gitberthe/BertheVario/BertheVario213/Documentation/00-photo/T5-V2_17.jpg

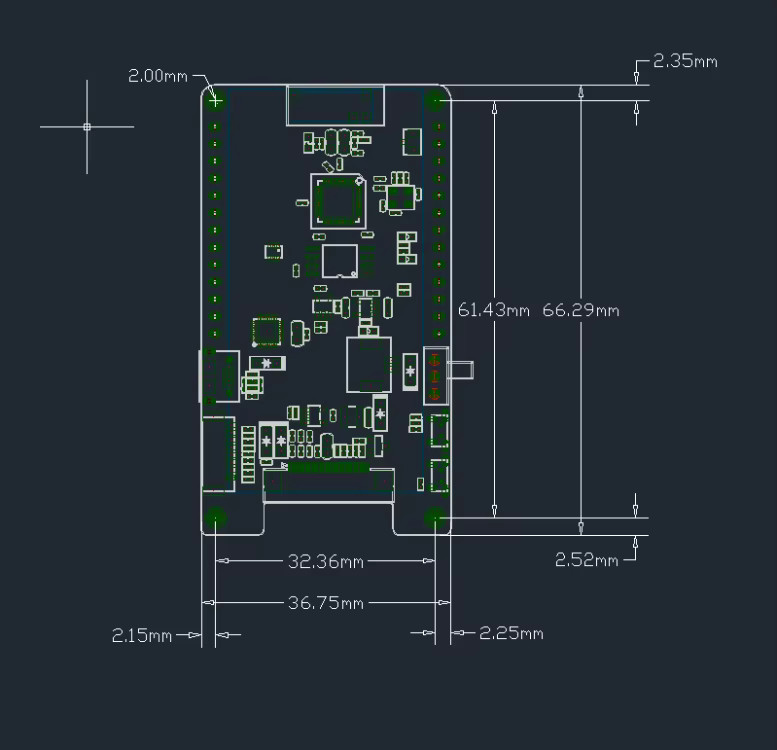
BertheVario213/Documentation/00-photo/T5-V2_17.jpg
