gitberthe/BertheVario/BertheVario213/Photos/03-cablage.jpg

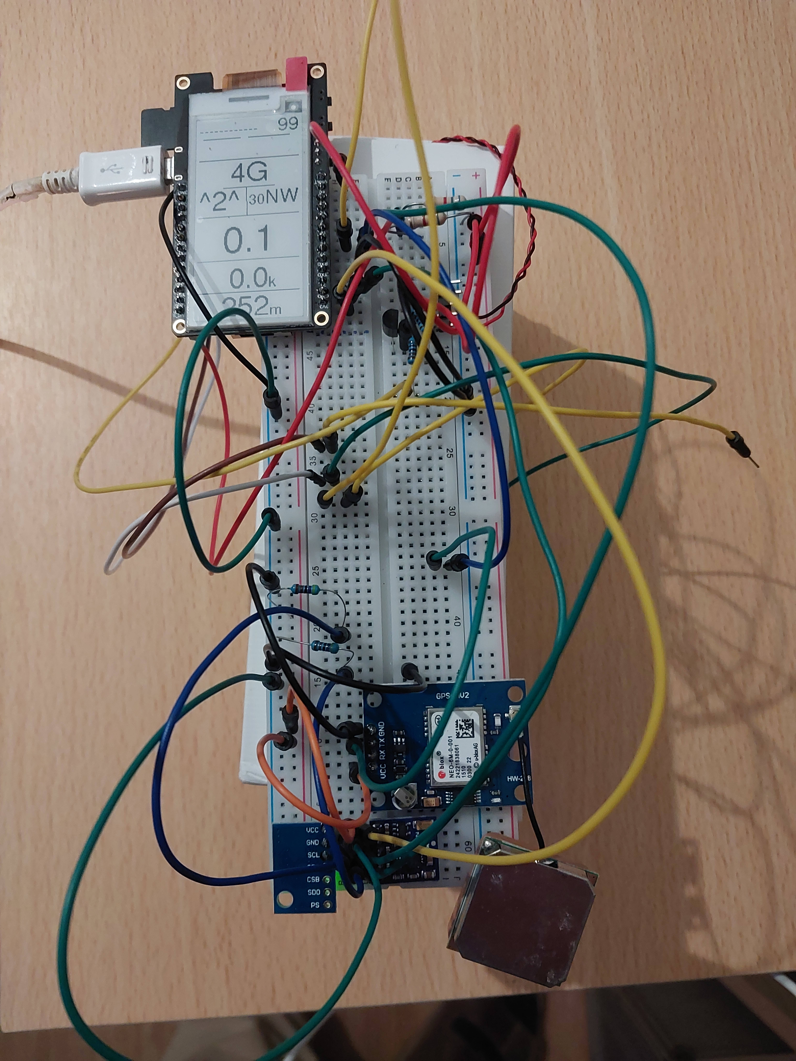
BertheVario213/Photos/03-cablage.jpg
