gitberthe/BertheVario/BertheVario213/Photos/07-bv213-sans-boitier-1.jpg

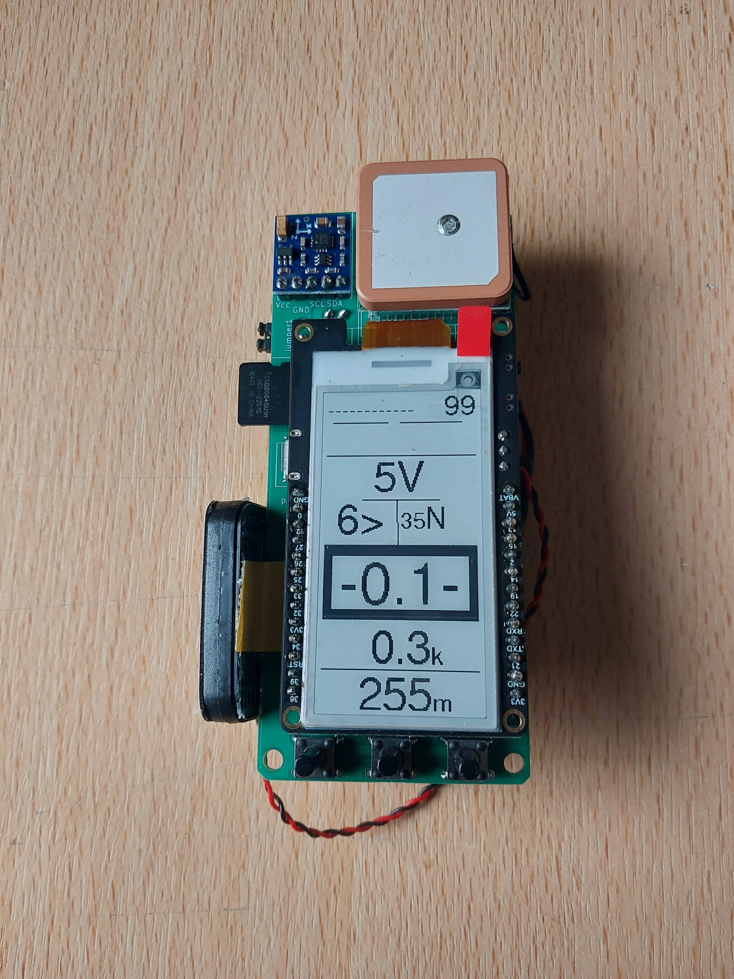
BertheVario213/Photos/07-bv213-sans-boitier-1.jpg
