gitberthe/BertheVario/BertheVario213/Photos/08-bv213-sans-boitier-2.jpg

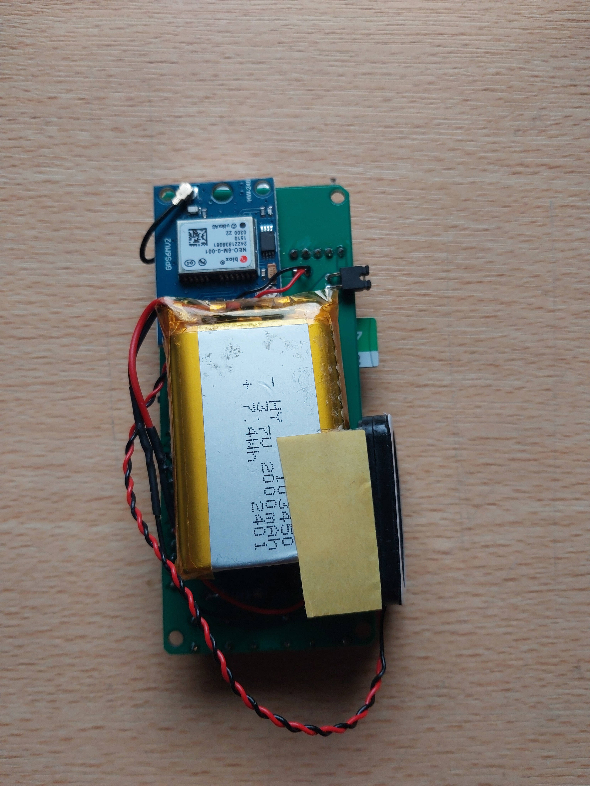
BertheVario213/Photos/08-bv213-sans-boitier-2.jpg
