gitberthe/BertheVario/CompZoneAerienne/zones_gnuplot/000_png_PROTECT_Reserve_naturelle_nationale_de_Chastreix-Sancy_300m_sol_.png

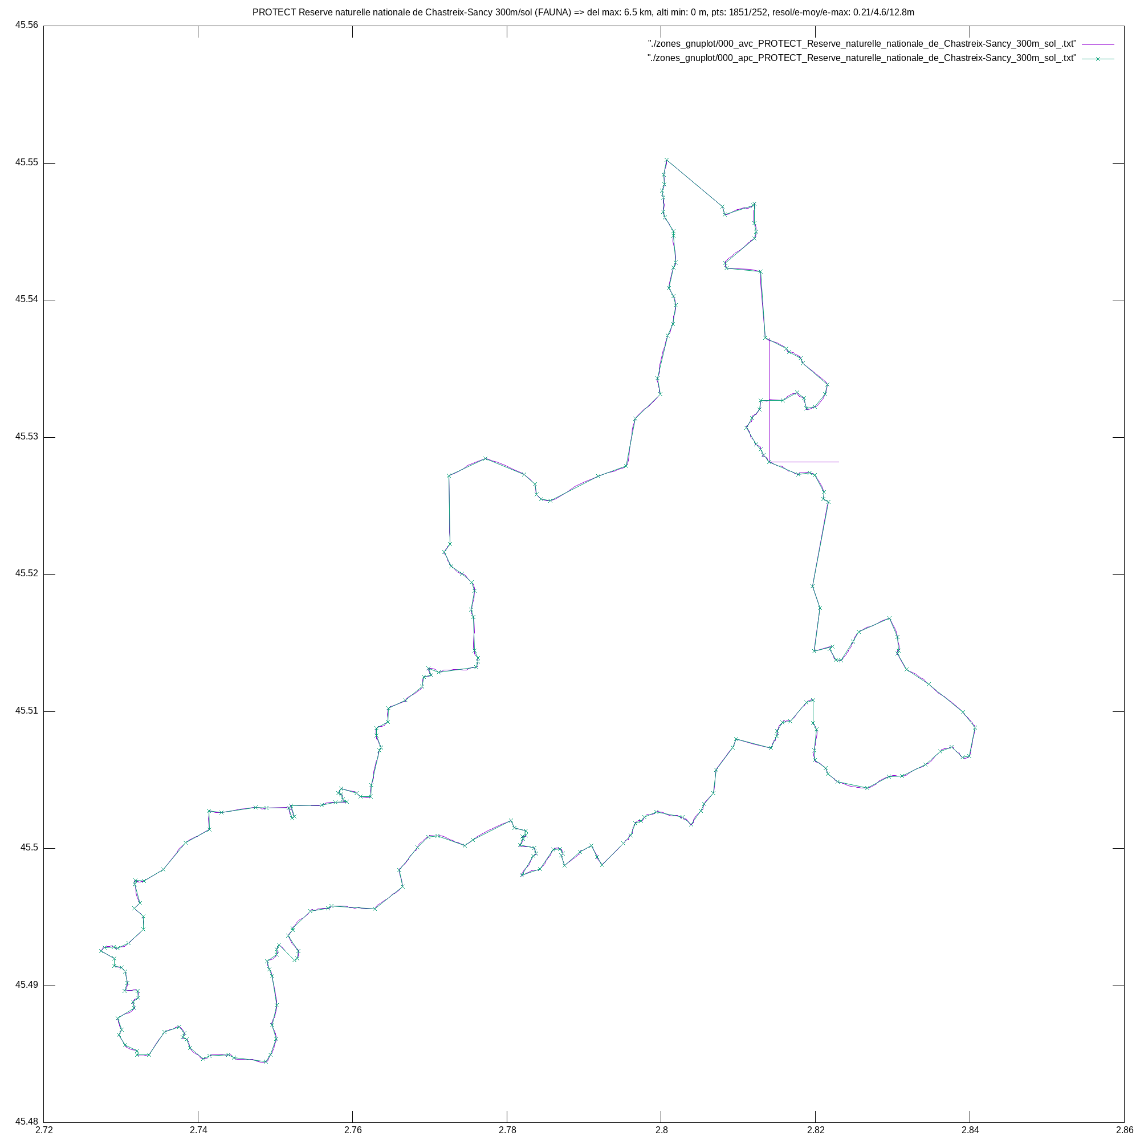
CompZoneAerienne/zones_gnuplot/000_png_PROTECT_Reserve_naturelle_nationale_de_Chastreix-Sancy_300m_sol_.png
