gitberthe/BertheVario/CompZoneAerienne/zones_gnuplot/001_png_PROTECT_Reserve_naturelle_nationale_de_la_Vallee_de_Chaudefour.png

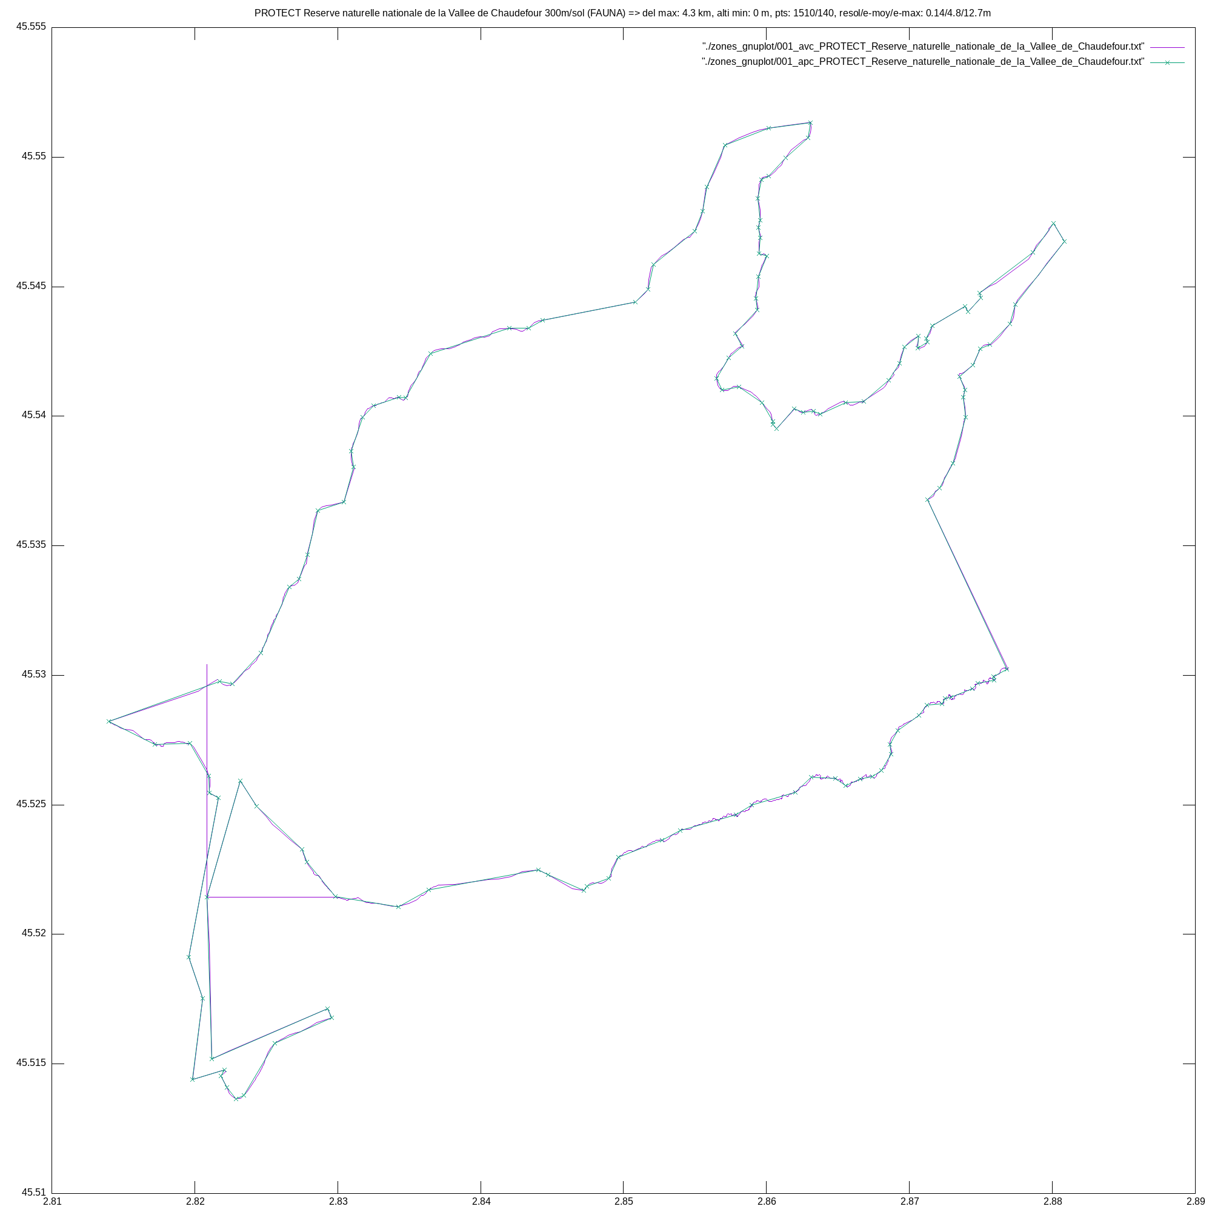
CompZoneAerienne/zones_gnuplot/001_png_PROTECT_Reserve_naturelle_nationale_de_la_Vallee_de_Chaudefour.png
