gitberthe/BertheVario/CompZoneAerienne/zones_gnuplot/002_png_CTR_CLERMONT_Twr_118.625__Upper_2700FT_AMSL-1000FT_AGL.png

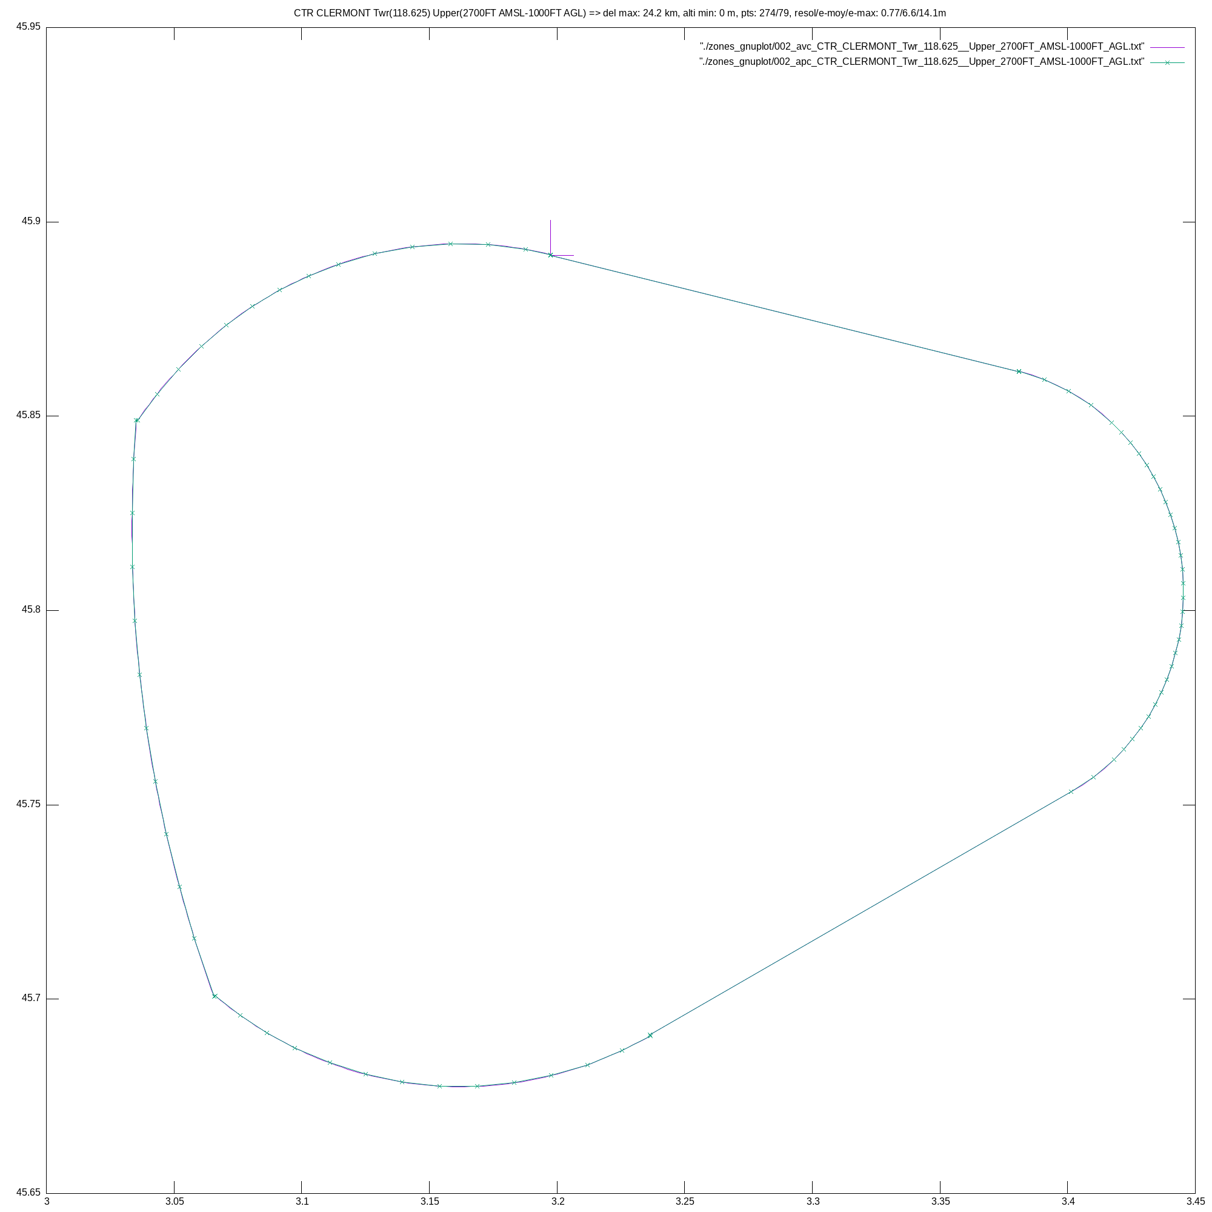
CompZoneAerienne/zones_gnuplot/002_png_CTR_CLERMONT_Twr_118.625__Upper_2700FT_AMSL-1000FT_AGL.png
