gitberthe/BertheVario/CompZoneAerienne/zones_gnuplot/003_png_PROTECT_Rocher_de_la_Jacquette__300m_sol_.png

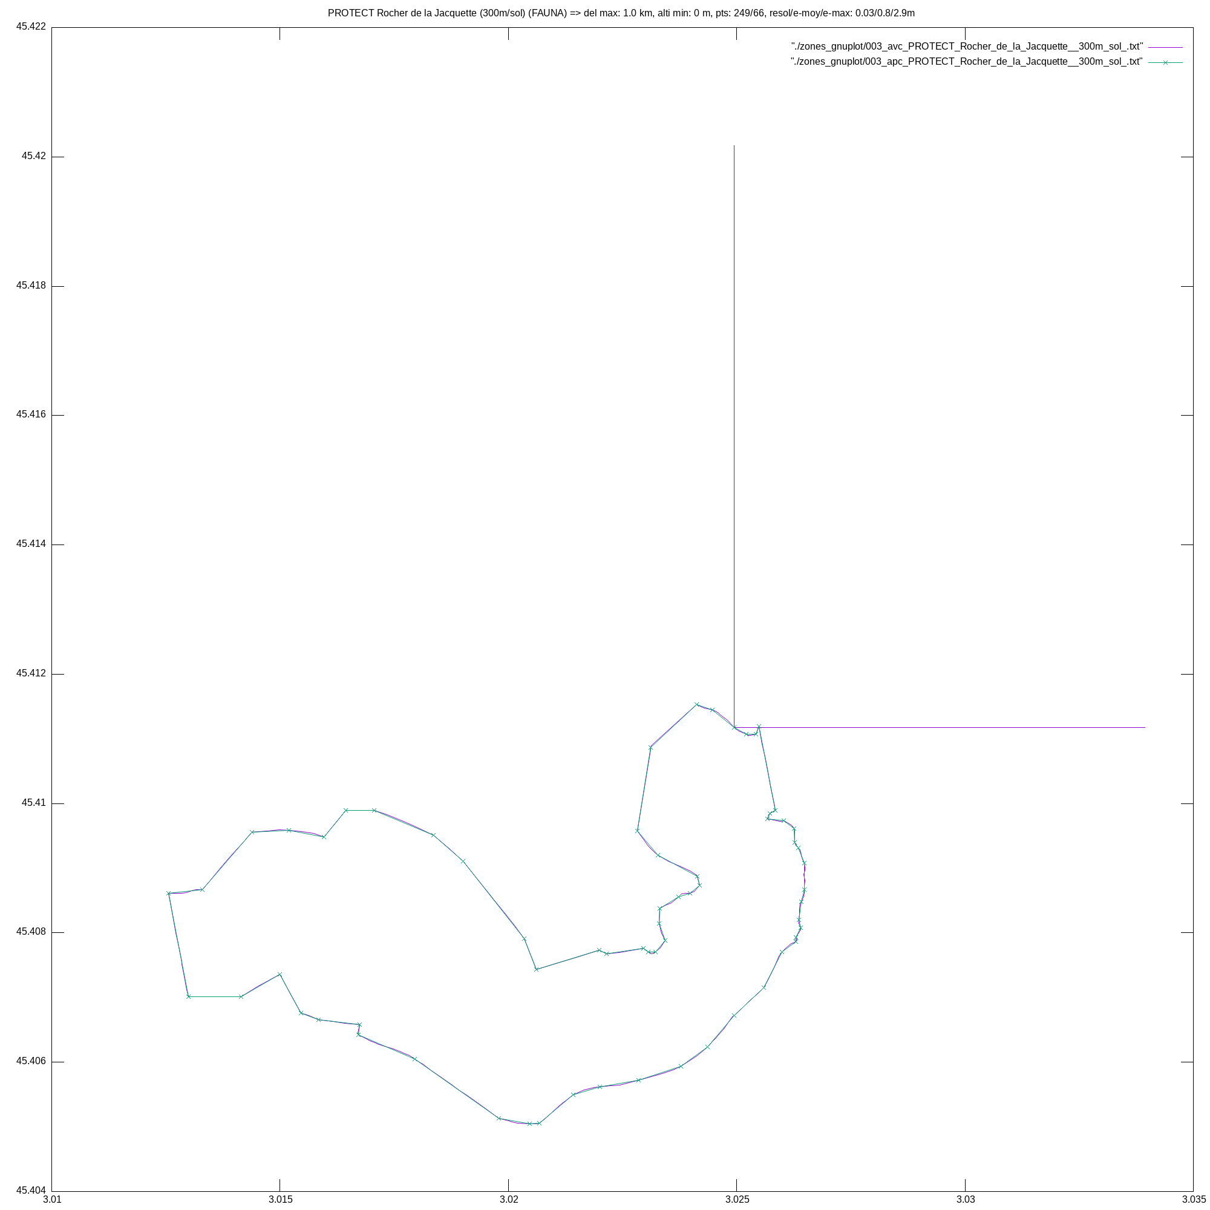
CompZoneAerienne/zones_gnuplot/003_png_PROTECT_Rocher_de_la_Jacquette__300m_sol_.png
