gitberthe/BertheVario/CompZoneAerienne/zones_gnuplot/004_png_TMA_CLERMONT_9_App_122.225__Lower_1000FT_AGL-4000FT.png

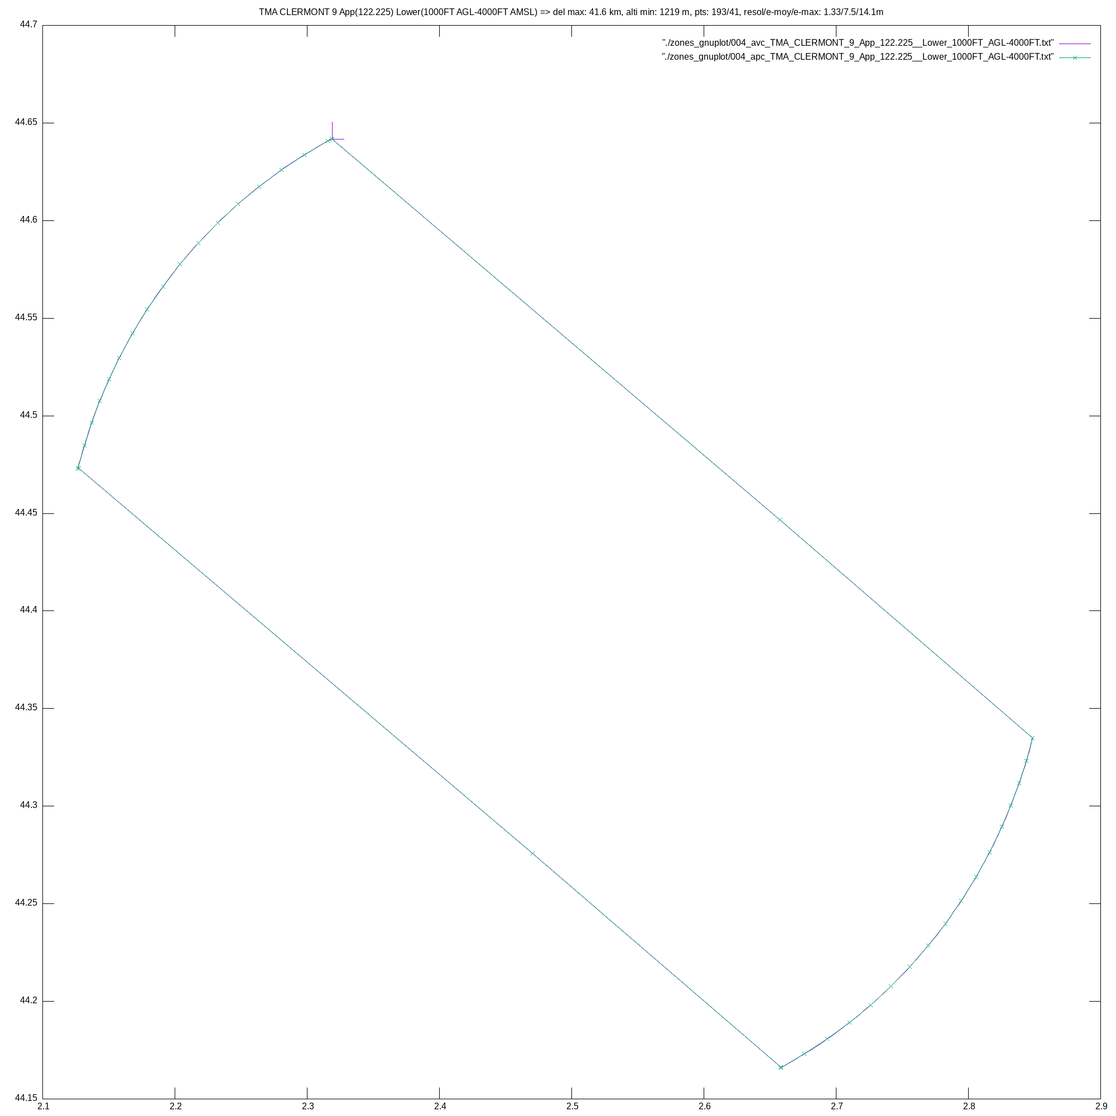
CompZoneAerienne/zones_gnuplot/004_png_TMA_CLERMONT_9_App_122.225__Lower_1000FT_AGL-4000FT.png
