gitberthe/BertheVario/CompZoneAerienne/zones_gnuplot/005_png_CTR_RODEZ_Twr_118.125___FFVL-Prot__.png

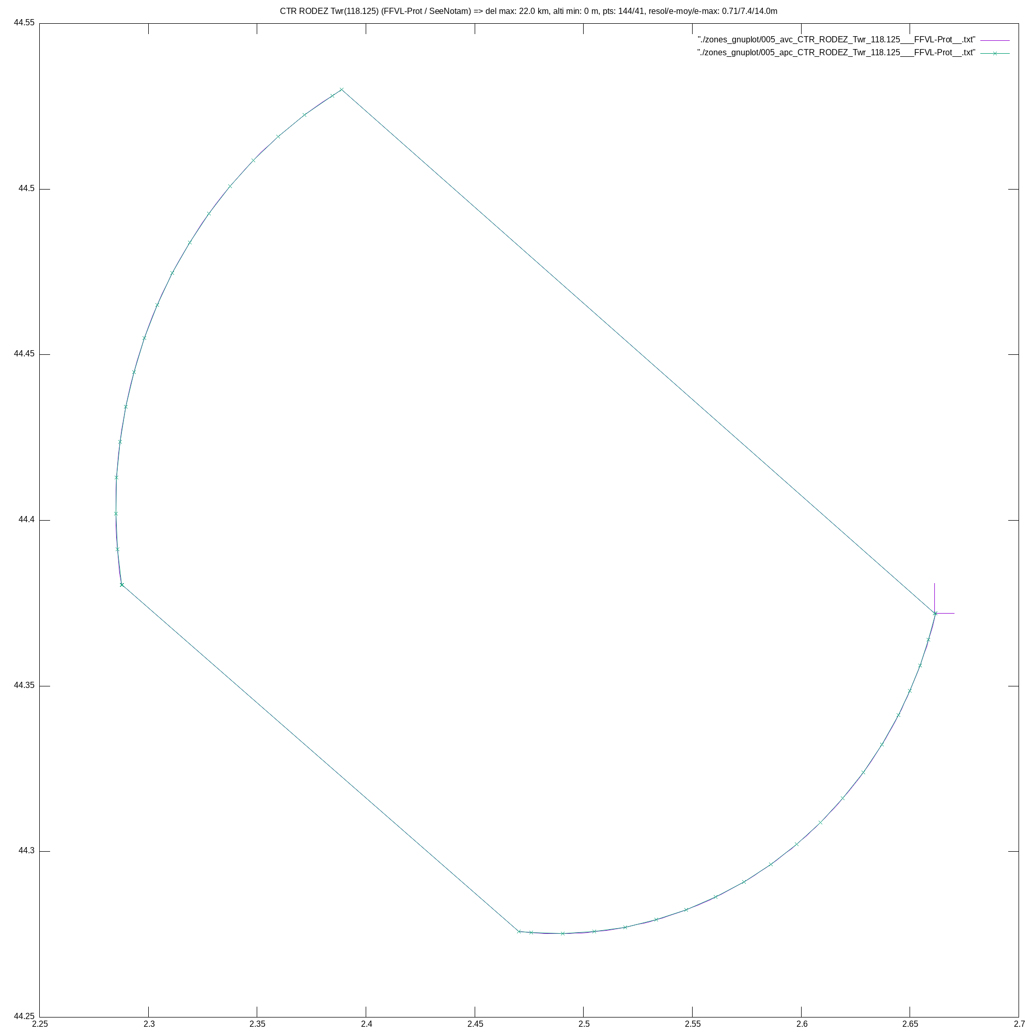
CompZoneAerienne/zones_gnuplot/005_png_CTR_RODEZ_Twr_118.125___FFVL-Prot__.png
