gitberthe/BertheVario/CompZoneAerienne/zones_gnuplot/006_png_TMA_CLERMONT_1_App_122.225__Lower_1000FT_AGL-2700FT.png

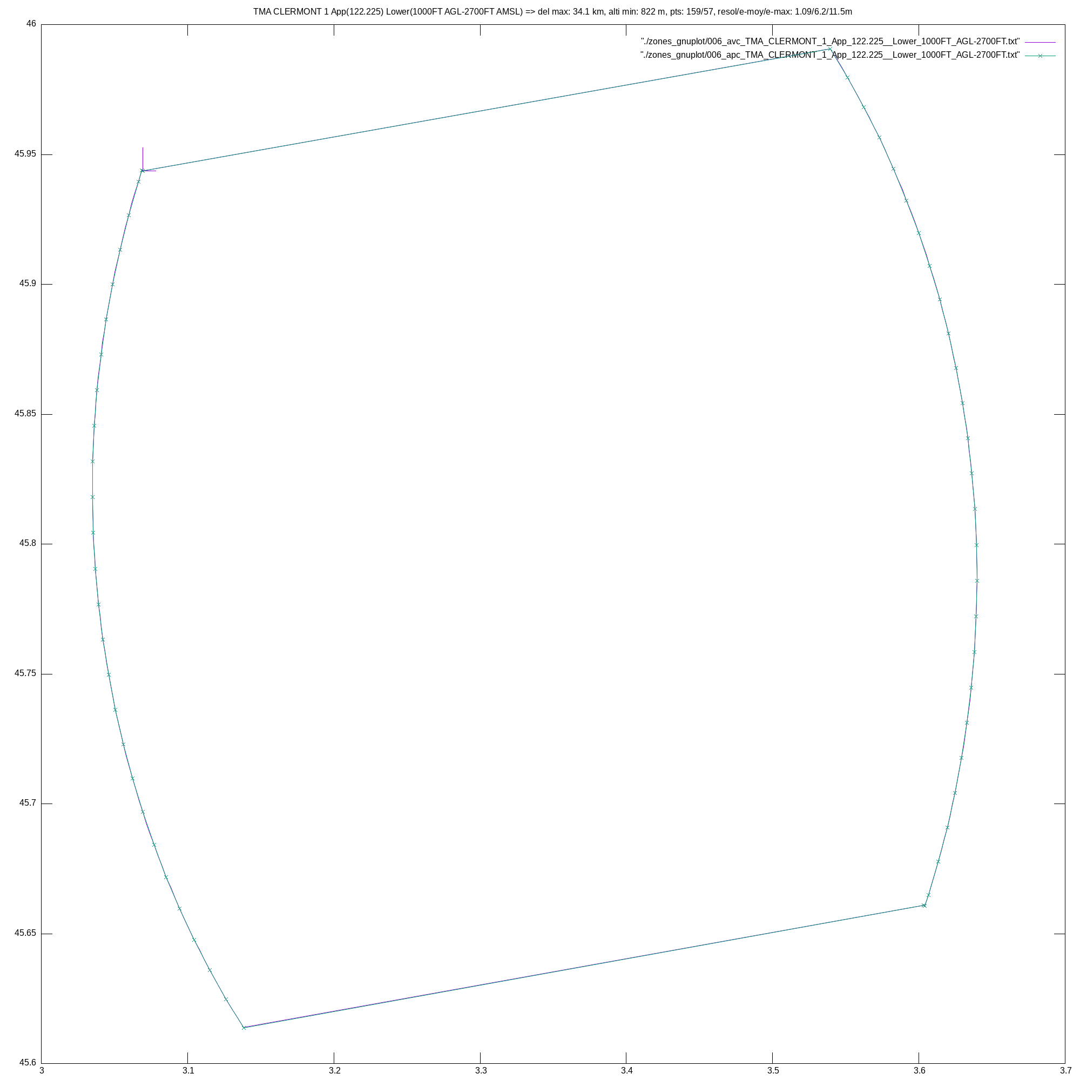
CompZoneAerienne/zones_gnuplot/006_png_TMA_CLERMONT_1_App_122.225__Lower_1000FT_AGL-2700FT.png
