gitberthe/BertheVario/CompZoneAerienne/zones_gnuplot/007_png_CTR_SAINT_ETIENNE_2_Twr_119.250_.png

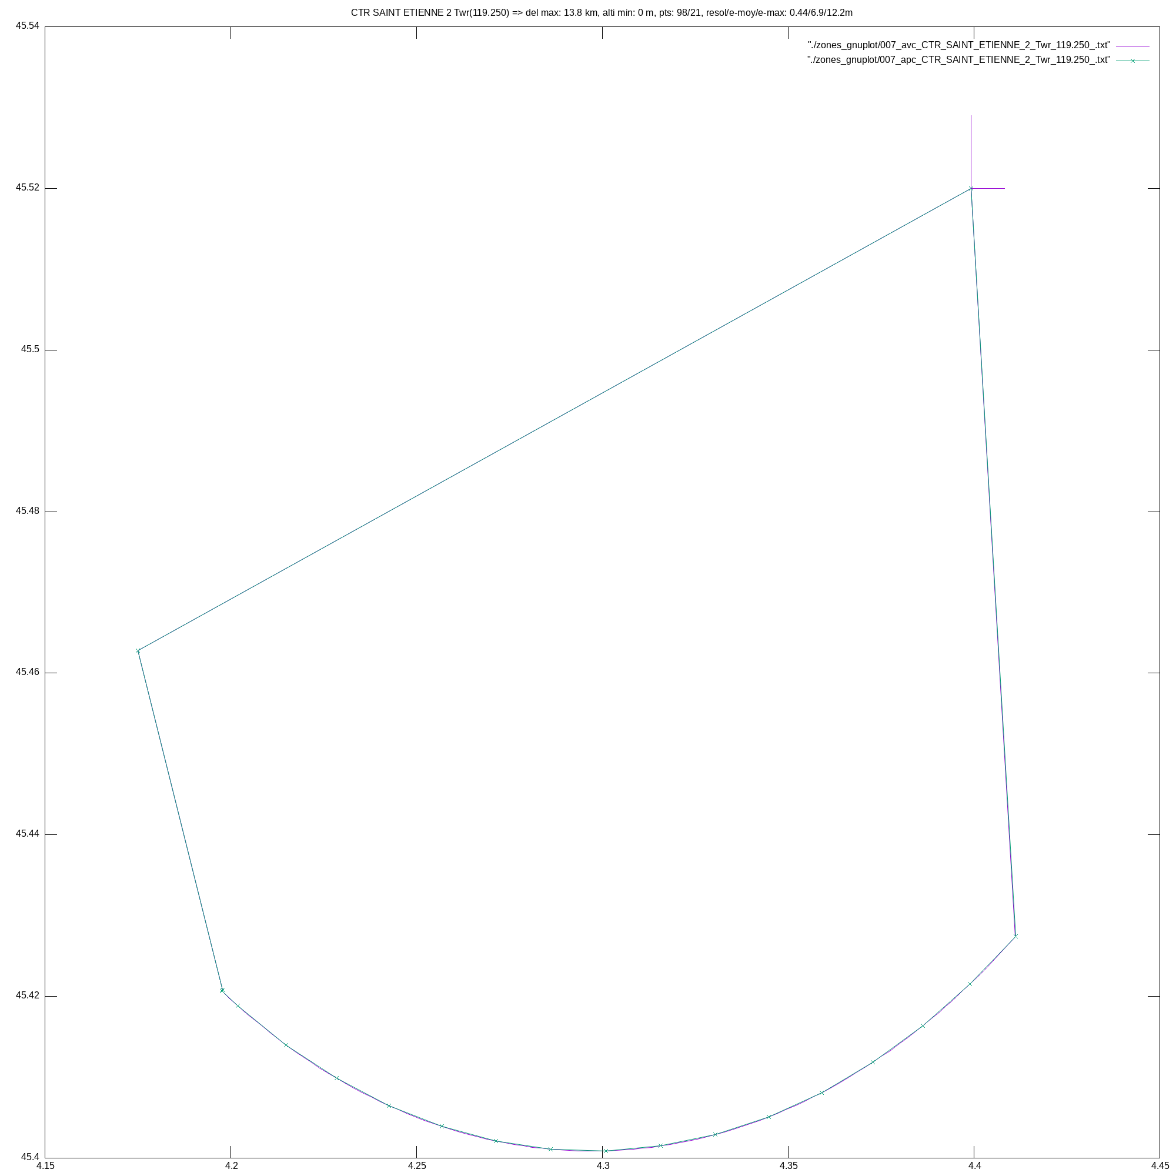
CompZoneAerienne/zones_gnuplot/007_png_CTR_SAINT_ETIENNE_2_Twr_119.250_.png
