gitberthe/BertheVario/CompZoneAerienne/zones_gnuplot/008_png_CTA_LIMOGES_Twr_127.675_.png

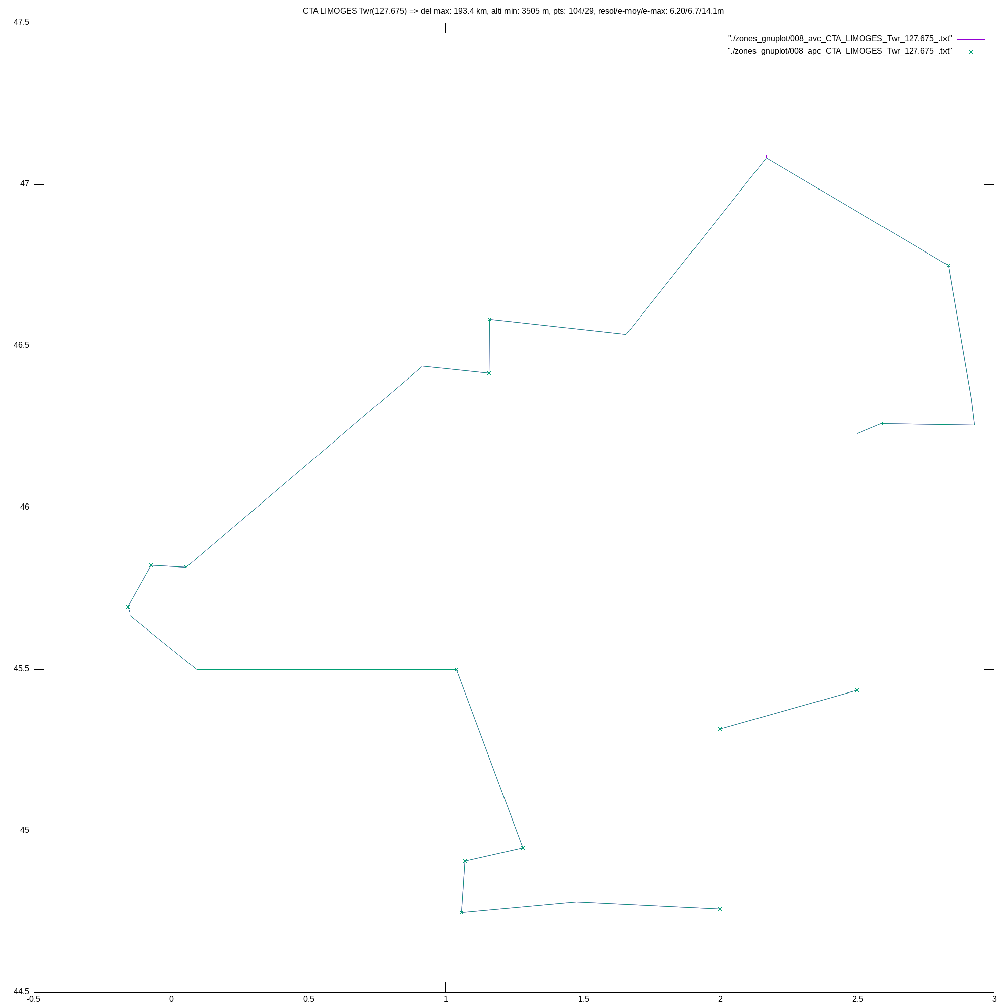
CompZoneAerienne/zones_gnuplot/008_png_CTA_LIMOGES_Twr_127.675_.png
