gitberthe/BertheVario/CompZoneAerienne/zones_gnuplot/009_png_TMA_CLERMONT_2.3_App_122.225_.png

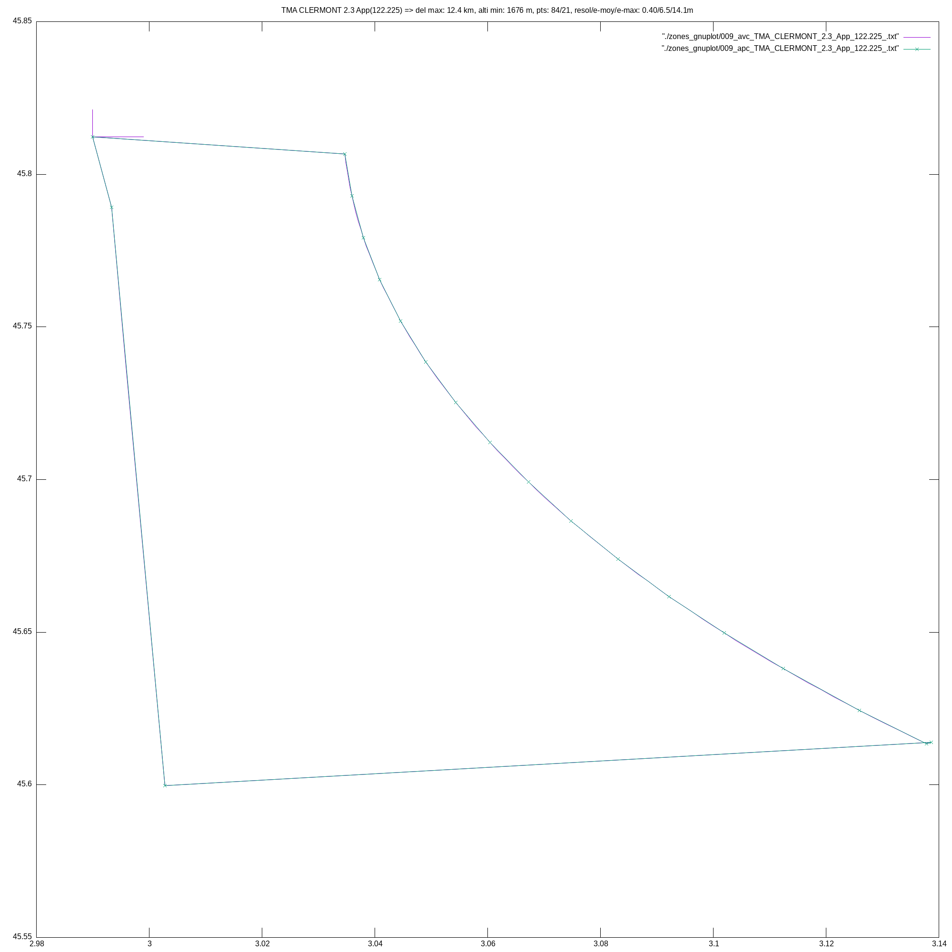
CompZoneAerienne/zones_gnuplot/009_png_TMA_CLERMONT_2.3_App_122.225_.png
