gitberthe/BertheVario/CompZoneAerienne/zones_gnuplot/011_png_RTBA_139_B__MILOPS___SeeNotam_.png

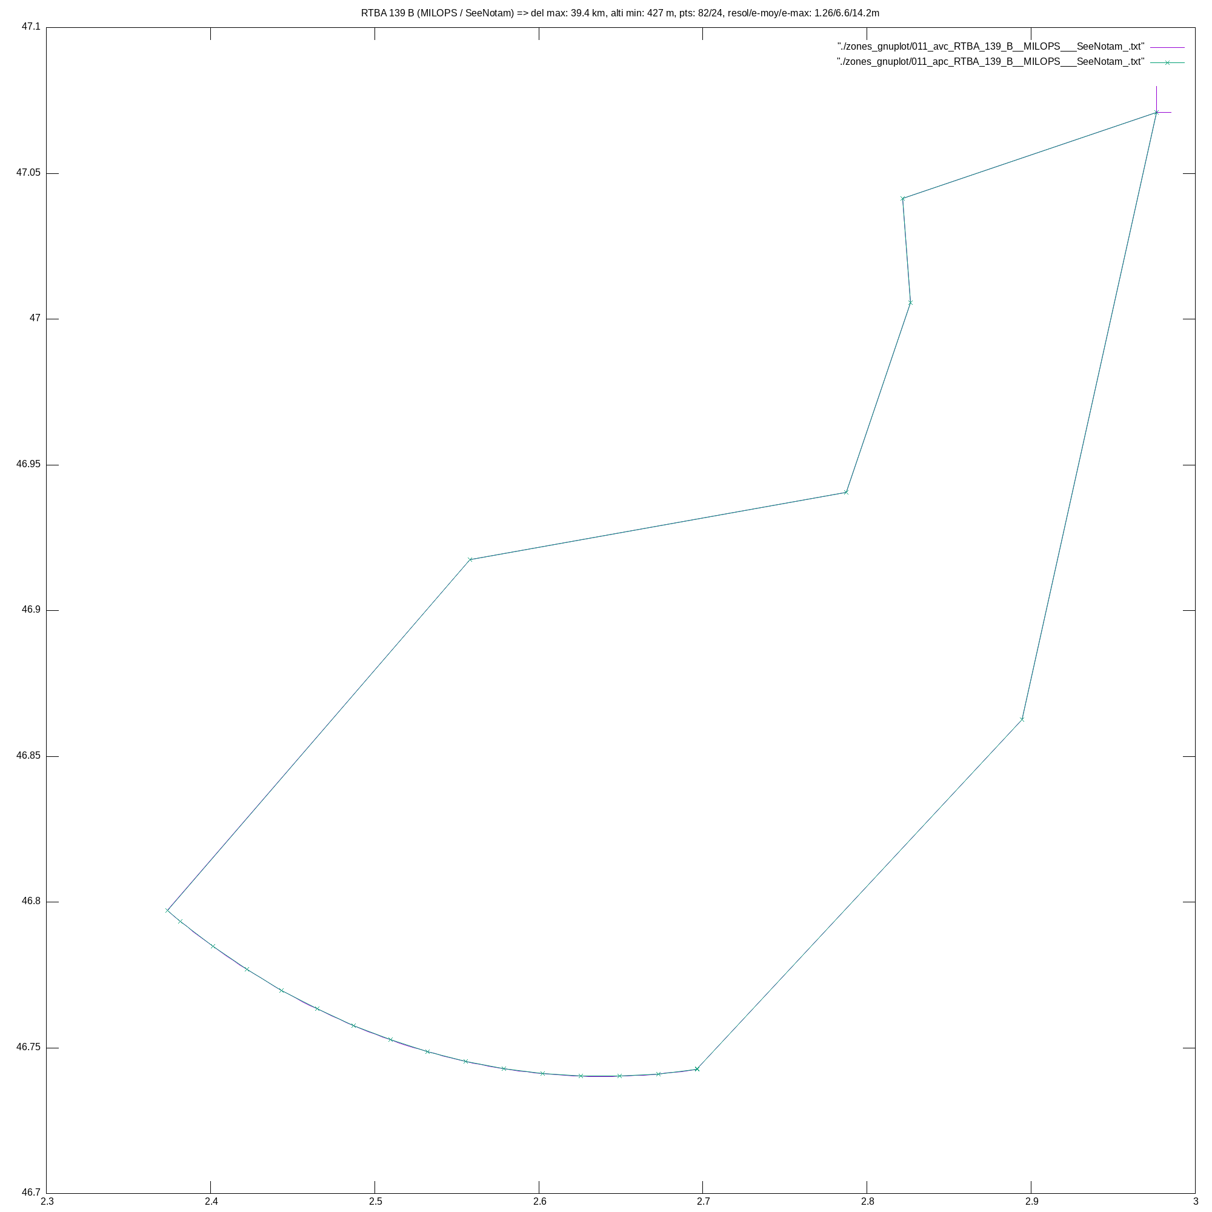
CompZoneAerienne/zones_gnuplot/011_png_RTBA_139_B__MILOPS___SeeNotam_.png
