gitberthe/BertheVario/CompZoneAerienne/zones_gnuplot/012_png_RTBA_139_A__MILOPS___SeeNotam_.png

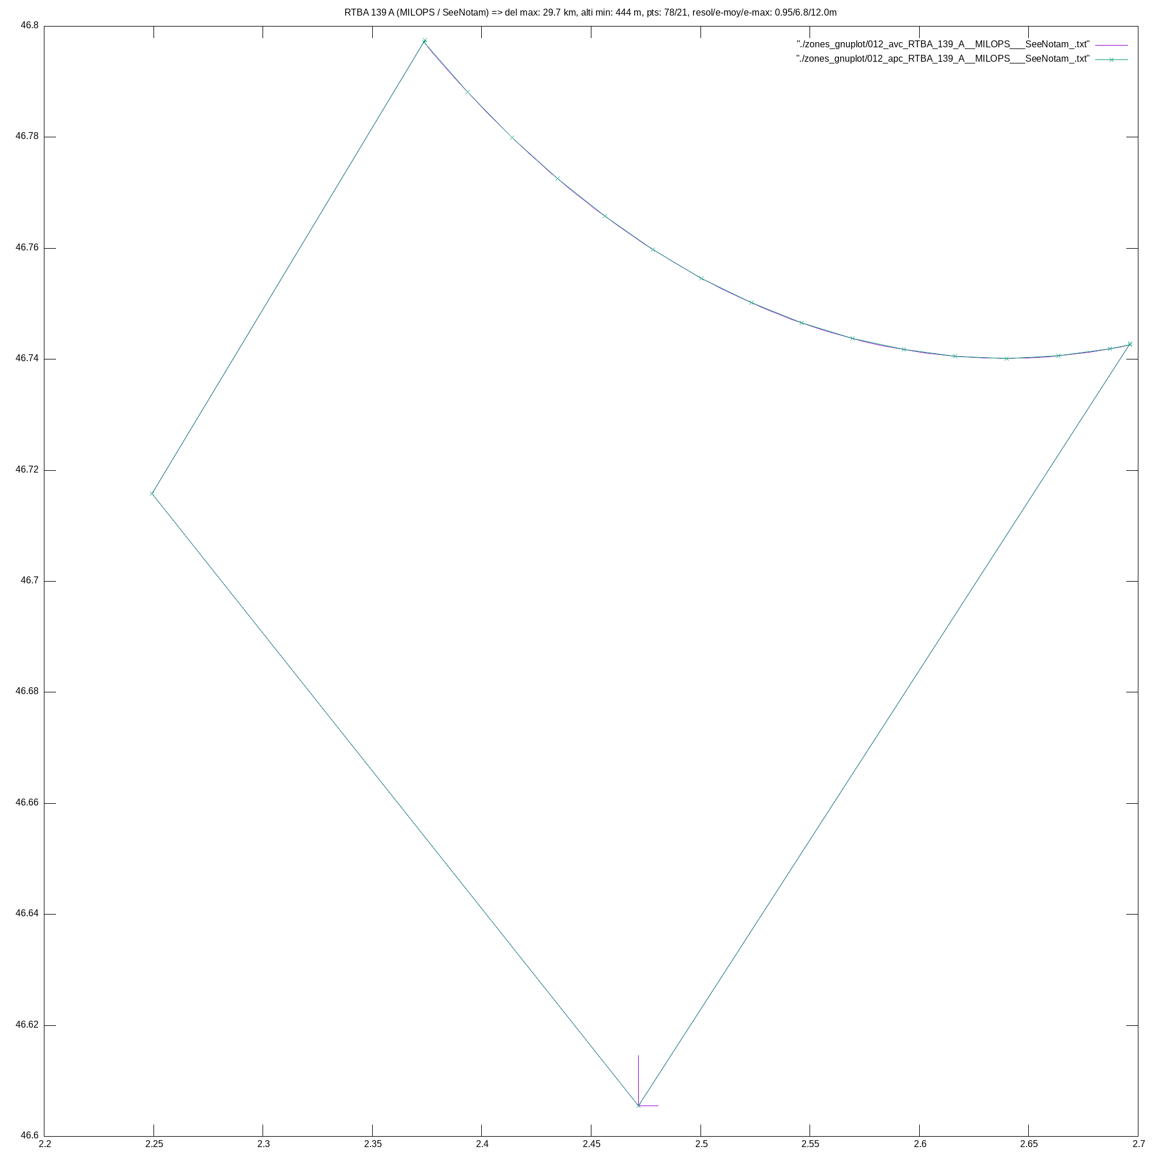
CompZoneAerienne/zones_gnuplot/012_png_RTBA_139_A__MILOPS___SeeNotam_.png
