gitberthe/BertheVario/CompZoneAerienne/zones_gnuplot/013_png_R_20_B3_E_App_119.7_.png

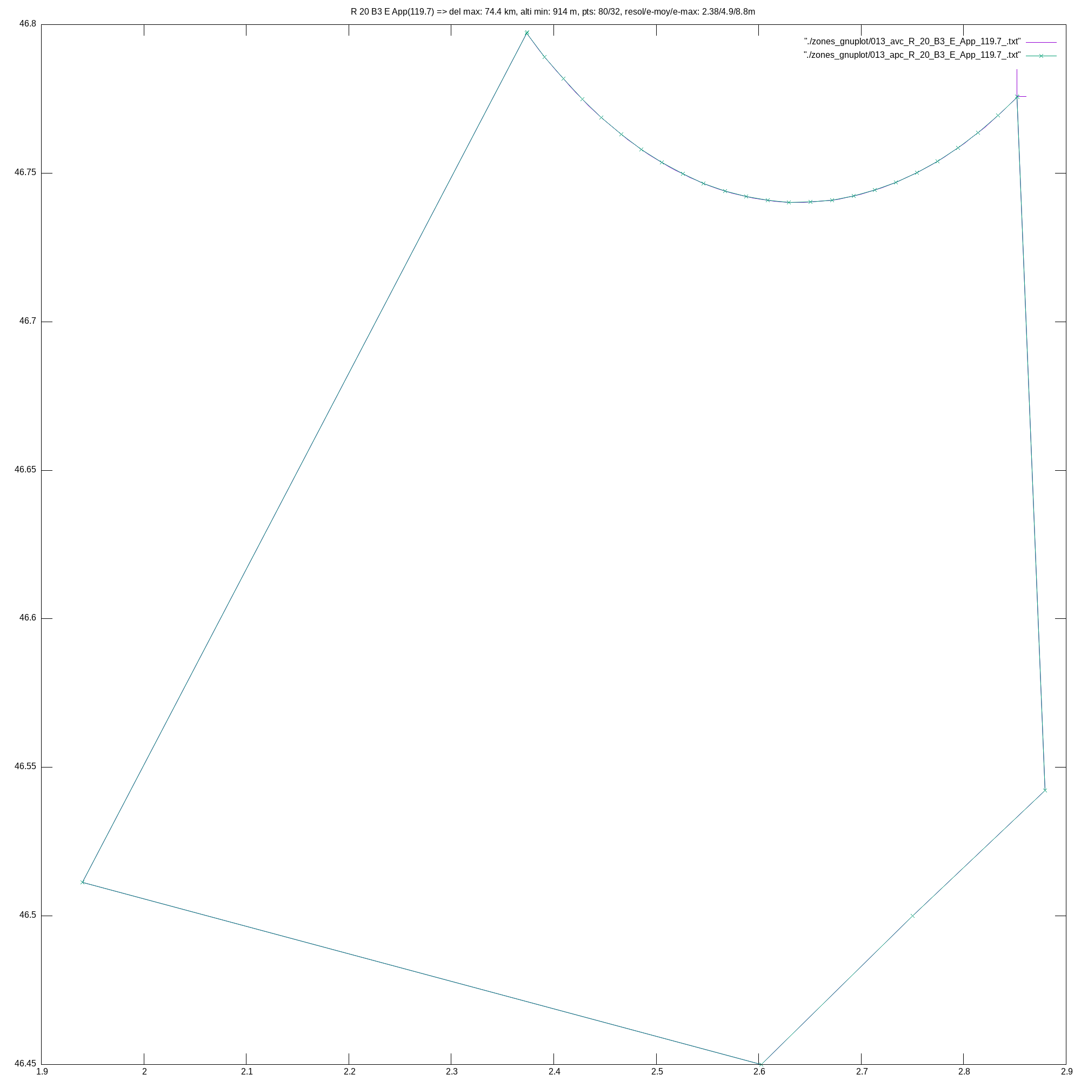
CompZoneAerienne/zones_gnuplot/013_png_R_20_B3_E_App_119.7_.png
