gitberthe/BertheVario/CompZoneAerienne/zones_gnuplot/014_png_PROTECT_Parc_Cevennes_Coeur__1000m_sol__.png

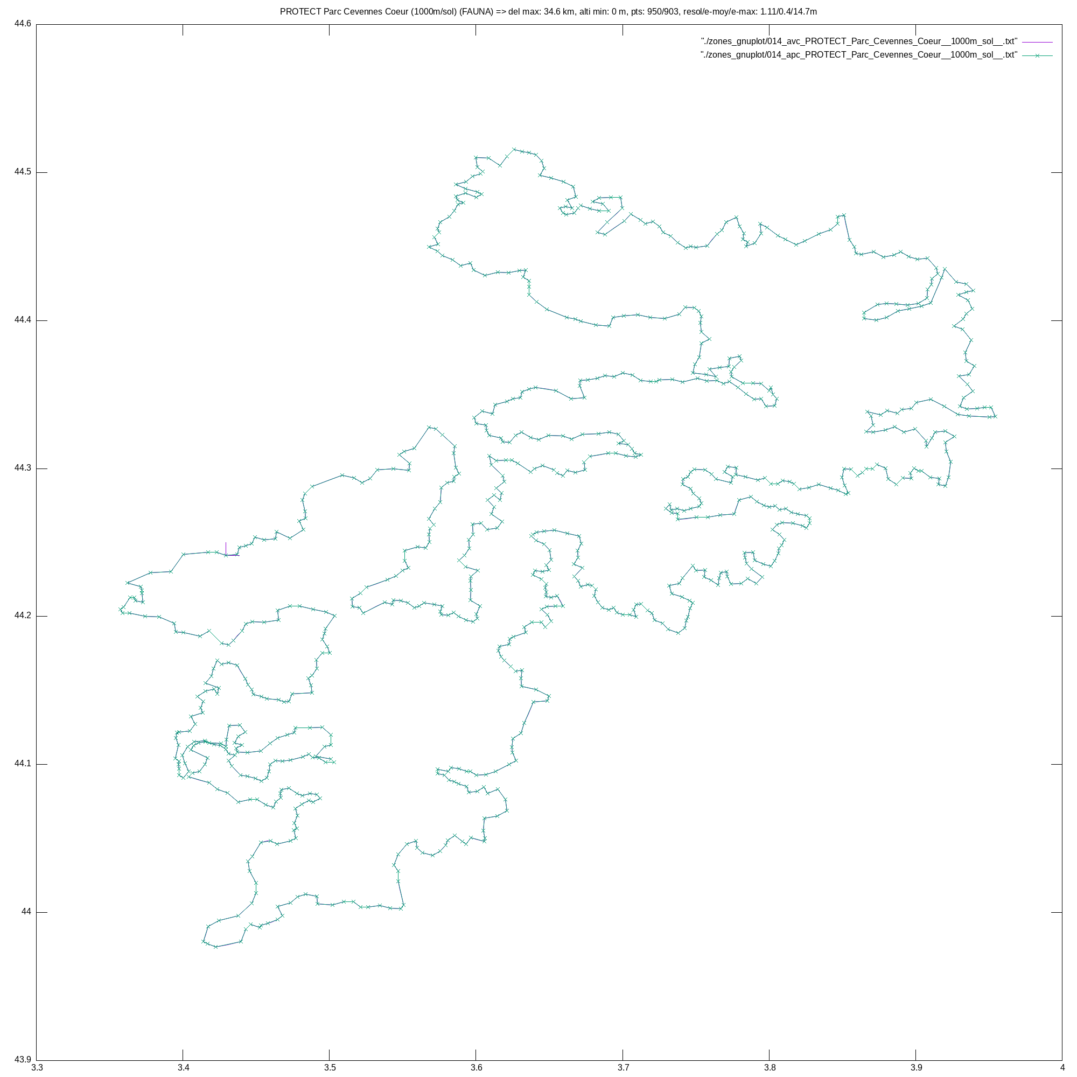
CompZoneAerienne/zones_gnuplot/014_png_PROTECT_Parc_Cevennes_Coeur__1000m_sol__.png
