gitberthe/BertheVario/CompZoneAerienne/zones_gnuplot/015_png_TMA_SAINT-YAN_1.2_App_123.405_.png

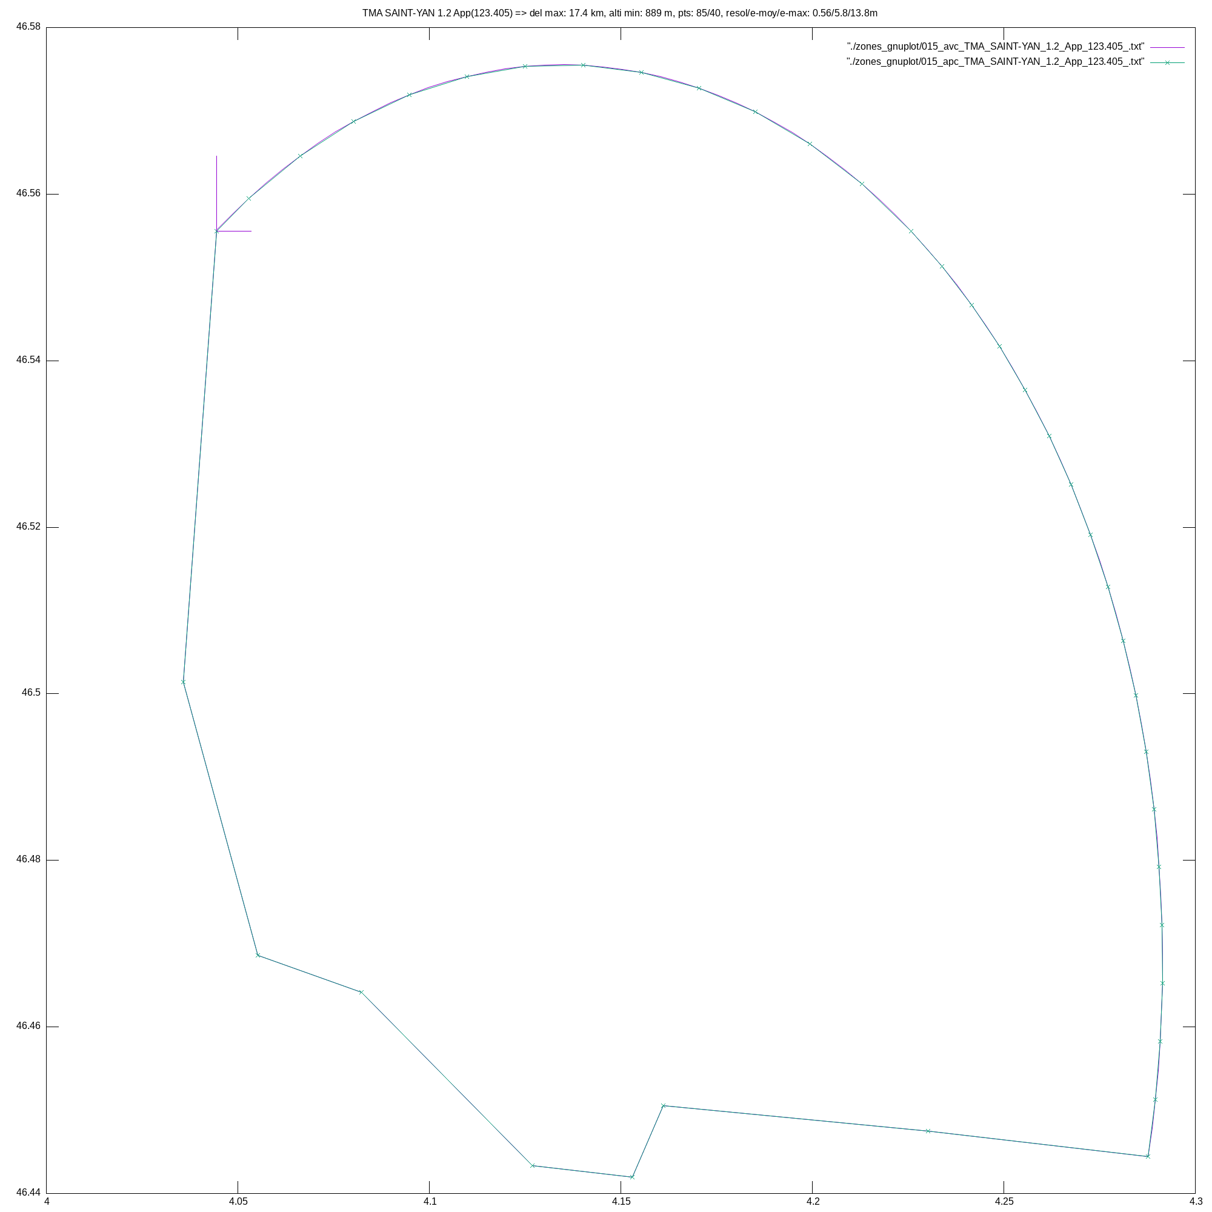
CompZoneAerienne/zones_gnuplot/015_png_TMA_SAINT-YAN_1.2_App_123.405_.png
