gitberthe/BertheVario/CompZoneAerienne/zones_gnuplot/016_png_CTR_SAINT_ETIENNE_1_Twr_119.250__Upper_3200FT.png

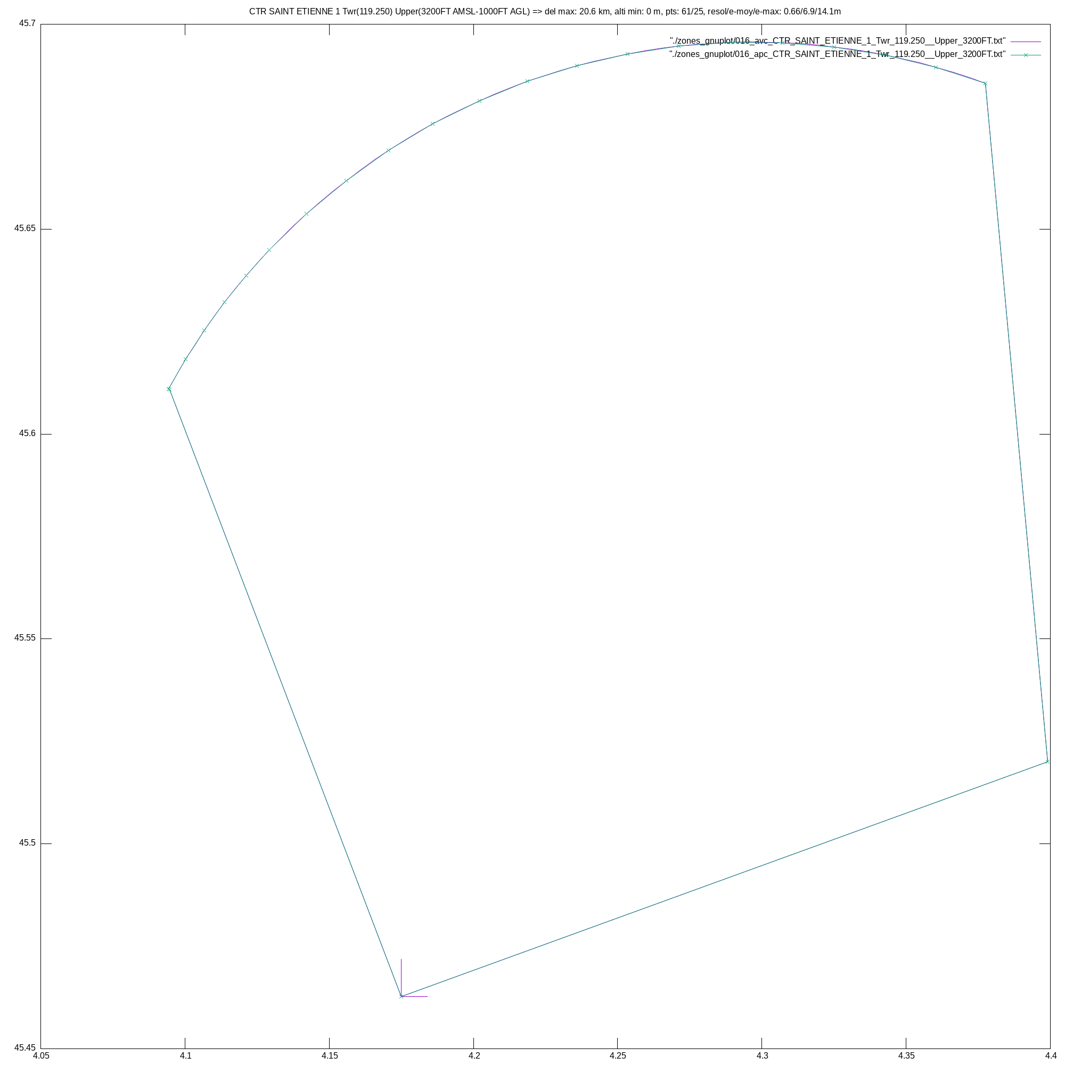
CompZoneAerienne/zones_gnuplot/016_png_CTR_SAINT_ETIENNE_1_Twr_119.250__Upper_3200FT.png
