gitberthe/BertheVario/CompZoneAerienne/zones_gnuplot/017_png_R_20_B3_W_App_119.7_.png

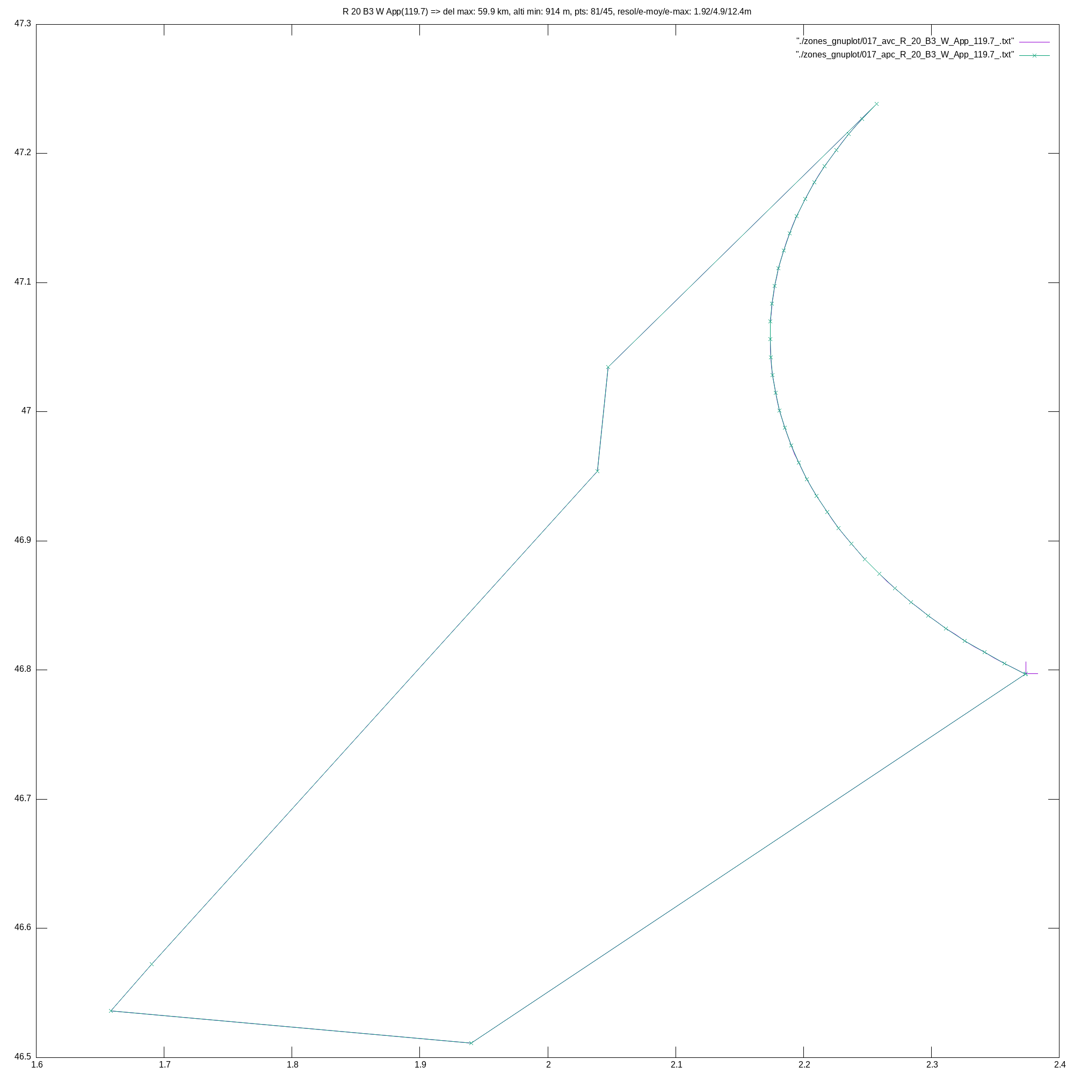
CompZoneAerienne/zones_gnuplot/017_png_R_20_B3_W_App_119.7_.png
