gitberthe/BertheVario/CompZoneAerienne/zones_gnuplot/018_png_R_368_E2.png

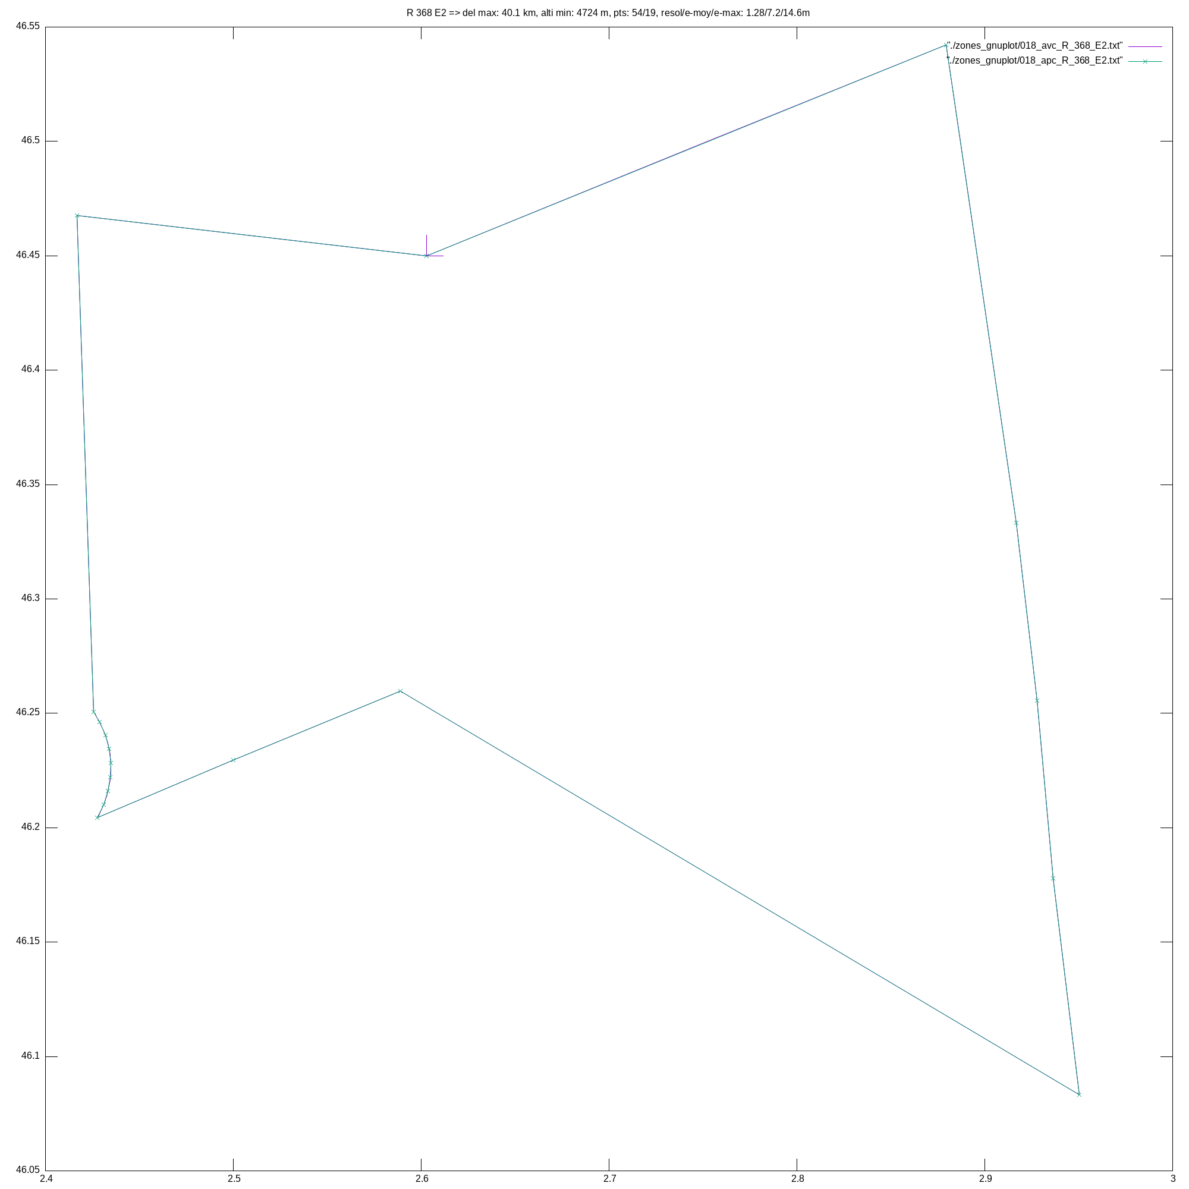
CompZoneAerienne/zones_gnuplot/018_png_R_368_E2.png
