gitberthe/BertheVario/CompZoneAerienne/zones_gnuplot/019_png_TMA_LYON_04_App_133.150_.png

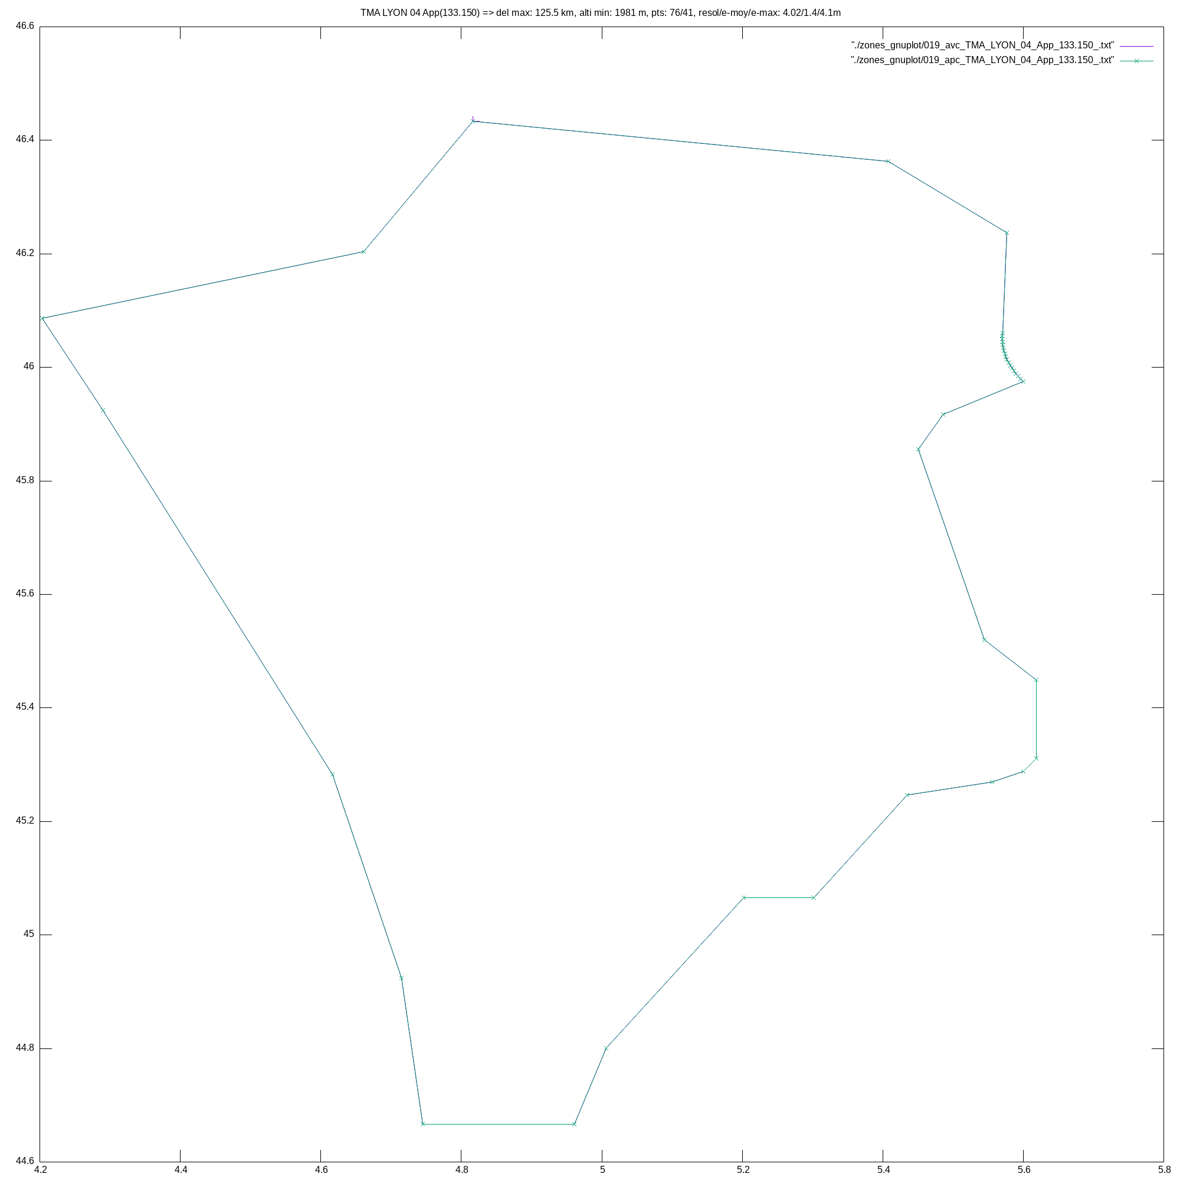
CompZoneAerienne/zones_gnuplot/019_png_TMA_LYON_04_App_133.150_.png
