gitberthe/BertheVario/CompZoneAerienne/zones_gnuplot/020_png_CTR_SAINT-YAN_2_Twr_122.300_.png

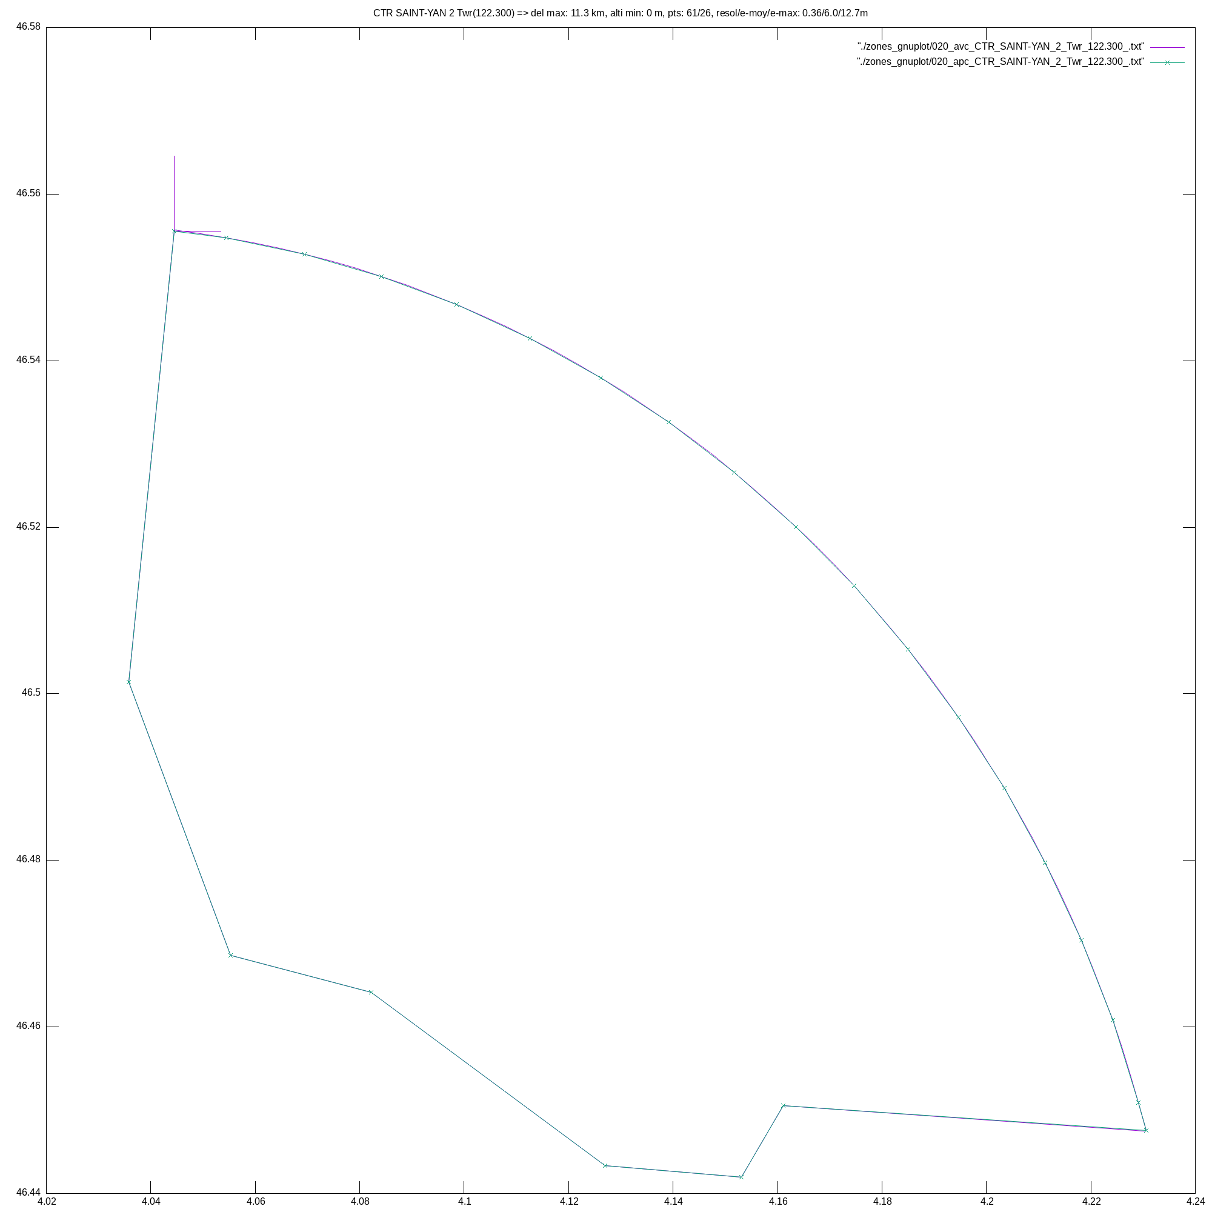
CompZoneAerienne/zones_gnuplot/020_png_CTR_SAINT-YAN_2_Twr_122.300_.png
