gitberthe/BertheVario/CompZoneAerienne/zones_gnuplot/022_png_TMA_SAINT-YAN_1.3_App_123.405_.png

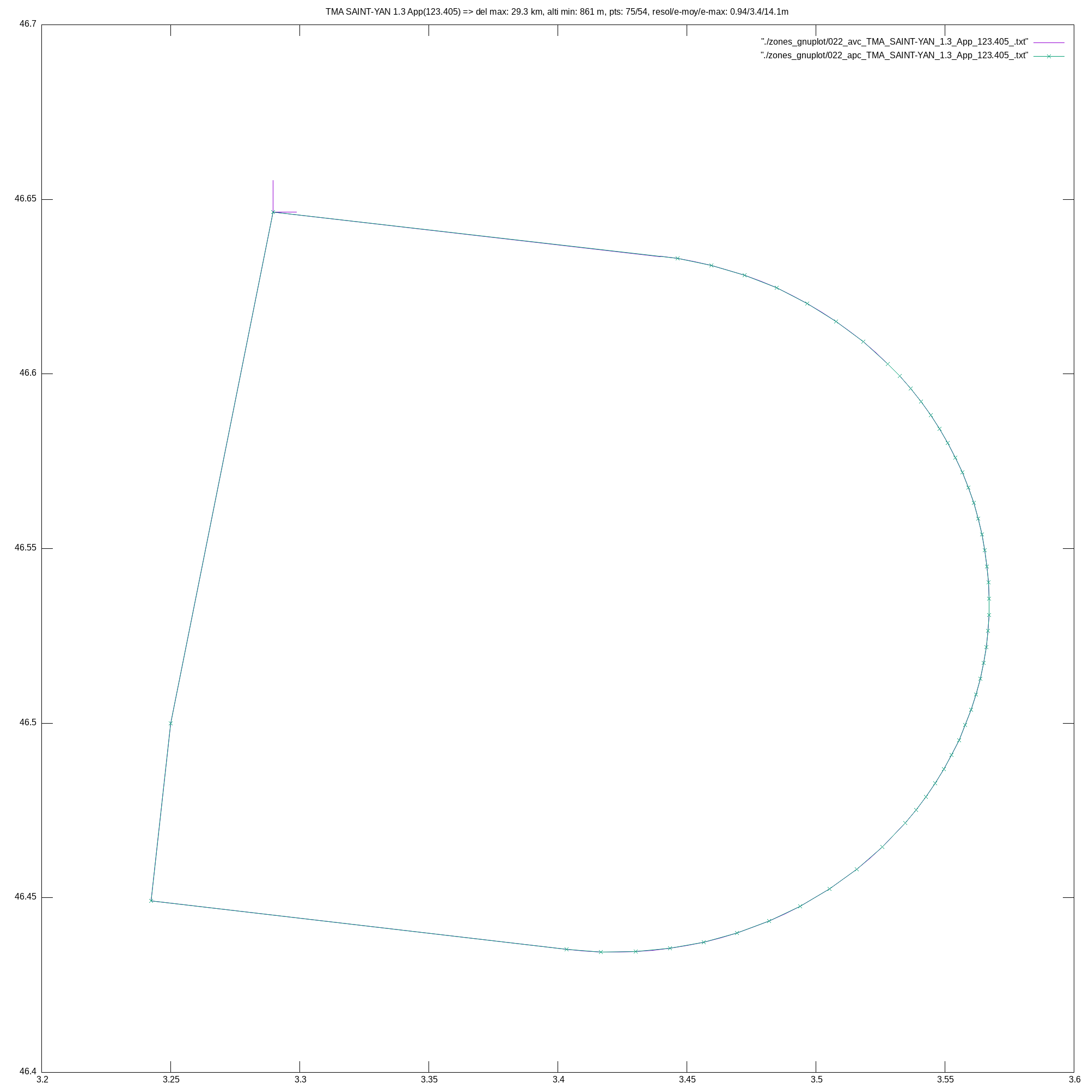
CompZoneAerienne/zones_gnuplot/022_png_TMA_SAINT-YAN_1.3_App_123.405_.png
