gitberthe/BertheVario/CompZoneAerienne/zones_gnuplot/023_png_R_167_B_App_119.2___SeeNotam_.png

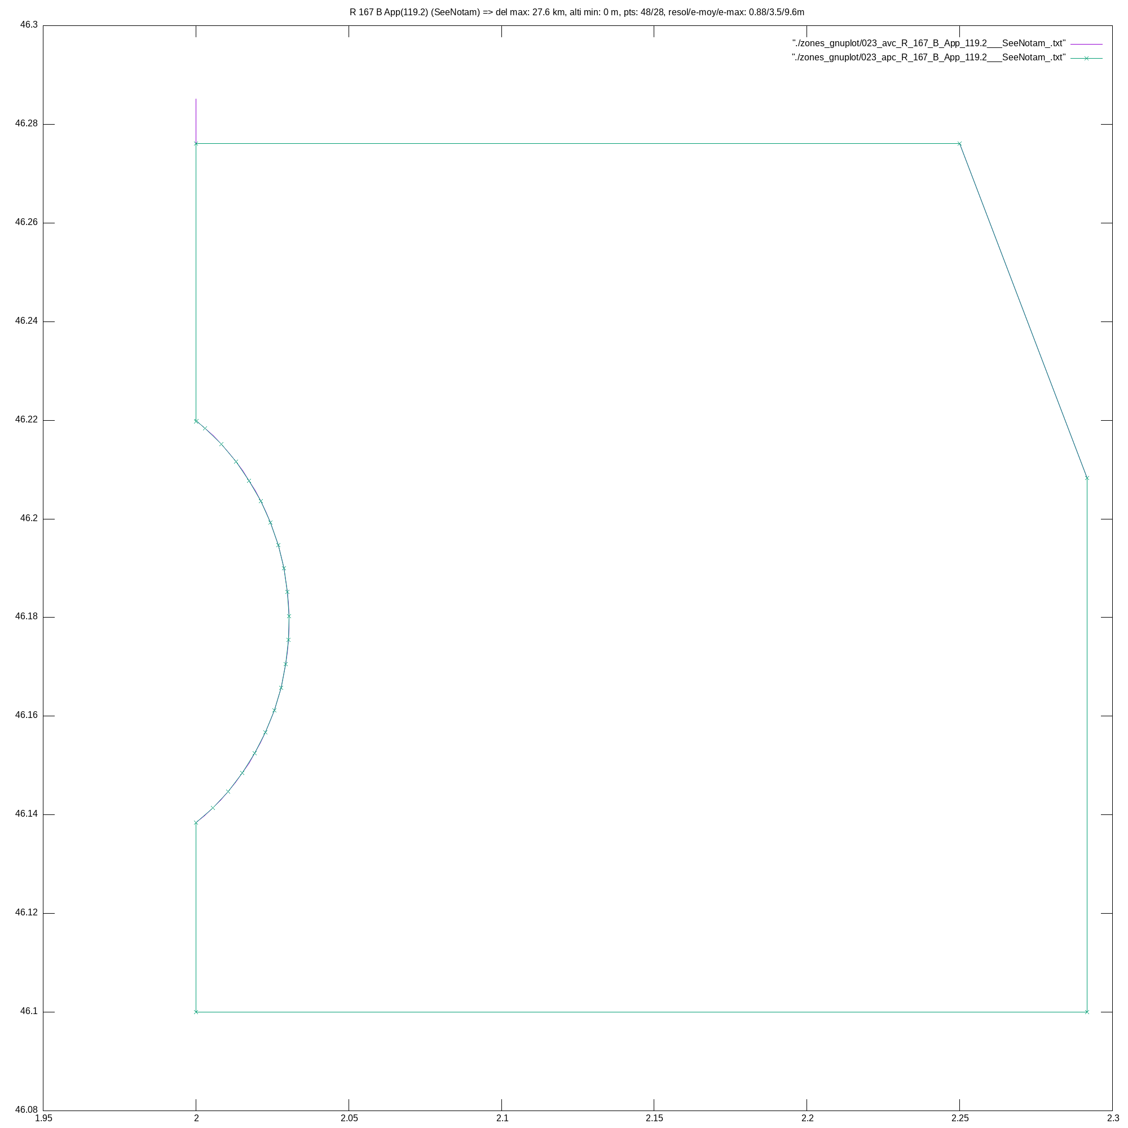
CompZoneAerienne/zones_gnuplot/023_png_R_167_B_App_119.2___SeeNotam_.png
