gitberthe/BertheVario/CompZoneAerienne/zones_gnuplot/024_png_R_20_B2_N_App_119.7_.png

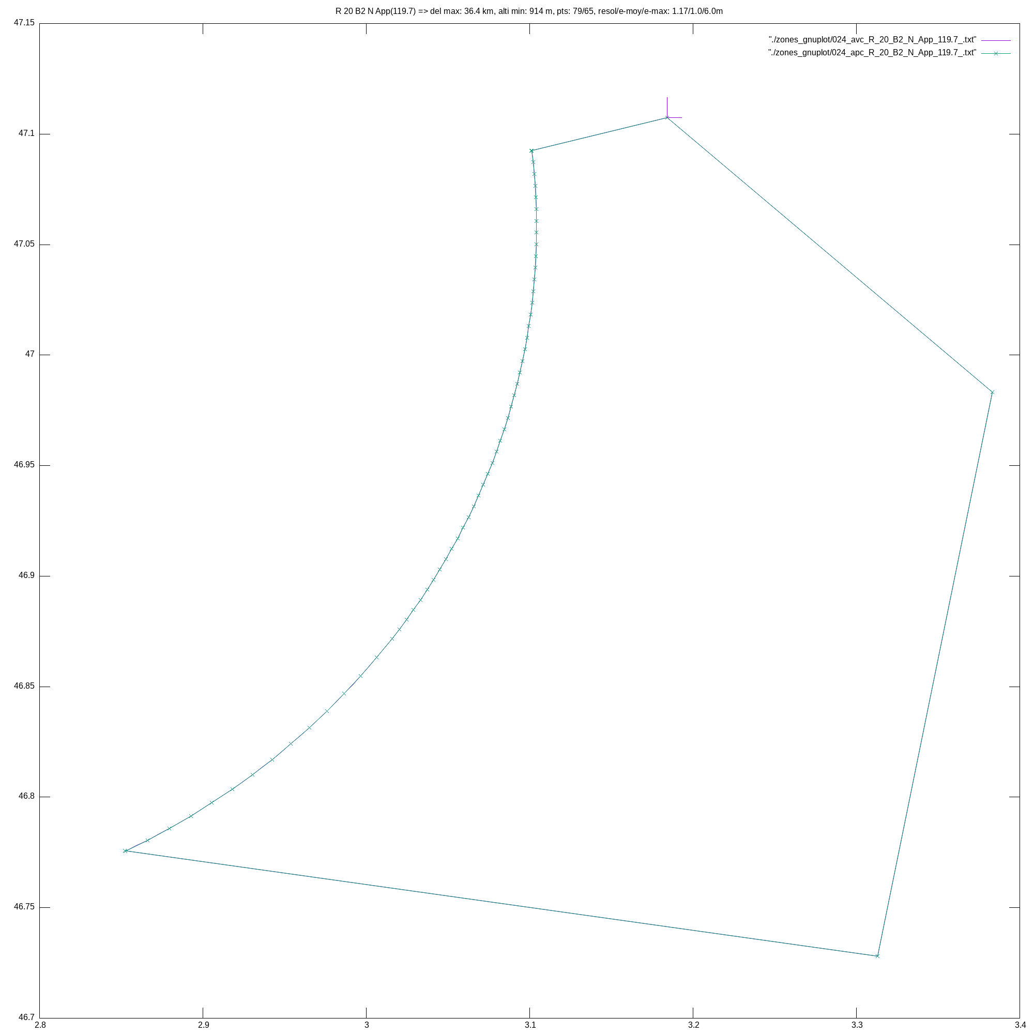
CompZoneAerienne/zones_gnuplot/024_png_R_20_B2_N_App_119.7_.png
