gitberthe/BertheVario/CompZoneAerienne/zones_gnuplot/026_png_PROTECT_4228_Gypaete_barbu_-_Zone_Tampon_300m_sol.png

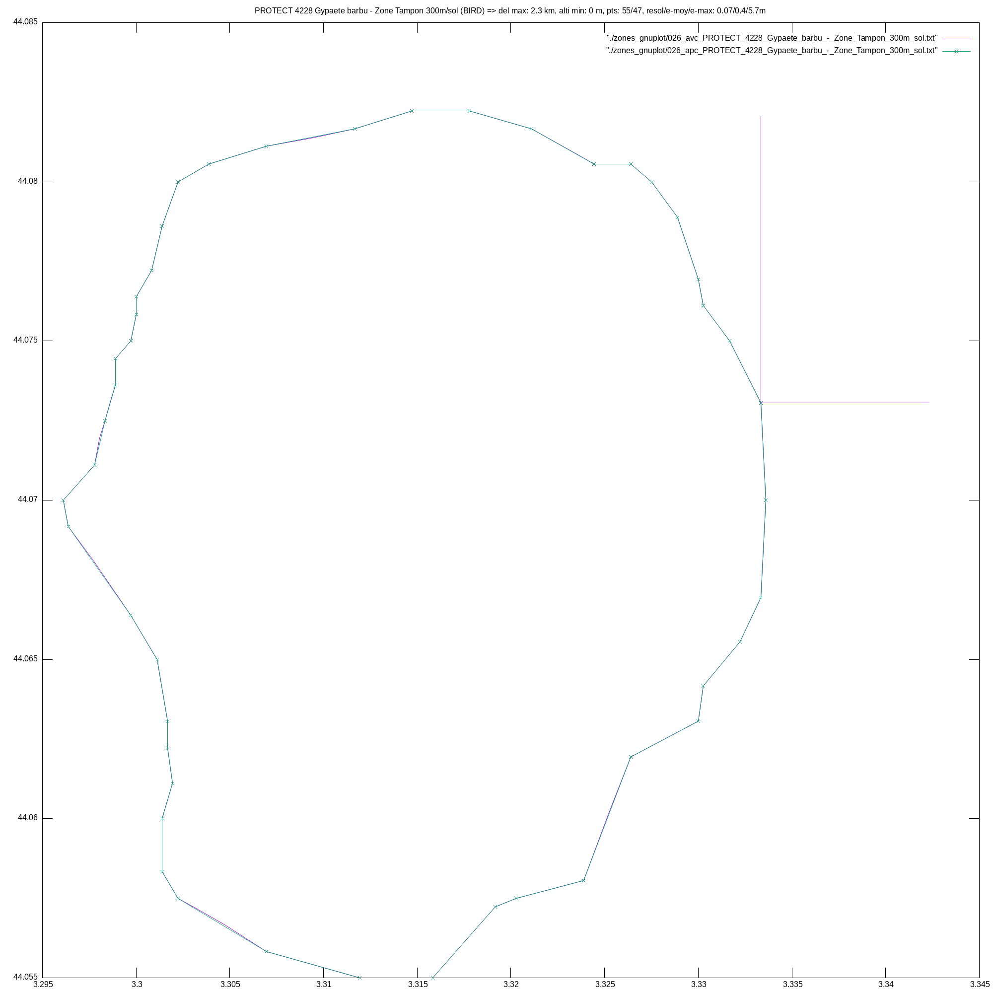
CompZoneAerienne/zones_gnuplot/026_png_PROTECT_4228_Gypaete_barbu_-_Zone_Tampon_300m_sol.png
