gitberthe/BertheVario/CompZoneAerienne/zones_gnuplot/027_png_PROTECT_4229_Gypaete_barbu_-_Zone_Tampon_300m_sol.png

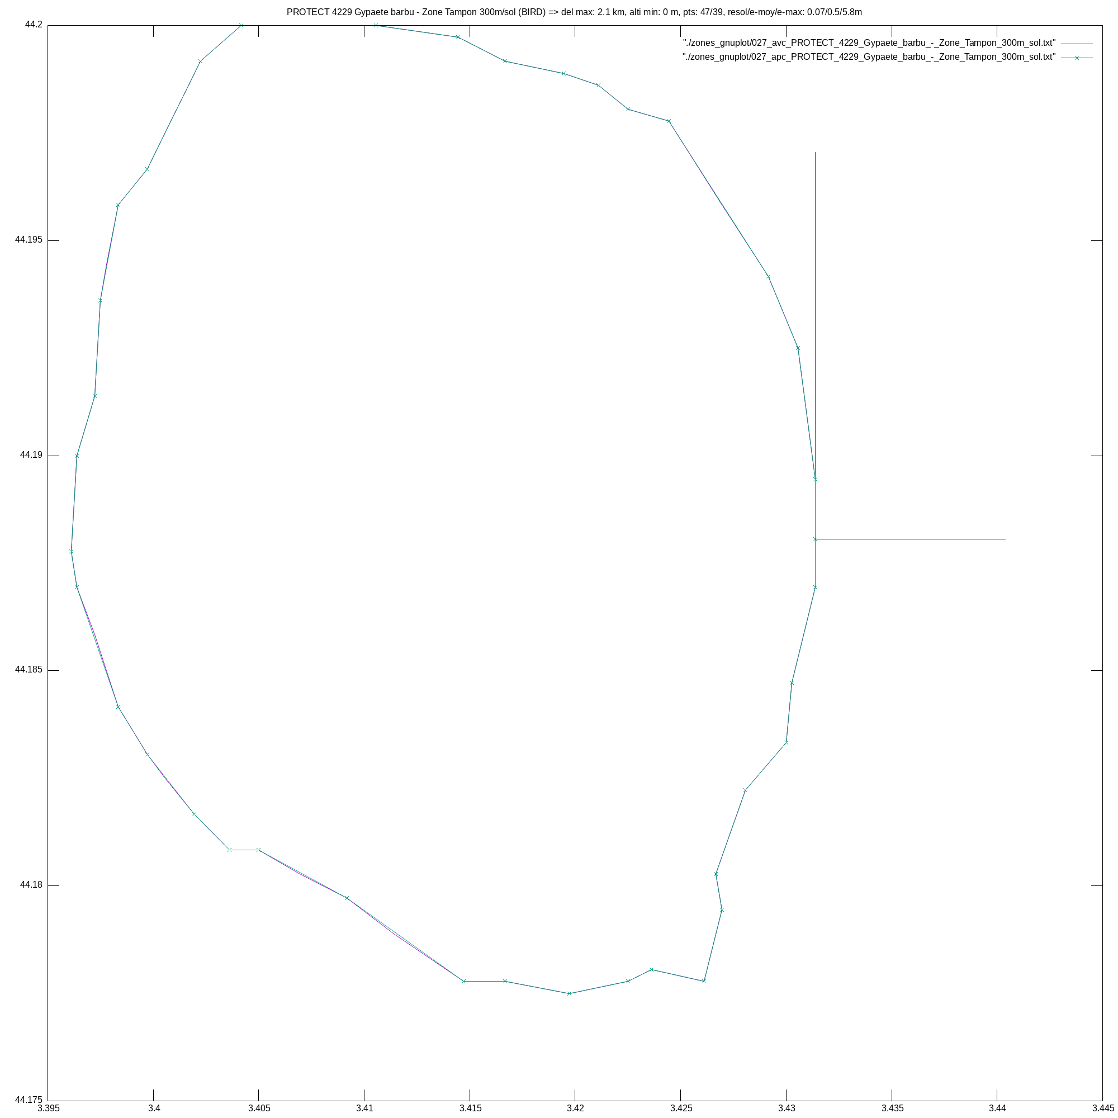
CompZoneAerienne/zones_gnuplot/027_png_PROTECT_4229_Gypaete_barbu_-_Zone_Tampon_300m_sol.png
