gitberthe/BertheVario/CompZoneAerienne/zones_gnuplot/028_png_CTA_LYON.png

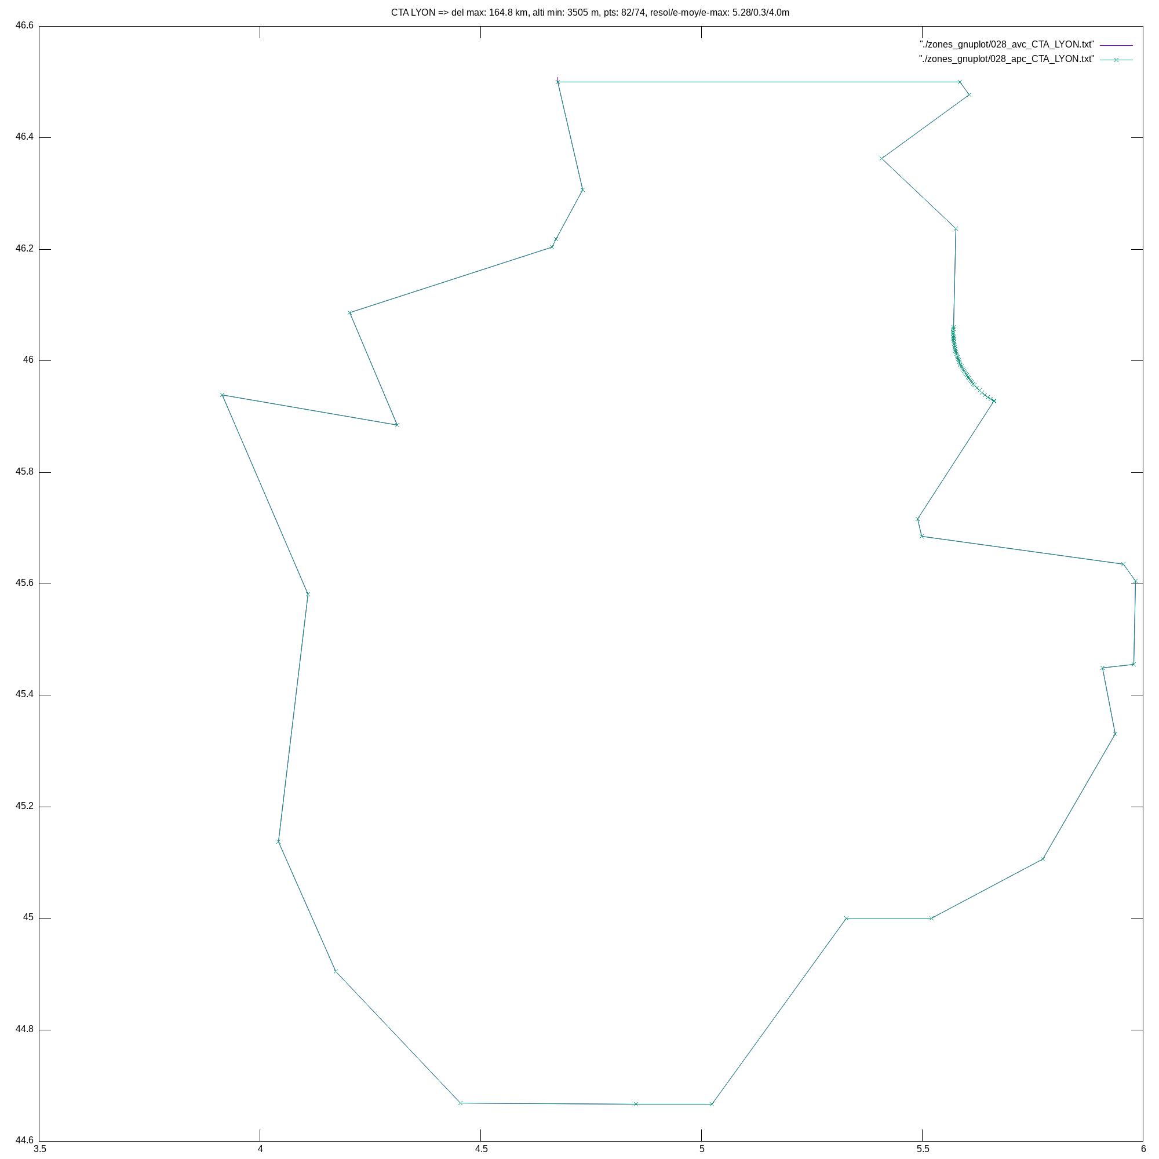
CompZoneAerienne/zones_gnuplot/028_png_CTA_LYON.png
