gitberthe/BertheVario/CompZoneAerienne/zones_gnuplot/029_png_PROTECT_Puy_D_Anzelles___Plateau_des_Vaugondieres.png

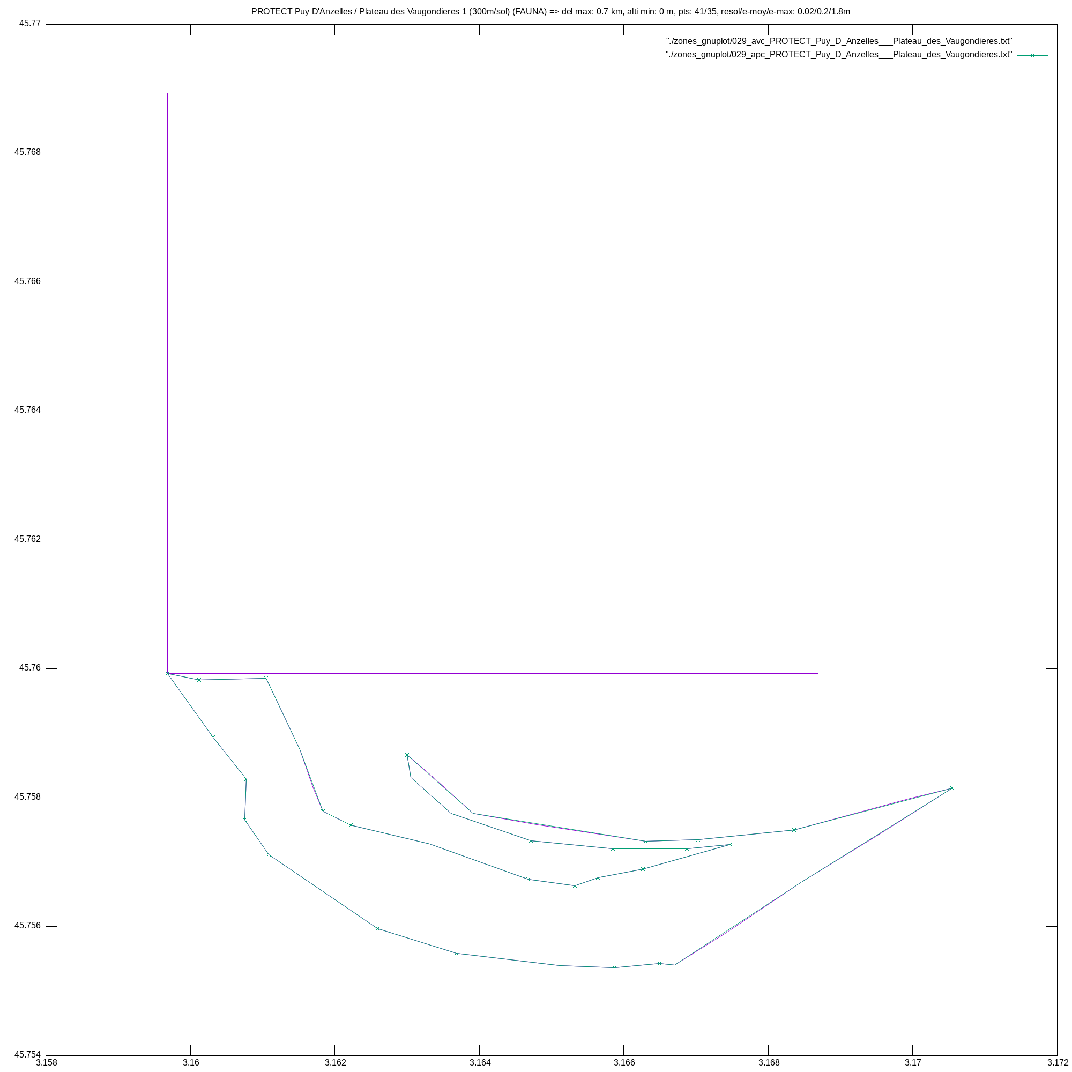
CompZoneAerienne/zones_gnuplot/029_png_PROTECT_Puy_D_Anzelles___Plateau_des_Vaugondieres.png
