gitberthe/BertheVario/CompZoneAerienne/zones_gnuplot/030_png_R_68_B.png

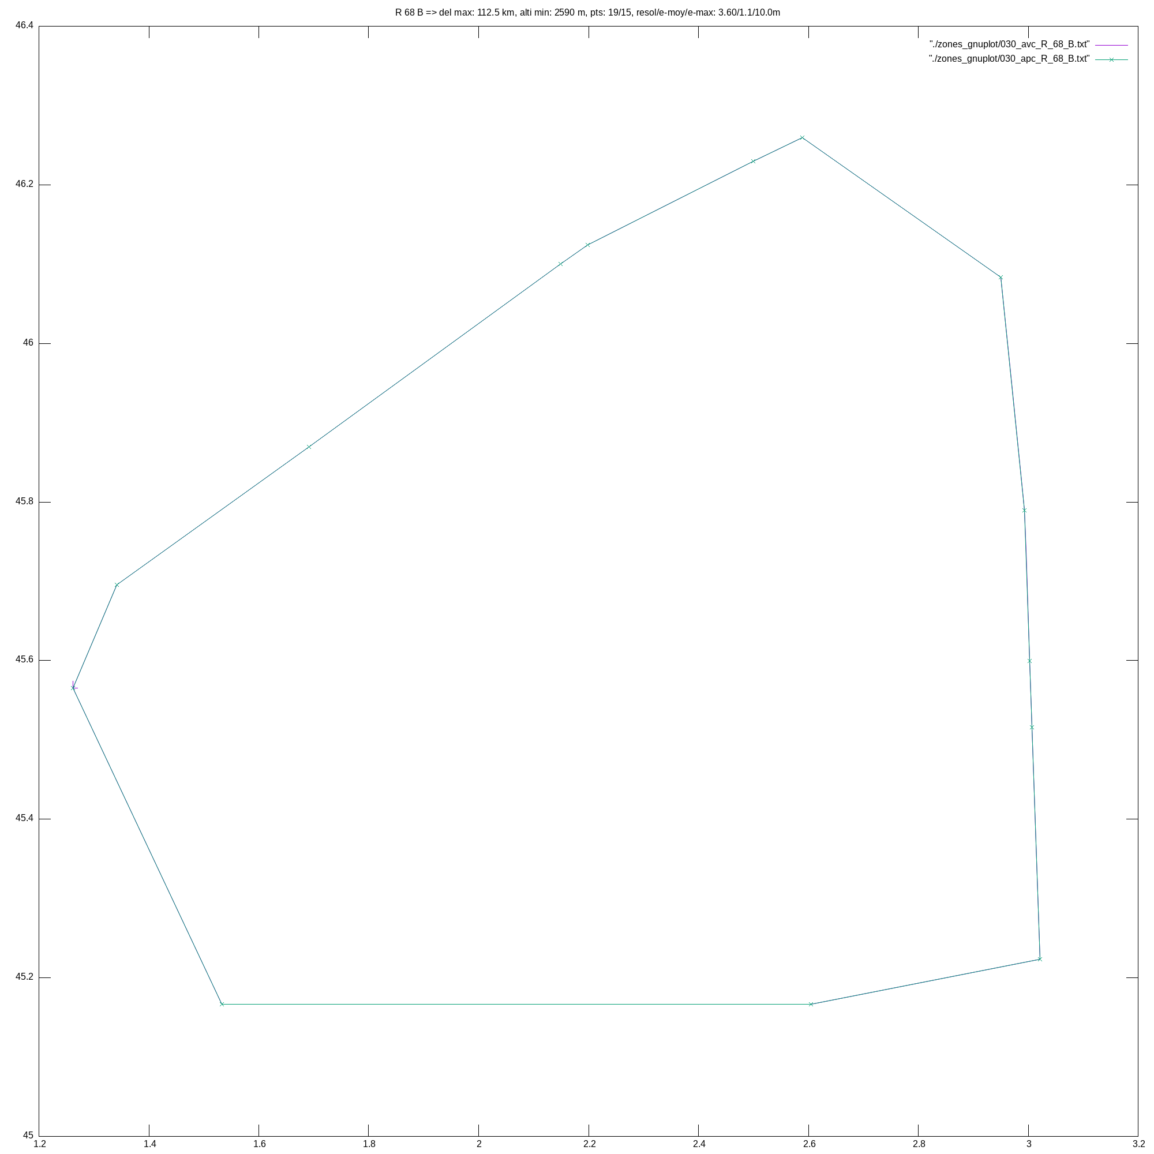
CompZoneAerienne/zones_gnuplot/030_png_R_68_B.png
