gitberthe/BertheVario/CompZoneAerienne/zones_gnuplot/031_png_R_368_B.png

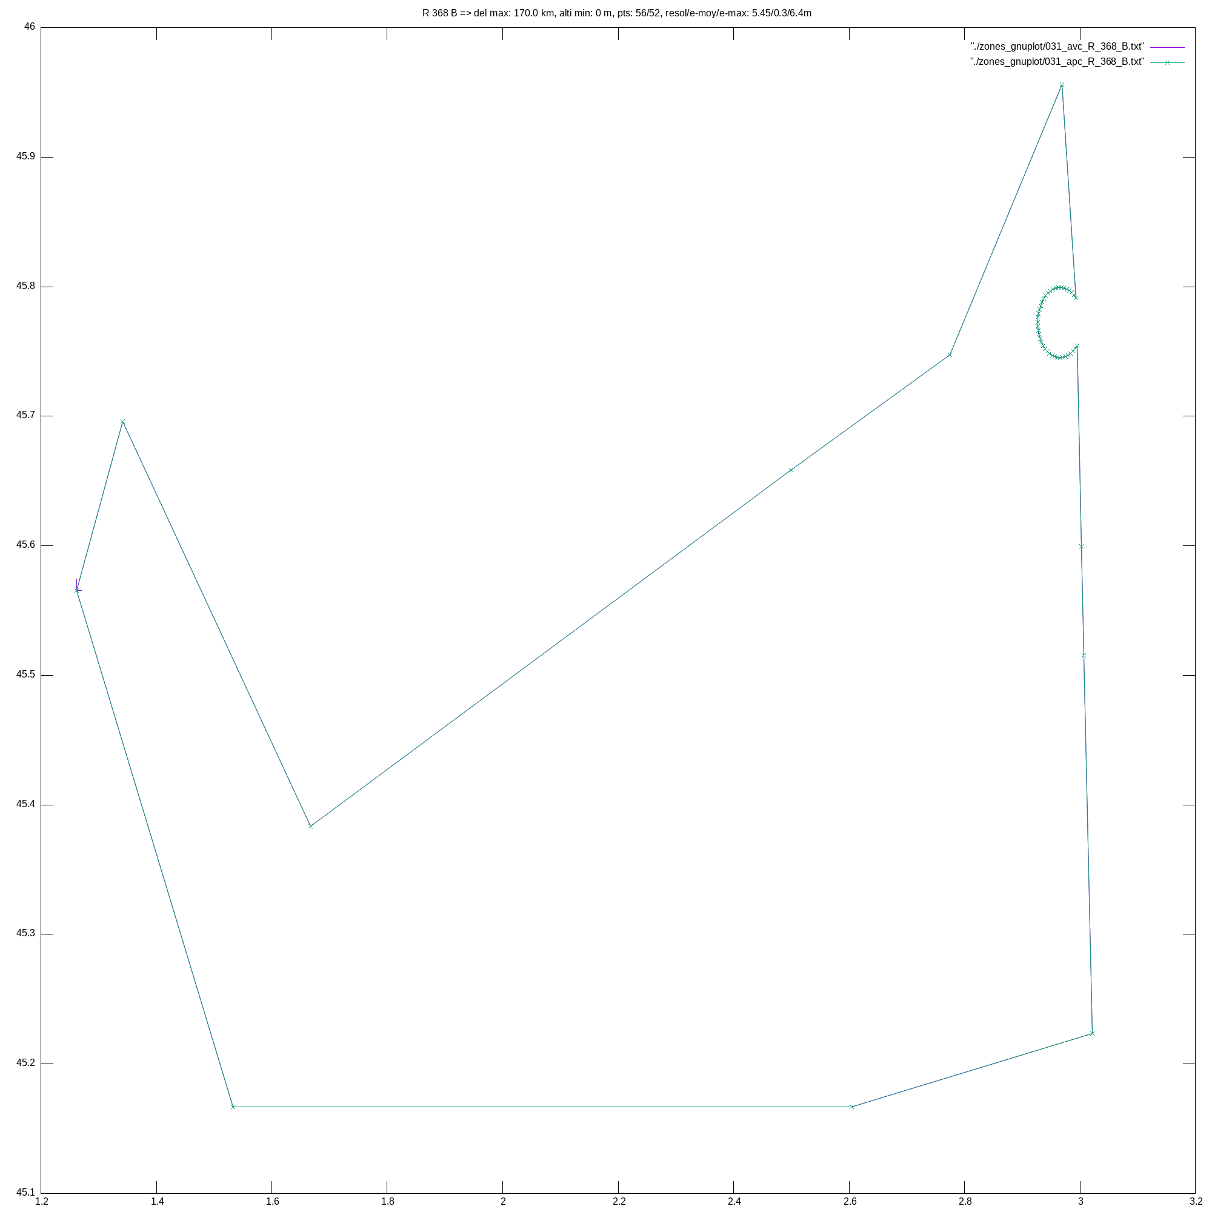
CompZoneAerienne/zones_gnuplot/031_png_R_368_B.png
