gitberthe/BertheVario/CompZoneAerienne/zones_gnuplot/032_png_TMA_CLERMONT_2_App_122.225_.png

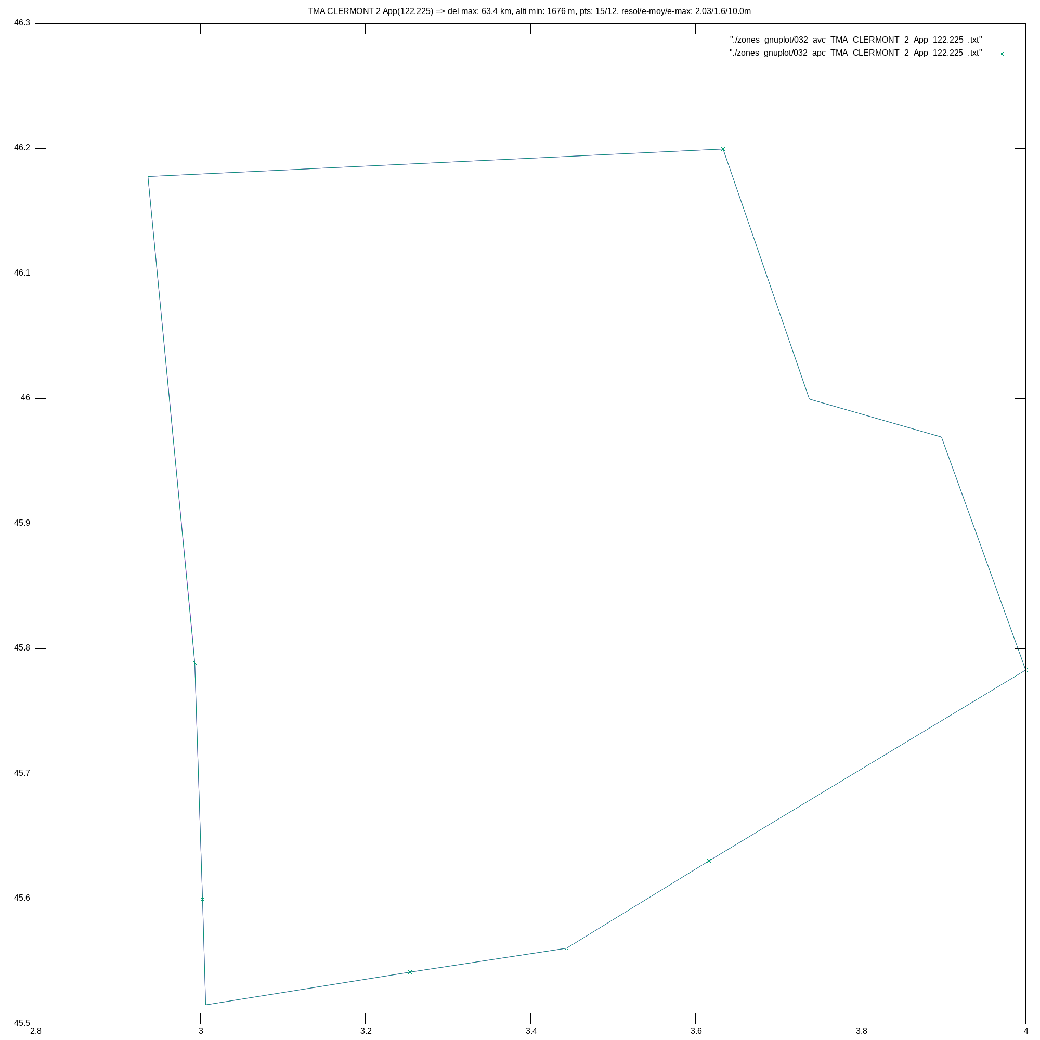
CompZoneAerienne/zones_gnuplot/032_png_TMA_CLERMONT_2_App_122.225_.png
