gitberthe/BertheVario/CompZoneAerienne/zones_gnuplot/033_png_CTA_MARSEILLE_7.png

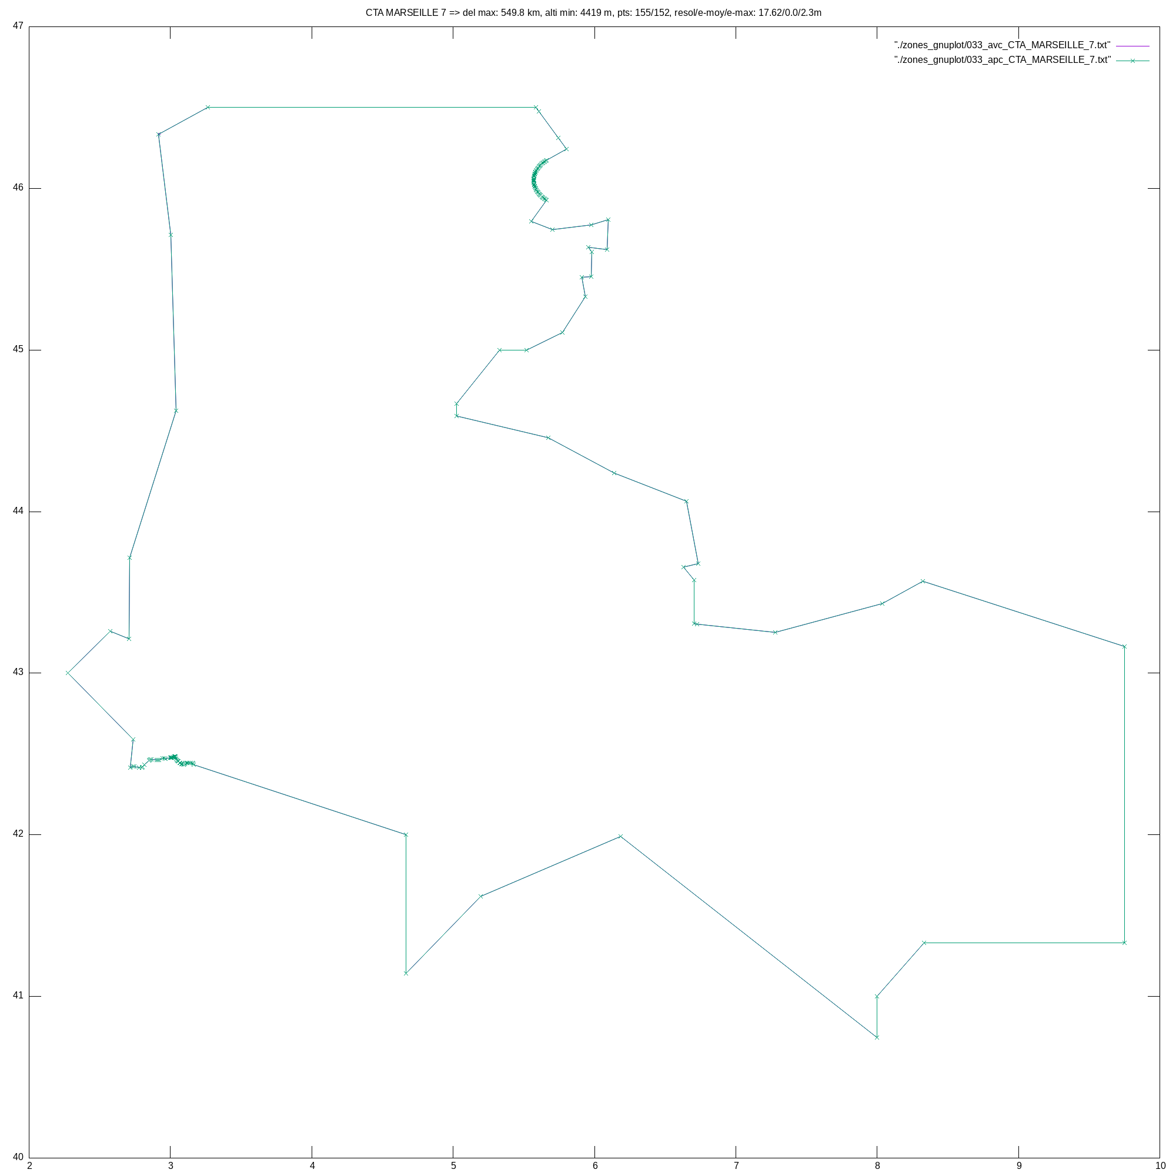
CompZoneAerienne/zones_gnuplot/033_png_CTA_MARSEILLE_7.png
