gitberthe/BertheVario/CompZoneAerienne/zones_gnuplot/034_png_TMA_CLERMONT_5_App_122.225_.png

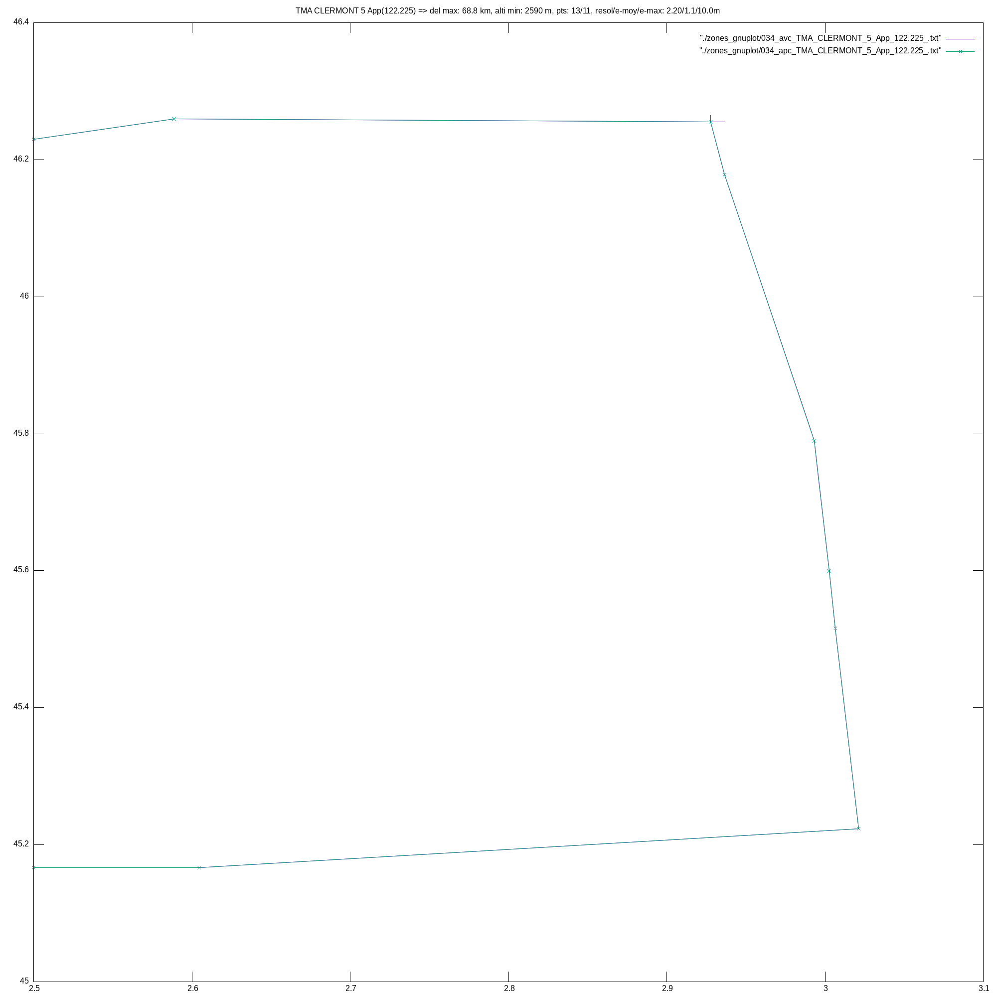
CompZoneAerienne/zones_gnuplot/034_png_TMA_CLERMONT_5_App_122.225_.png
