gitberthe/BertheVario/CompZoneAerienne/zones_gnuplot/035_png_CTR_SAINT-YAN_1_Twr_122.300_.png

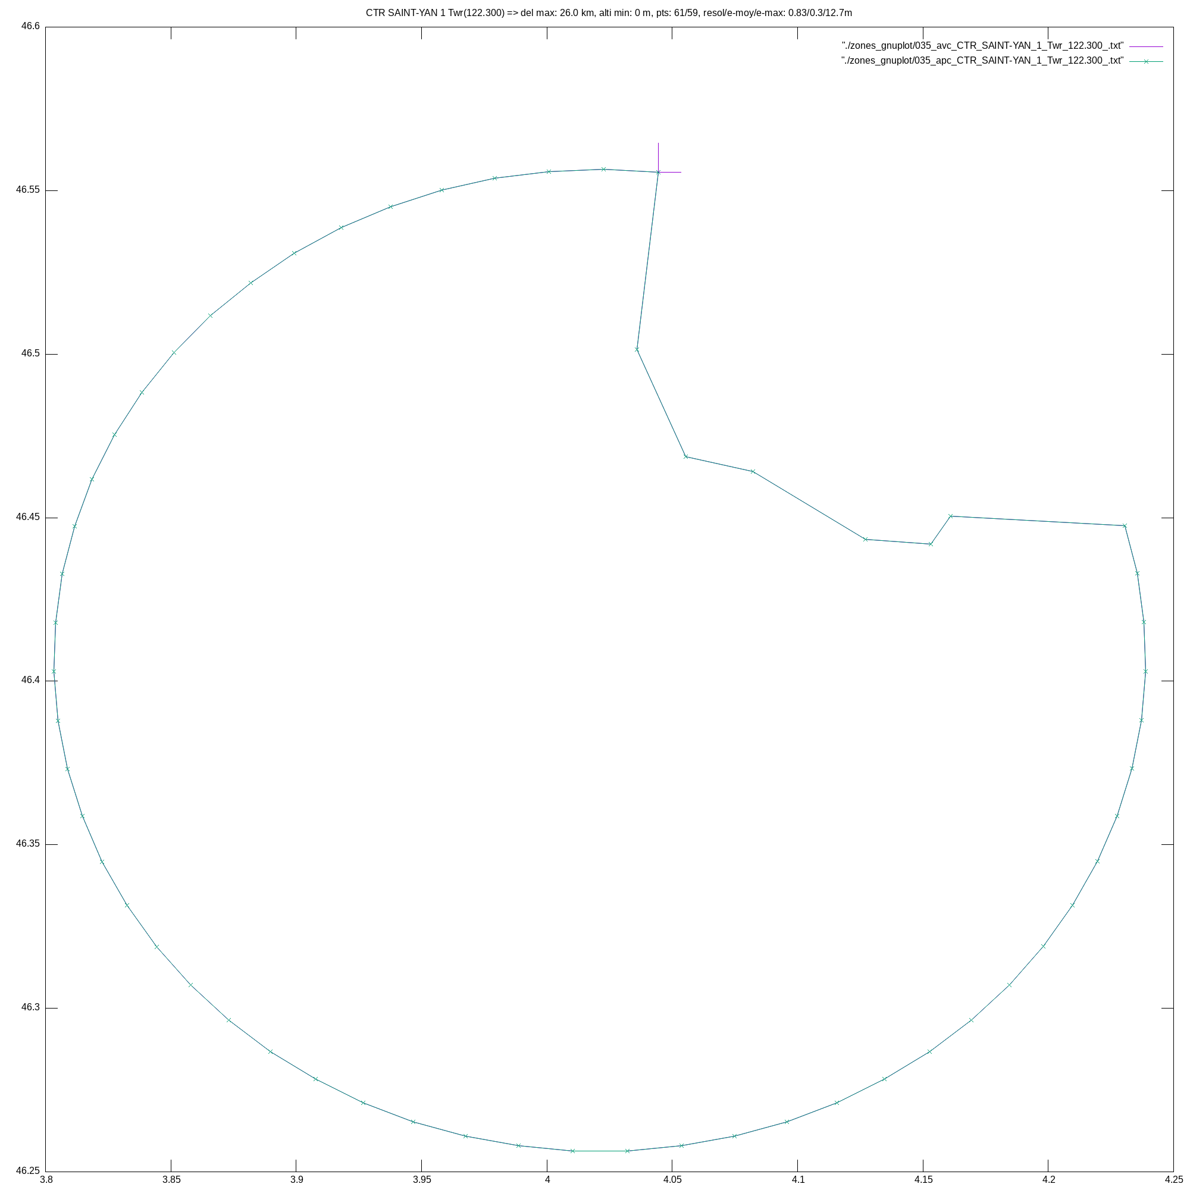
CompZoneAerienne/zones_gnuplot/035_png_CTR_SAINT-YAN_1_Twr_122.300_.png
