gitberthe/BertheVario/CompZoneAerienne/zones_gnuplot/037_png_R_167_A_App_119.2___SeeNotam_.png

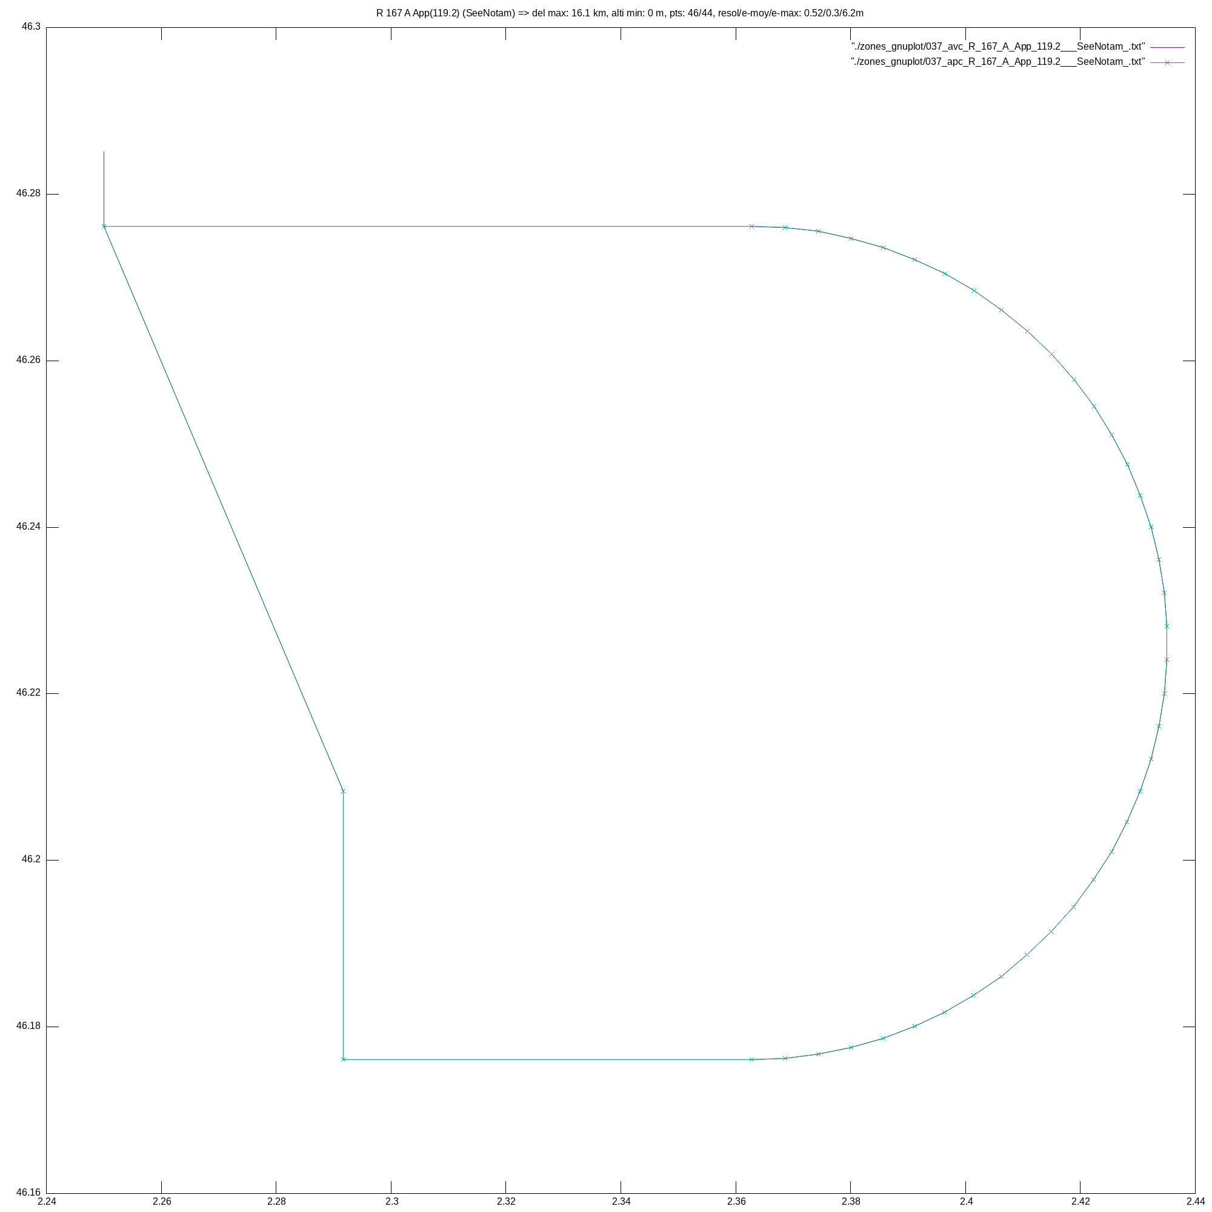
CompZoneAerienne/zones_gnuplot/037_png_R_167_A_App_119.2___SeeNotam_.png
