gitberthe/BertheVario/CompZoneAerienne/zones_gnuplot/038_png_CTA_MONTPELLIER.png

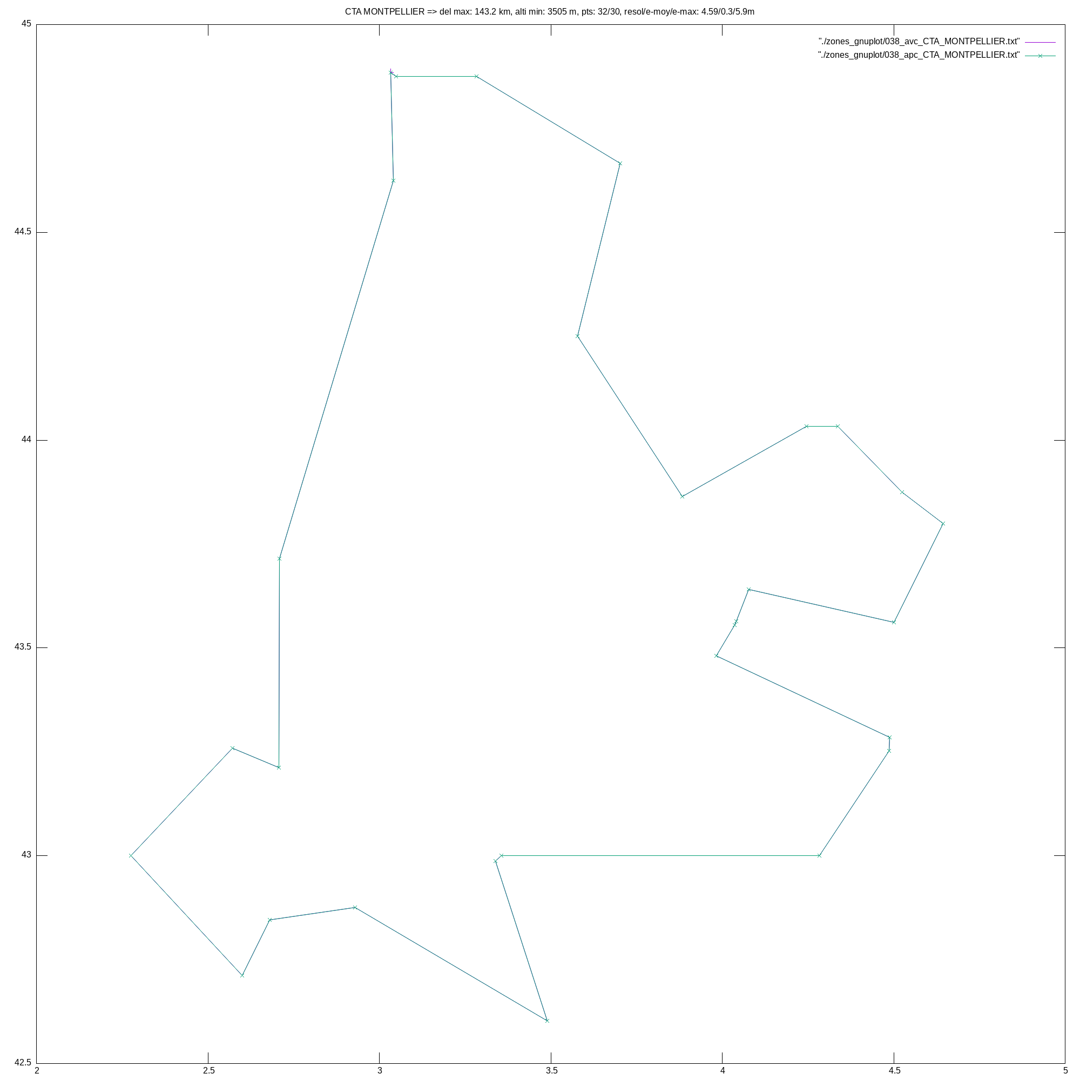
CompZoneAerienne/zones_gnuplot/038_png_CTA_MONTPELLIER.png
