gitberthe/BertheVario/CompZoneAerienne/zones_gnuplot/039_png_CTA_TOULOUSE_3.png

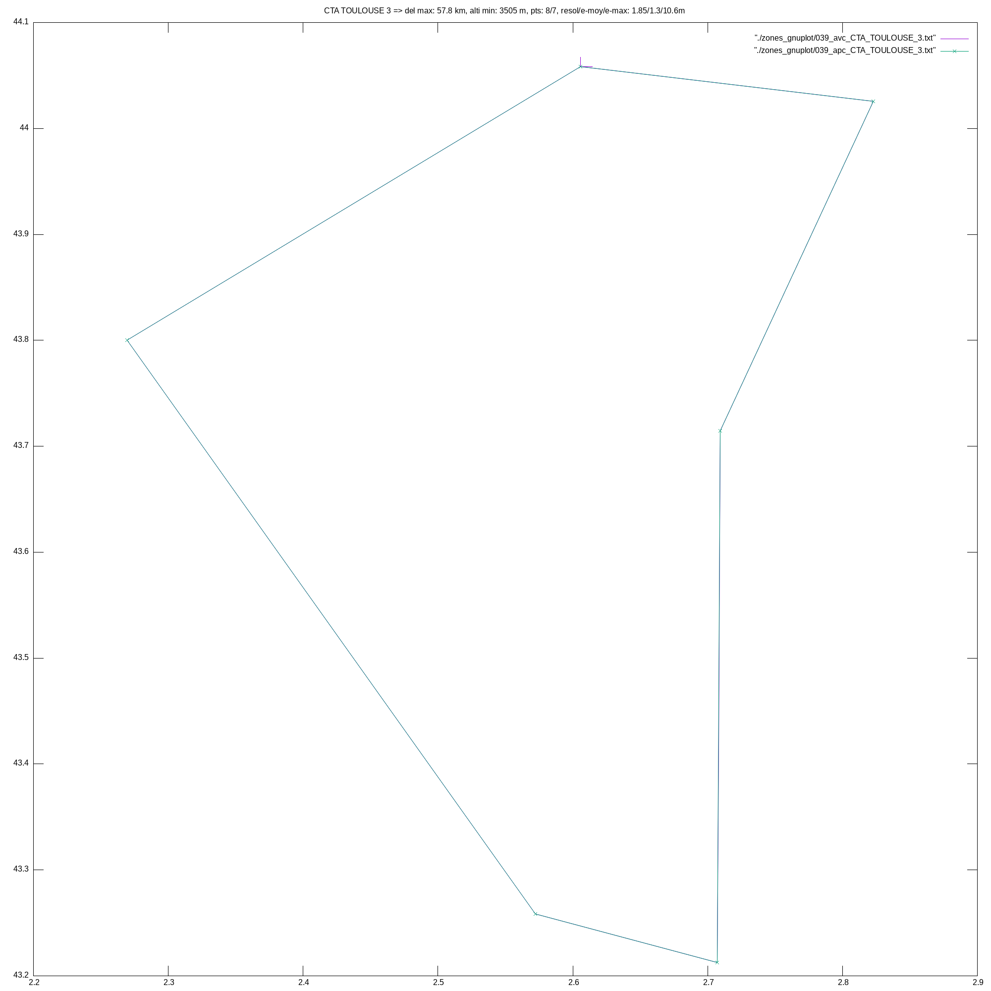
CompZoneAerienne/zones_gnuplot/039_png_CTA_TOULOUSE_3.png
