gitberthe/BertheVario/CompZoneAerienne/zones_gnuplot/040_png_R_368_C1.png

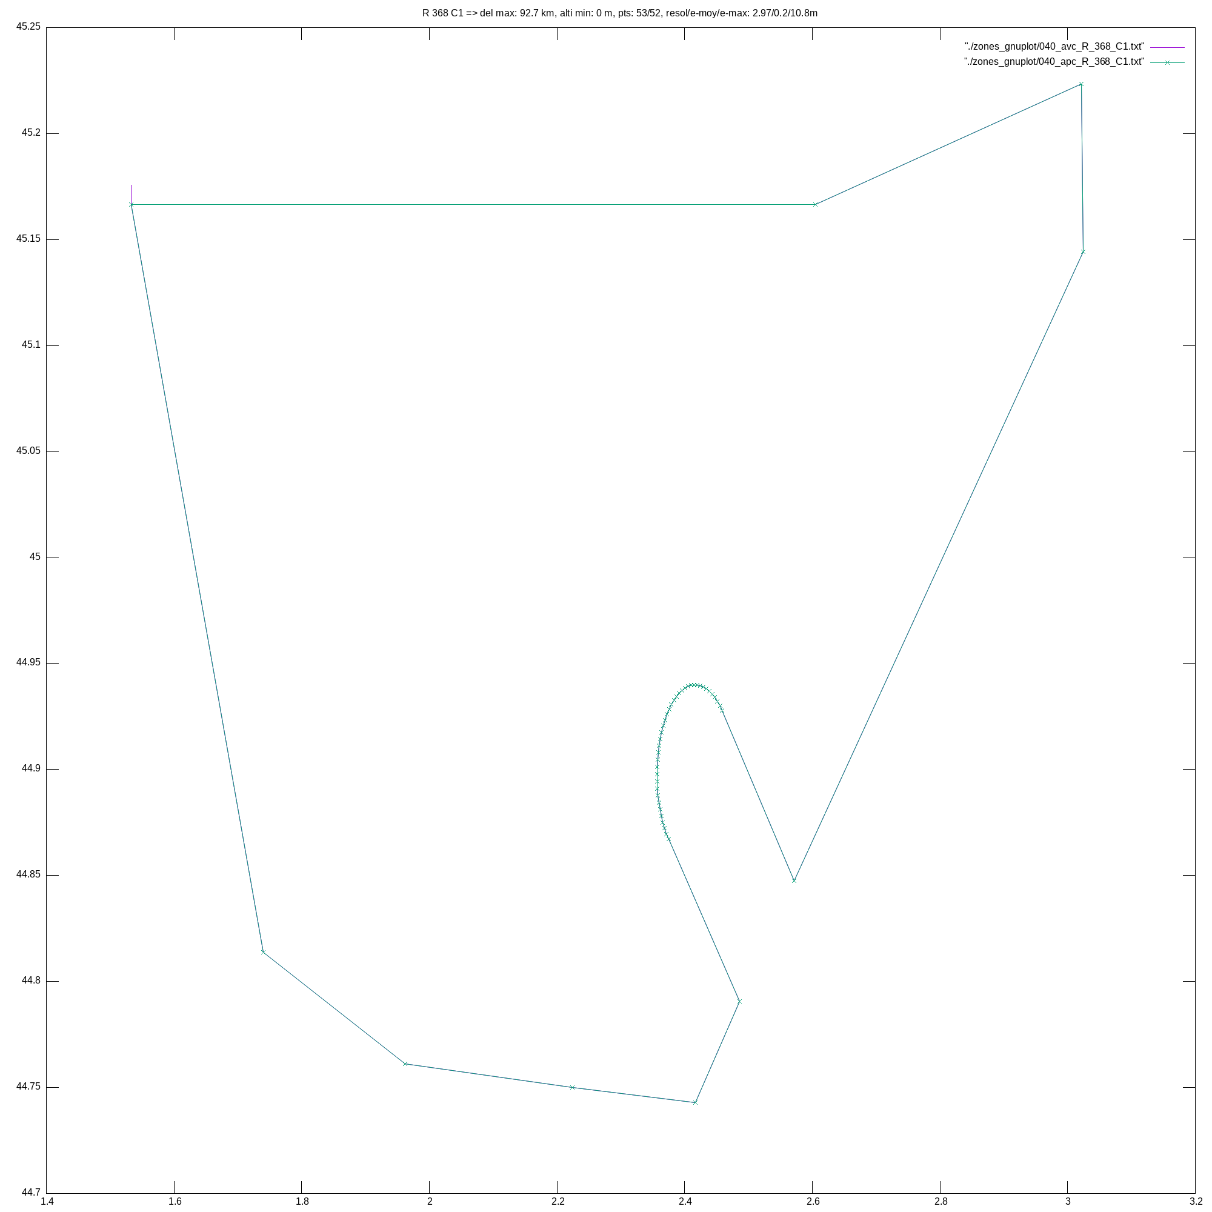
CompZoneAerienne/zones_gnuplot/040_png_R_368_C1.png
