gitberthe/BertheVario/CompZoneAerienne/zones_gnuplot/041_png_R_68_A.png

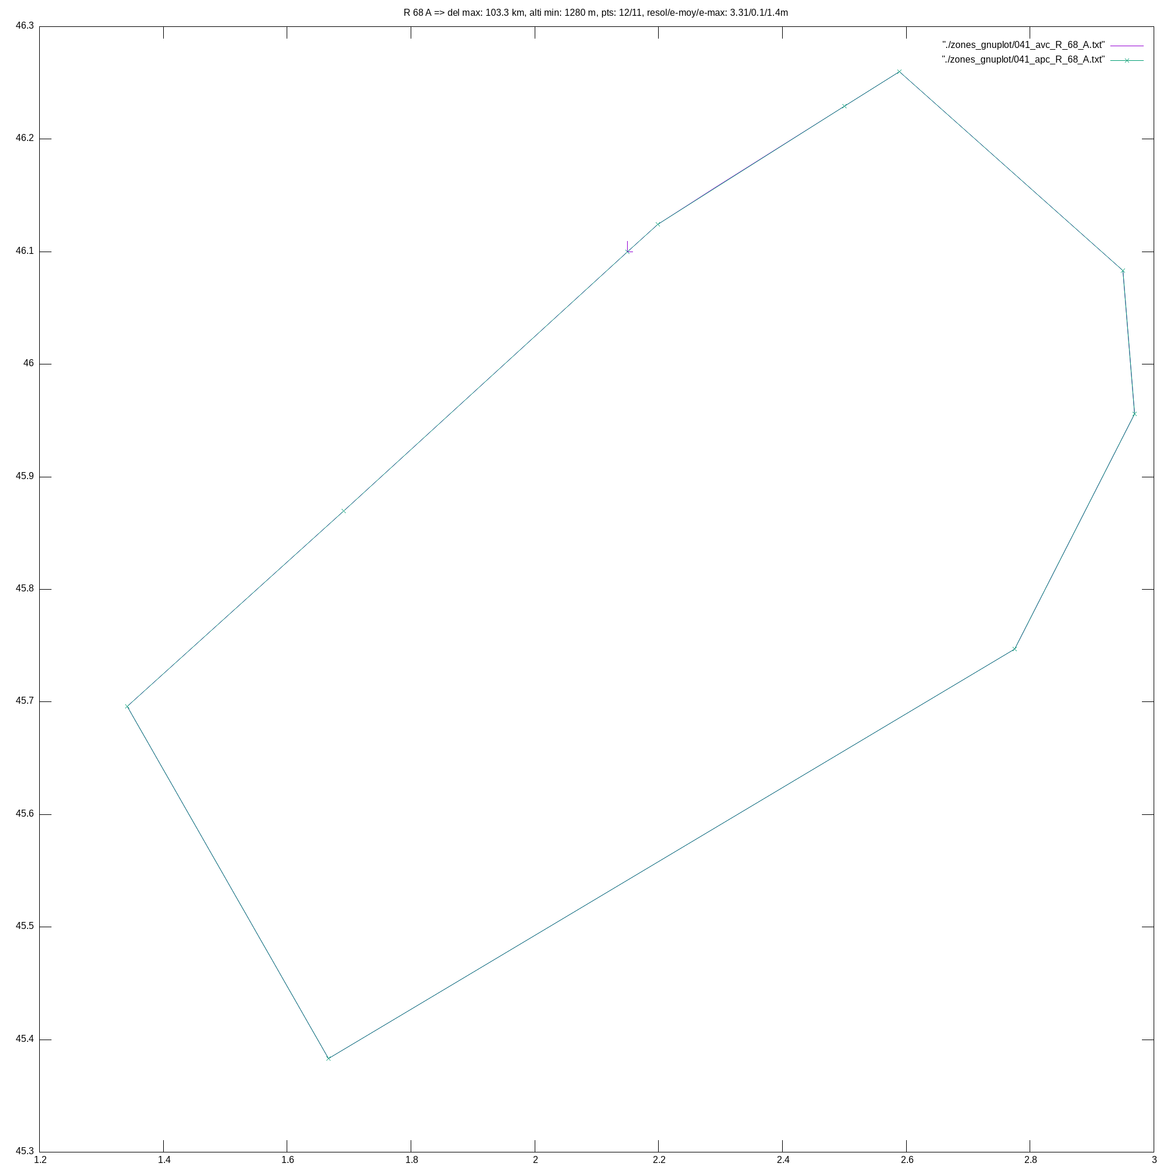
CompZoneAerienne/zones_gnuplot/041_png_R_68_A.png
