gitberthe/BertheVario/CompZoneAerienne/zones_gnuplot/042_png_TMA_MONTPELLIER_4_App_130.855_.png

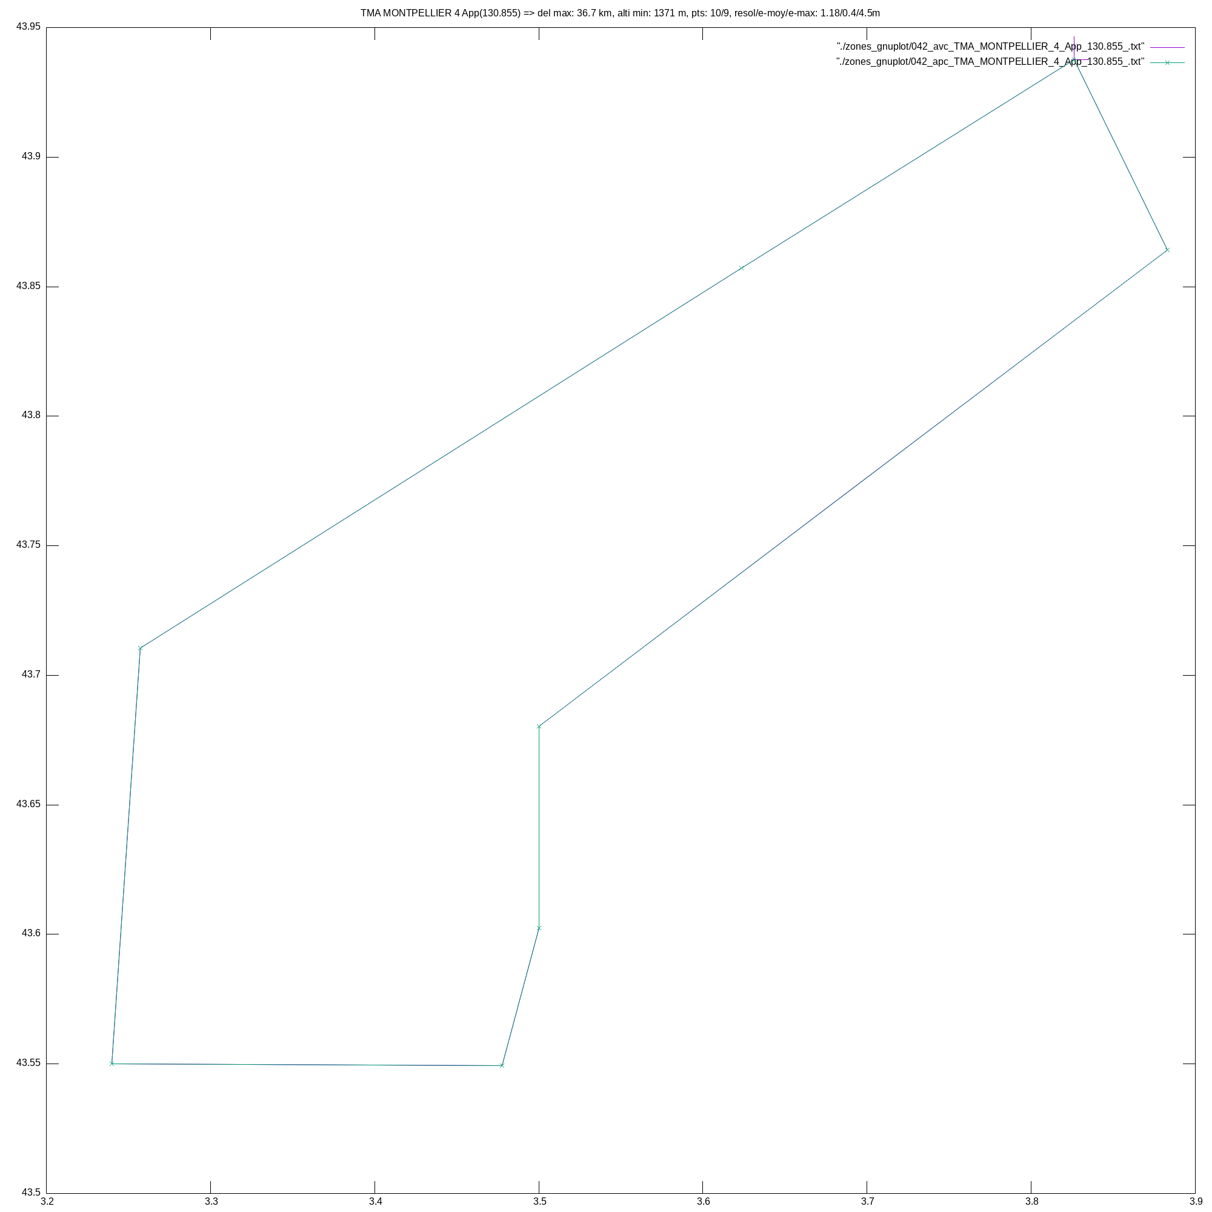
CompZoneAerienne/zones_gnuplot/042_png_TMA_MONTPELLIER_4_App_130.855_.png
