gitberthe/BertheVario/CompZoneAerienne/zones_gnuplot/043_png_FFVL-Prot_Parc_Cevennes_Tarn_Ouest__500m_sol_.png

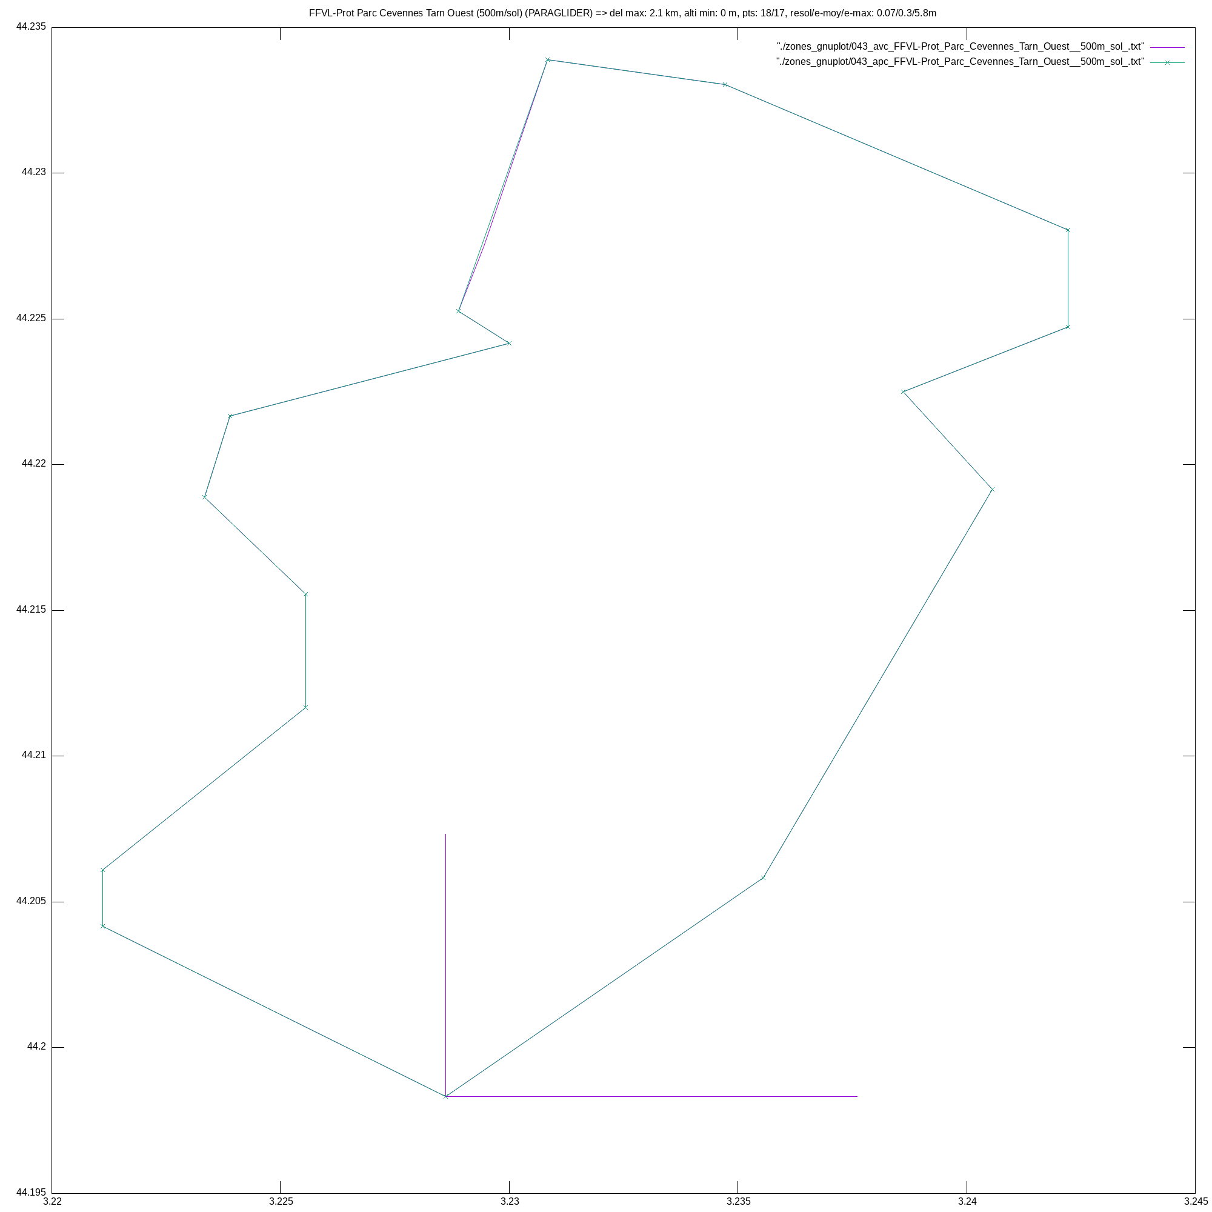
CompZoneAerienne/zones_gnuplot/043_png_FFVL-Prot_Parc_Cevennes_Tarn_Ouest__500m_sol_.png
