gitberthe/BertheVario/CompZoneAerienne/zones_gnuplot/045_png_FFVL-Prot_Parc_Cevennes_Combe_Ouest__500m_sol_.png

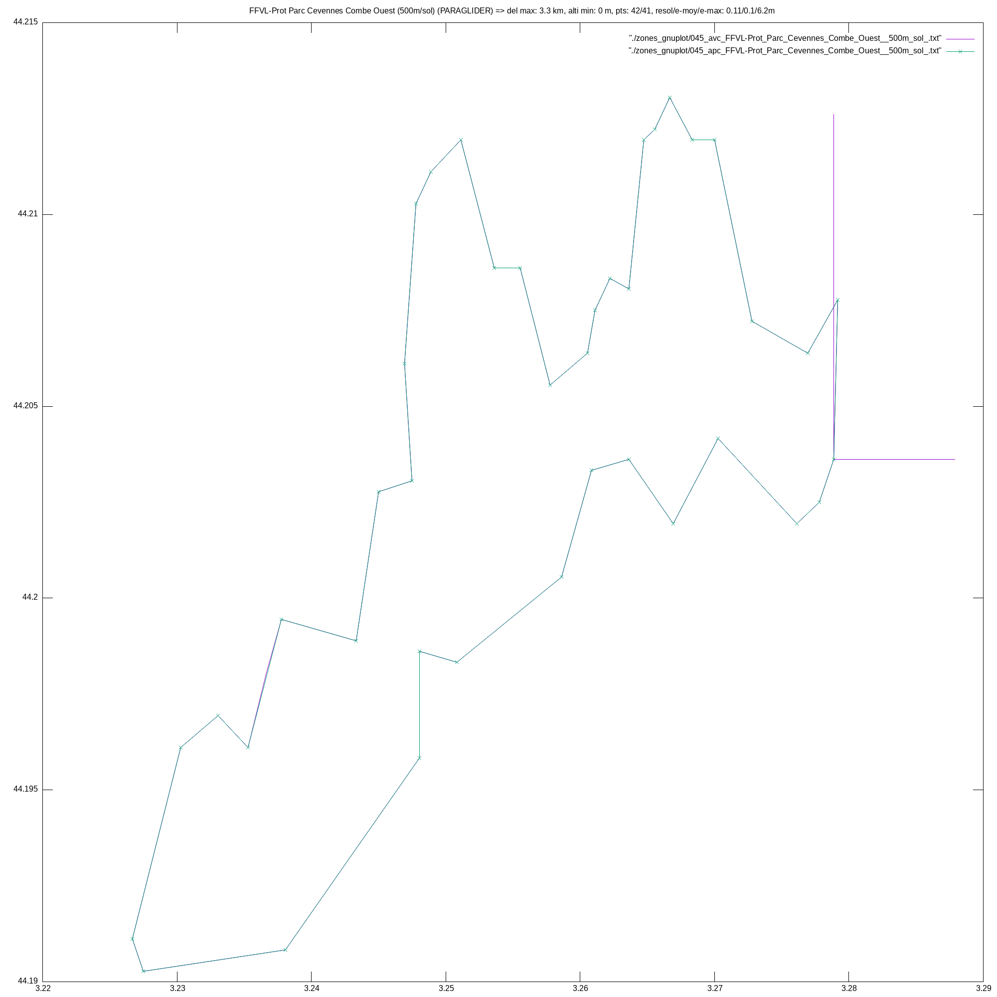
CompZoneAerienne/zones_gnuplot/045_png_FFVL-Prot_Parc_Cevennes_Combe_Ouest__500m_sol_.png
