gitberthe/BertheVario/CompZoneAerienne/zones_gnuplot/046_png_PROTECT_Puy_D_Anzelles___Plateau_des_Vaugondires.png

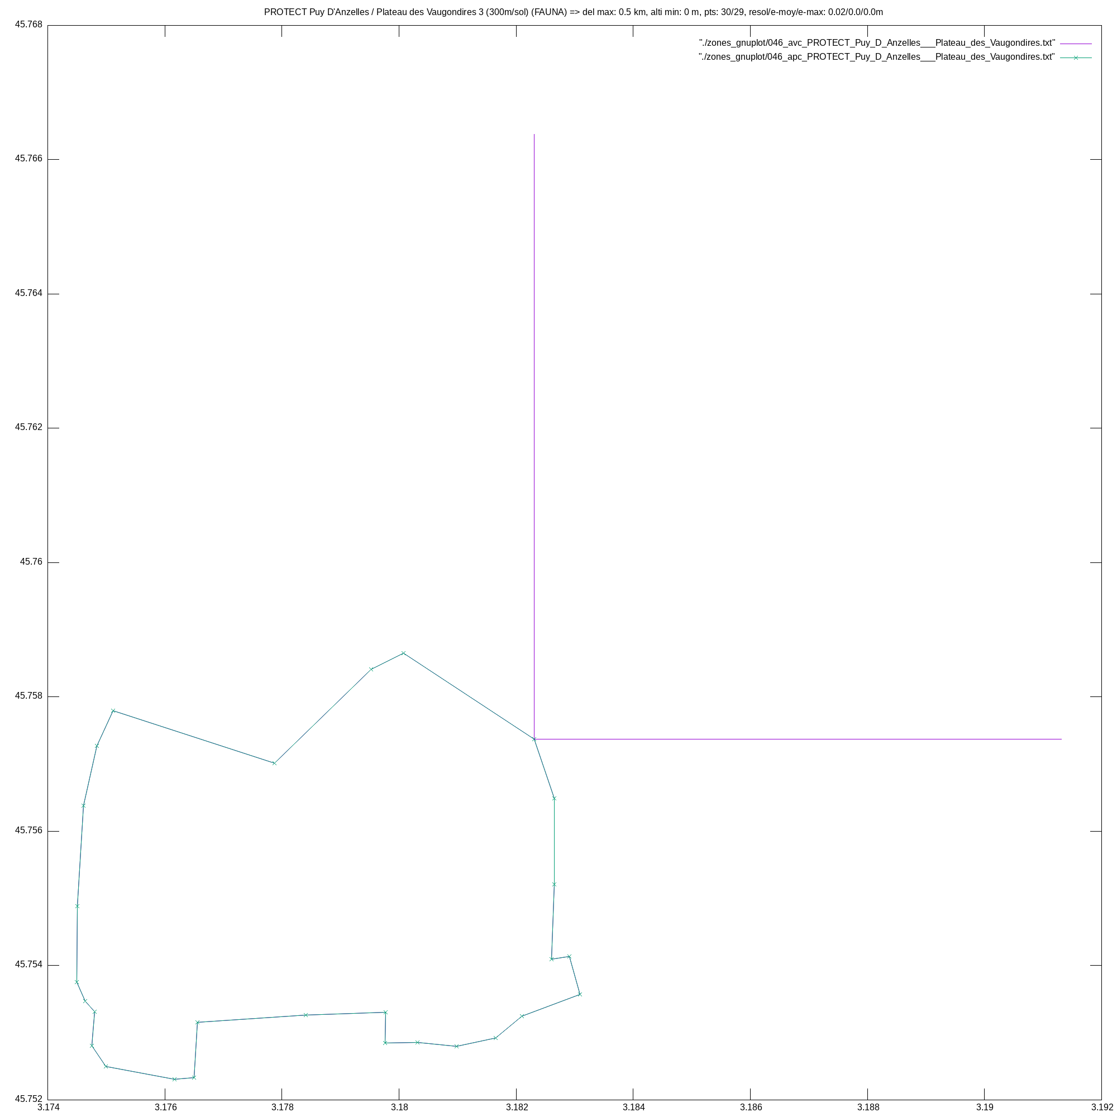
CompZoneAerienne/zones_gnuplot/046_png_PROTECT_Puy_D_Anzelles___Plateau_des_Vaugondires.png
