gitberthe/BertheVario/CompZoneAerienne/zones_gnuplot/048_png_CTA_CLERMONT_1.png

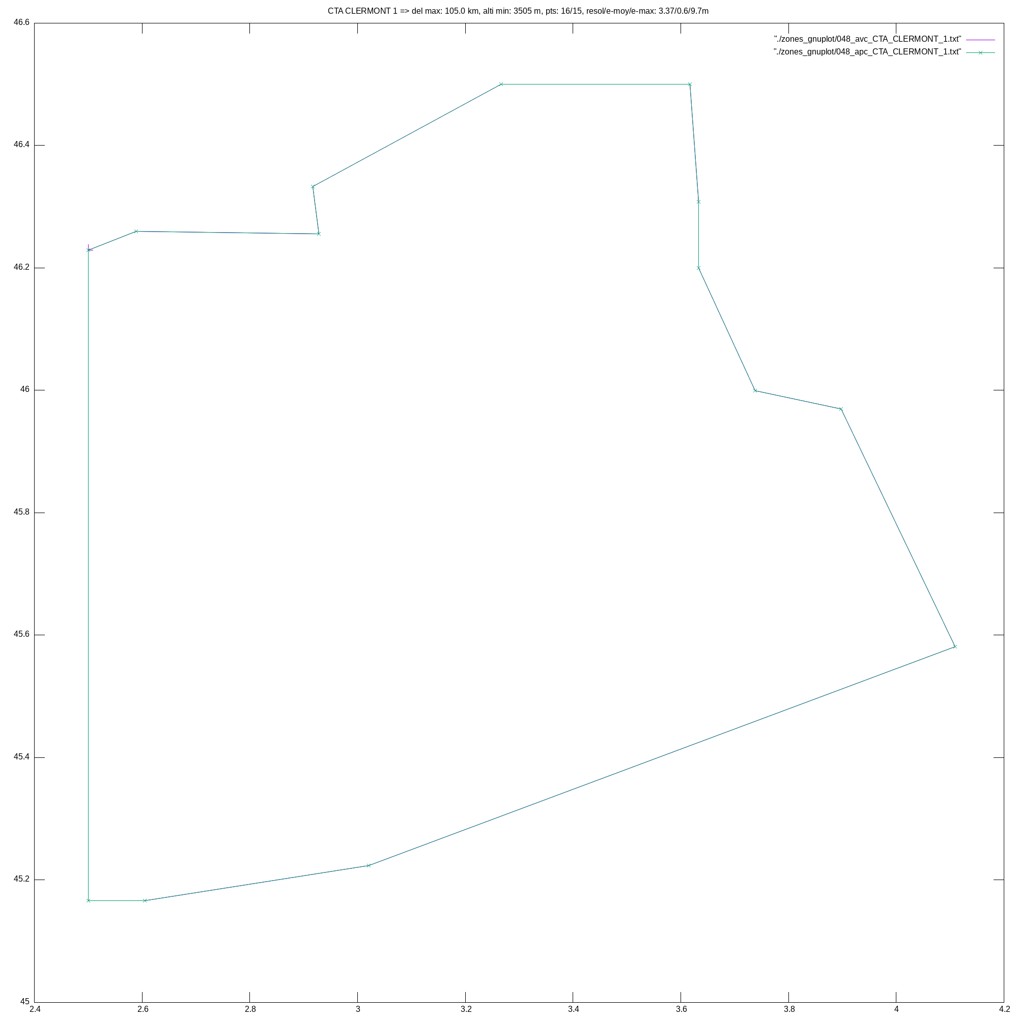
CompZoneAerienne/zones_gnuplot/048_png_CTA_CLERMONT_1.png
