gitberthe/BertheVario/CompZoneAerienne/zones_gnuplot/049_png_PROTECT_5516_Gypaete_barbu_-_Zone_Tampon_300m_sol.png

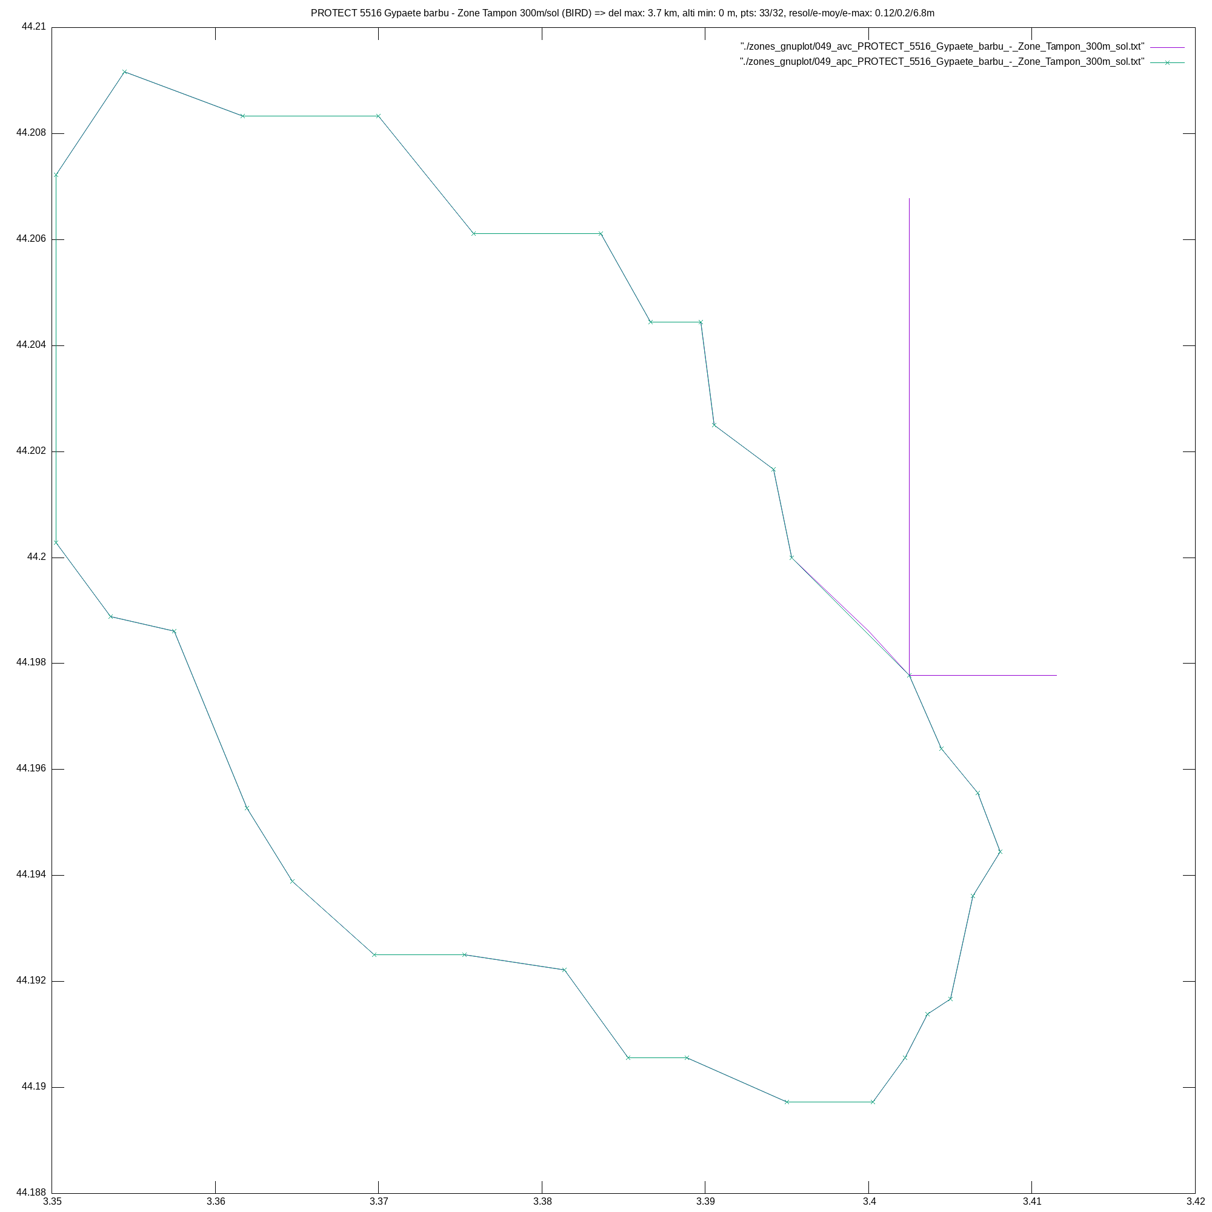
CompZoneAerienne/zones_gnuplot/049_png_PROTECT_5516_Gypaete_barbu_-_Zone_Tampon_300m_sol.png
