gitberthe/BertheVario/CompZoneAerienne/zones_gnuplot/050_png_TMA_CLERMONT_2.2_App_122.225_.png

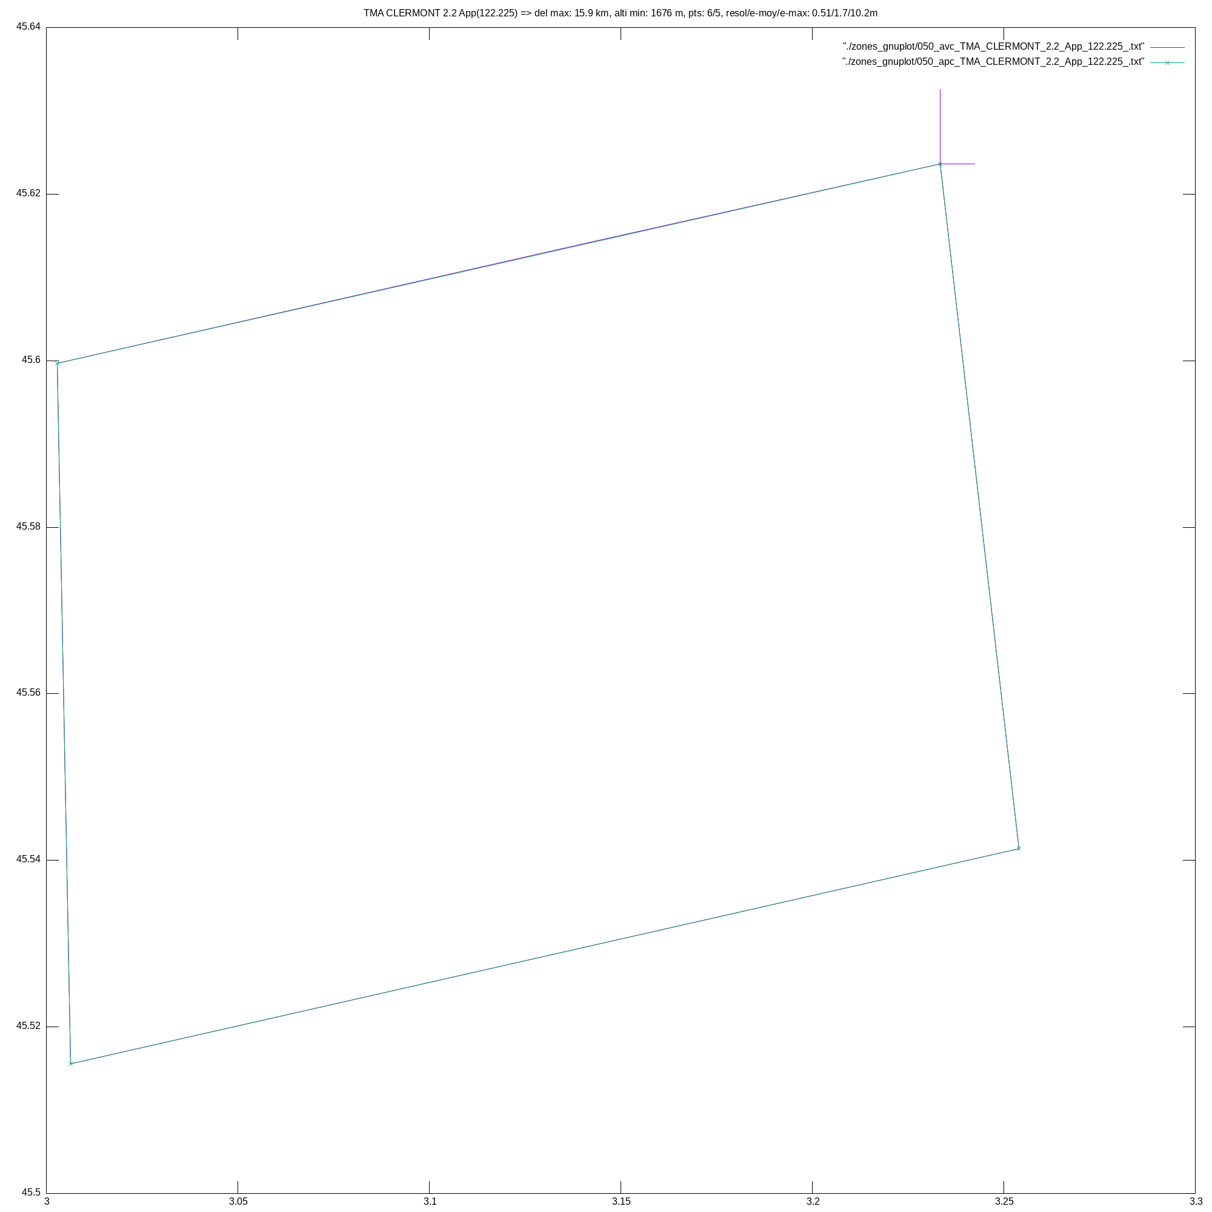
CompZoneAerienne/zones_gnuplot/050_png_TMA_CLERMONT_2.2_App_122.225_.png
