gitberthe/BertheVario/CompZoneAerienne/zones_gnuplot/051_png_FFVL-Prot_Parc_Cevennes_Combe_Est__500m_sol_.png

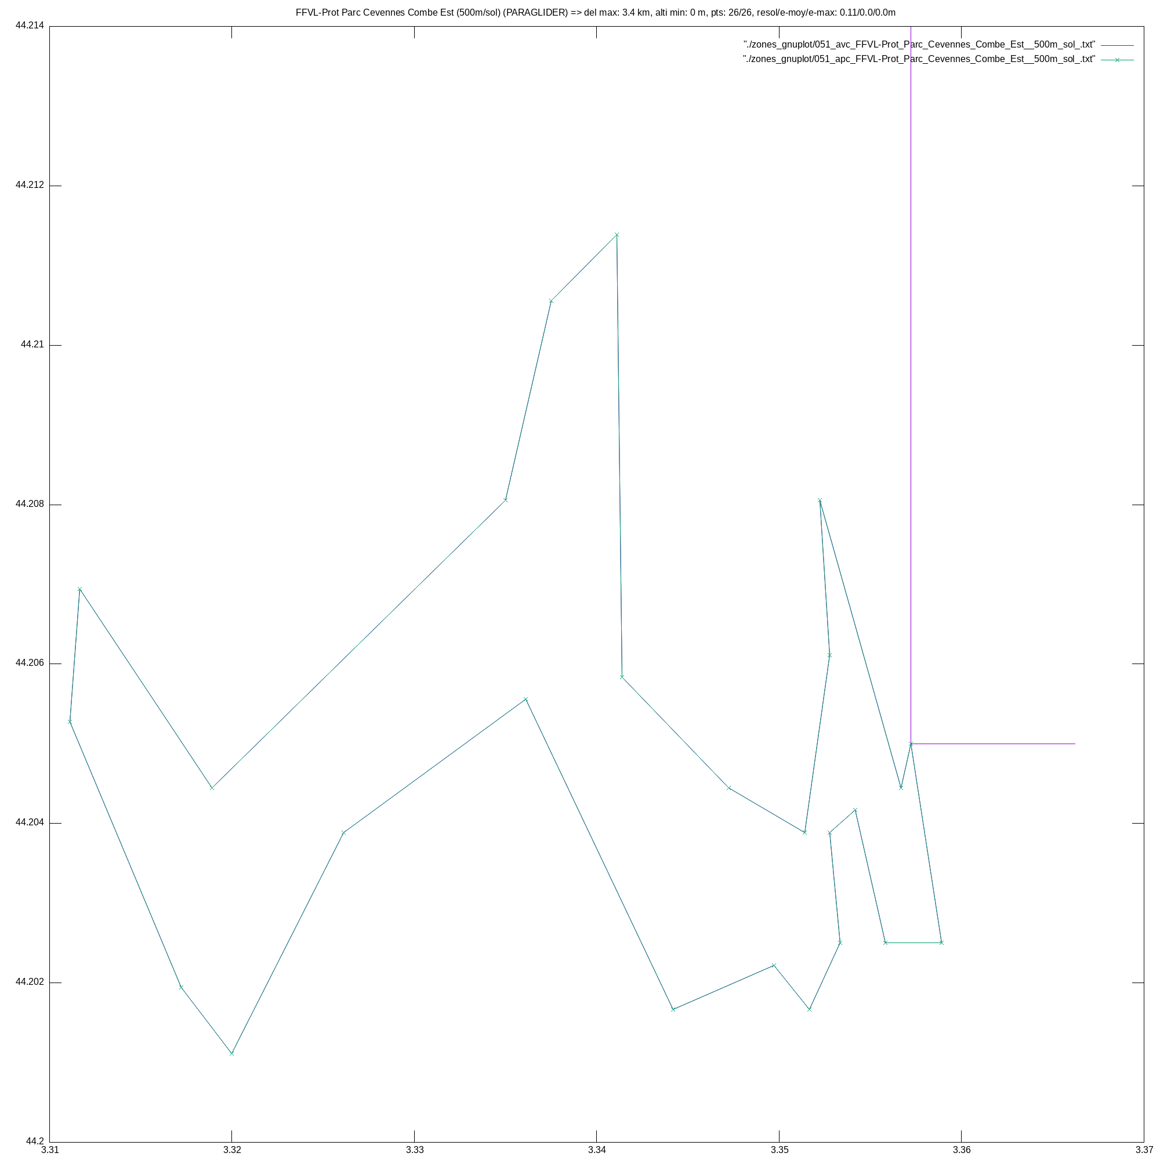
CompZoneAerienne/zones_gnuplot/051_png_FFVL-Prot_Parc_Cevennes_Combe_Est__500m_sol_.png
