gitberthe/BertheVario/CompZoneAerienne/zones_gnuplot/052_png_R_217__5.png

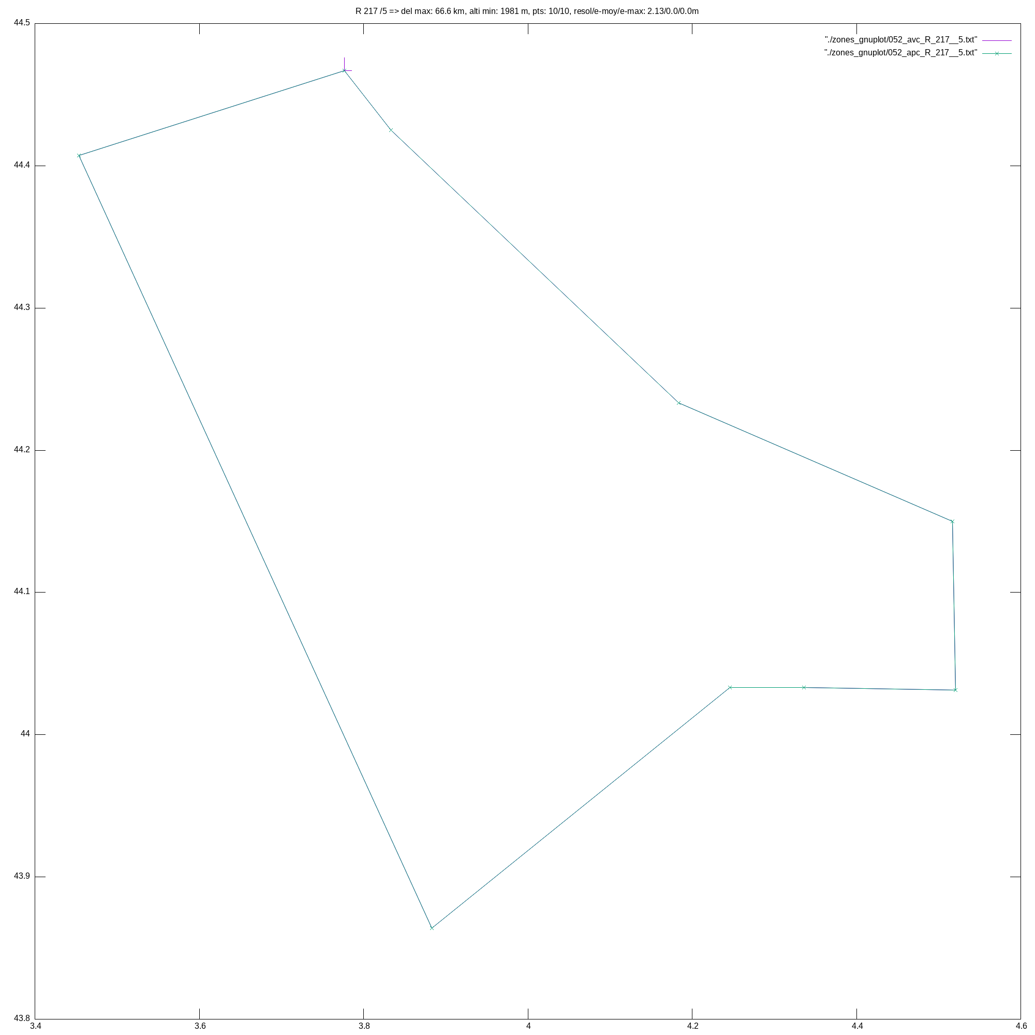
CompZoneAerienne/zones_gnuplot/052_png_R_217__5.png
