gitberthe/BertheVario/CompZoneAerienne/zones_gnuplot/053_png_TMA_MONTPELLIER_6.1_App_130.855_.png

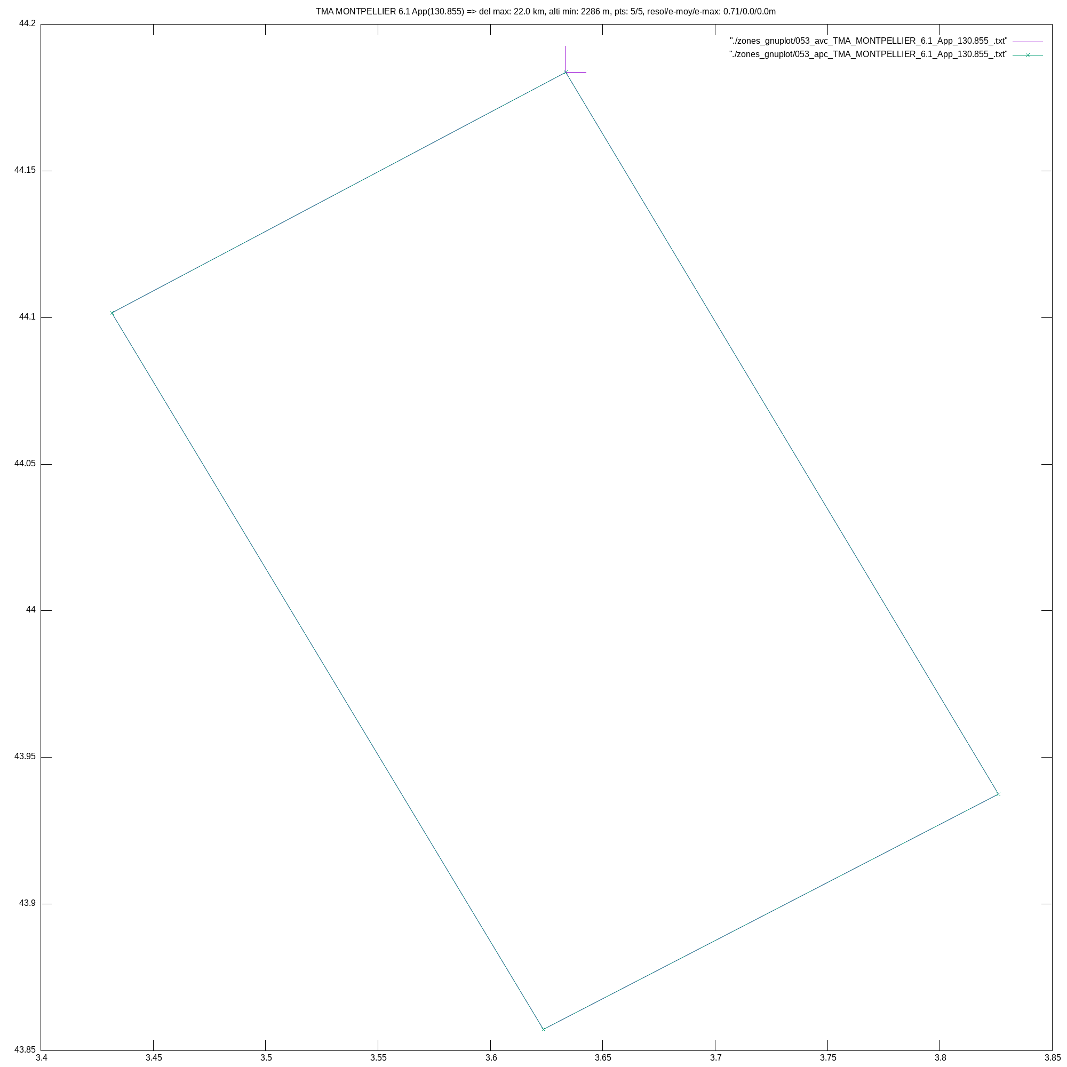
CompZoneAerienne/zones_gnuplot/053_png_TMA_MONTPELLIER_6.1_App_130.855_.png
