gitberthe/BertheVario/CompZoneAerienne/zones_gnuplot/054_png_RTBA_46_C__MILOPS___SeeNotam_.png

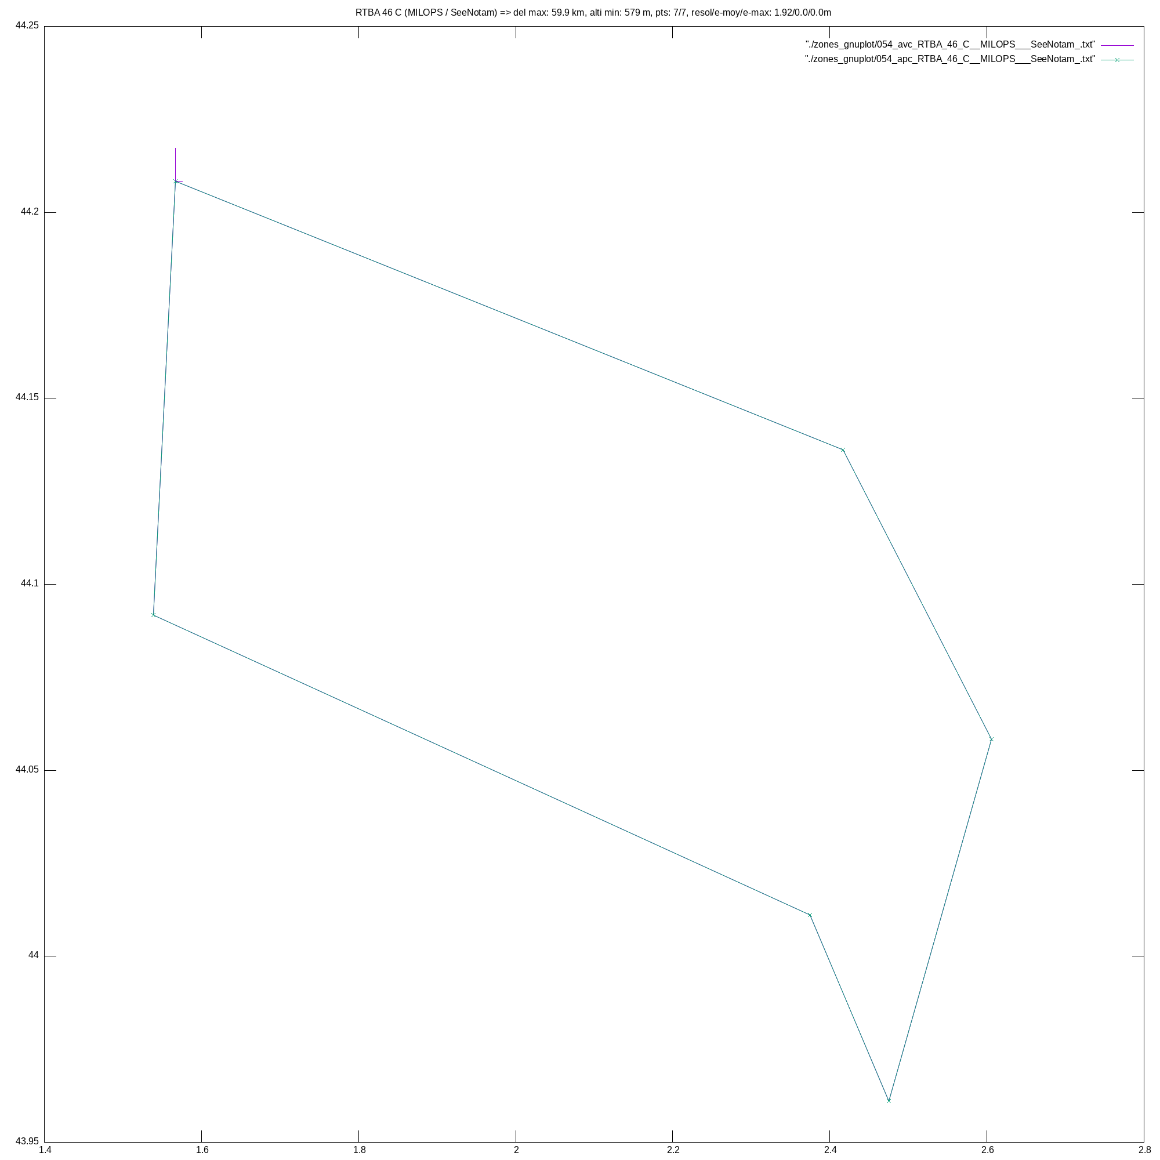
CompZoneAerienne/zones_gnuplot/054_png_RTBA_46_C__MILOPS___SeeNotam_.png
