gitberthe/BertheVario/CompZoneAerienne/zones_gnuplot/055_png_RTBA_589_B__MILOPS___SeeNotam_.png

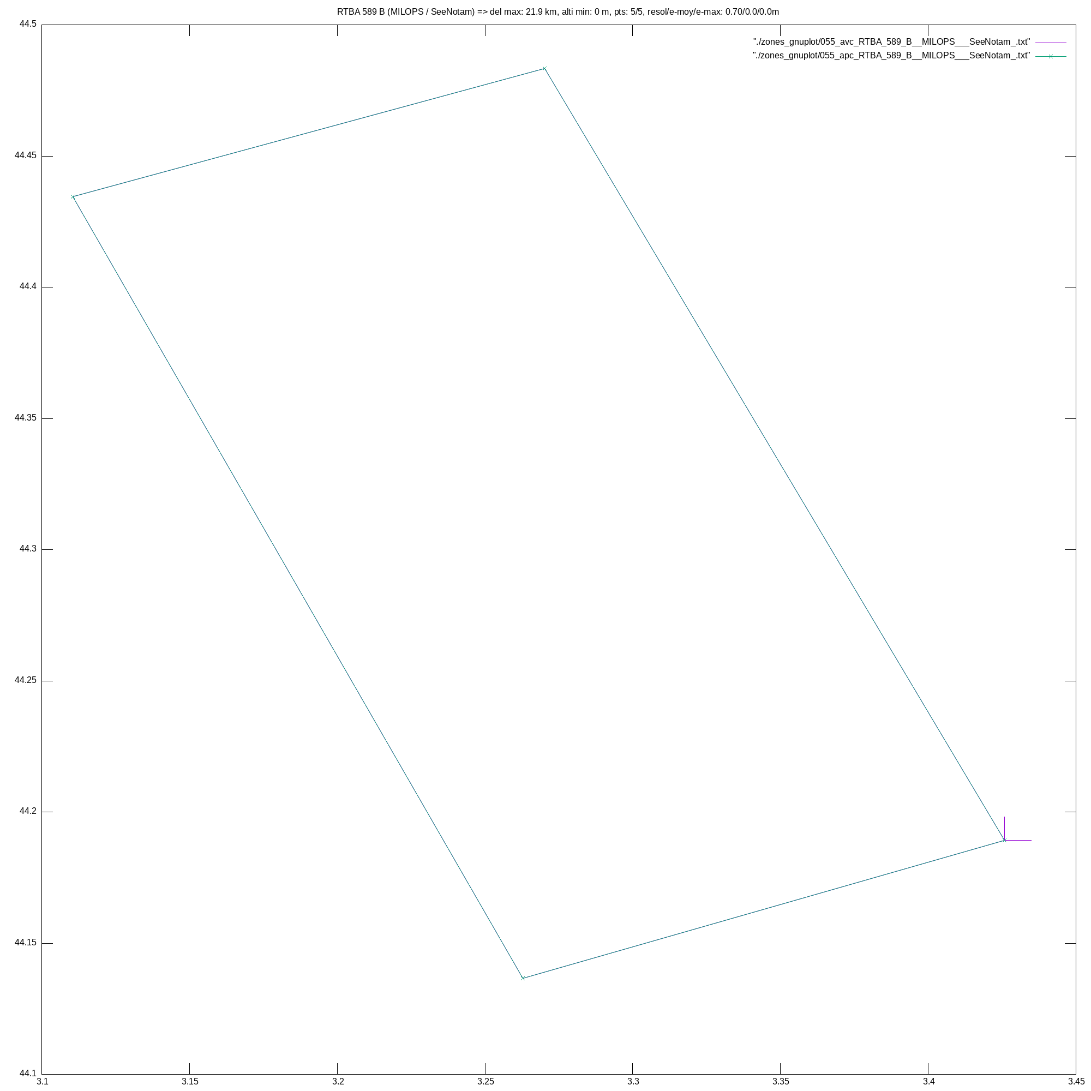
CompZoneAerienne/zones_gnuplot/055_png_RTBA_589_B__MILOPS___SeeNotam_.png
