gitberthe/BertheVario/CompZoneAerienne/zones_gnuplot/056_png_RTBA_589_A__MILOPS___SeeNotam_.png

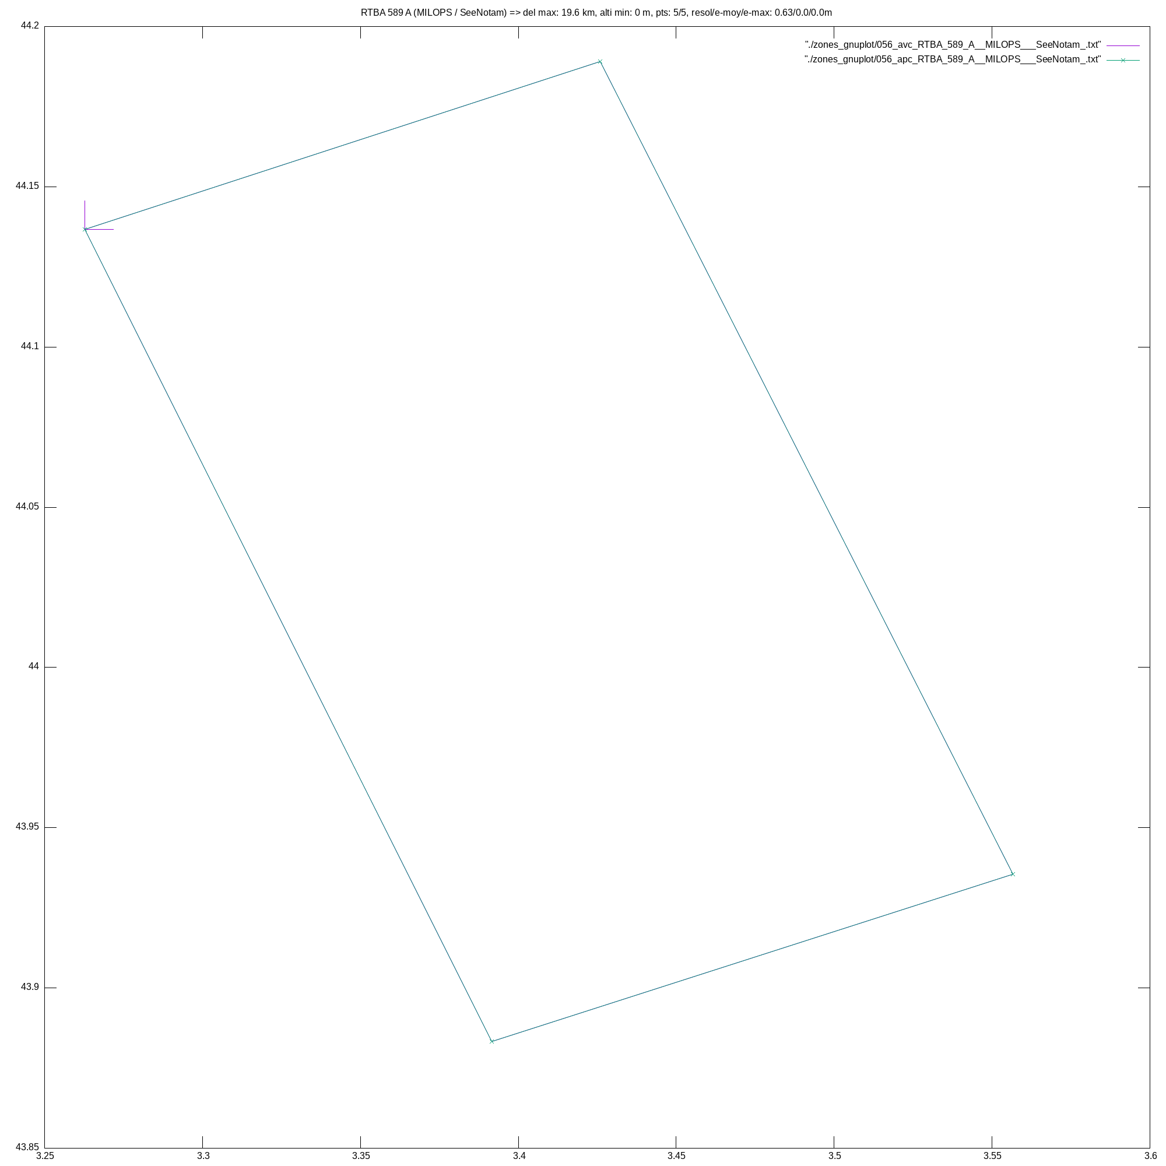
CompZoneAerienne/zones_gnuplot/056_png_RTBA_589_A__MILOPS___SeeNotam_.png
