gitberthe/BertheVario/CompZoneAerienne/zones_gnuplot/057_png_RTBA_193_B__MILOPS___SeeNotam_.png

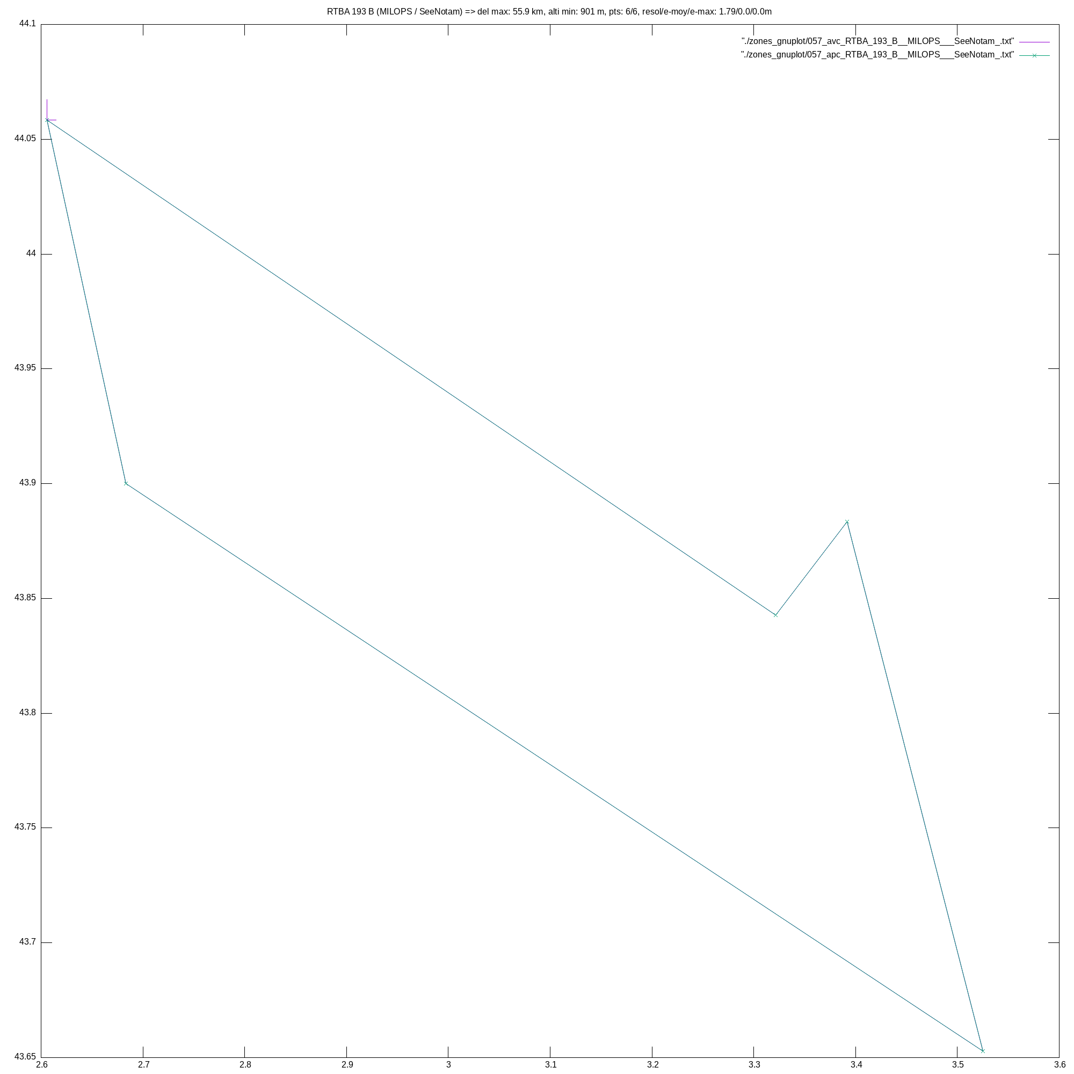
CompZoneAerienne/zones_gnuplot/057_png_RTBA_193_B__MILOPS___SeeNotam_.png
