gitberthe/BertheVario/CompZoneAerienne/zones_gnuplot/058_png_RTBA_193_A__MILOPS___SeeNotam_.png

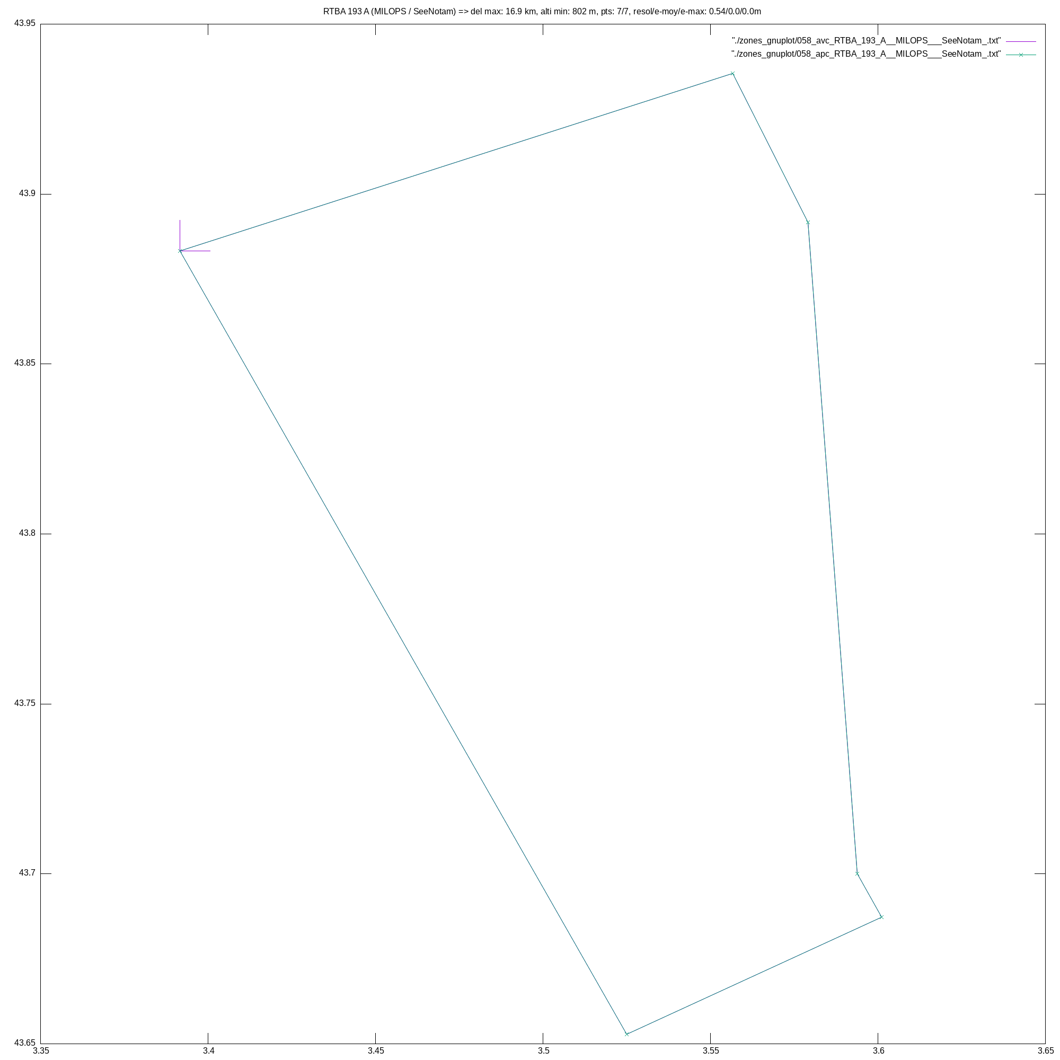
CompZoneAerienne/zones_gnuplot/058_png_RTBA_193_A__MILOPS___SeeNotam_.png
