gitberthe/BertheVario/CompZoneAerienne/zones_gnuplot/059_png_RTBA_46_N2__MILOPS___SeeNotam_.png

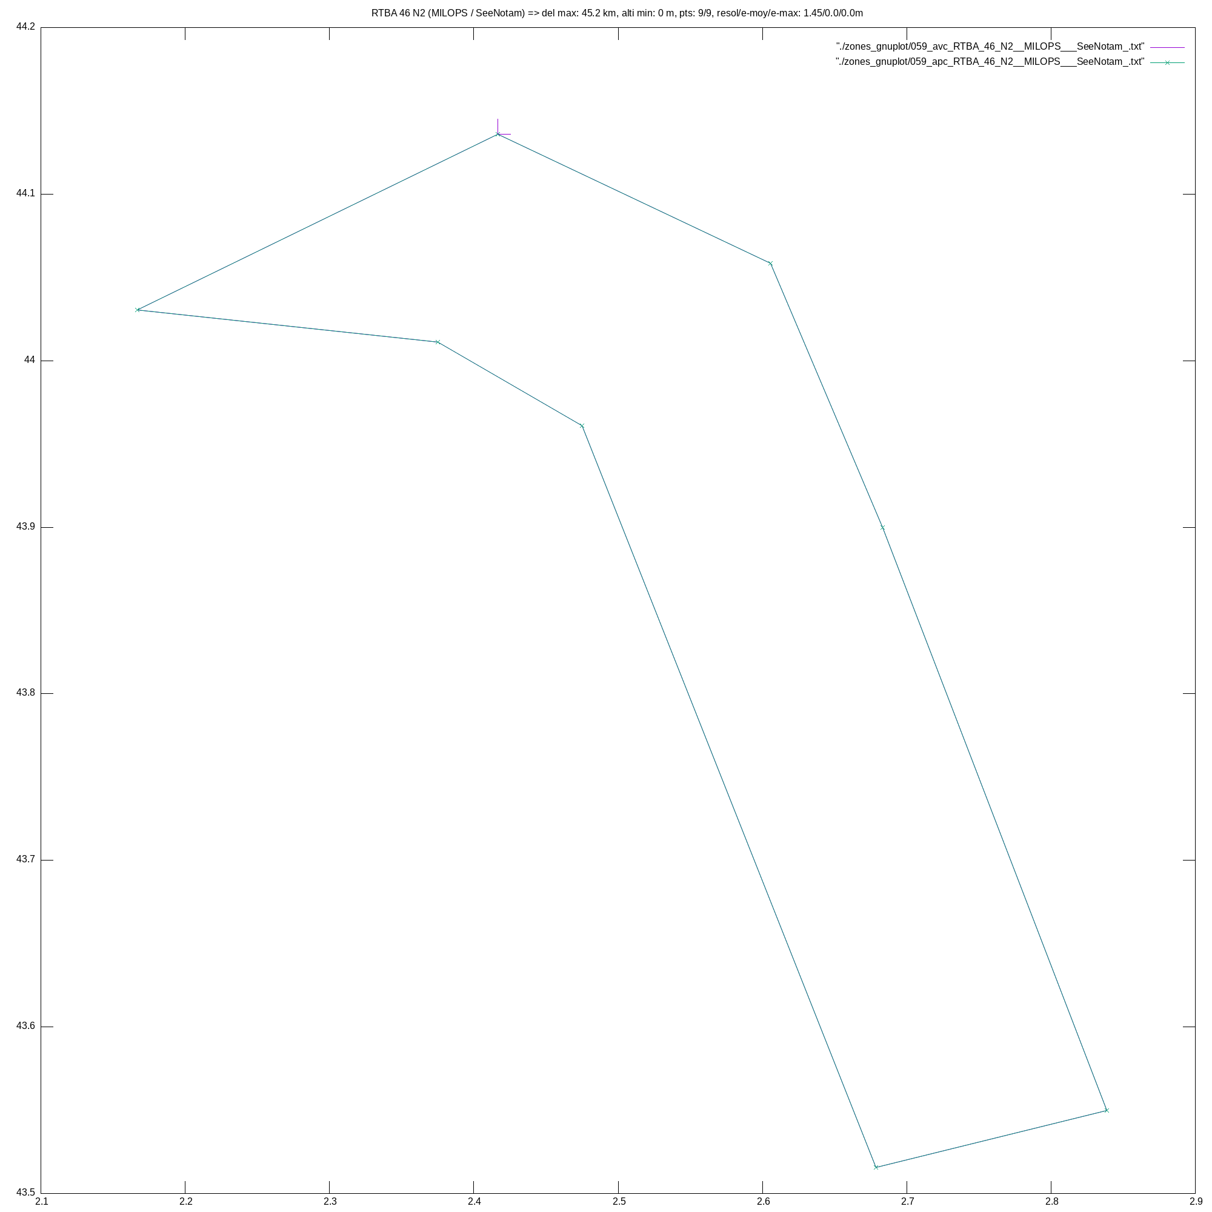
CompZoneAerienne/zones_gnuplot/059_png_RTBA_46_N2__MILOPS___SeeNotam_.png
