gitberthe/BertheVario/CompZoneAerienne/zones_gnuplot/060_png_RTBA_46_D__MILOPS___SeeNotam_.png

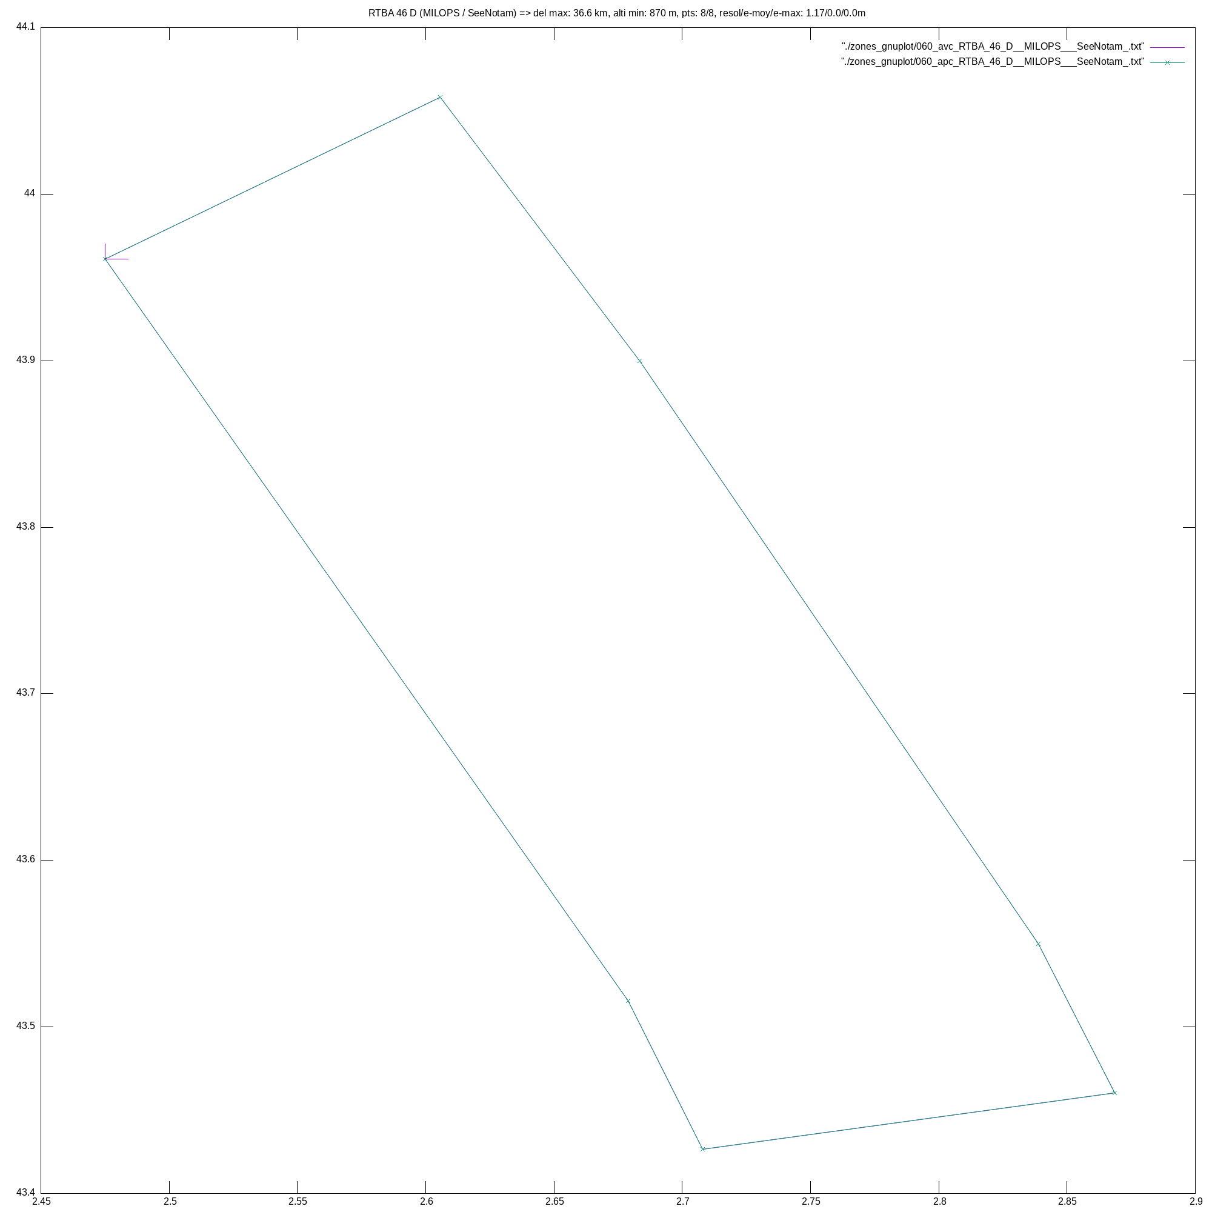
CompZoneAerienne/zones_gnuplot/060_png_RTBA_46_D__MILOPS___SeeNotam_.png
