gitberthe/BertheVario/CompZoneAerienne/zones_gnuplot/061_png_RTBA_590_A__MILOPS___SeeNotam_.png

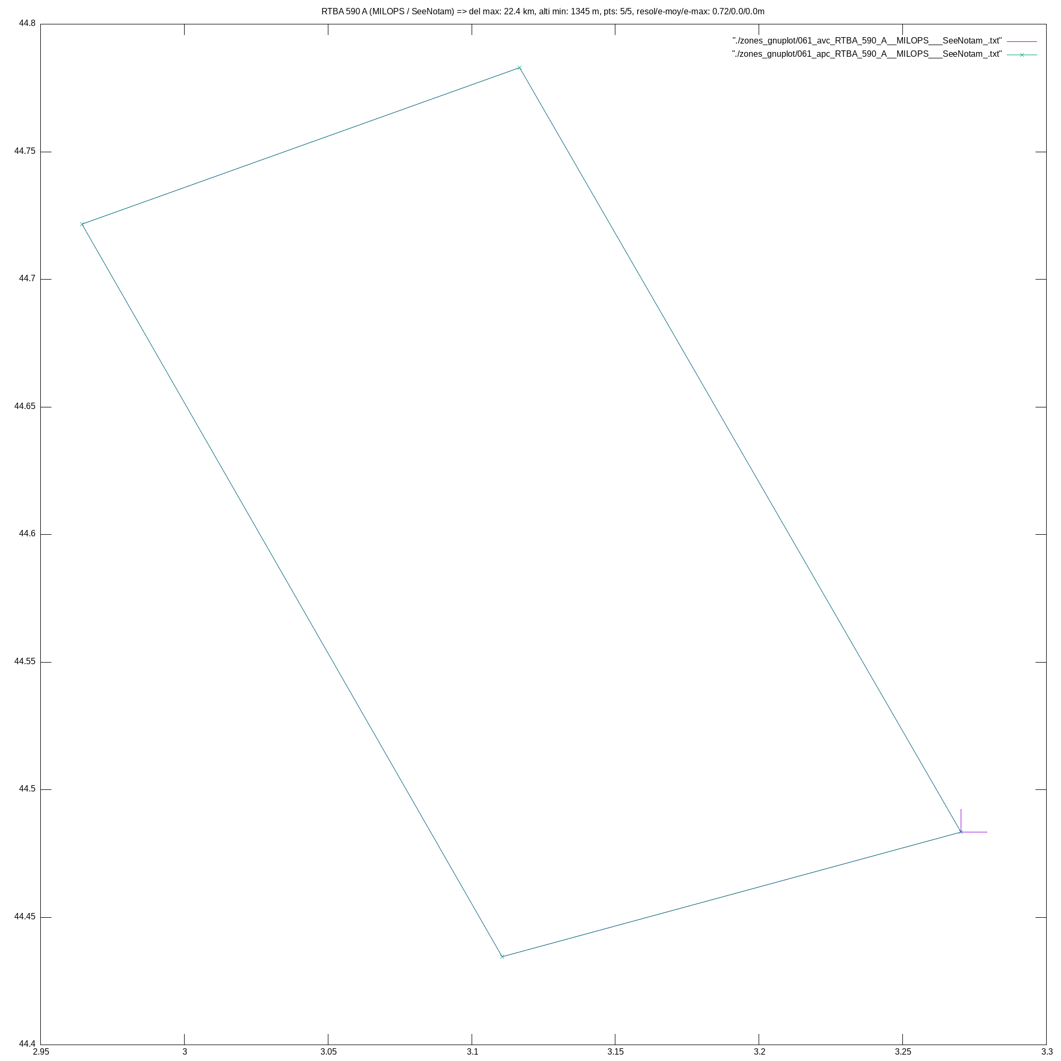
CompZoneAerienne/zones_gnuplot/061_png_RTBA_590_A__MILOPS___SeeNotam_.png
