gitberthe/BertheVario/CompZoneAerienne/zones_gnuplot/062_png_CTA_TOULOUSE_1.png

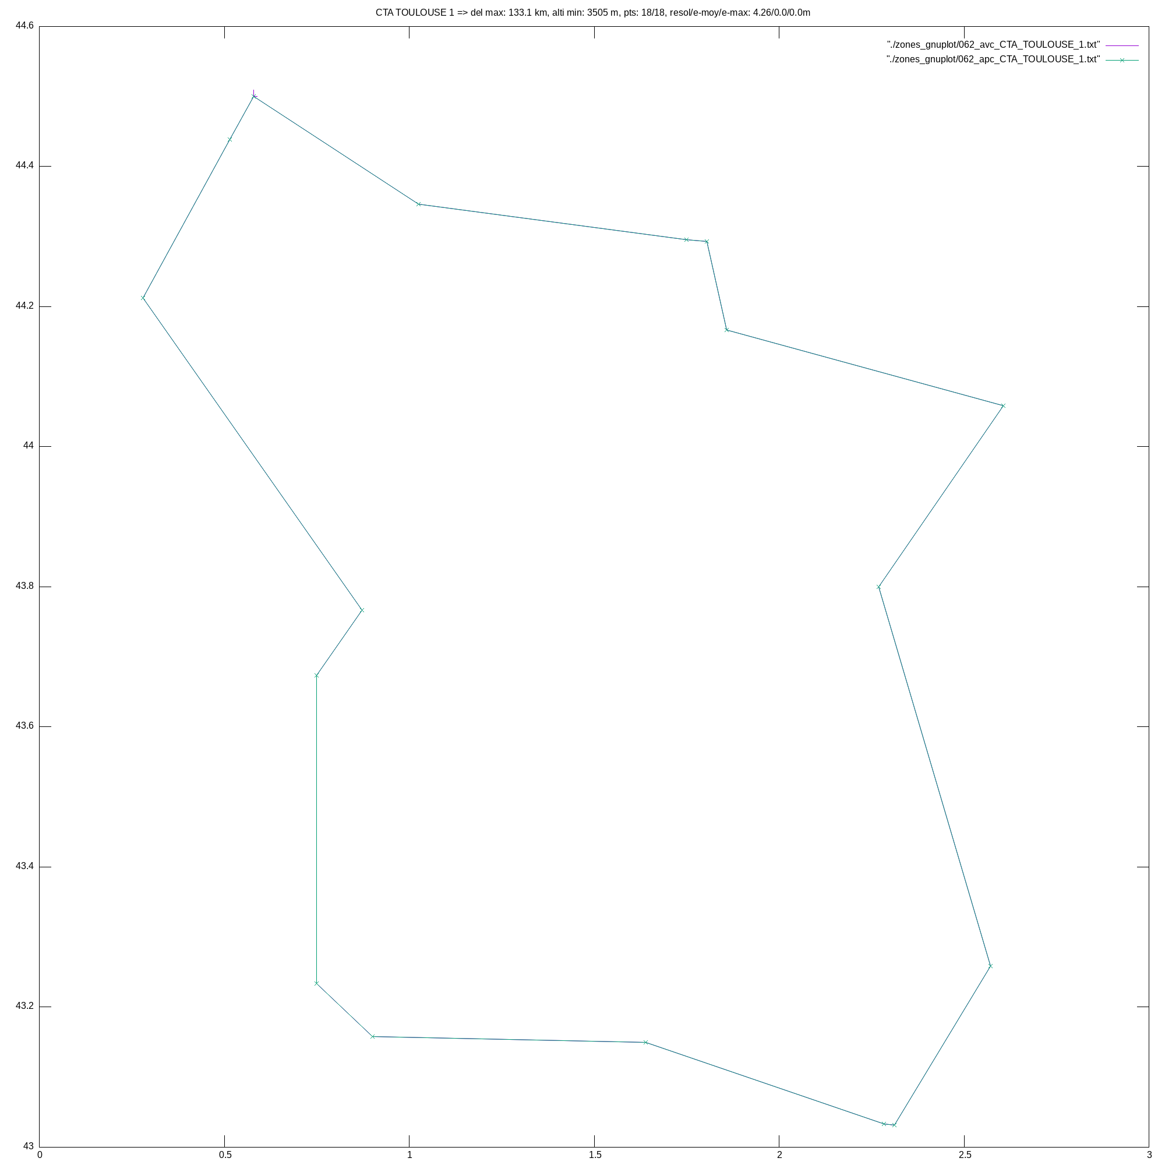
CompZoneAerienne/zones_gnuplot/062_png_CTA_TOULOUSE_1.png
