gitberthe/BertheVario/CompZoneAerienne/zones_gnuplot/063_png_CTA_TOULOUSE_2.png

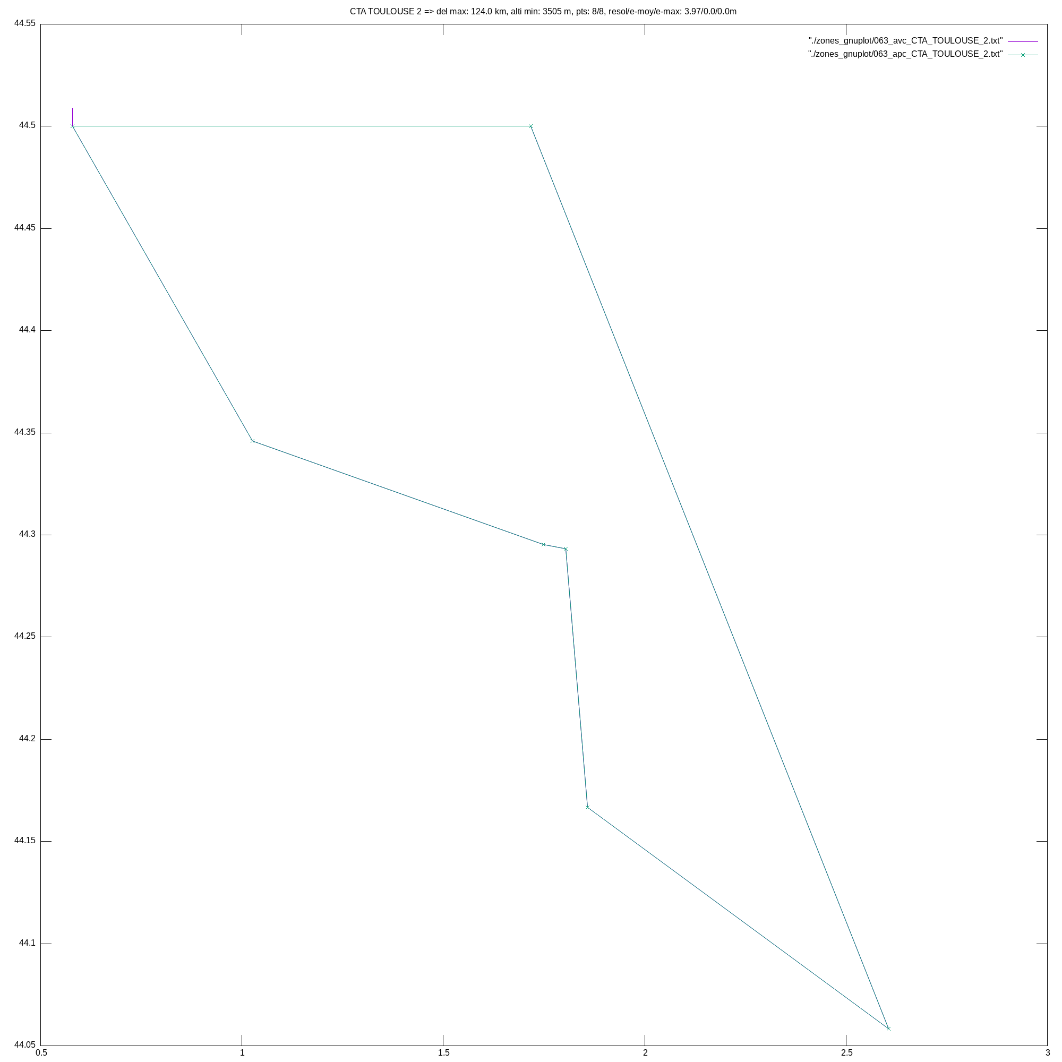
CompZoneAerienne/zones_gnuplot/063_png_CTA_TOULOUSE_2.png
