gitberthe/BertheVario/CompZoneAerienne/zones_gnuplot/065_png_R_169_A.png

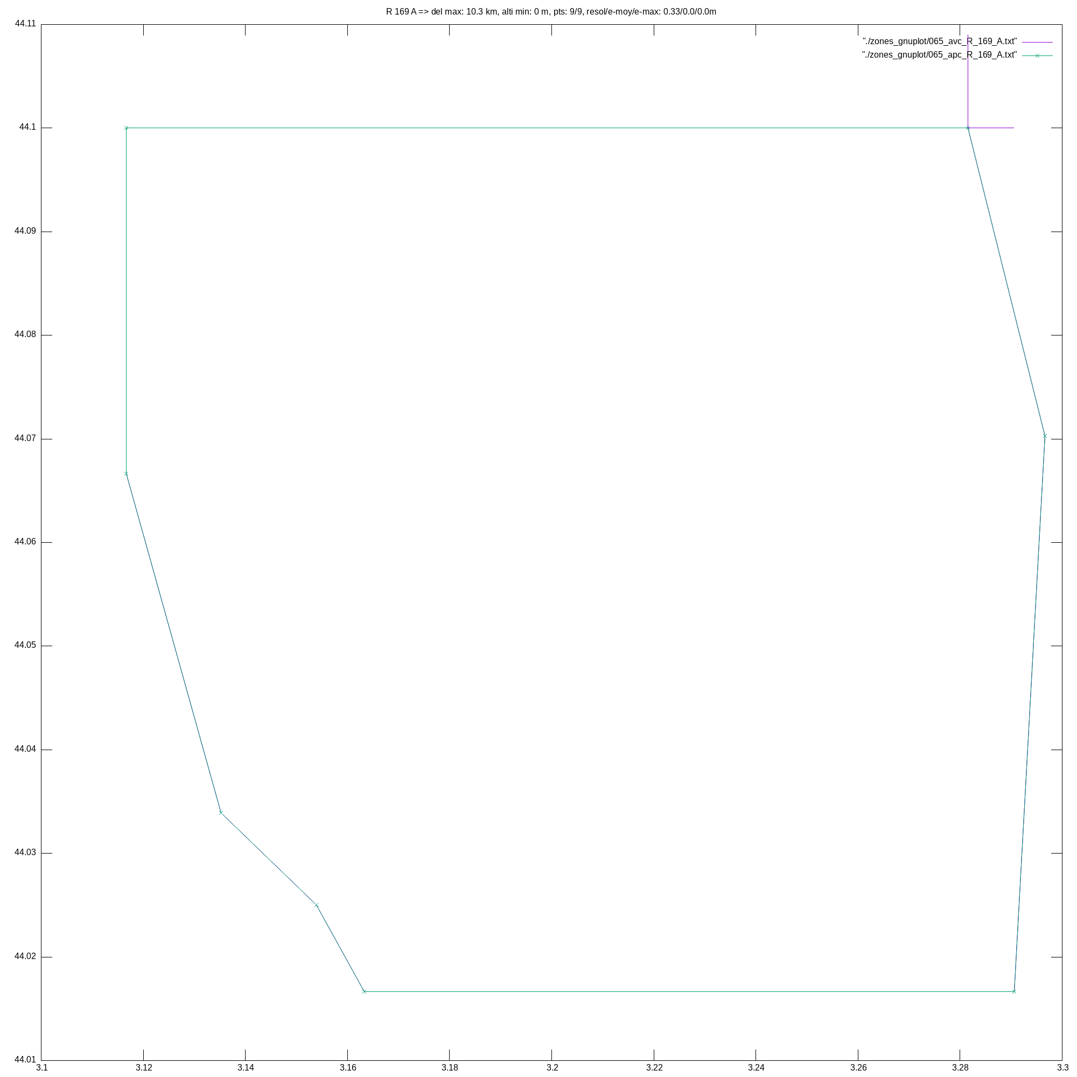
CompZoneAerienne/zones_gnuplot/065_png_R_169_A.png
