gitberthe/BertheVario/CompZoneAerienne/zones_gnuplot/067_png_CTA_MARSEILLE_5.png

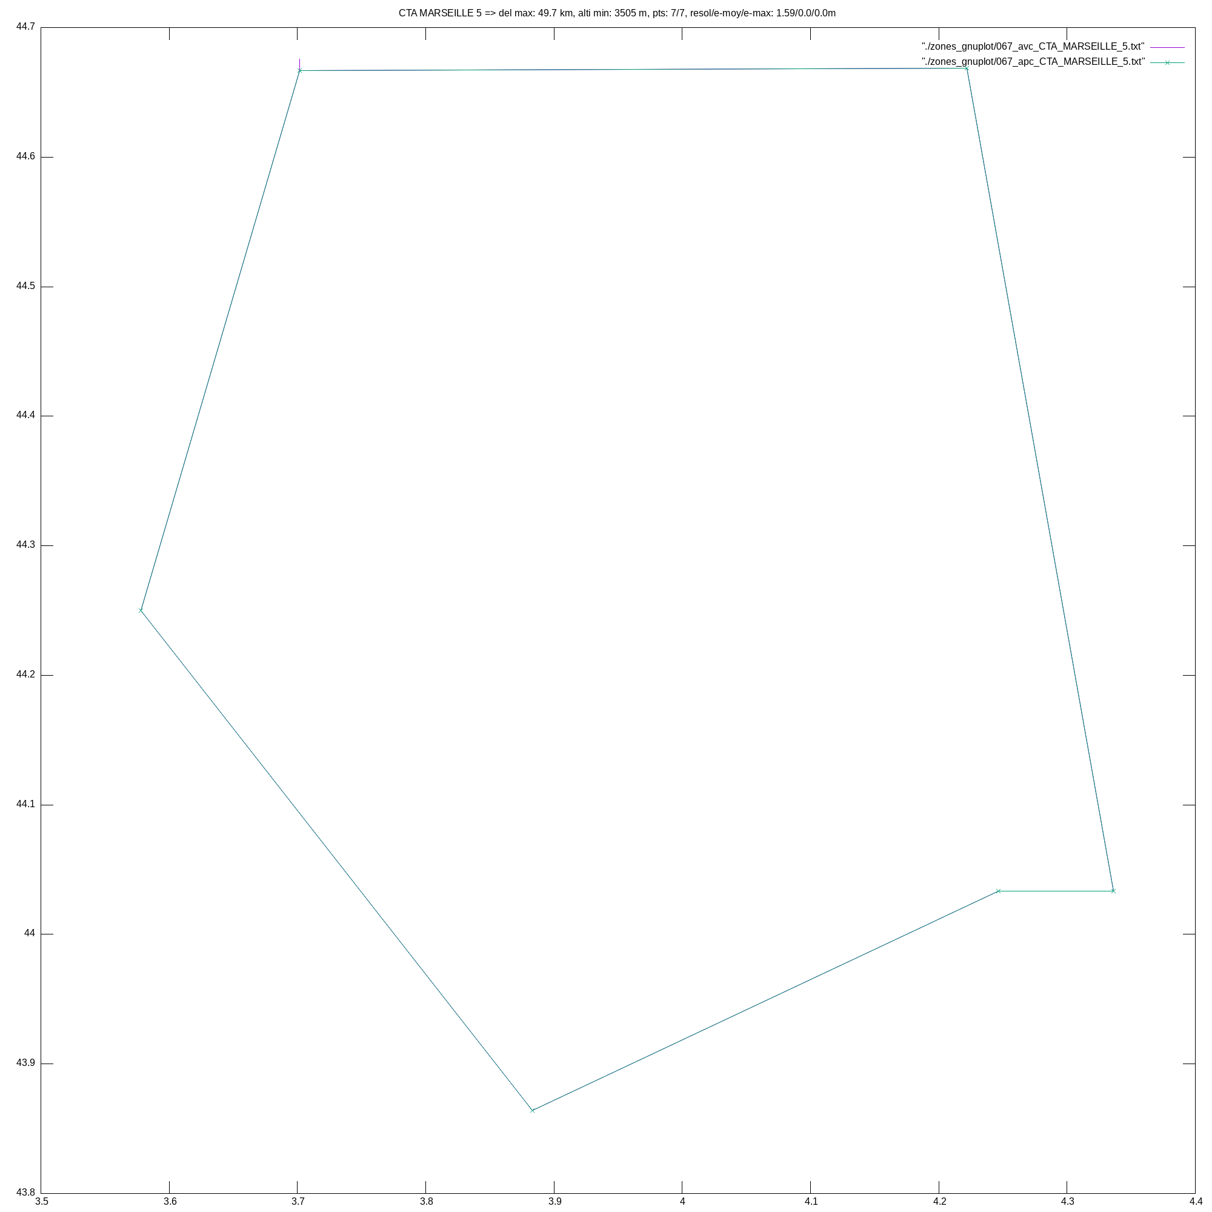
CompZoneAerienne/zones_gnuplot/067_png_CTA_MARSEILLE_5.png
