gitberthe/BertheVario/CompZoneAerienne/zones_gnuplot/068_png_TMA_MONTPELLIER_5_App_130.855_.png

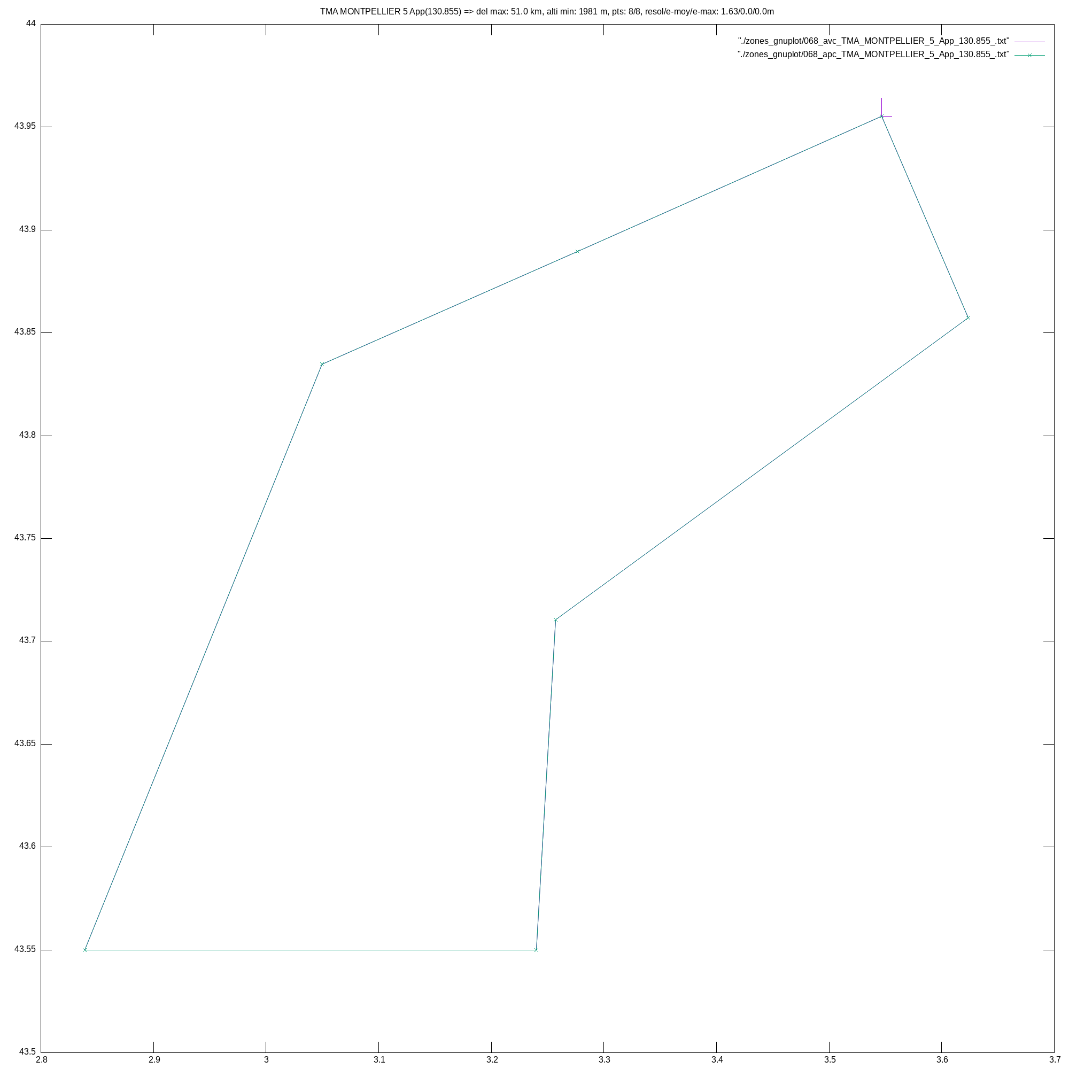
CompZoneAerienne/zones_gnuplot/068_png_TMA_MONTPELLIER_5_App_130.855_.png
