gitberthe/BertheVario/CompZoneAerienne/zones_gnuplot/069_png_TMA_MONTPELLIER_6_App_130.855_.png

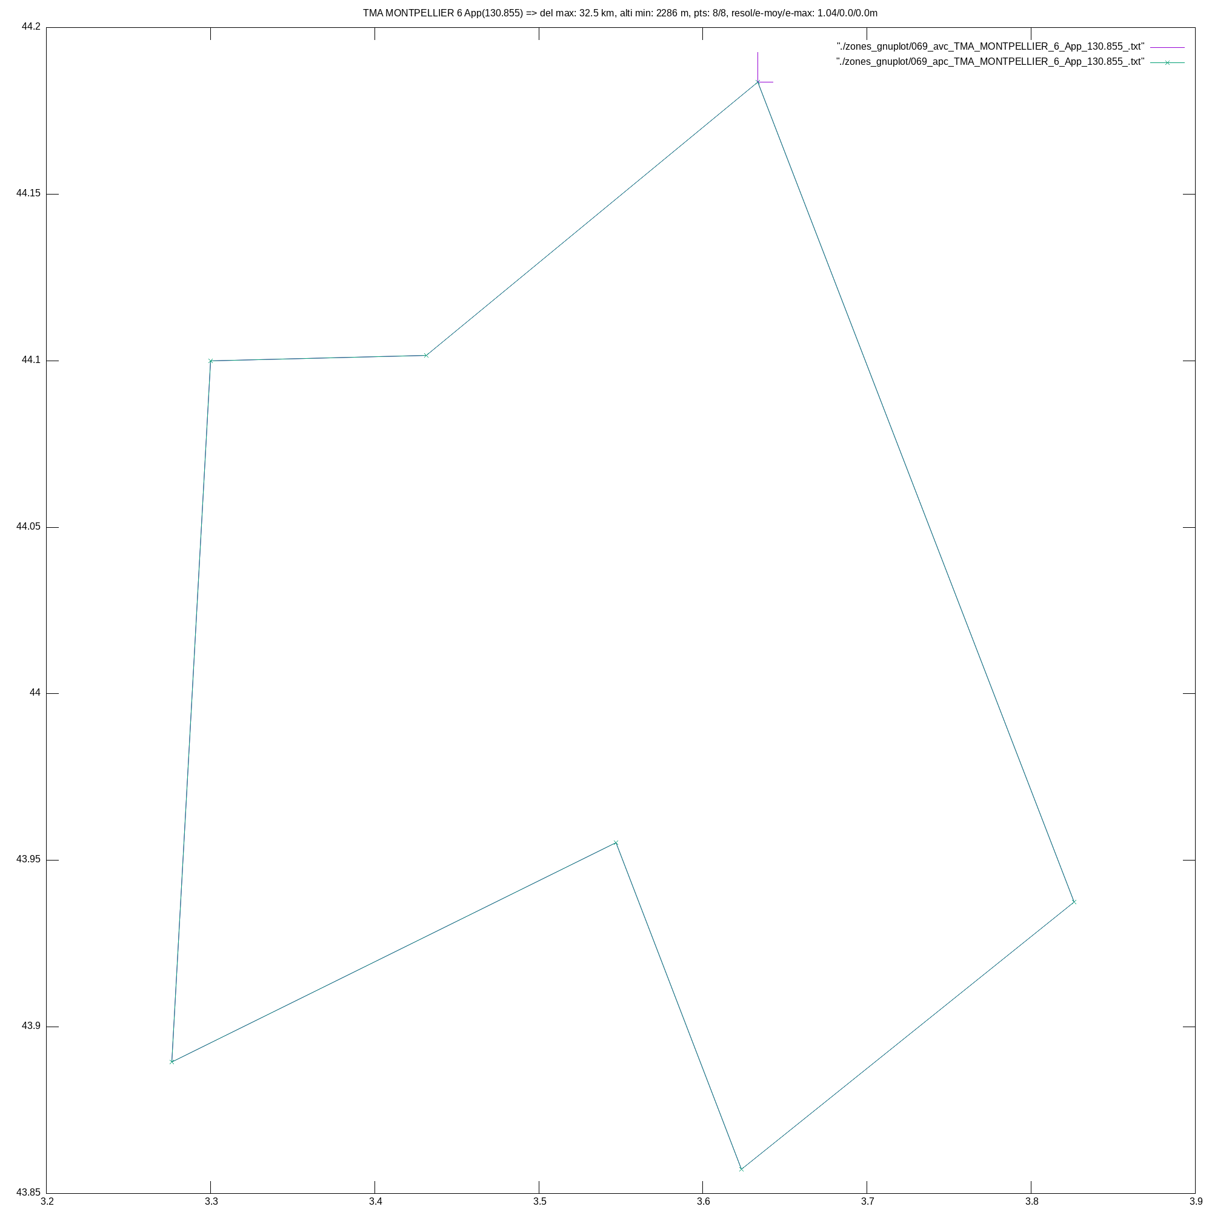
CompZoneAerienne/zones_gnuplot/069_png_TMA_MONTPELLIER_6_App_130.855_.png
