gitberthe/BertheVario/CompZoneAerienne/zones_gnuplot/070_png_CTA_CLERMONT_2.png

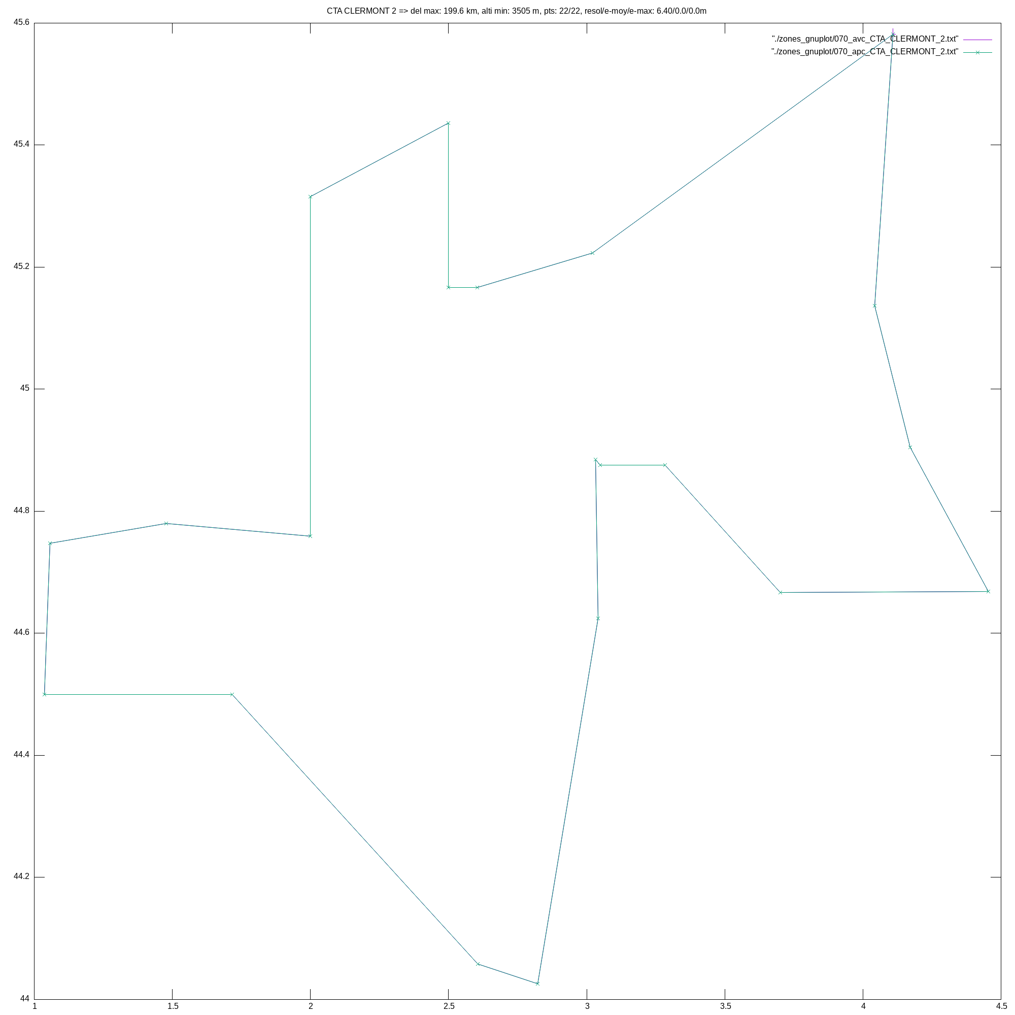
CompZoneAerienne/zones_gnuplot/070_png_CTA_CLERMONT_2.png
