gitberthe/BertheVario/CompZoneAerienne/zones_gnuplot/071_png_PROTECT_ParcCevennes_Combe_Centre__1000m_sol__.png

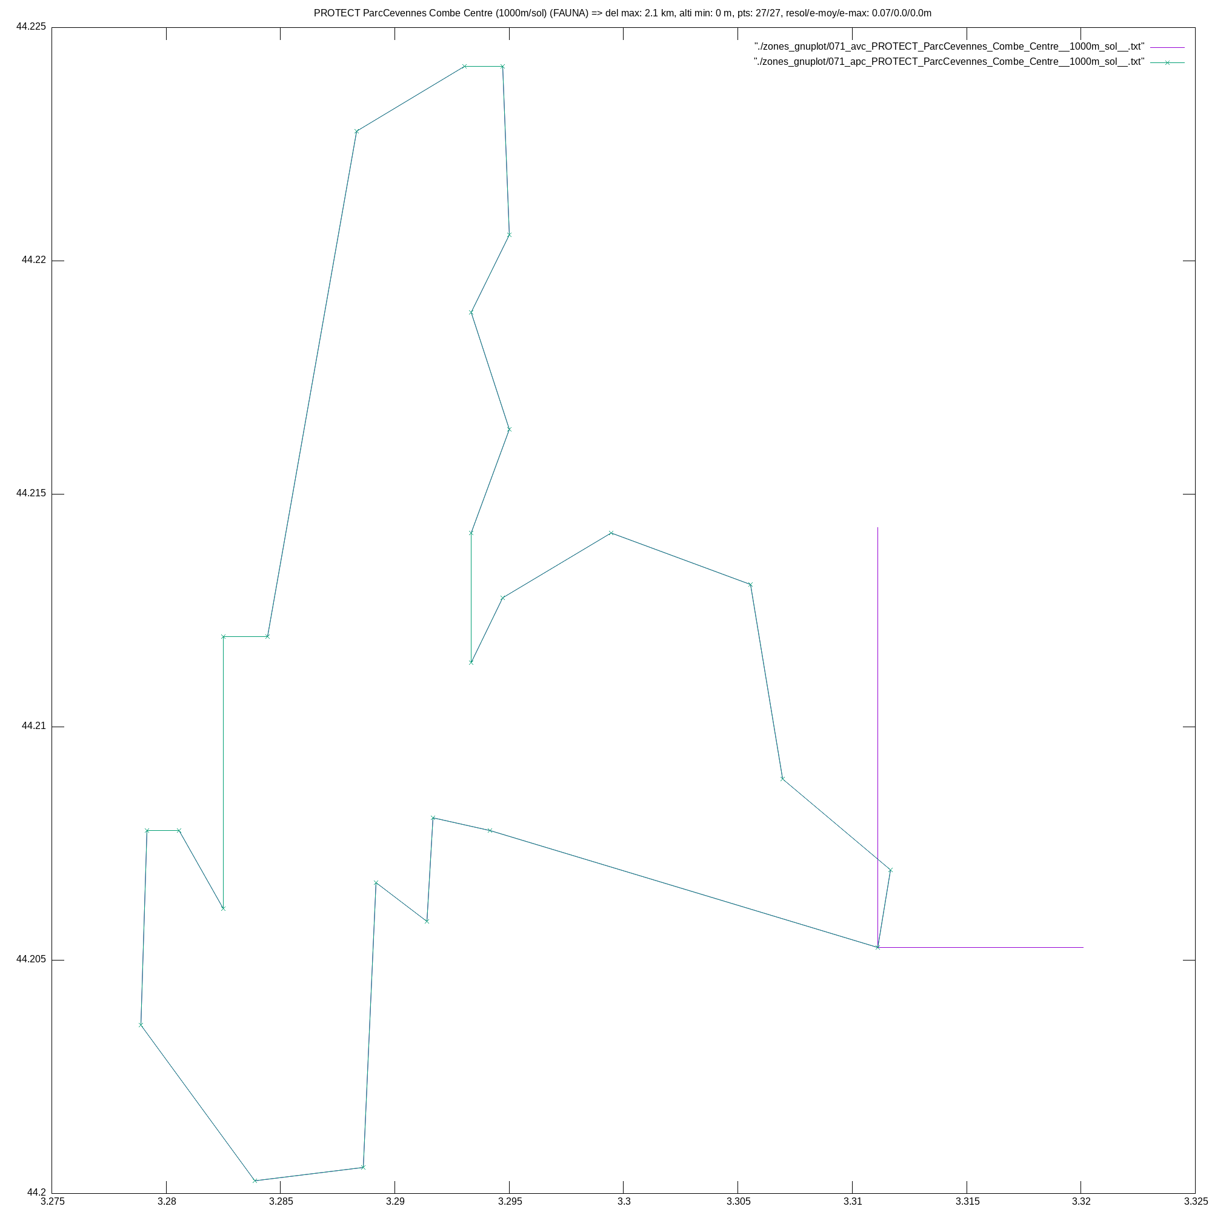
CompZoneAerienne/zones_gnuplot/071_png_PROTECT_ParcCevennes_Combe_Centre__1000m_sol__.png
