gitberthe/BertheVario/CompZoneAerienne/zones_gnuplot/072_png_PROTECT_Parc_Cevennes_Tarn_Est__1000m_sol_.png

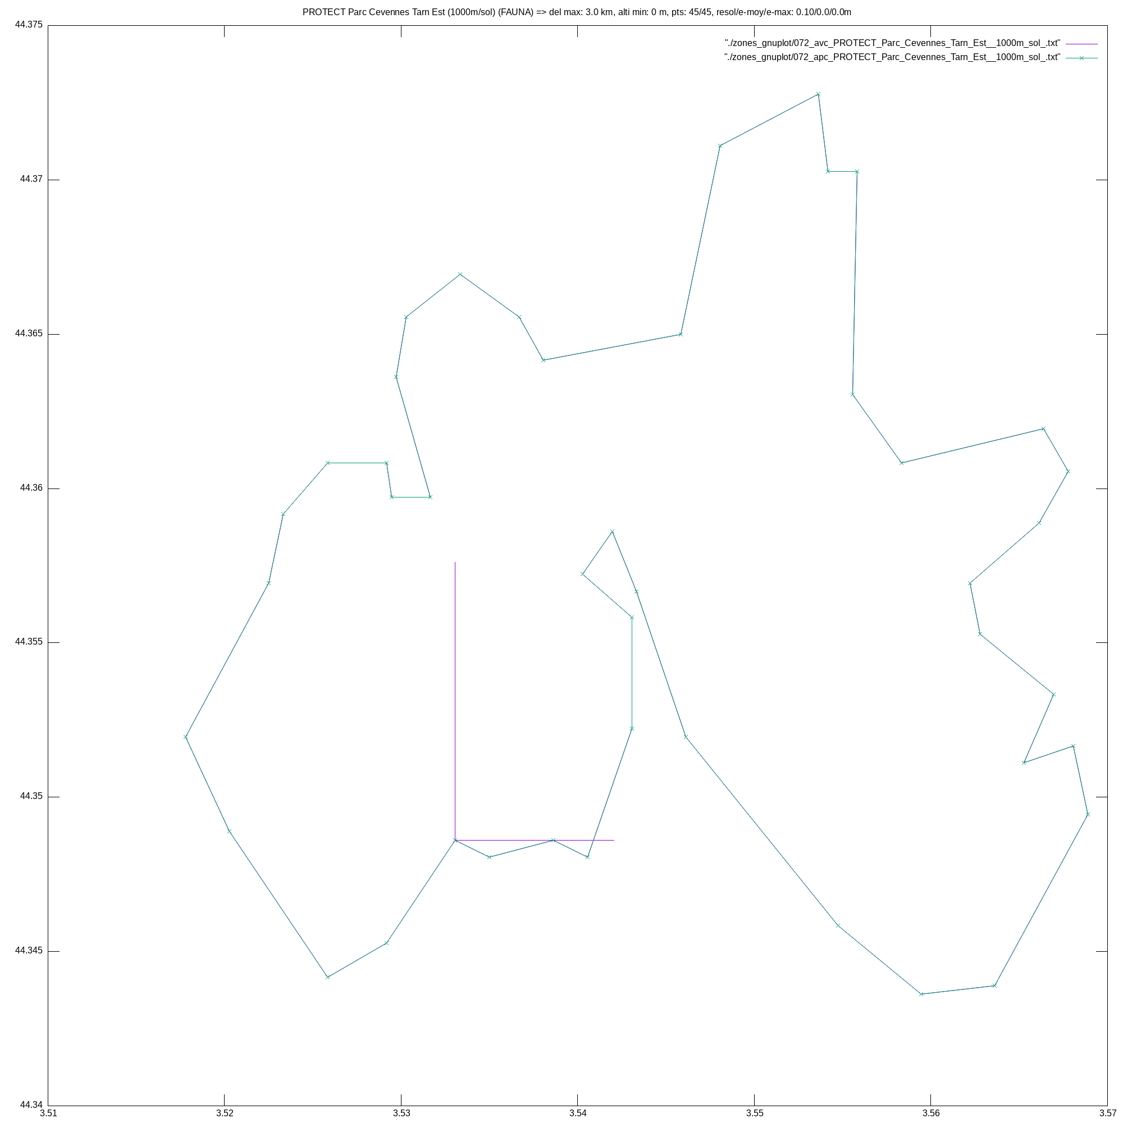
CompZoneAerienne/zones_gnuplot/072_png_PROTECT_Parc_Cevennes_Tarn_Est__1000m_sol_.png
