gitberthe/BertheVario/CompZoneAerienne/zones_gnuplot/073_png_R_242_Siv_124.050_.png

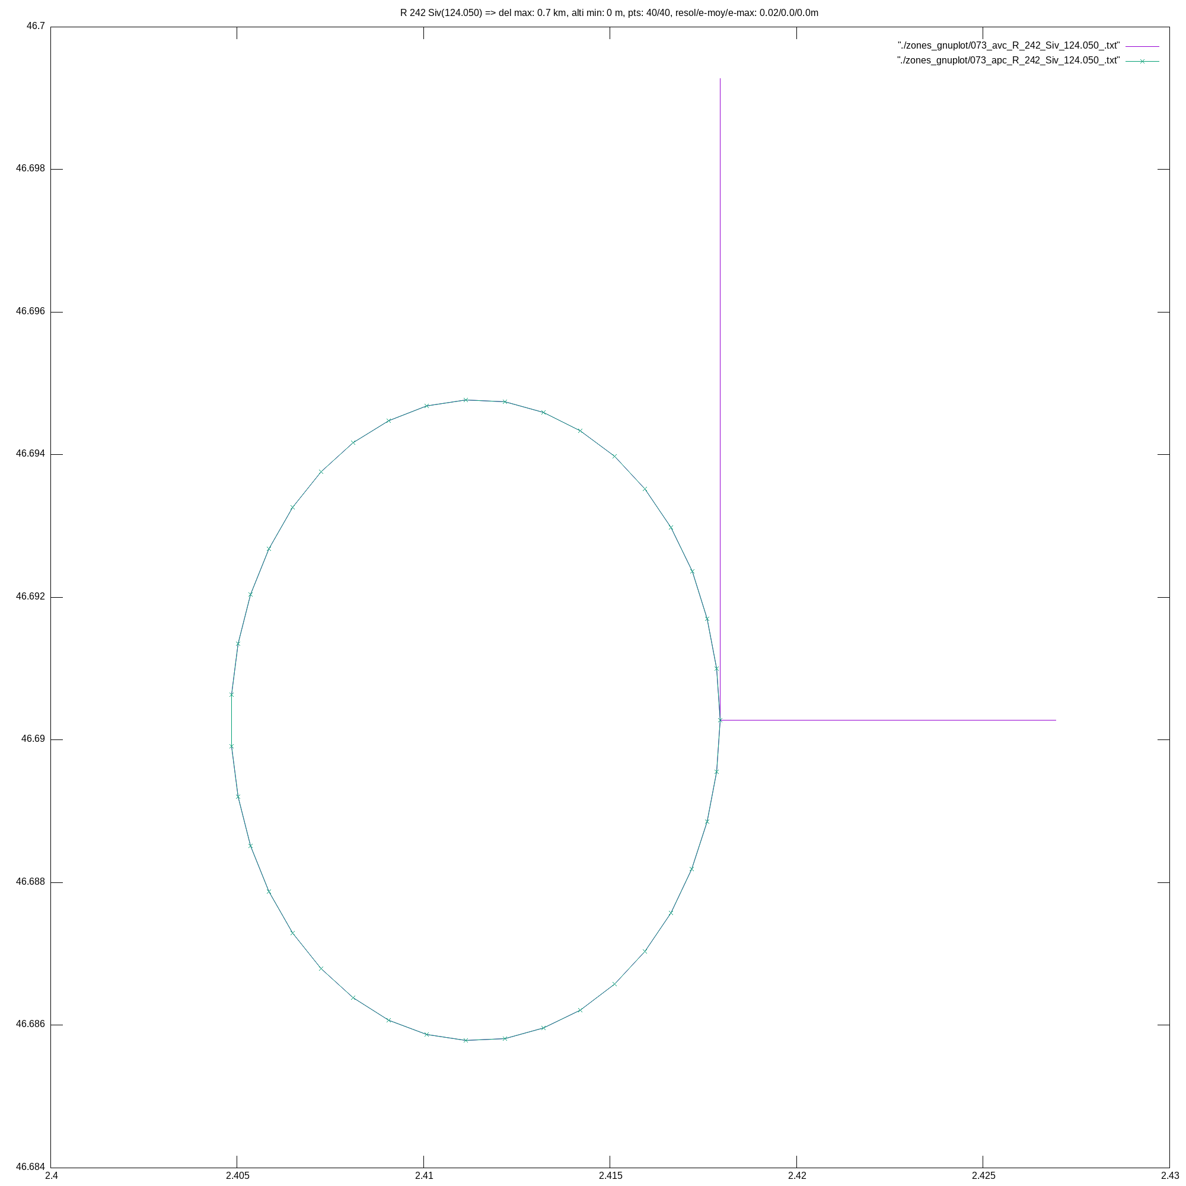
CompZoneAerienne/zones_gnuplot/073_png_R_242_Siv_124.050_.png
