gitberthe/BertheVario/CompZoneAerienne/zones_gnuplot/074_png_TMA_AVORD_1.1_App_119.700_.png

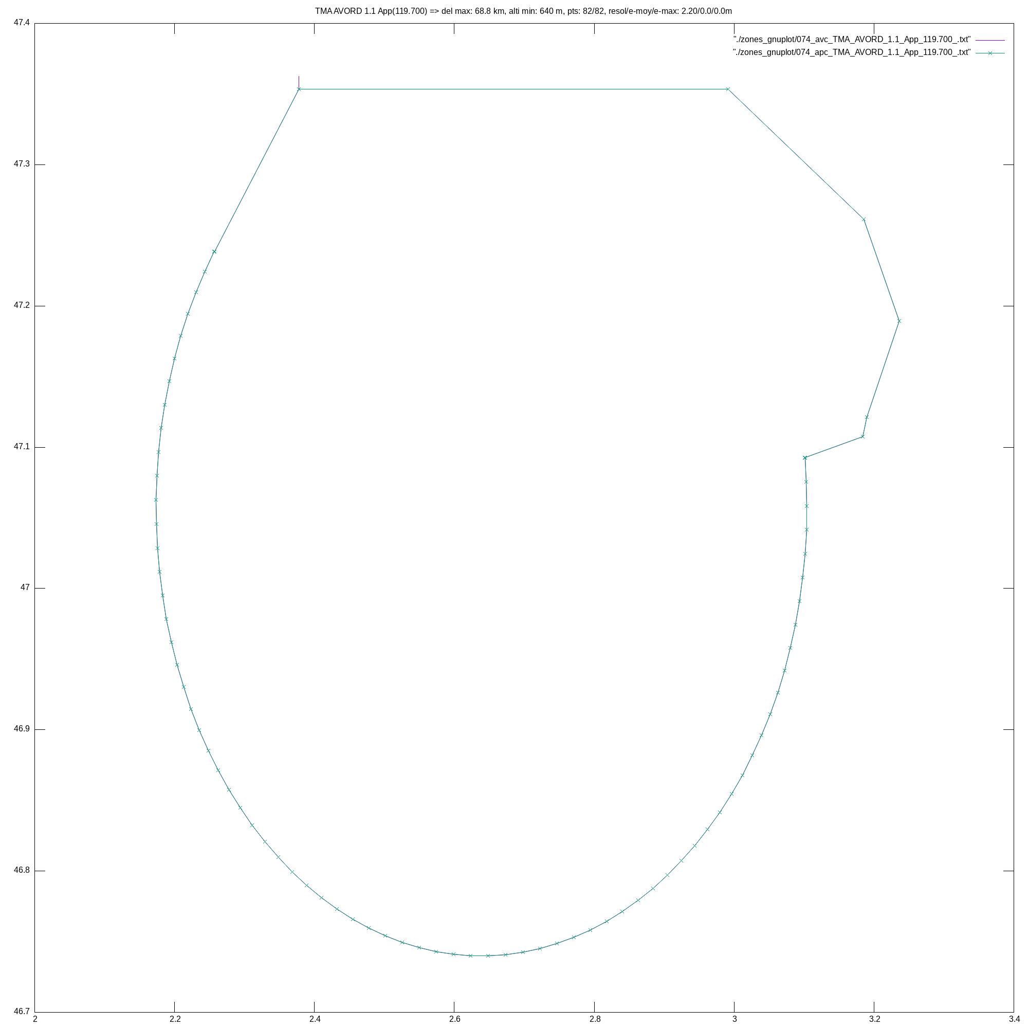
CompZoneAerienne/zones_gnuplot/074_png_TMA_AVORD_1.1_App_119.700_.png
