gitberthe/BertheVario/CompZoneAerienne/zones_gnuplot/075_png_RTBA_145_A__MILOPS___SeeNotam_.png

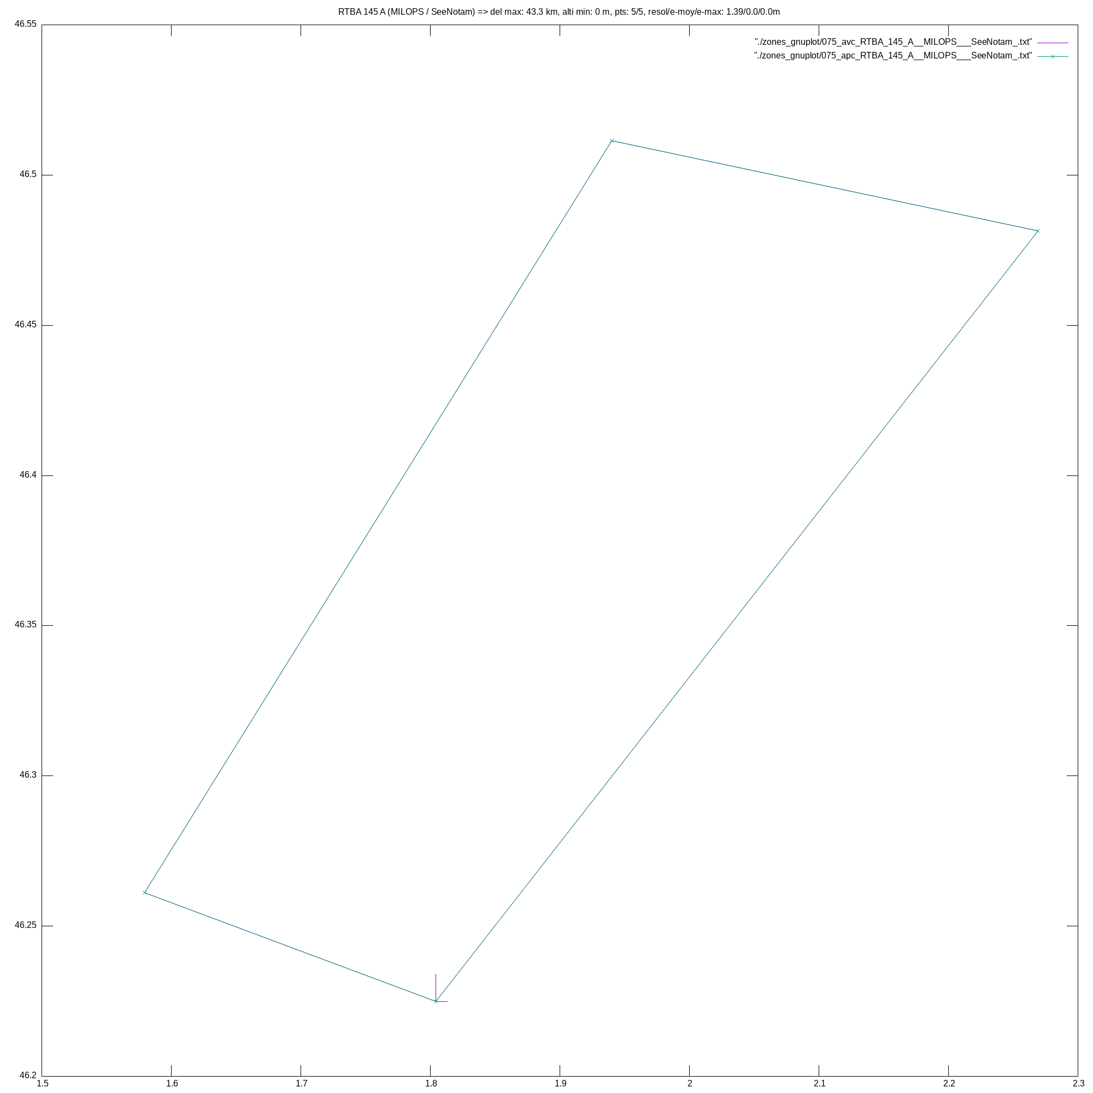
CompZoneAerienne/zones_gnuplot/075_png_RTBA_145_A__MILOPS___SeeNotam_.png
