gitberthe/BertheVario/CompZoneAerienne/zones_gnuplot/076_png_RTBA_145_B__MILOPS___SeeNotam_.png

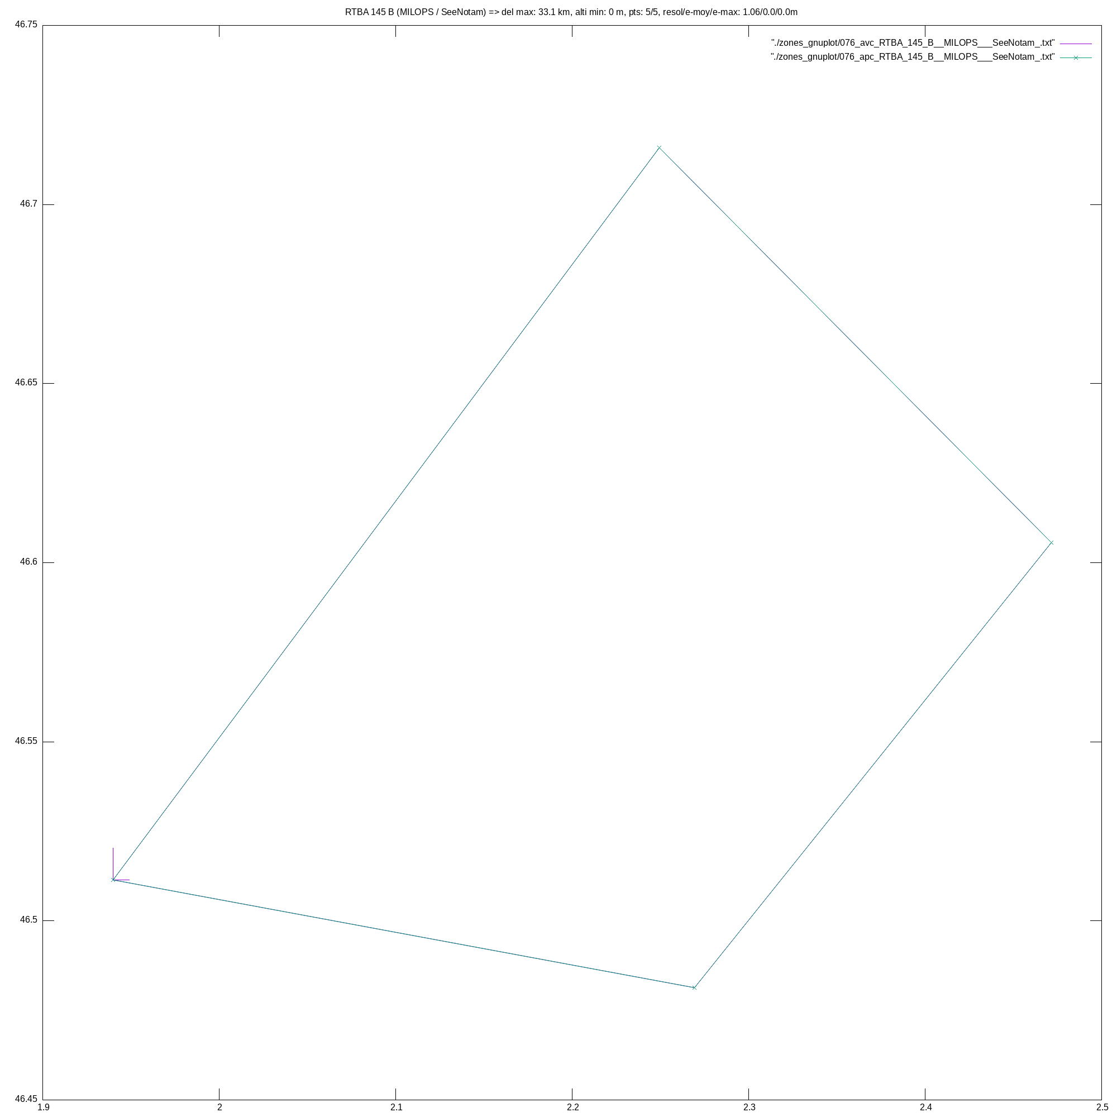
CompZoneAerienne/zones_gnuplot/076_png_RTBA_145_B__MILOPS___SeeNotam_.png
