gitberthe/BertheVario/CompZoneAerienne/zones_gnuplot/077_png_TMA_CLERMONT_2.1_App_122.225_.png

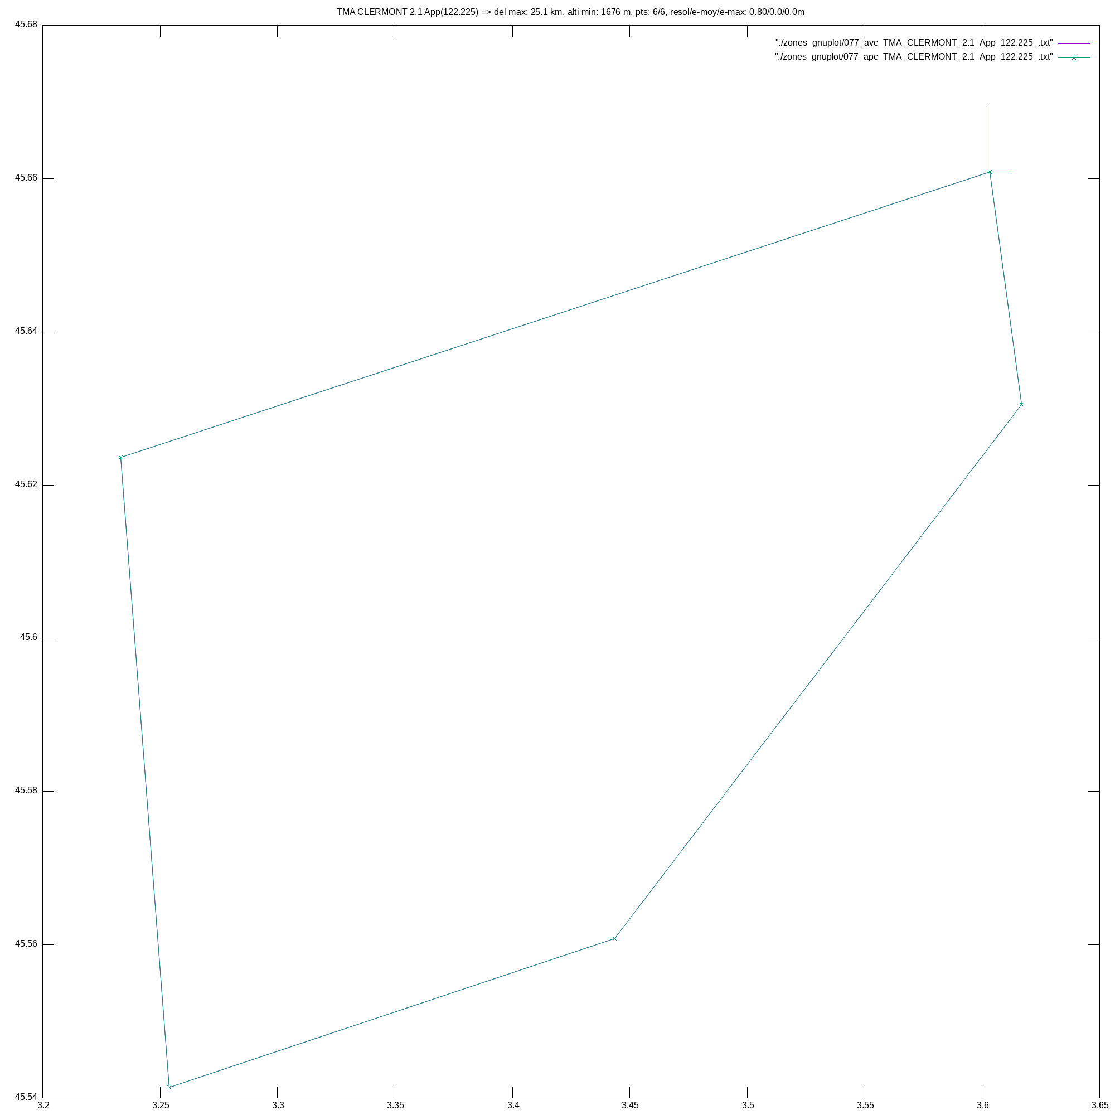
CompZoneAerienne/zones_gnuplot/077_png_TMA_CLERMONT_2.1_App_122.225_.png
