gitberthe/BertheVario/CompZoneAerienne/zones_gnuplot/078_png_R_571.png

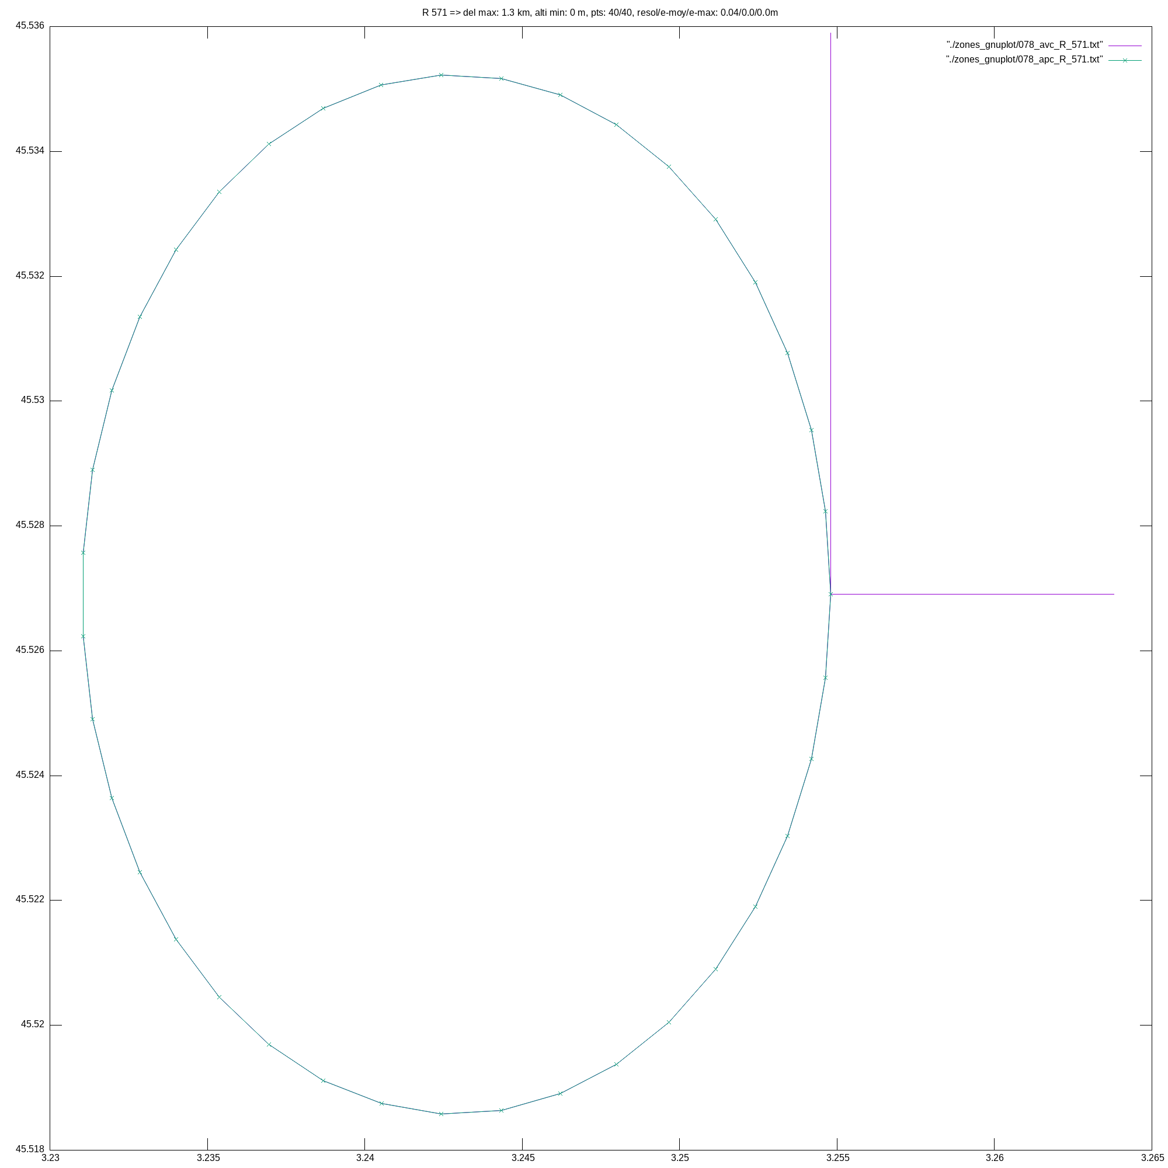
CompZoneAerienne/zones_gnuplot/078_png_R_571.png
