gitberthe/BertheVario/CompZoneAerienne/zones_gnuplot/079_png_R_1274_Upper_7700FT_AMSL-3300FT_AGL_.png

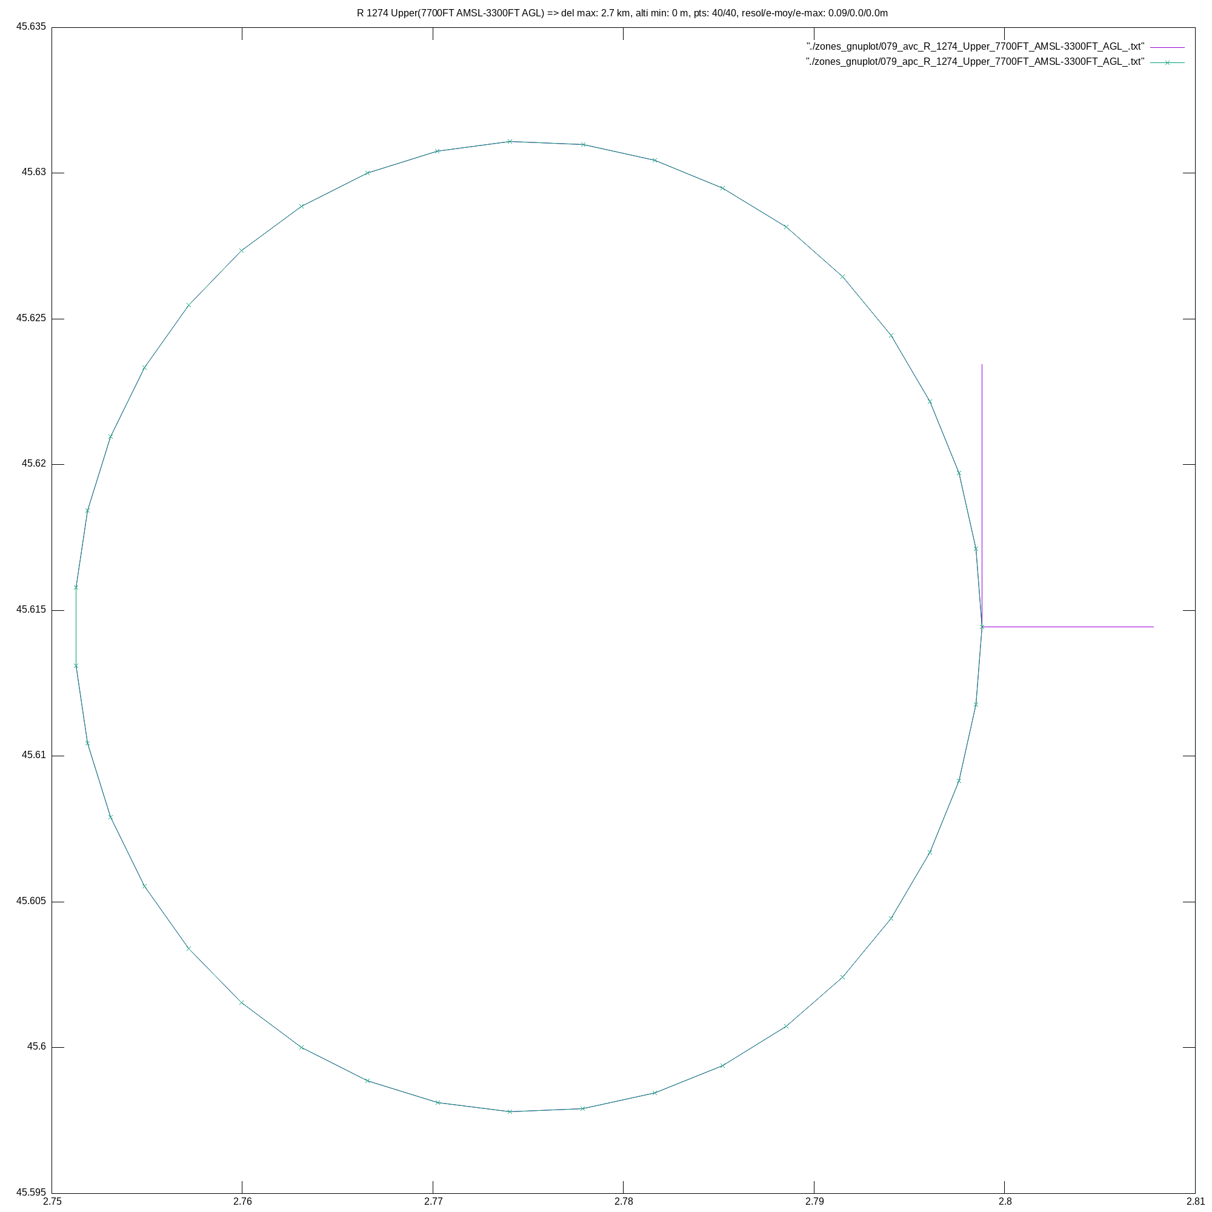
CompZoneAerienne/zones_gnuplot/079_png_R_1274_Upper_7700FT_AMSL-3300FT_AGL_.png
