gitberthe/BertheVario/CompZoneAerienne/zones_gnuplot/080_png_R_20_H3_App_119.7_.png

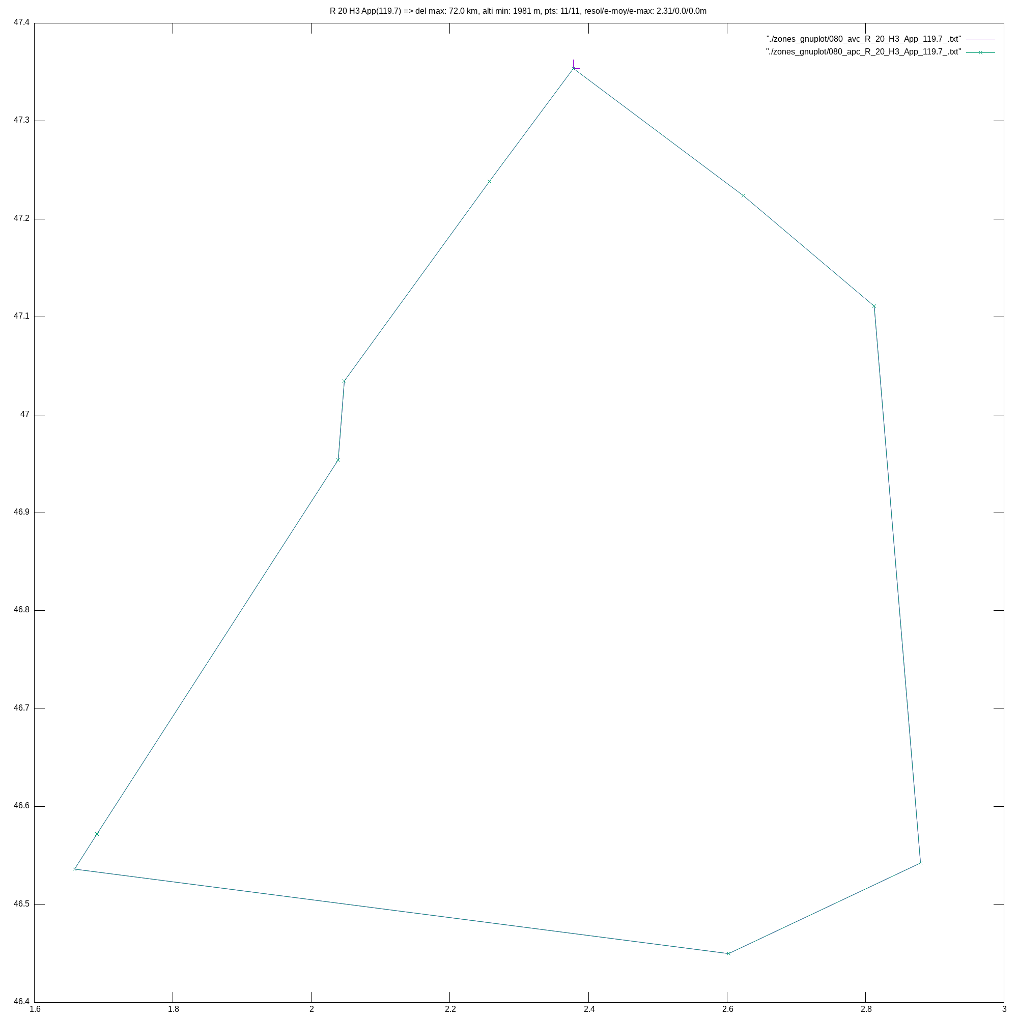
CompZoneAerienne/zones_gnuplot/080_png_R_20_H3_App_119.7_.png
