gitberthe/BertheVario/CompZoneAerienne/zones_gnuplot/082_png_TMA_CLERMONT_6_App_122.225_.png

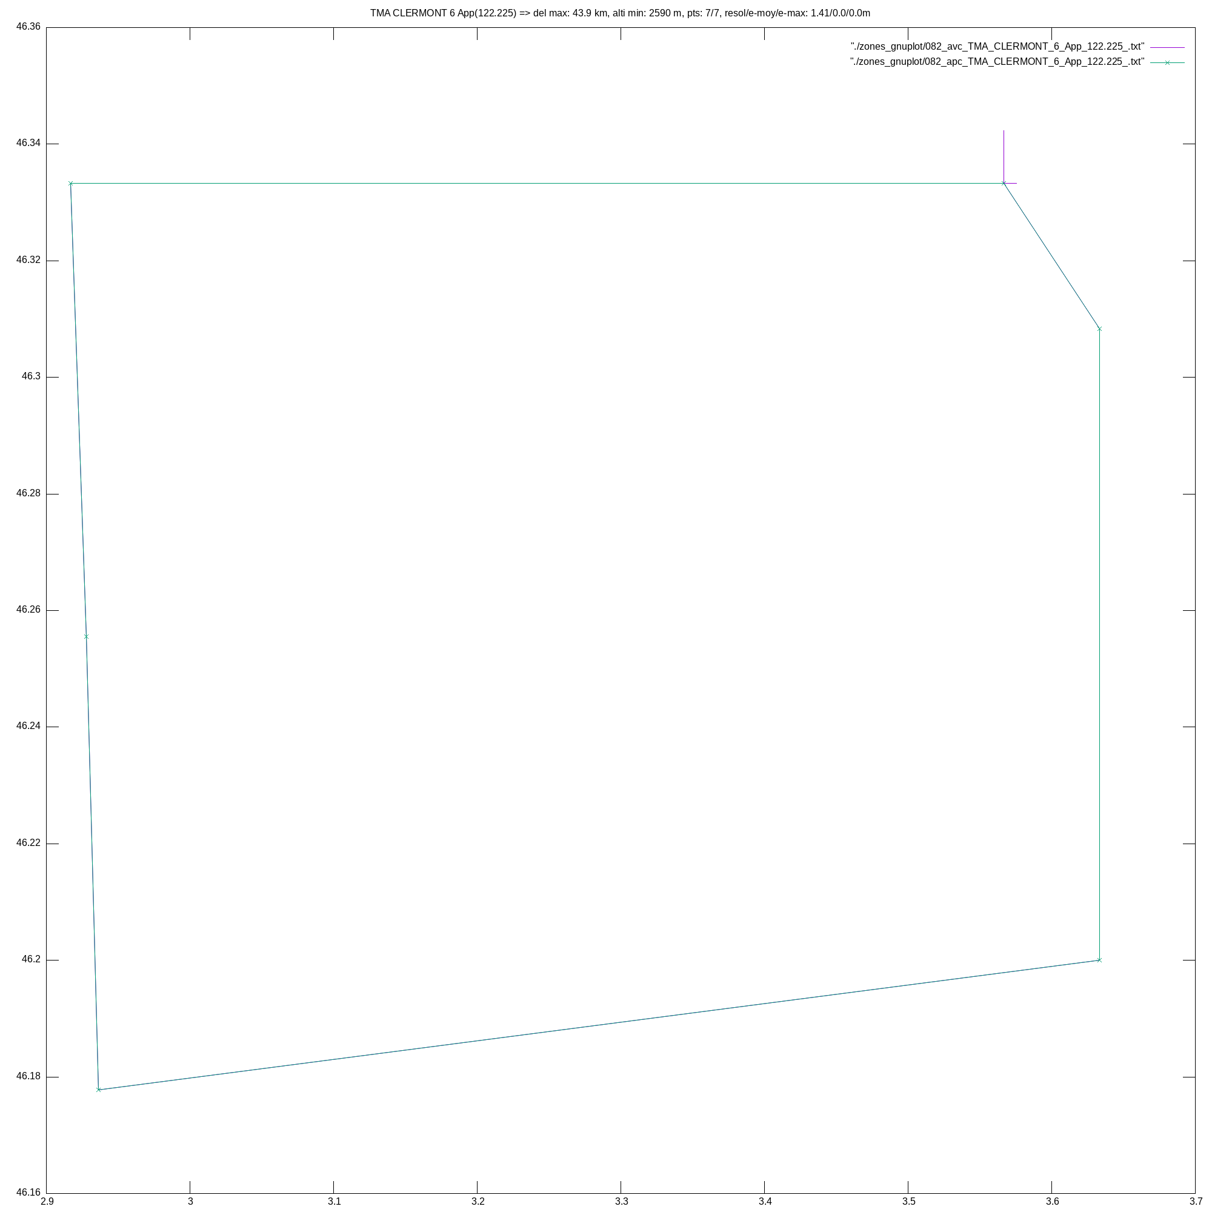
CompZoneAerienne/zones_gnuplot/082_png_TMA_CLERMONT_6_App_122.225_.png
