gitberthe/BertheVario/CompZoneAerienne/zones_gnuplot/083_png_TMA_CLERMONT_4_App_122.225_.png

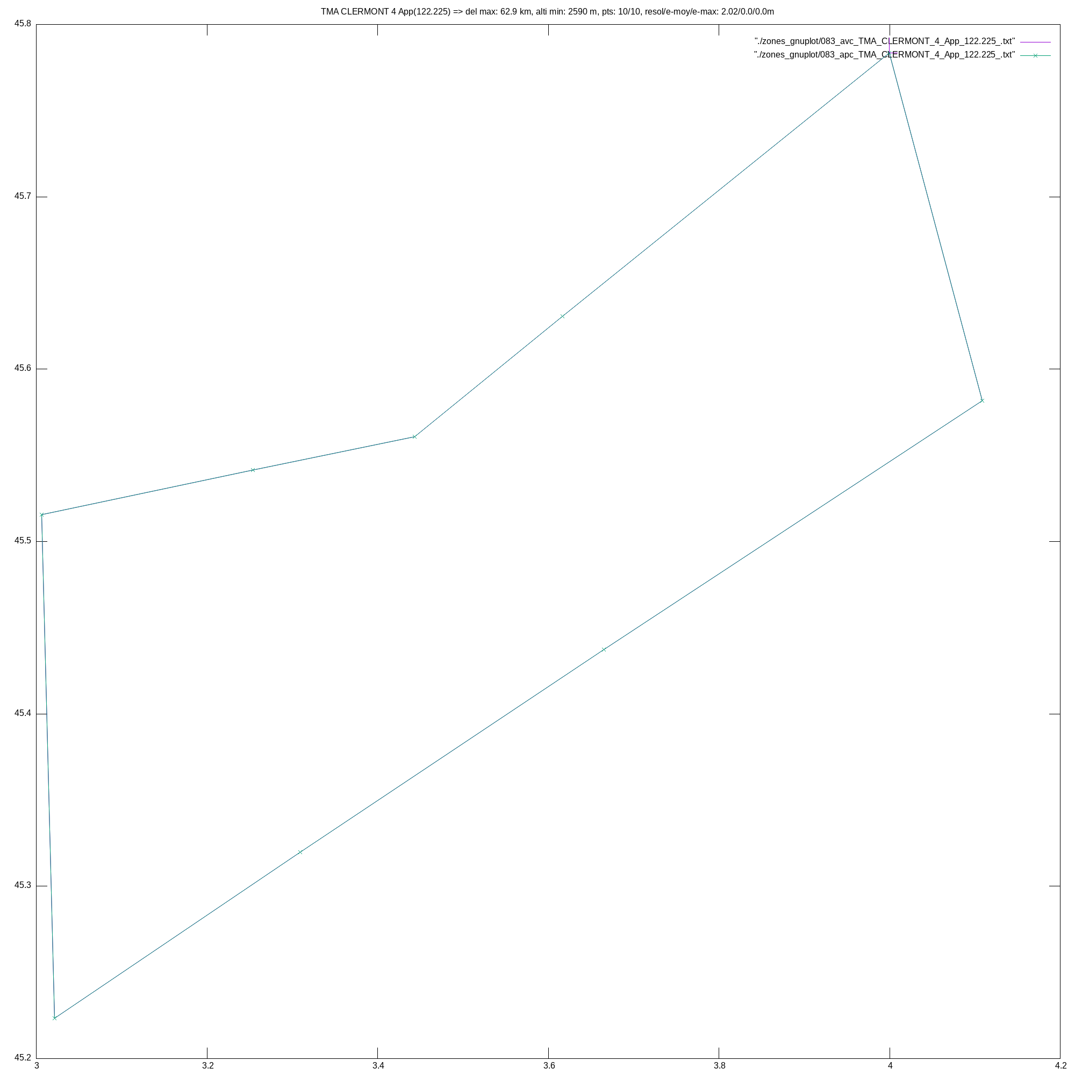
CompZoneAerienne/zones_gnuplot/083_png_TMA_CLERMONT_4_App_122.225_.png
