gitberthe/BertheVario/CompZoneAerienne/zones_gnuplot/084_png_CTA_MARSEILLE_6.png

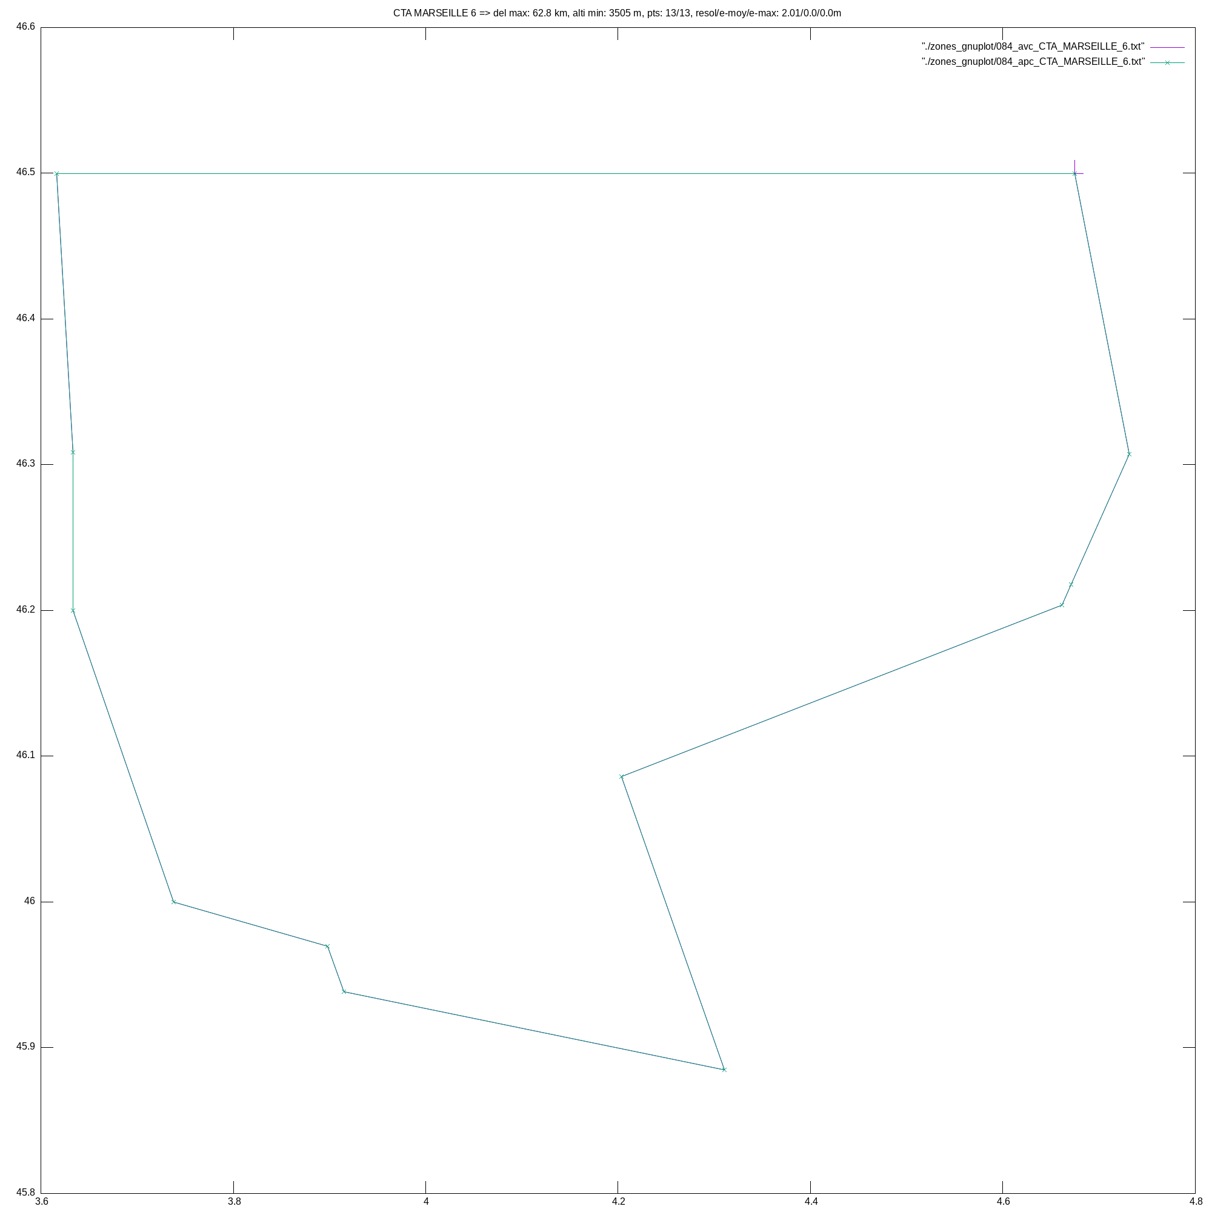
CompZoneAerienne/zones_gnuplot/084_png_CTA_MARSEILLE_6.png
