gitberthe/BertheVario/CompZoneAerienne/zones_gnuplot/085_png_TMA_CLERMONT_5.1_App_122.225_.png

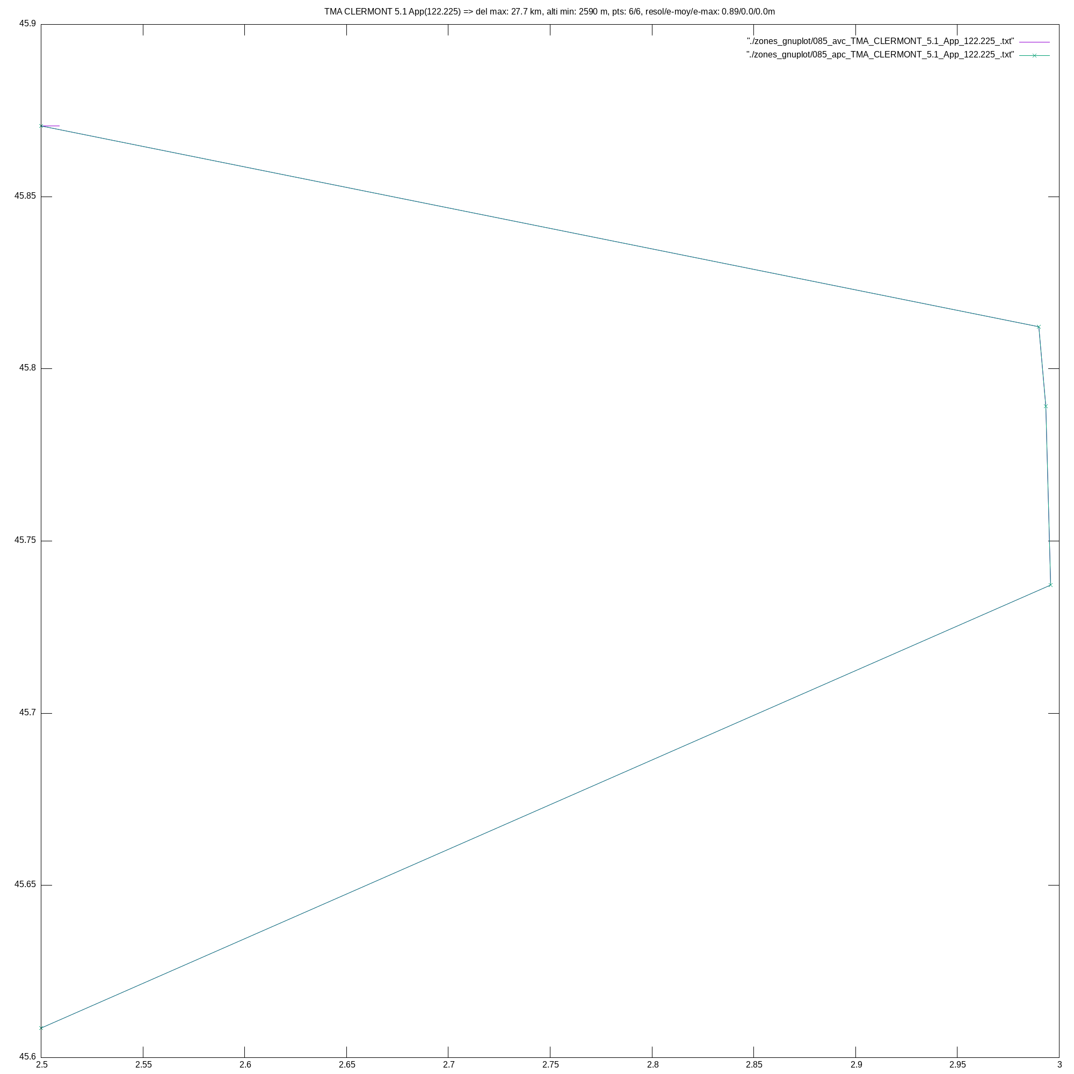
CompZoneAerienne/zones_gnuplot/085_png_TMA_CLERMONT_5.1_App_122.225_.png
