gitberthe/BertheVario/CompZoneAerienne/zones_gnuplot/086_png_TMA_CLERMONT_4.1_App_122.225_.png

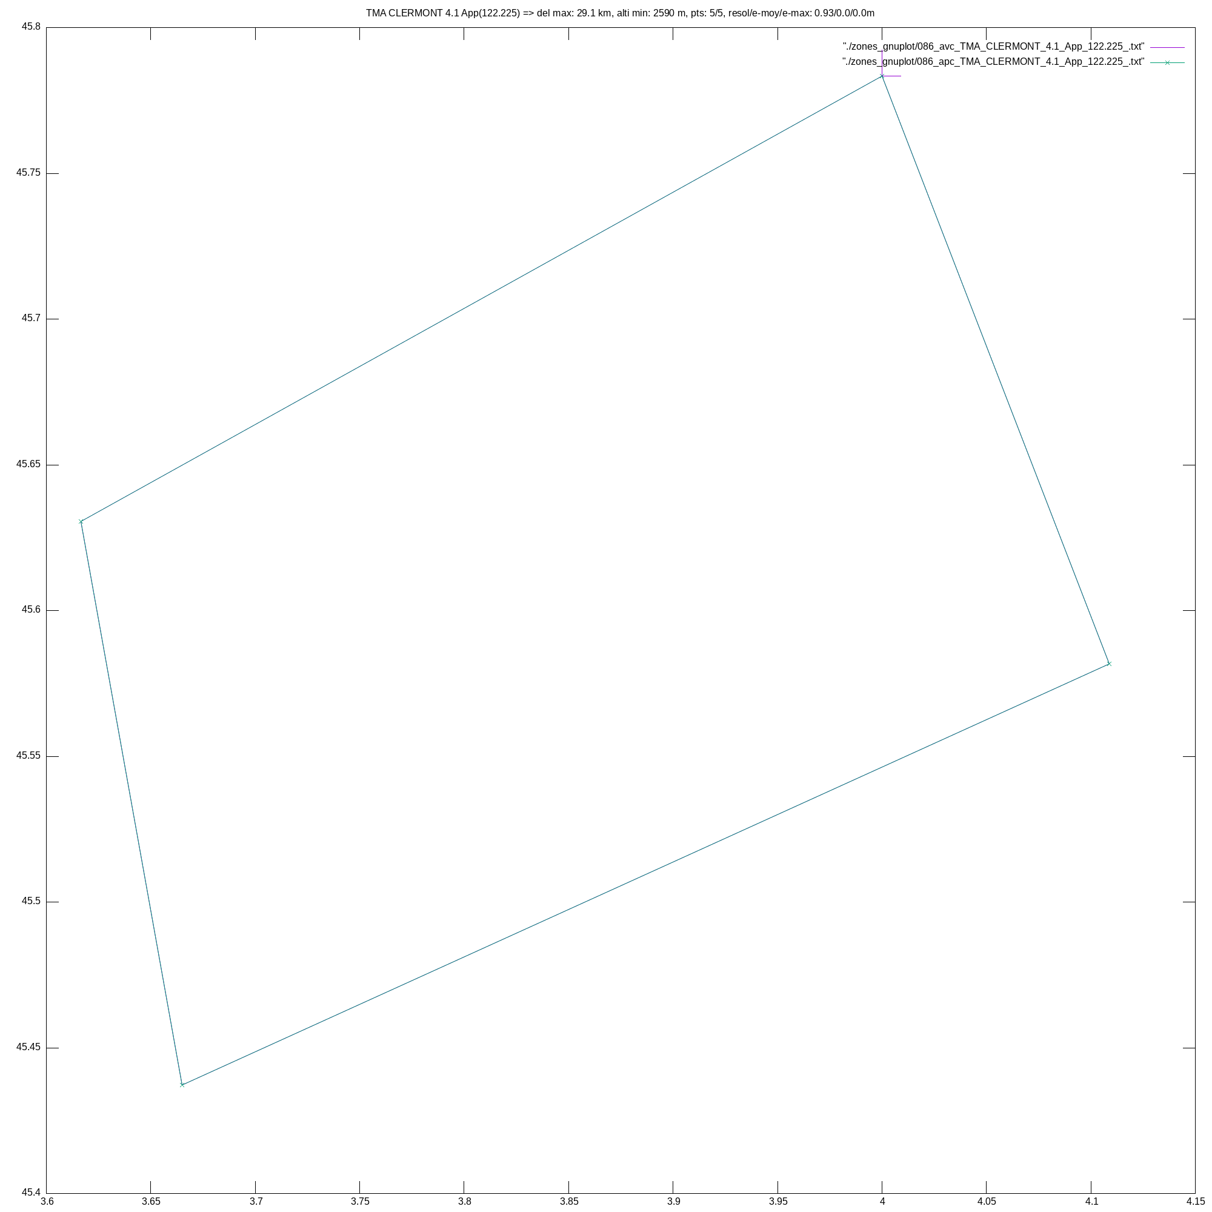
CompZoneAerienne/zones_gnuplot/086_png_TMA_CLERMONT_4.1_App_122.225_.png
