gitberthe/BertheVario/CompZoneAerienne/zones_gnuplot/087_png_R_203_B_Info_124.050_.png

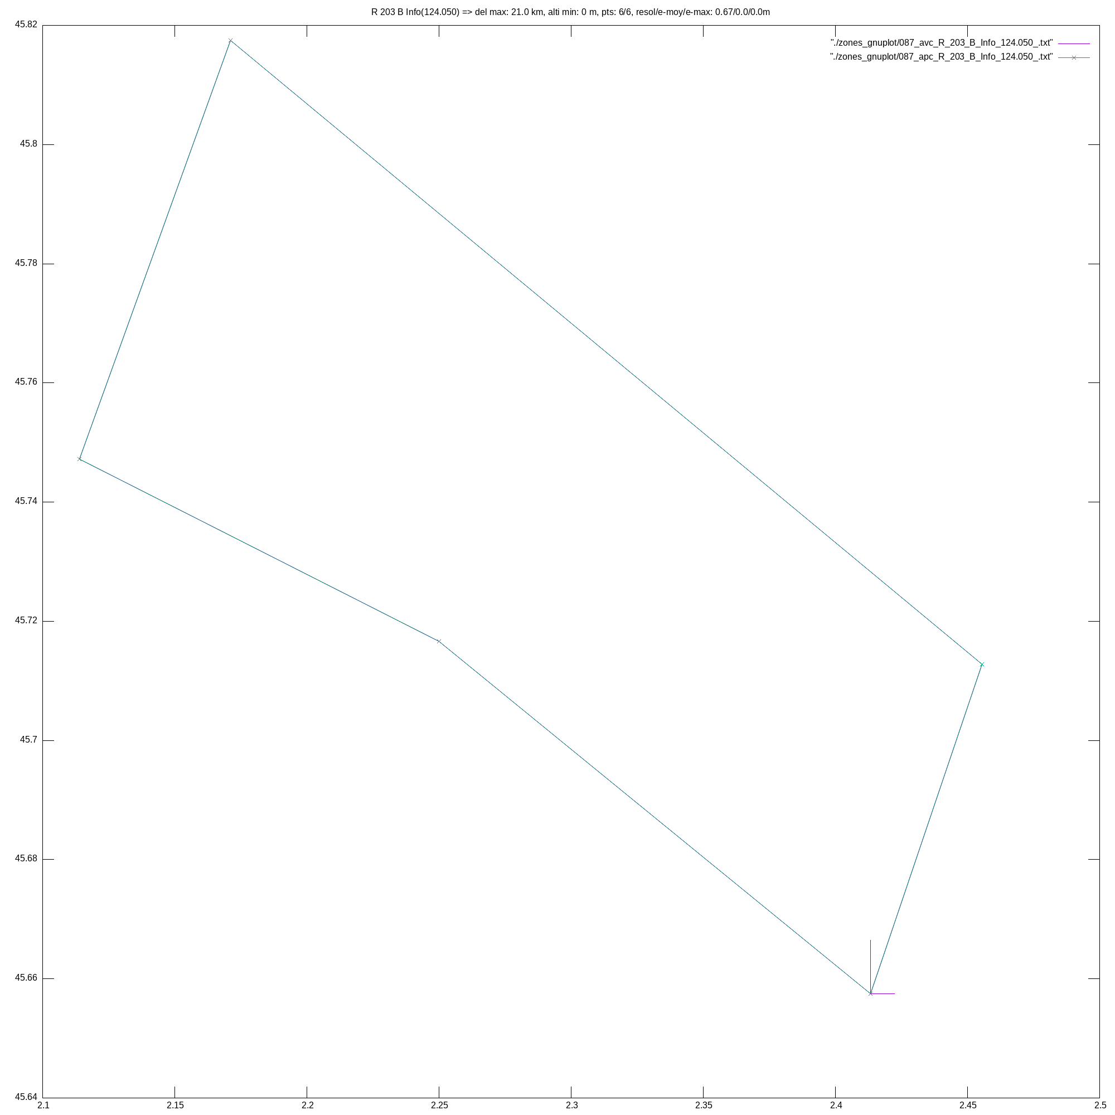
CompZoneAerienne/zones_gnuplot/087_png_R_203_B_Info_124.050_.png
