gitberthe/BertheVario/CompZoneAerienne/zones_gnuplot/088_png_TMA_LYON_05_App_133.150_.png

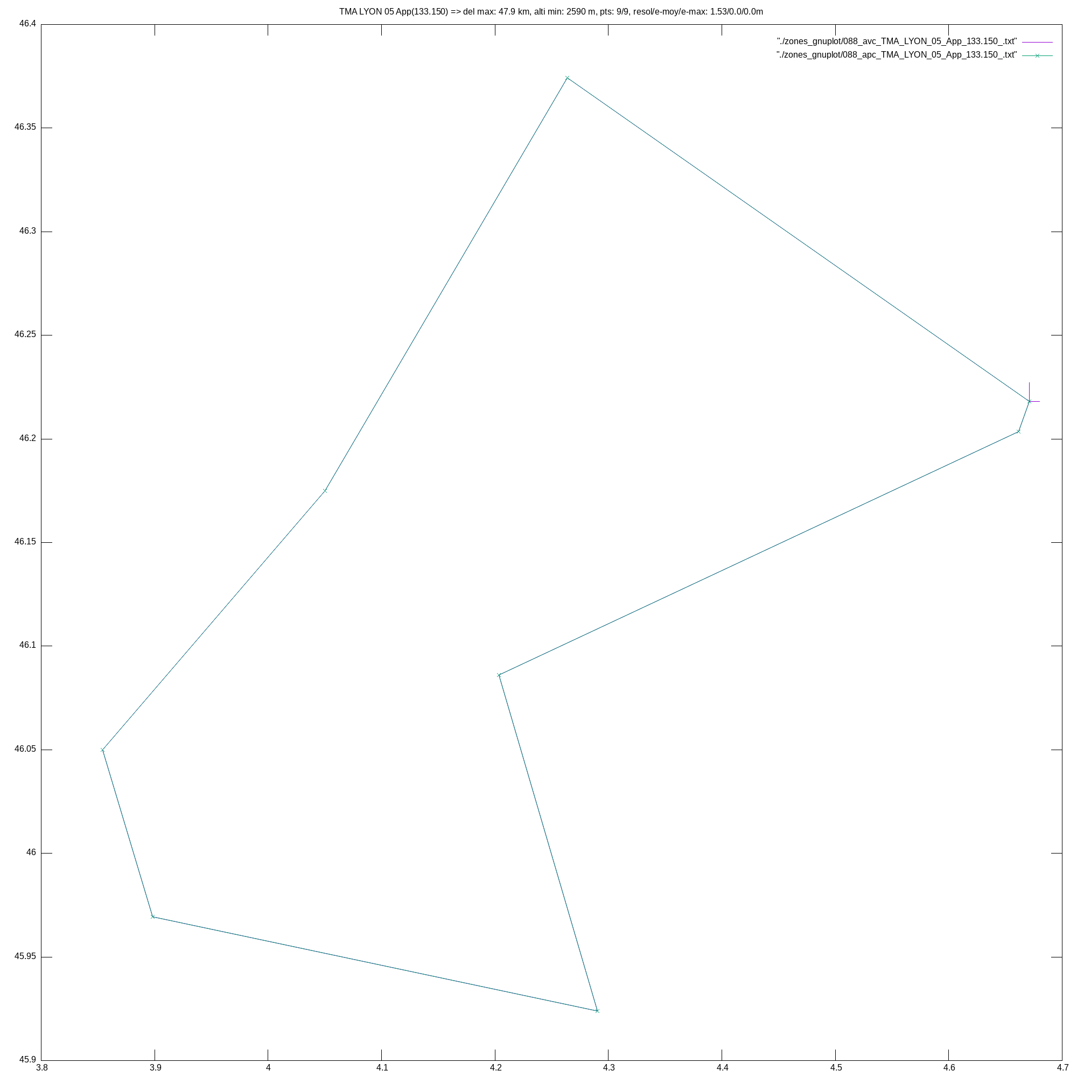
CompZoneAerienne/zones_gnuplot/088_png_TMA_LYON_05_App_133.150_.png
