gitberthe/BertheVario/CompZoneAerienne/zones_gnuplot/089_png_R_137_A__SeeNotam_.png

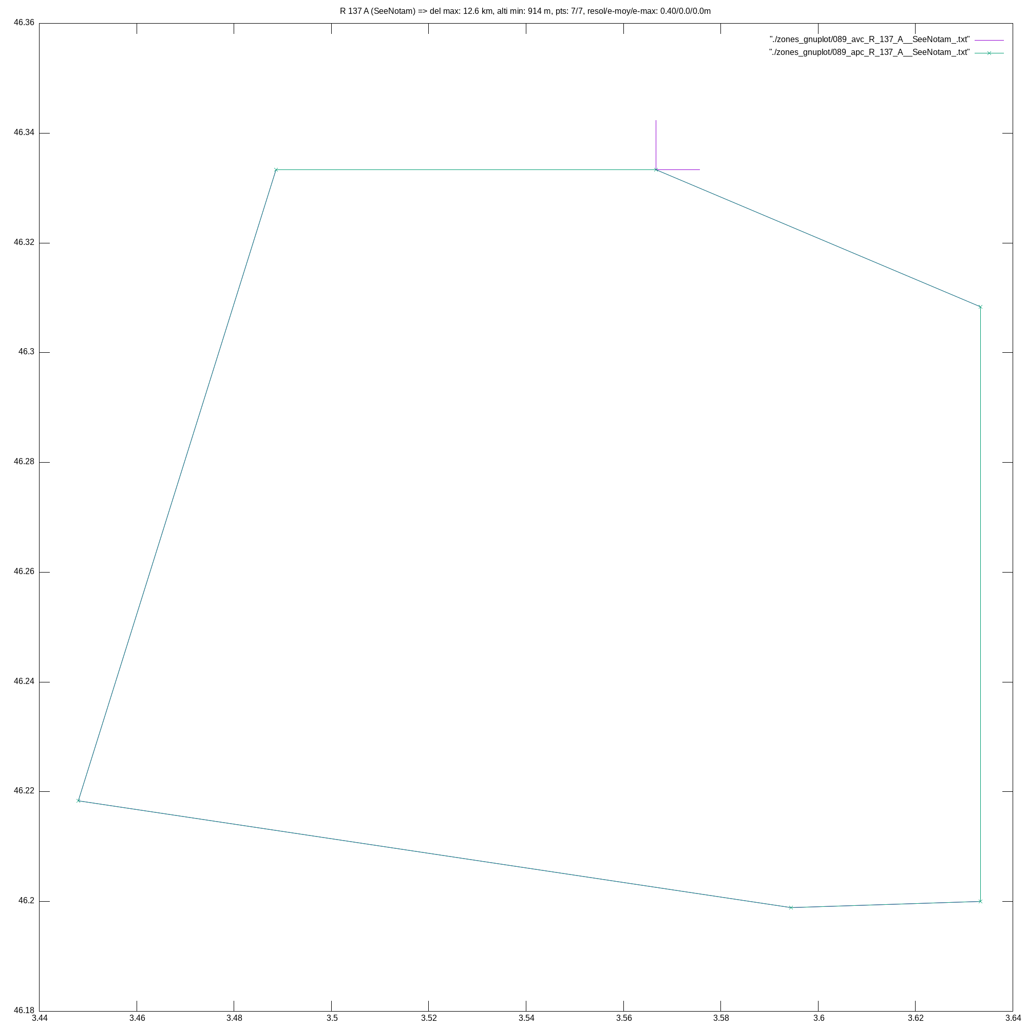
CompZoneAerienne/zones_gnuplot/089_png_R_137_A__SeeNotam_.png
