gitberthe/BertheVario/CompZoneAerienne/zones_gnuplot/090_png_R_137_B__SeeNotam_.png

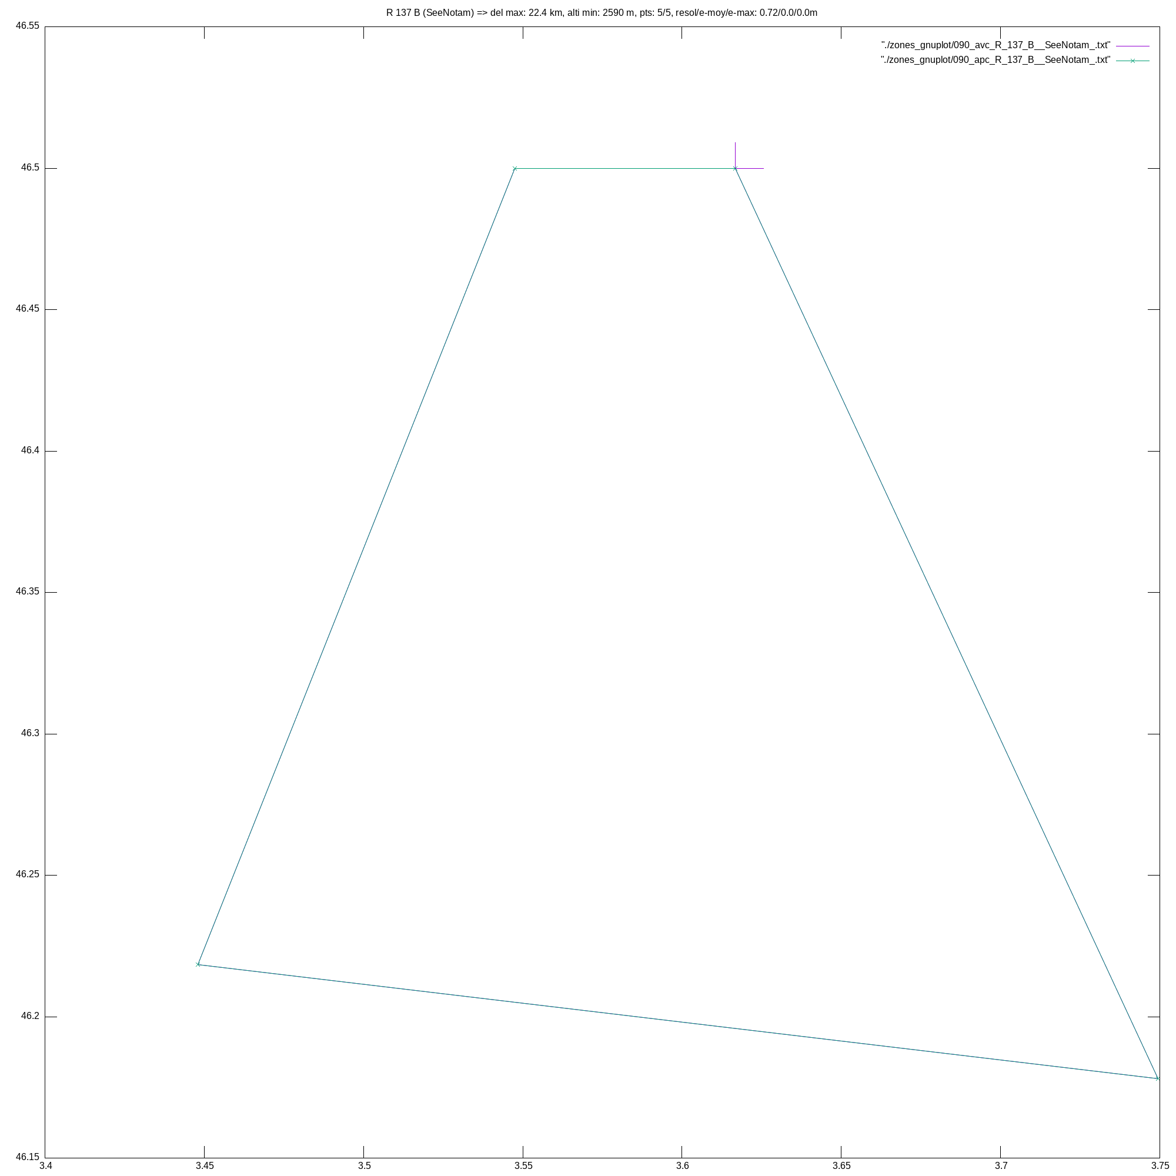
CompZoneAerienne/zones_gnuplot/090_png_R_137_B__SeeNotam_.png
