gitberthe/BertheVario/CompZoneAerienne/zones_gnuplot/091_png_RTBA_143__MILOPS___SeeNotam_.png

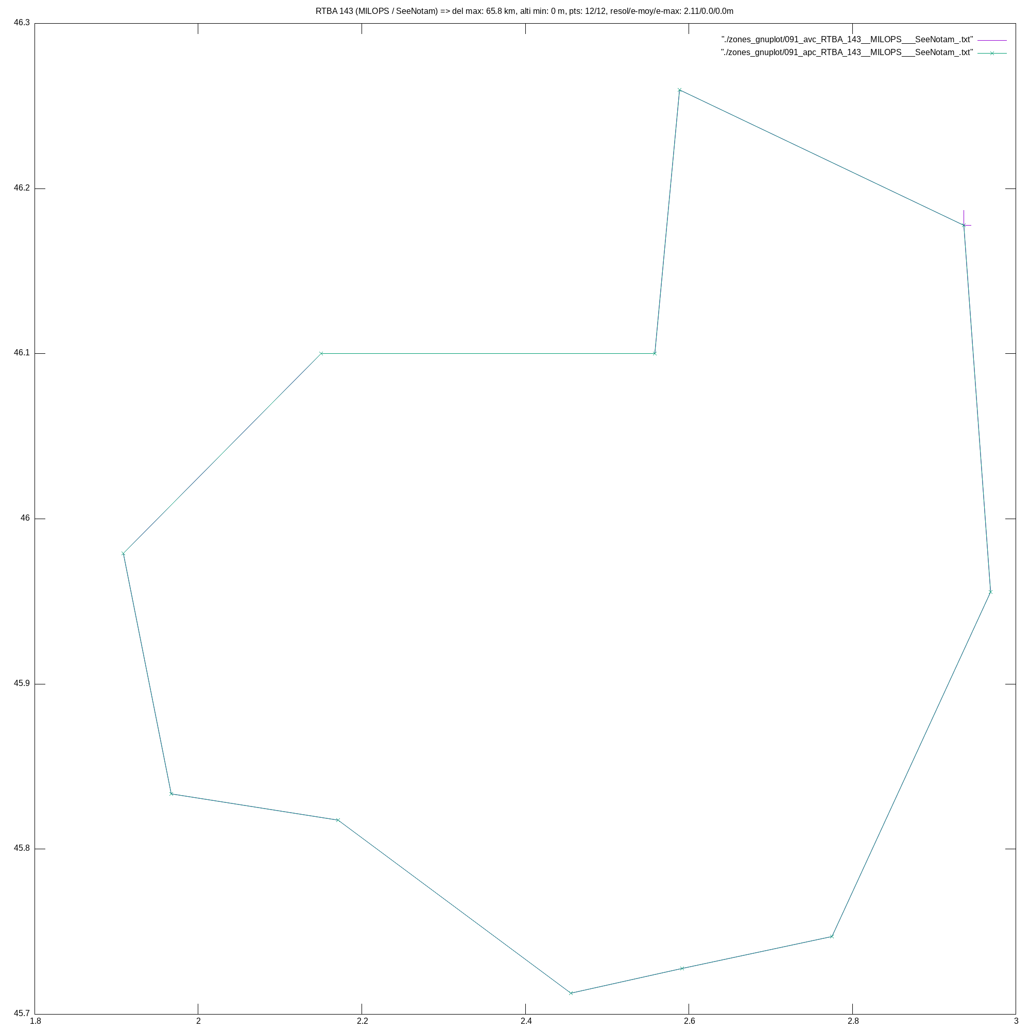
CompZoneAerienne/zones_gnuplot/091_png_RTBA_143__MILOPS___SeeNotam_.png
