gitberthe/BertheVario/CompZoneAerienne/zones_gnuplot/092_png_RTBA_144_B__MILOPS___SeeNotam_.png

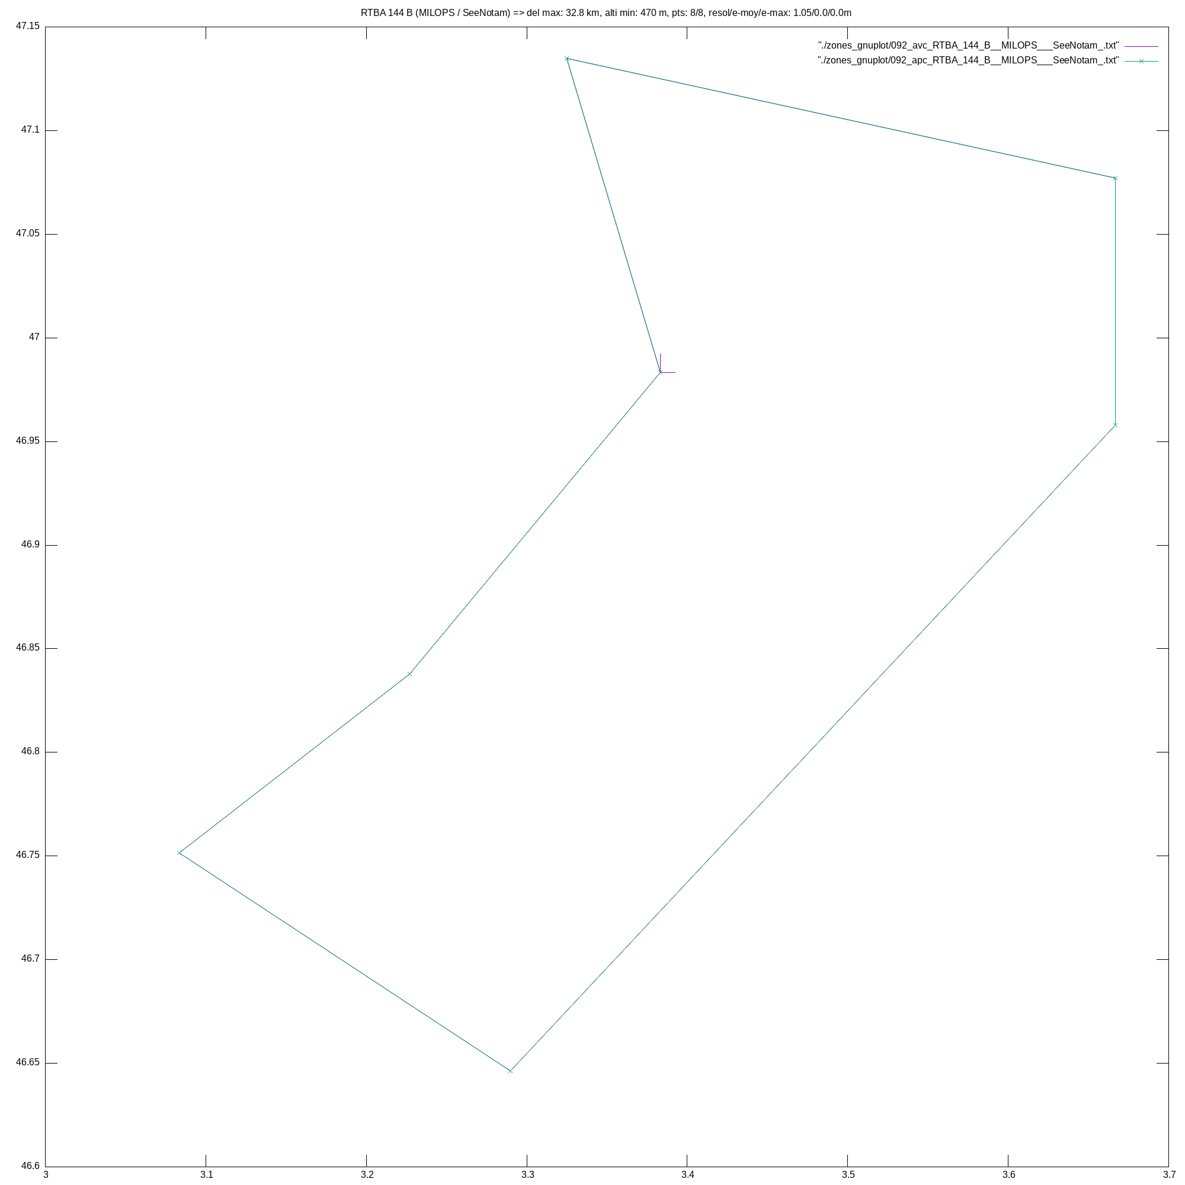
CompZoneAerienne/zones_gnuplot/092_png_RTBA_144_B__MILOPS___SeeNotam_.png
