gitberthe/BertheVario/CompZoneAerienne/zones_gnuplot/093_png_RTBA_144_A__MILOPS___SeeNotam_.png

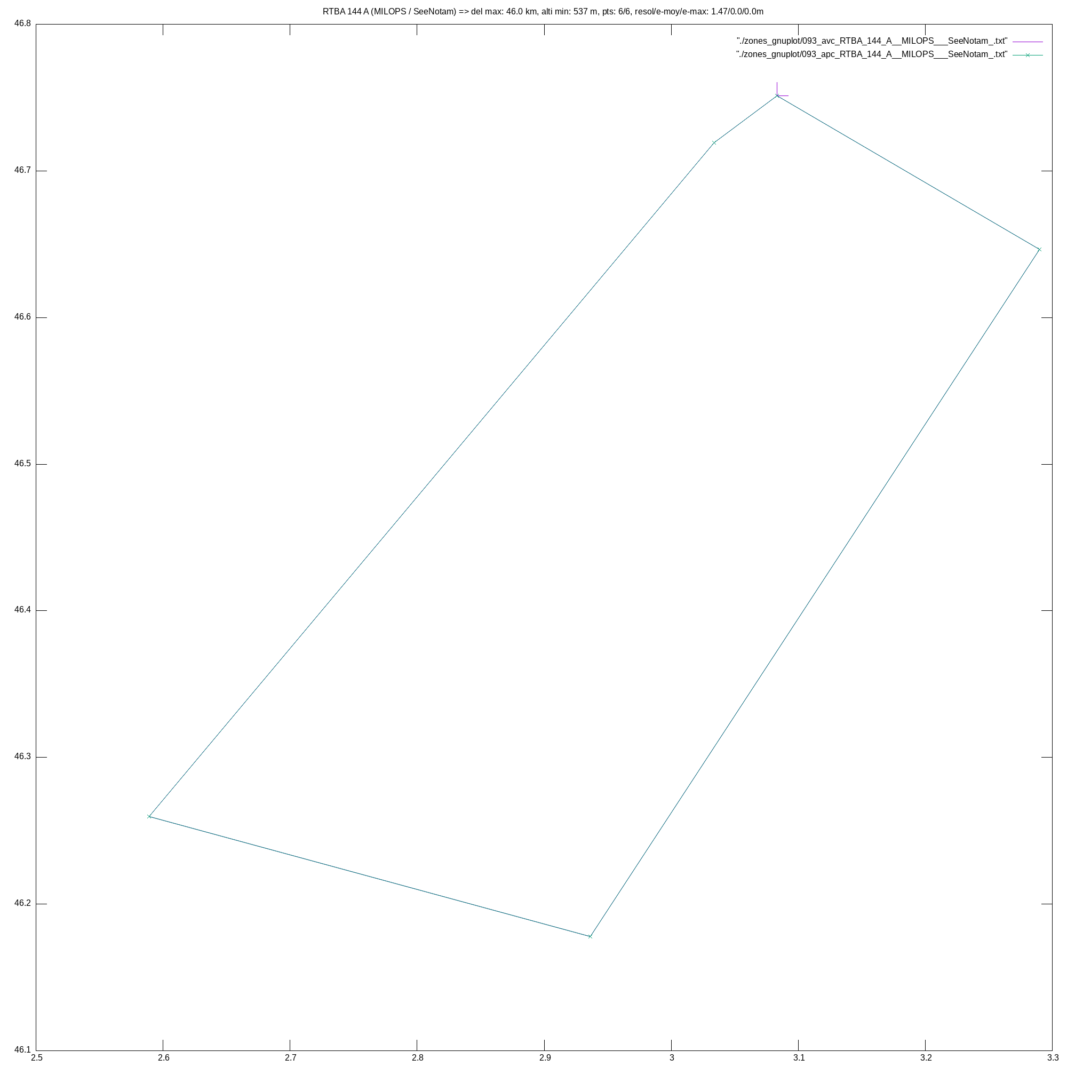
CompZoneAerienne/zones_gnuplot/093_png_RTBA_144_A__MILOPS___SeeNotam_.png
