gitberthe/BertheVario/CompZoneAerienne/zones_gnuplot/094_png_R_20_B2_S_App_119.7_.png

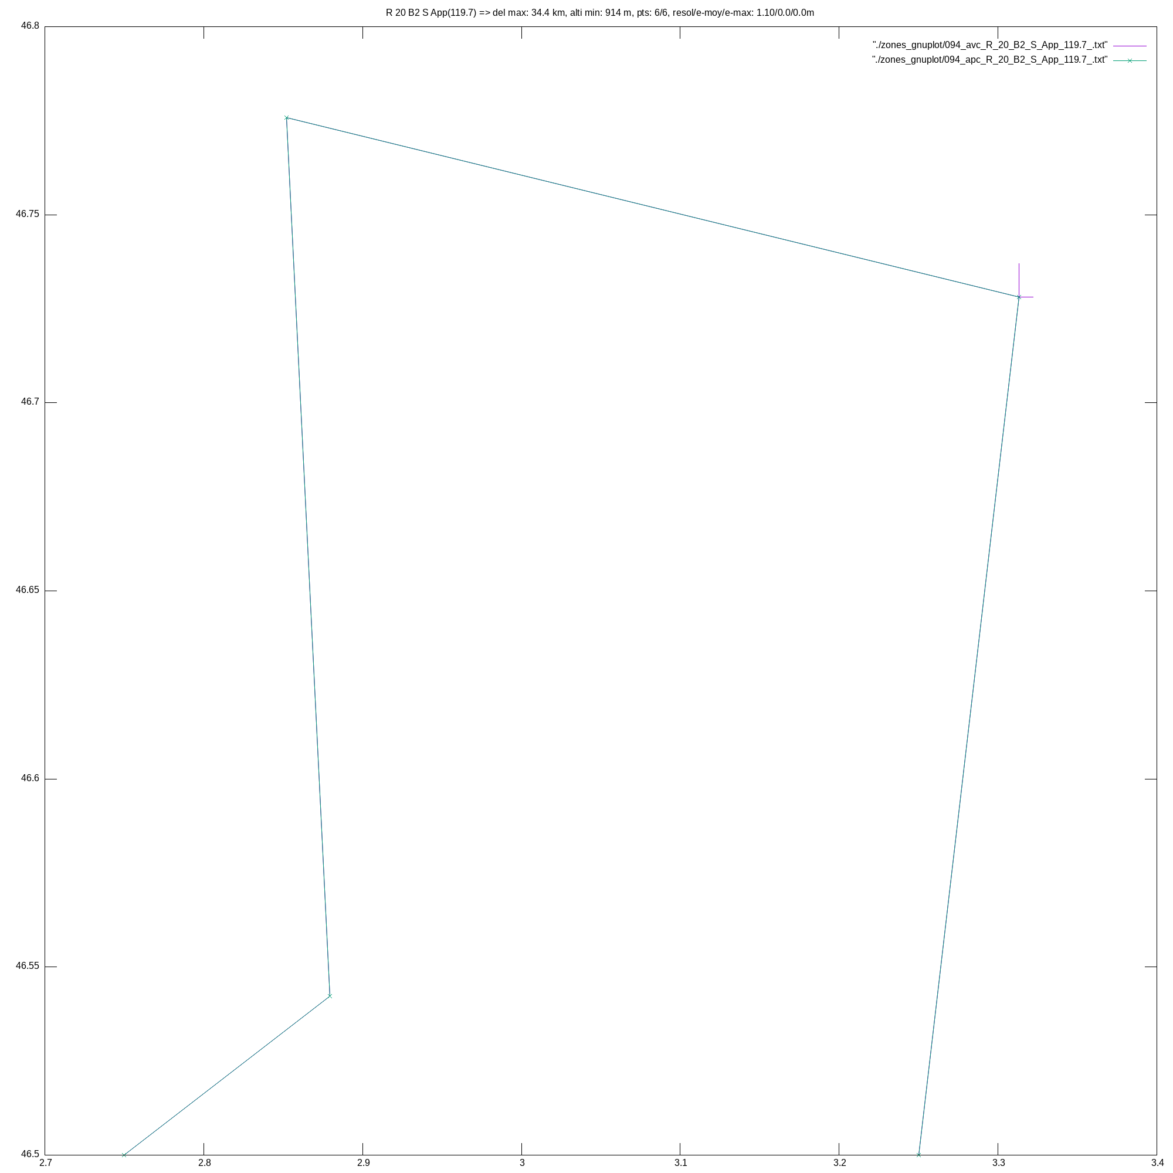
CompZoneAerienne/zones_gnuplot/094_png_R_20_B2_S_App_119.7_.png
