gitberthe/BertheVario/CompZoneAerienne/zones_gnuplot/095_png_P_235_L.png

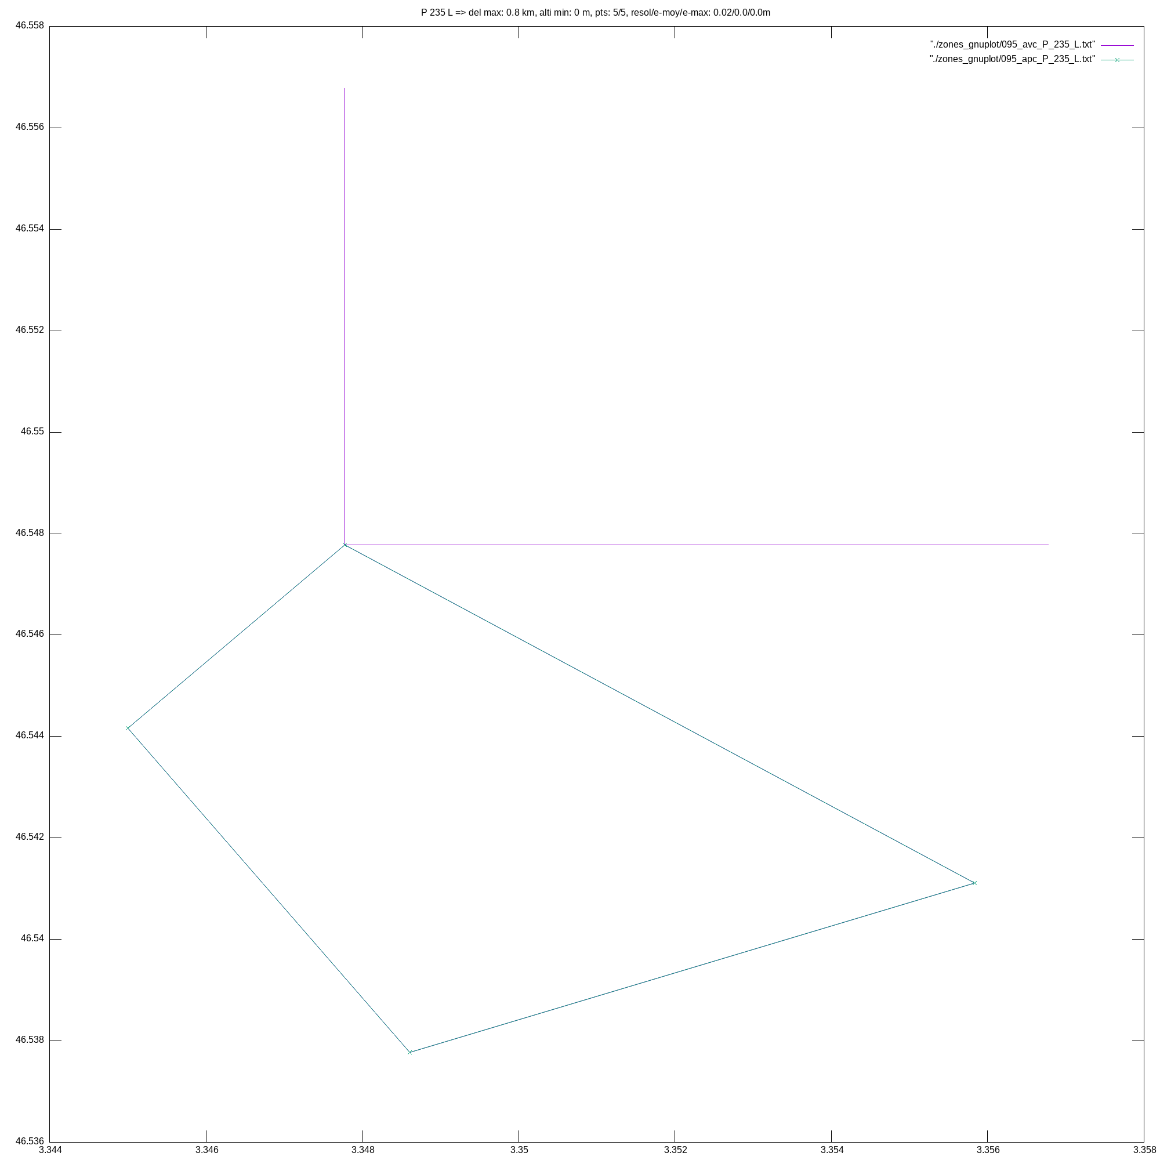
CompZoneAerienne/zones_gnuplot/095_png_P_235_L.png
