gitberthe/BertheVario/CompZoneAerienne/zones_gnuplot/096_png_TMA_SAINT-YAN_1_App_123.405_.png

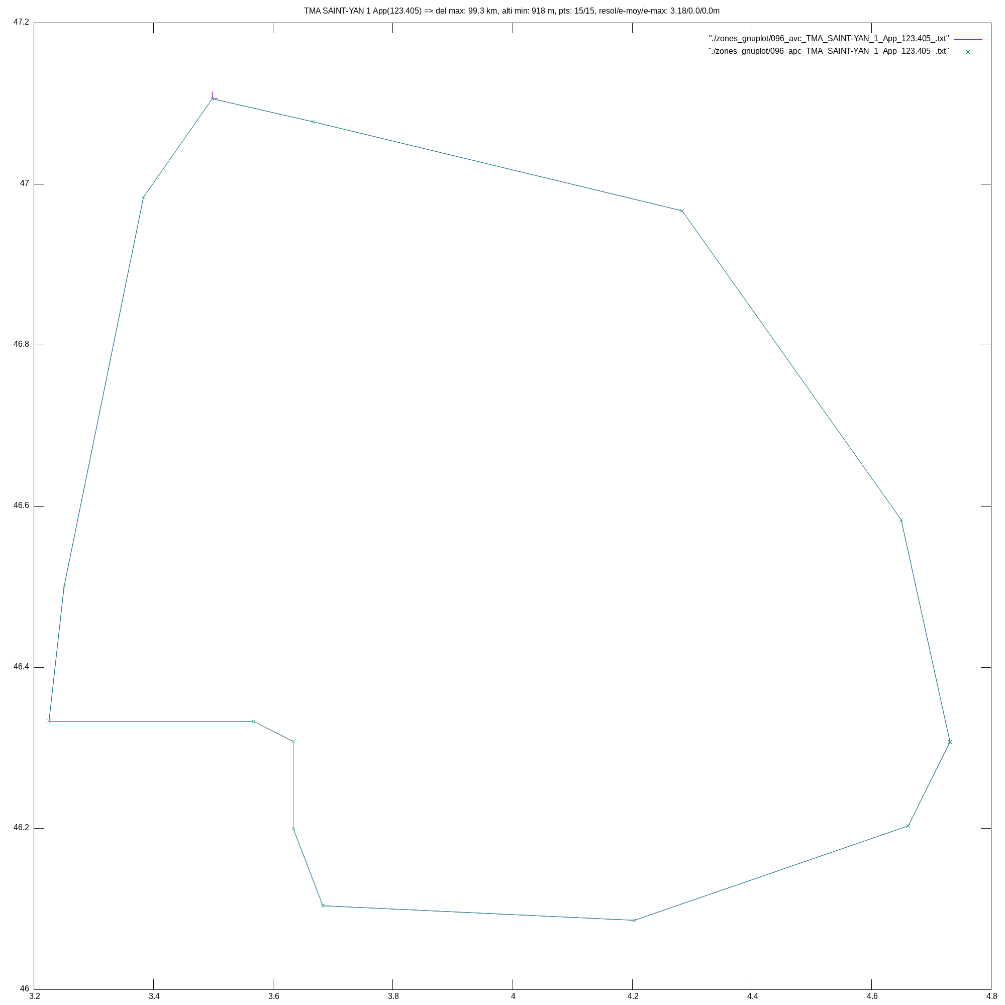
CompZoneAerienne/zones_gnuplot/096_png_TMA_SAINT-YAN_1_App_123.405_.png
