gitberthe/BertheVario/CompZoneAerienne/zones_gnuplot/097_png_R_3203.png

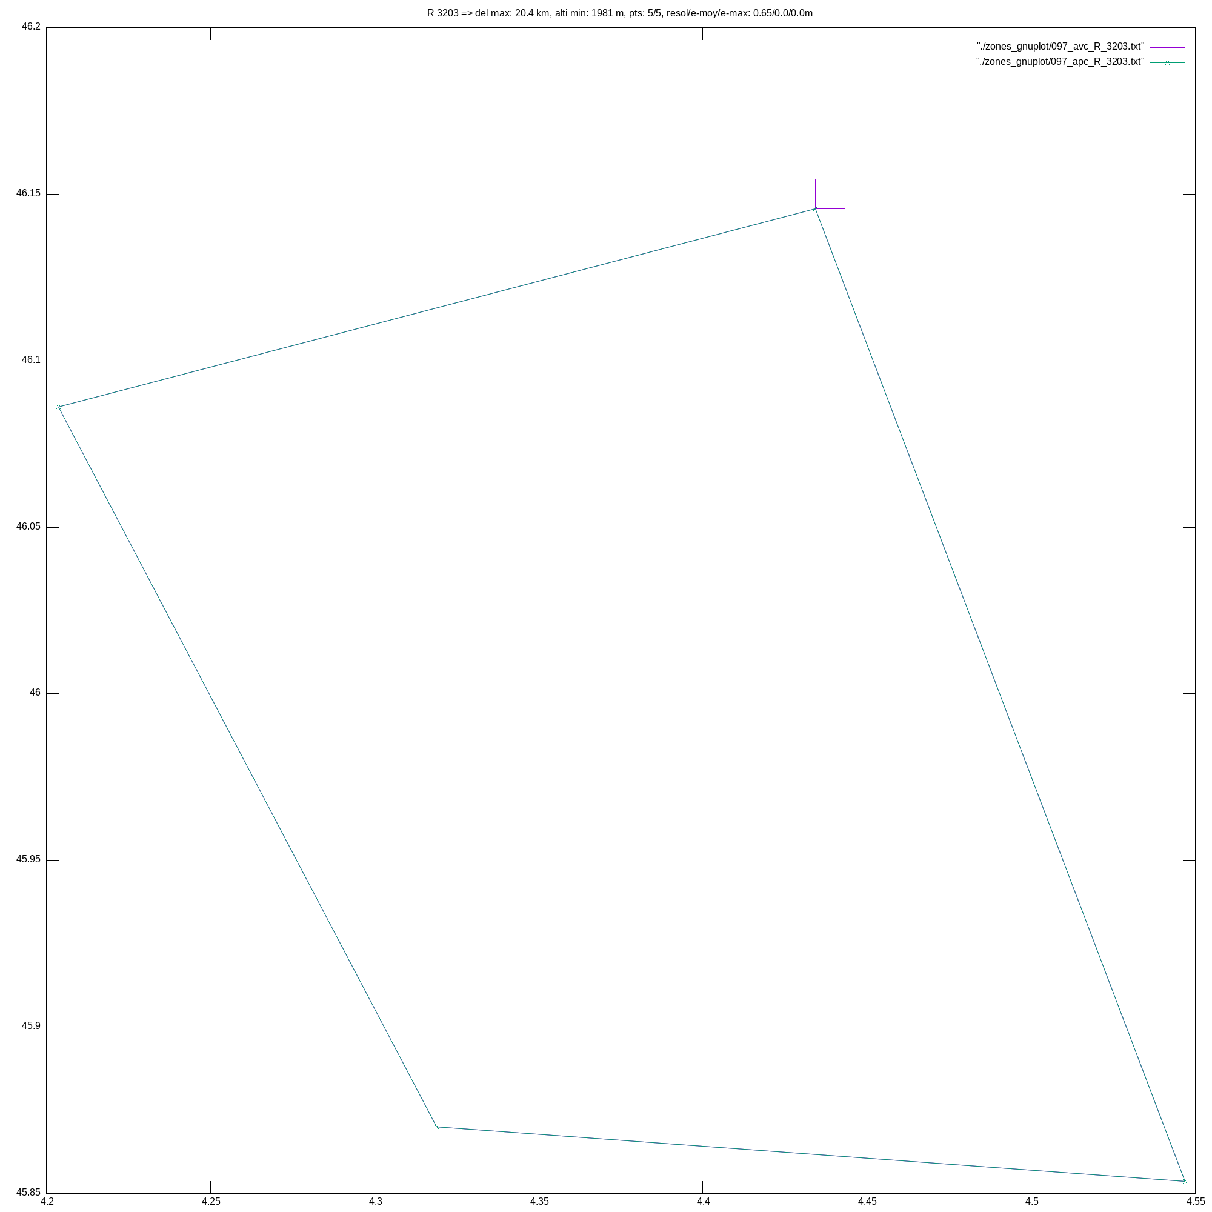
CompZoneAerienne/zones_gnuplot/097_png_R_3203.png
