gitberthe/BertheVario/CompZoneAerienne/zones_gnuplot/098_png_R_108_E2.png

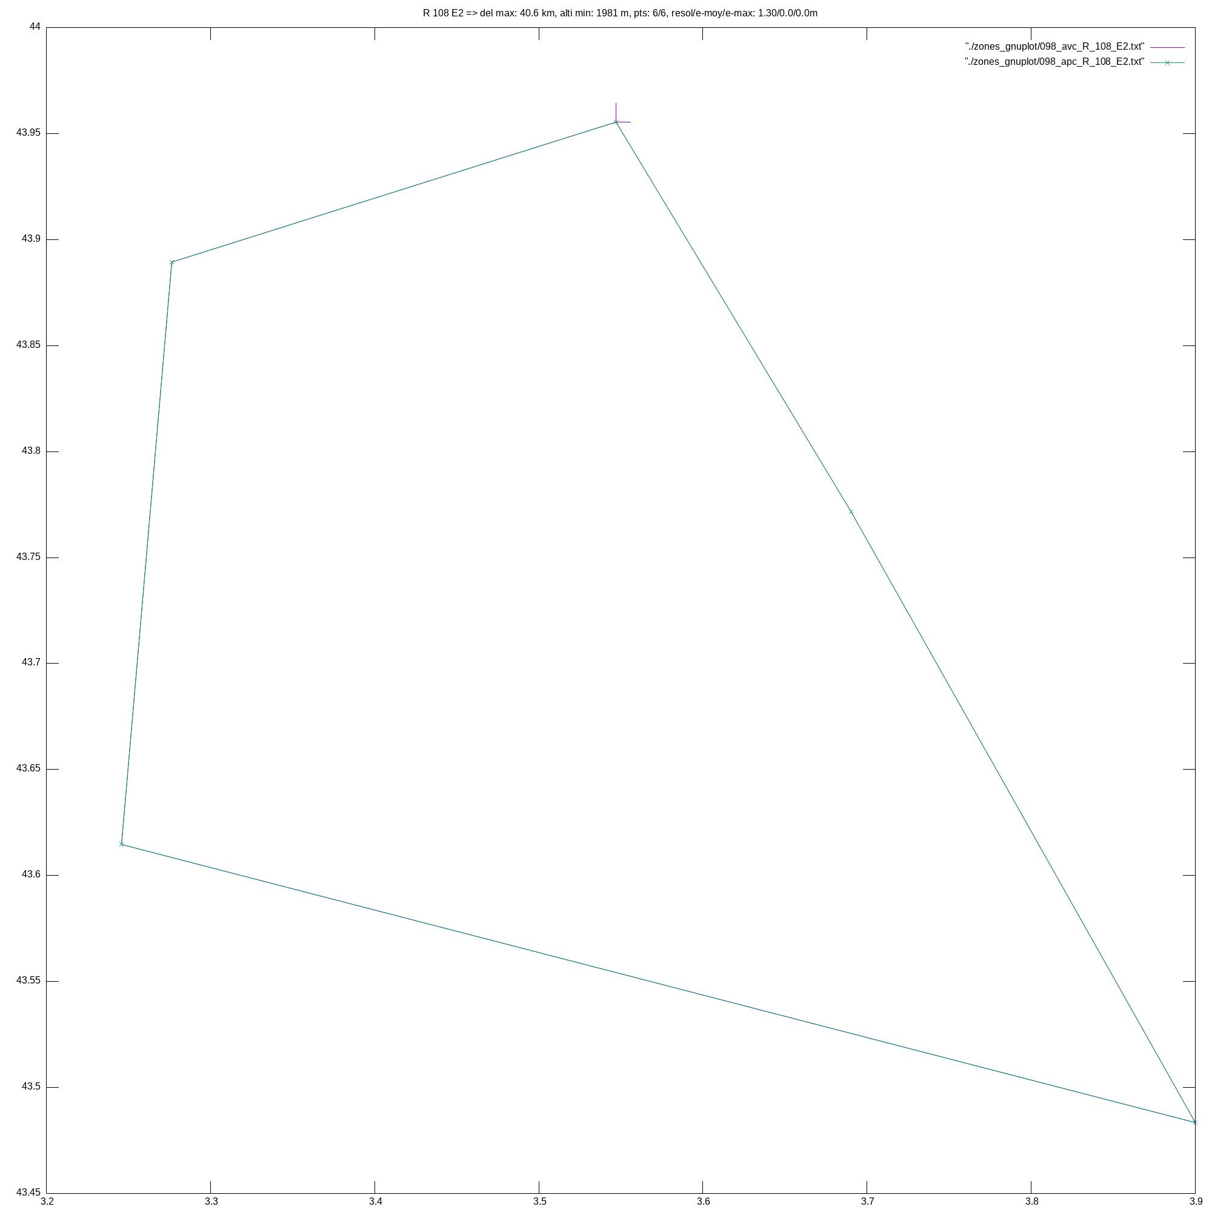
CompZoneAerienne/zones_gnuplot/098_png_R_108_E2.png
