gitberthe/BertheVario/CompZoneAerienne/zones_gnuplot/099_png_R_108_E1_Twr_127.925_.png

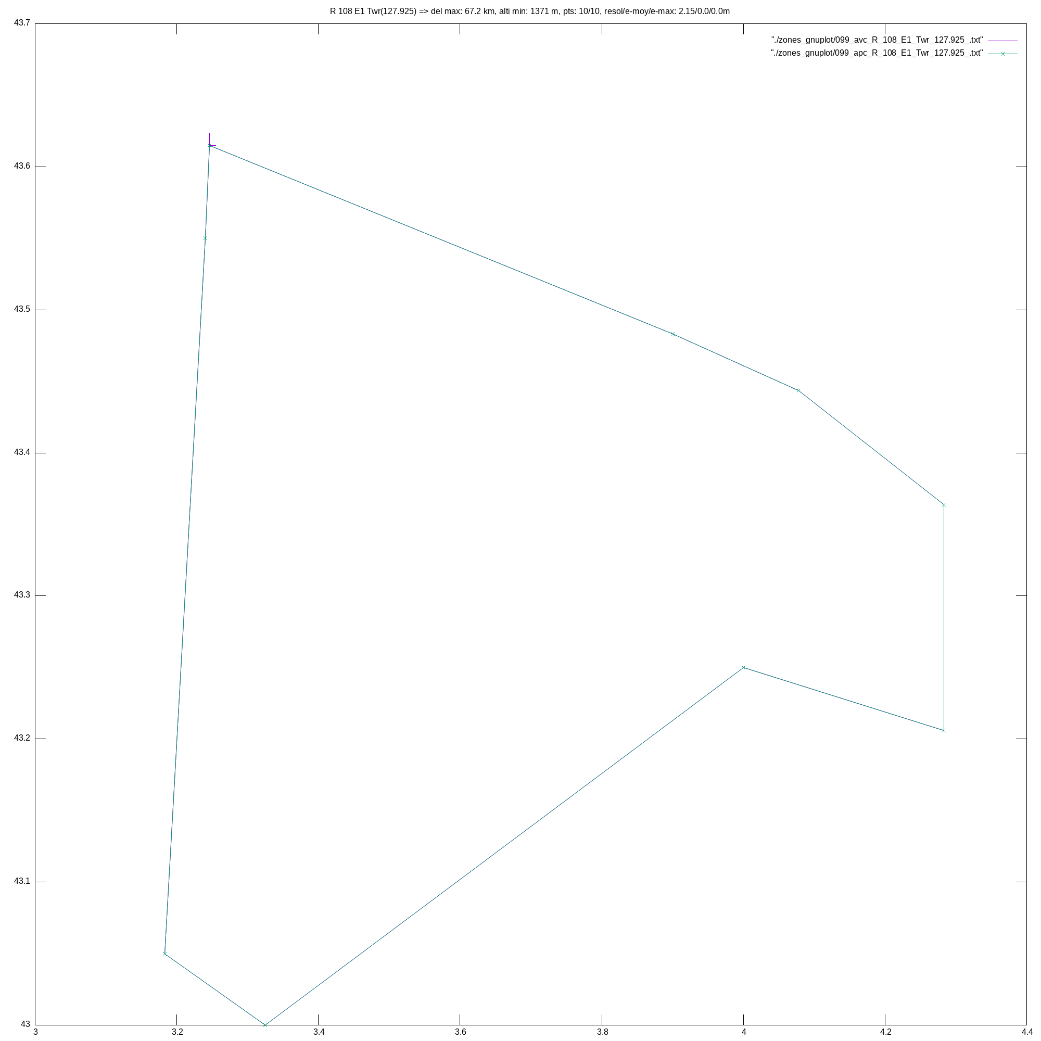
CompZoneAerienne/zones_gnuplot/099_png_R_108_E1_Twr_127.925_.png
