gitberthe/BertheVario/CompZoneAerienne/zones_gnuplot/100_png_R_108_E3.png

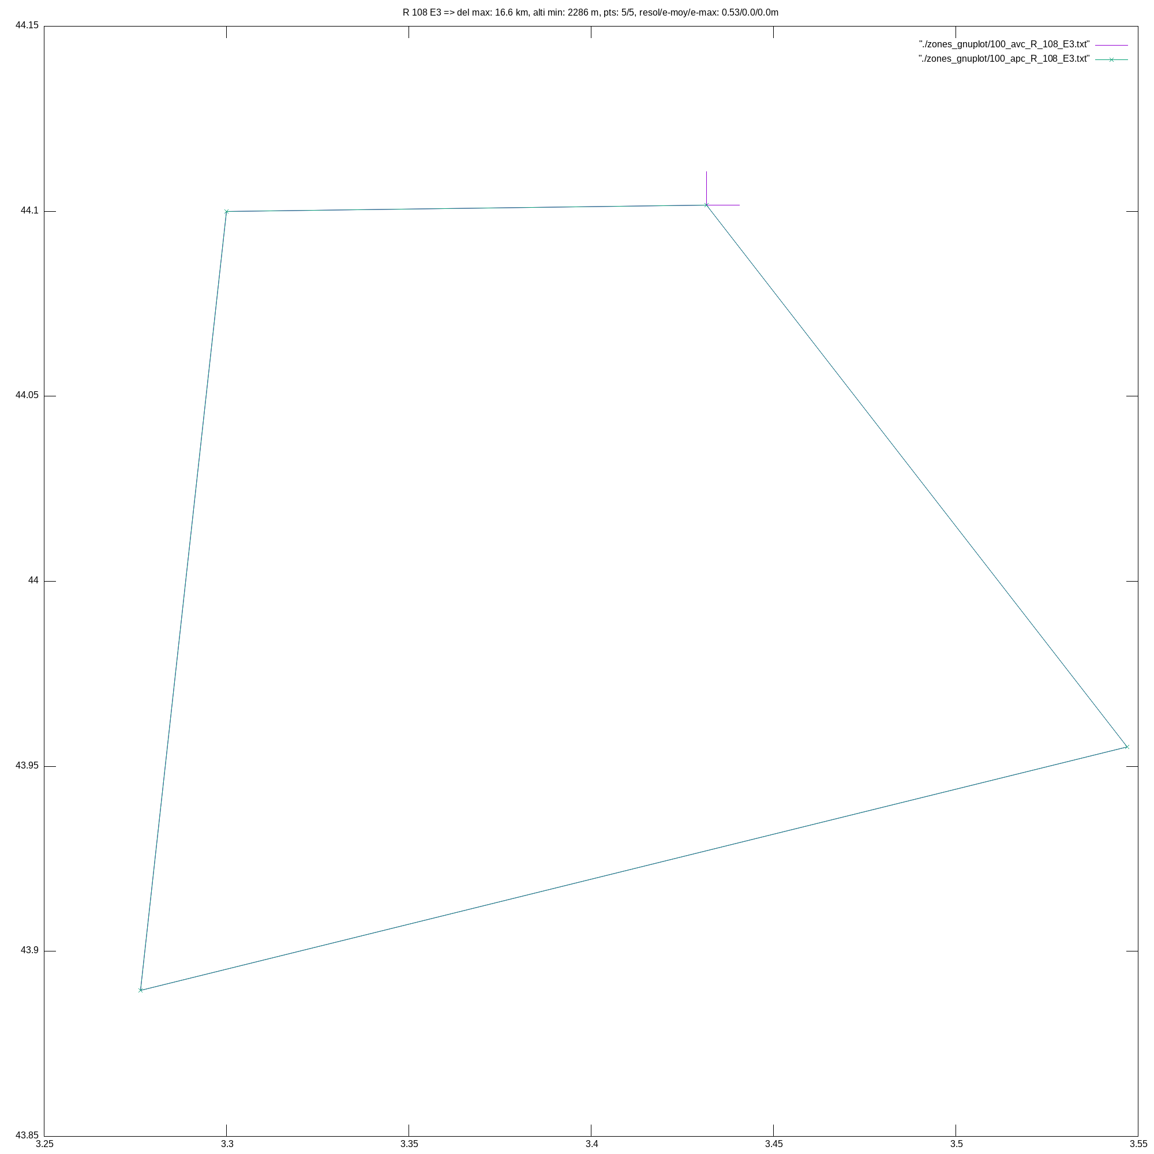
CompZoneAerienne/zones_gnuplot/100_png_R_108_E3.png
