gitberthe/BertheVario/CompZoneAerienne/zones_gnuplot/101_png_CTA_RHONE_6_Atis_127.925_.png

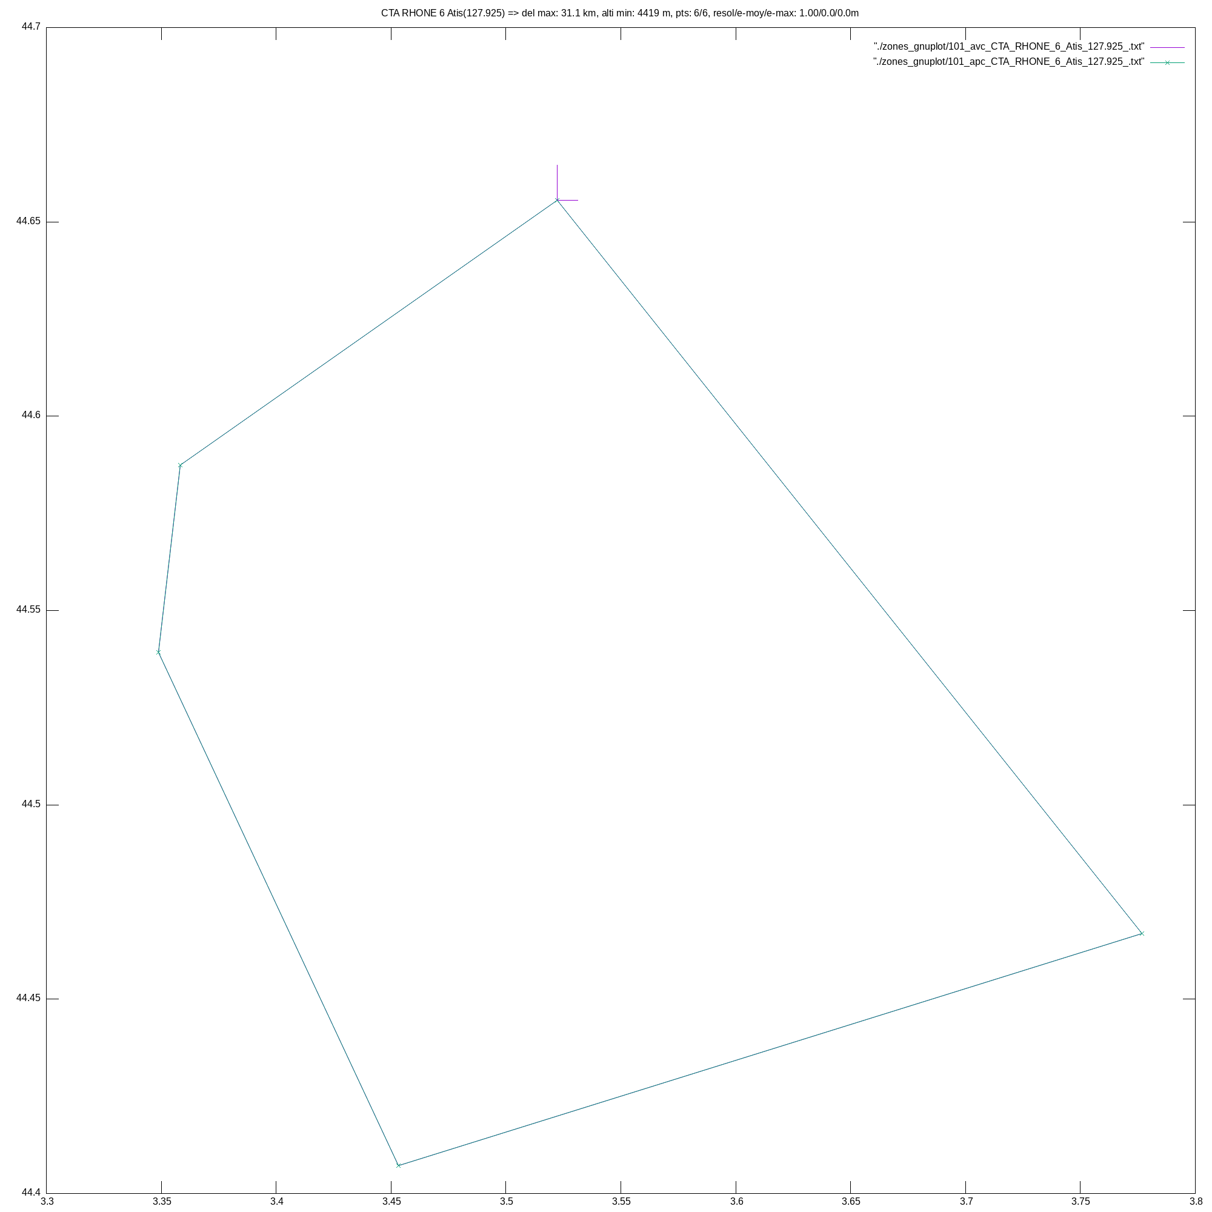
CompZoneAerienne/zones_gnuplot/101_png_CTA_RHONE_6_Atis_127.925_.png
