gitberthe/BertheVario/CompZoneAerienne/zones_gnuplot/103_png_RTBA_592__MILOPS___SeeNotam_.png

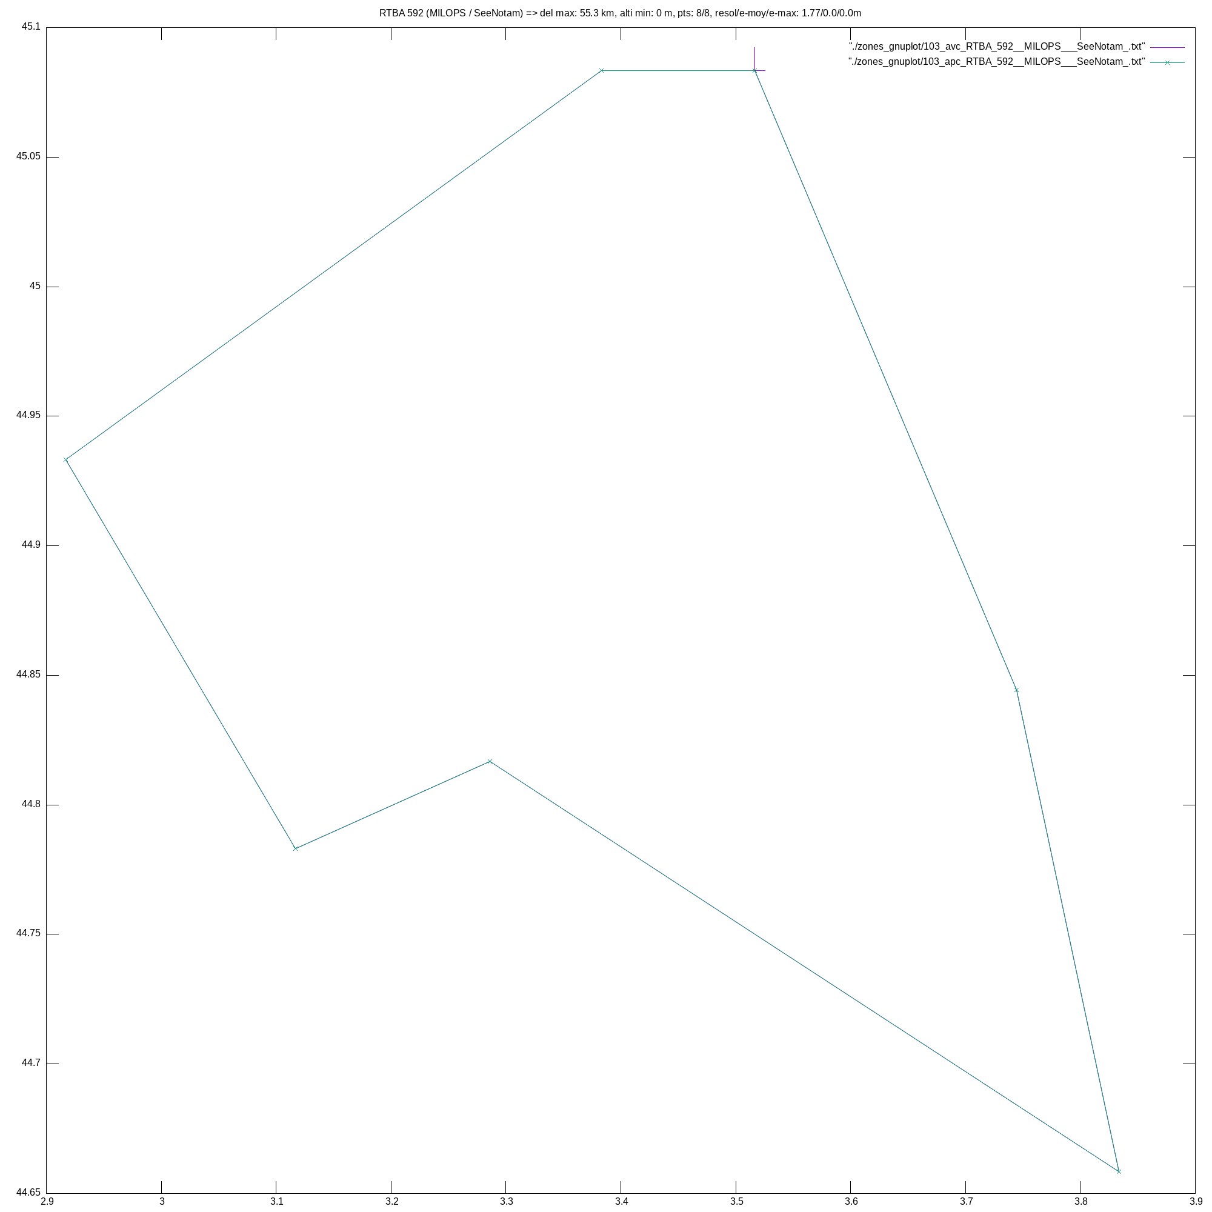
CompZoneAerienne/zones_gnuplot/103_png_RTBA_592__MILOPS___SeeNotam_.png
