gitberthe/BertheVario/CompZoneAerienne/zones_gnuplot/104_png_RTBA_590_B__MILOPS___SeeNotam_.png

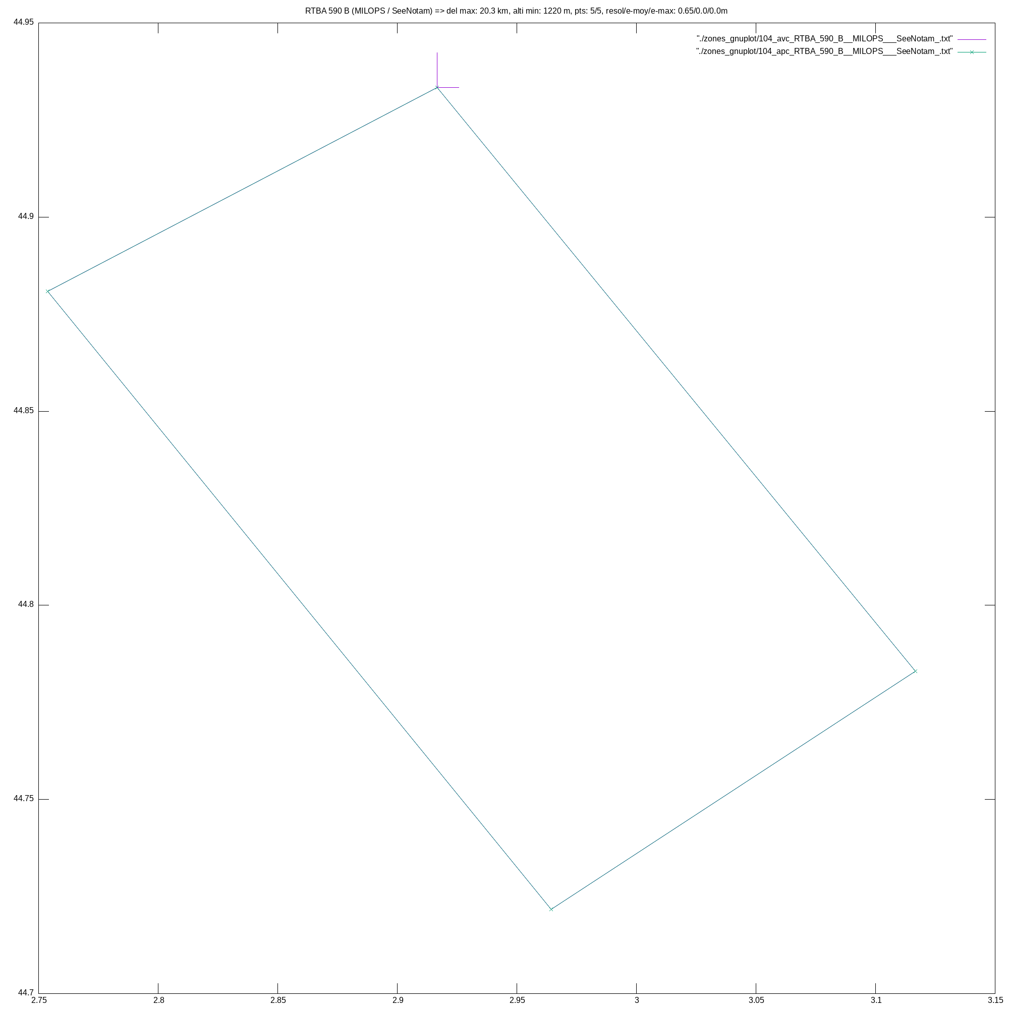
CompZoneAerienne/zones_gnuplot/104_png_RTBA_590_B__MILOPS___SeeNotam_.png
