gitberthe/BertheVario/CompZoneAerienne/zones_gnuplot/105_png_TMA_SAINT-YAN_1.4_App_123.405___FFVL-Prot_.png

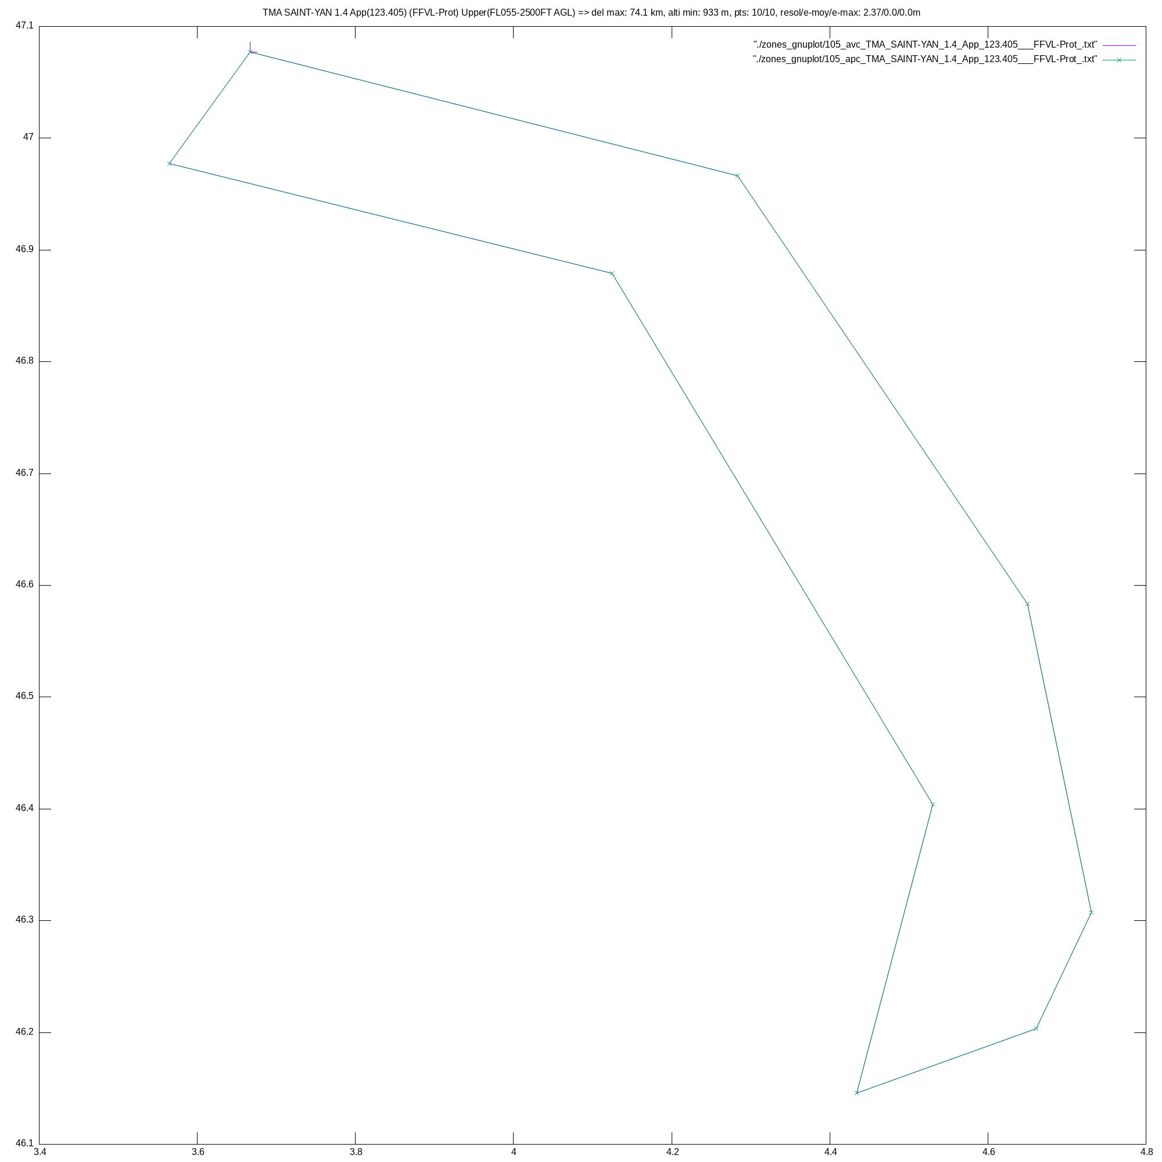
CompZoneAerienne/zones_gnuplot/105_png_TMA_SAINT-YAN_1.4_App_123.405___FFVL-Prot_.png
