gitberthe/BertheVario/CompZoneAerienne/zones_gnuplot/106_png_R_224.png

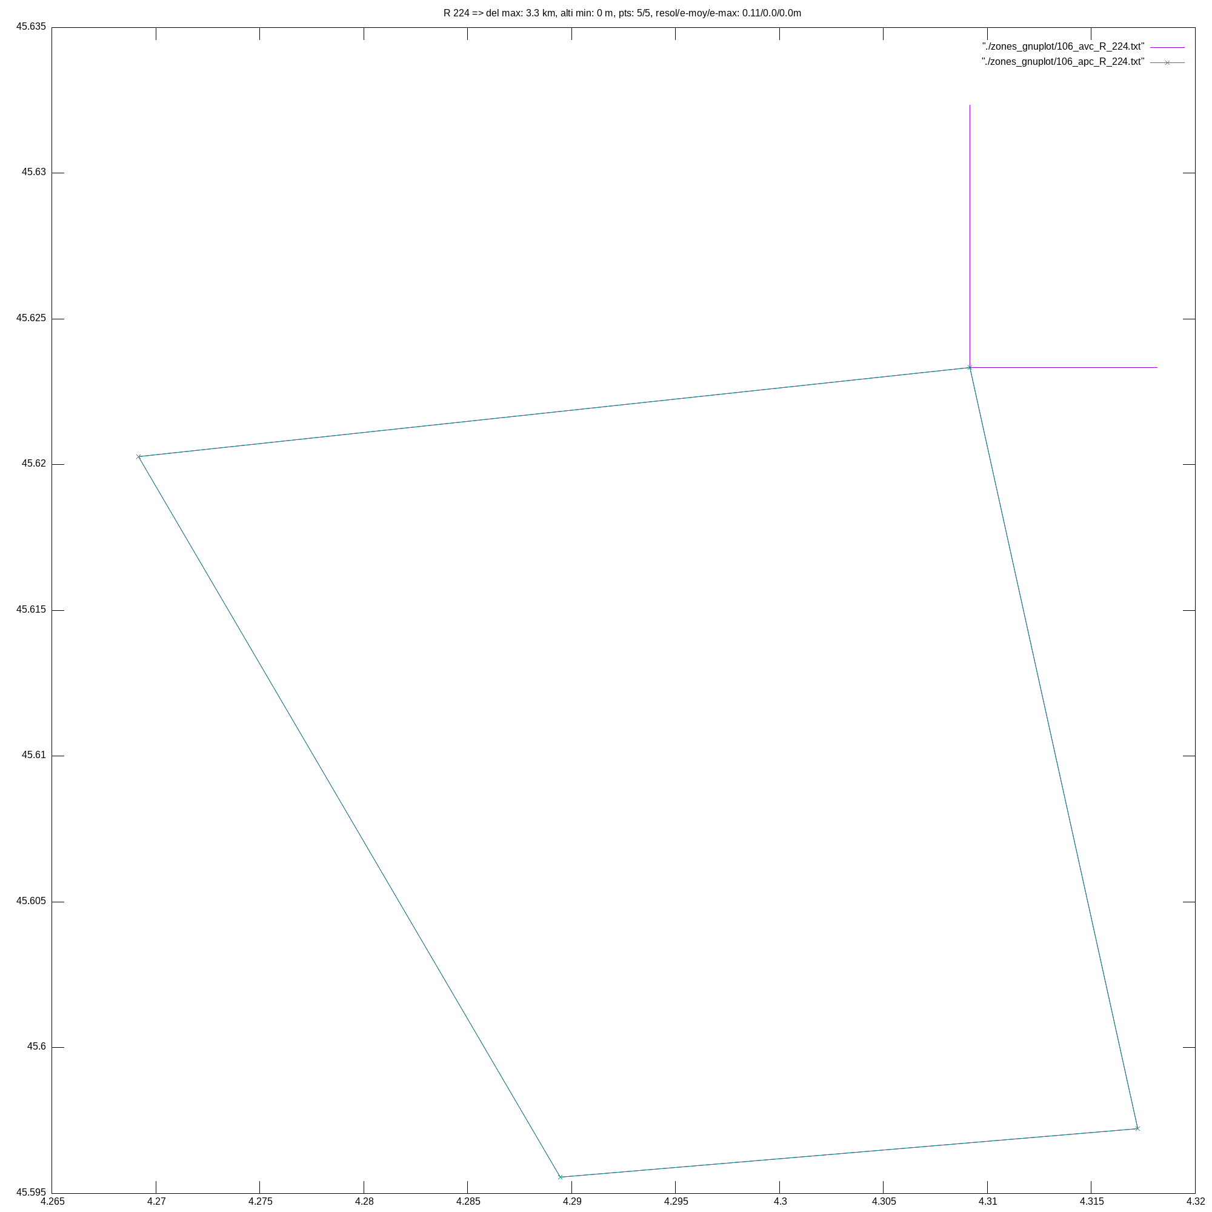
CompZoneAerienne/zones_gnuplot/106_png_R_224.png
