gitberthe/BertheVario/CompZoneAerienne/zones_gnuplot/109_png_RTBA_593__MILOPS___SeeNotam_.png

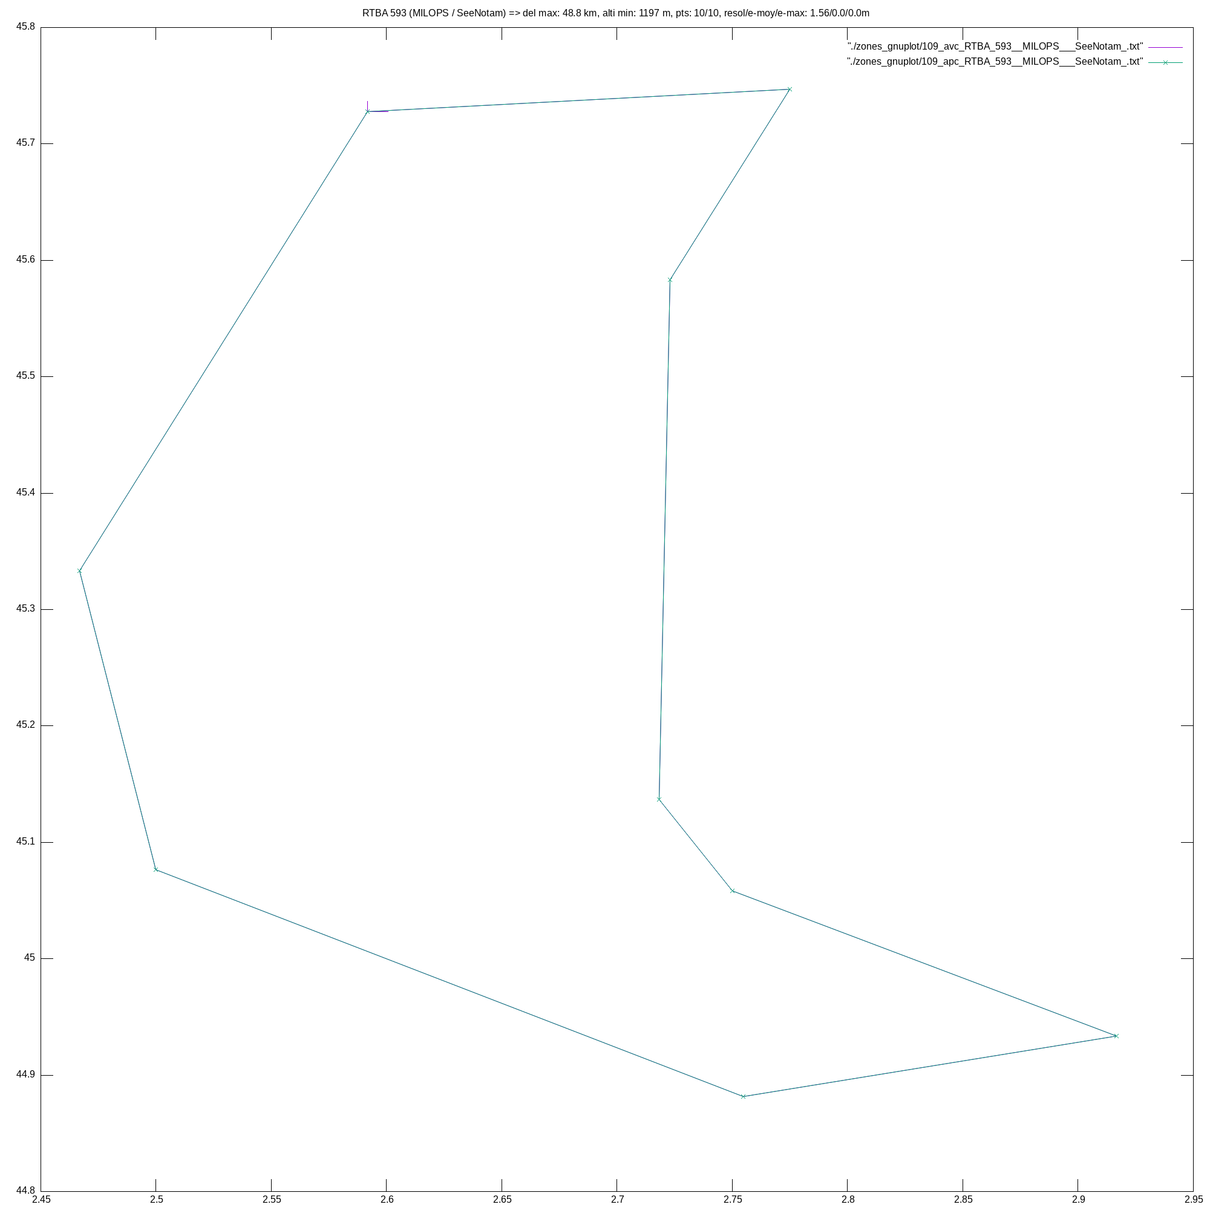
CompZoneAerienne/zones_gnuplot/109_png_RTBA_593__MILOPS___SeeNotam_.png
