gitberthe/BertheVario/CompZoneAerienne/zones_gnuplot/110_png_TMA_CLERMONT_4.2_App_122.225_.png

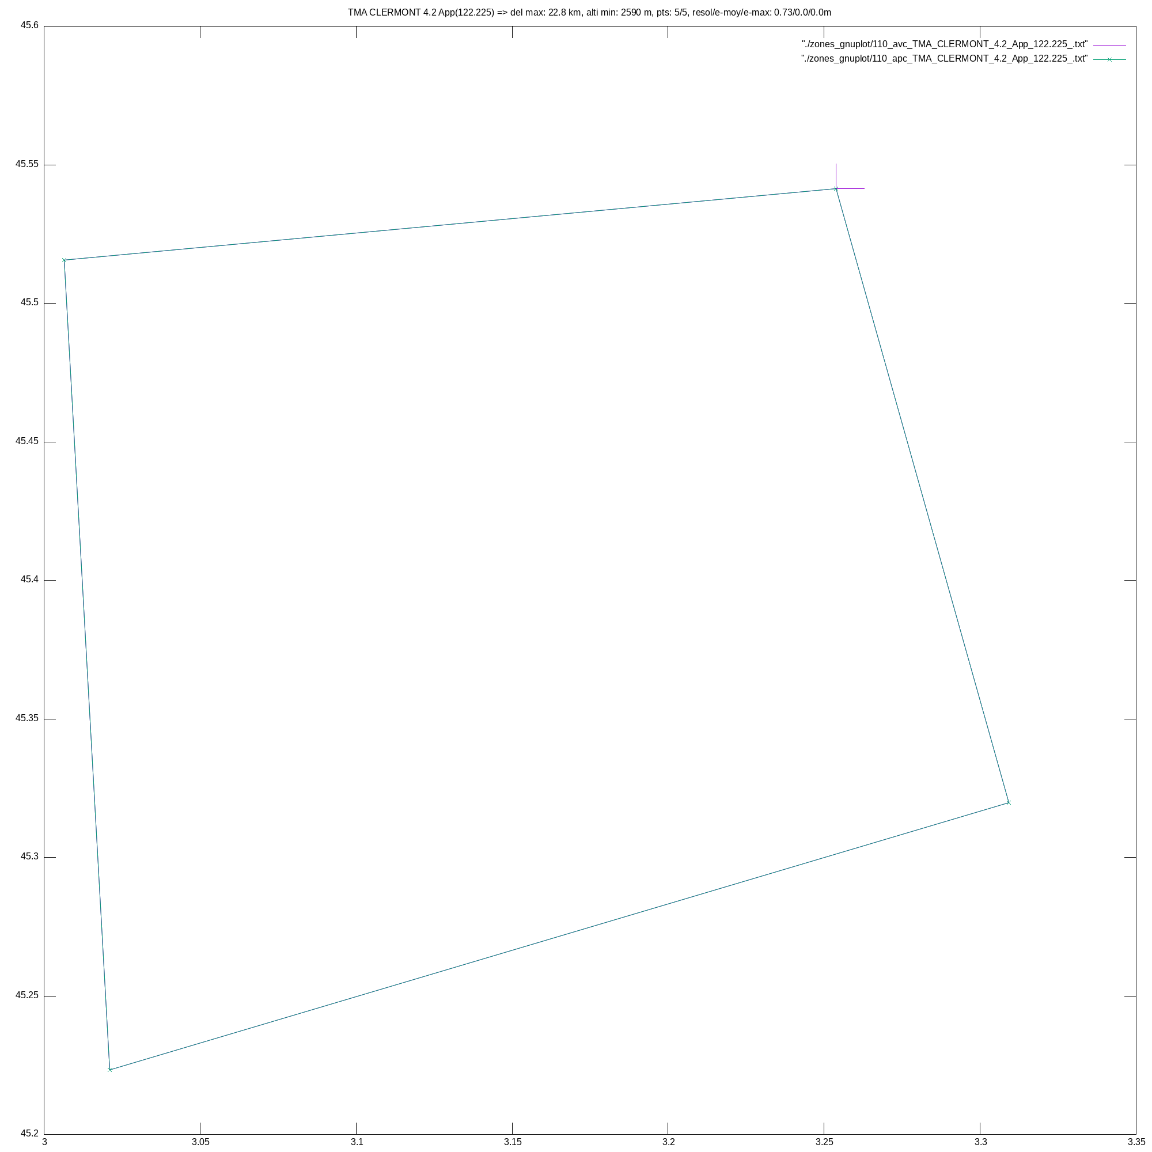
CompZoneAerienne/zones_gnuplot/110_png_TMA_CLERMONT_4.2_App_122.225_.png
