gitberthe/BertheVario/CompZoneAerienne/zones_gnuplot/111_png_R_233_B.png

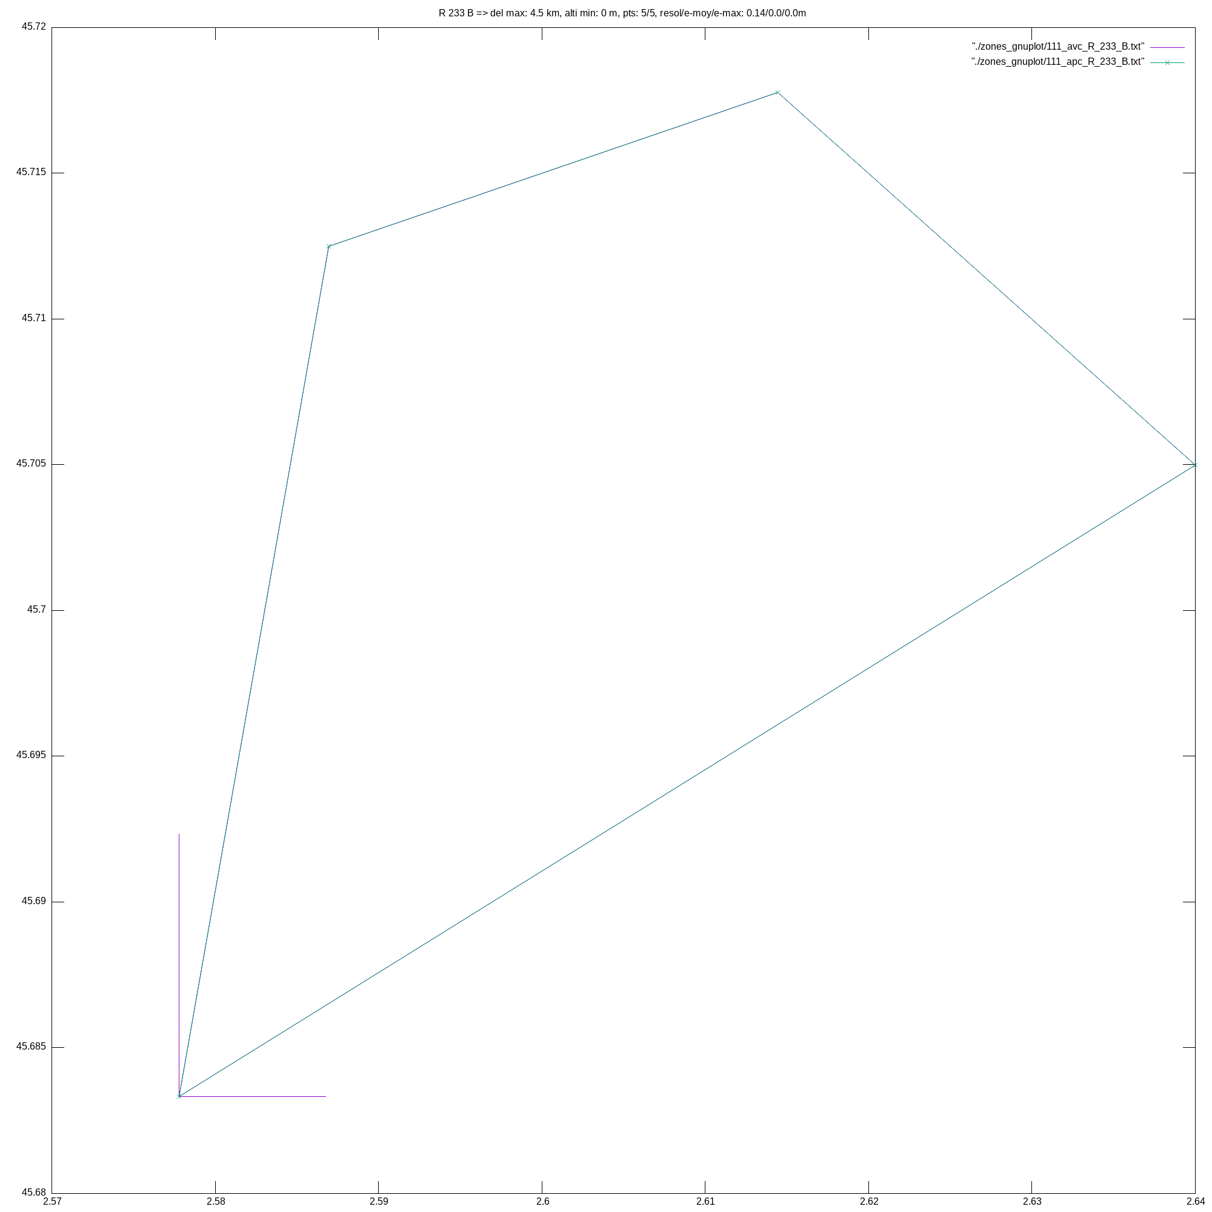
CompZoneAerienne/zones_gnuplot/111_png_R_233_B.png
