gitberthe/BertheVario/CompZoneAerienne/zones_gnuplot/112_png_R_233_A.png

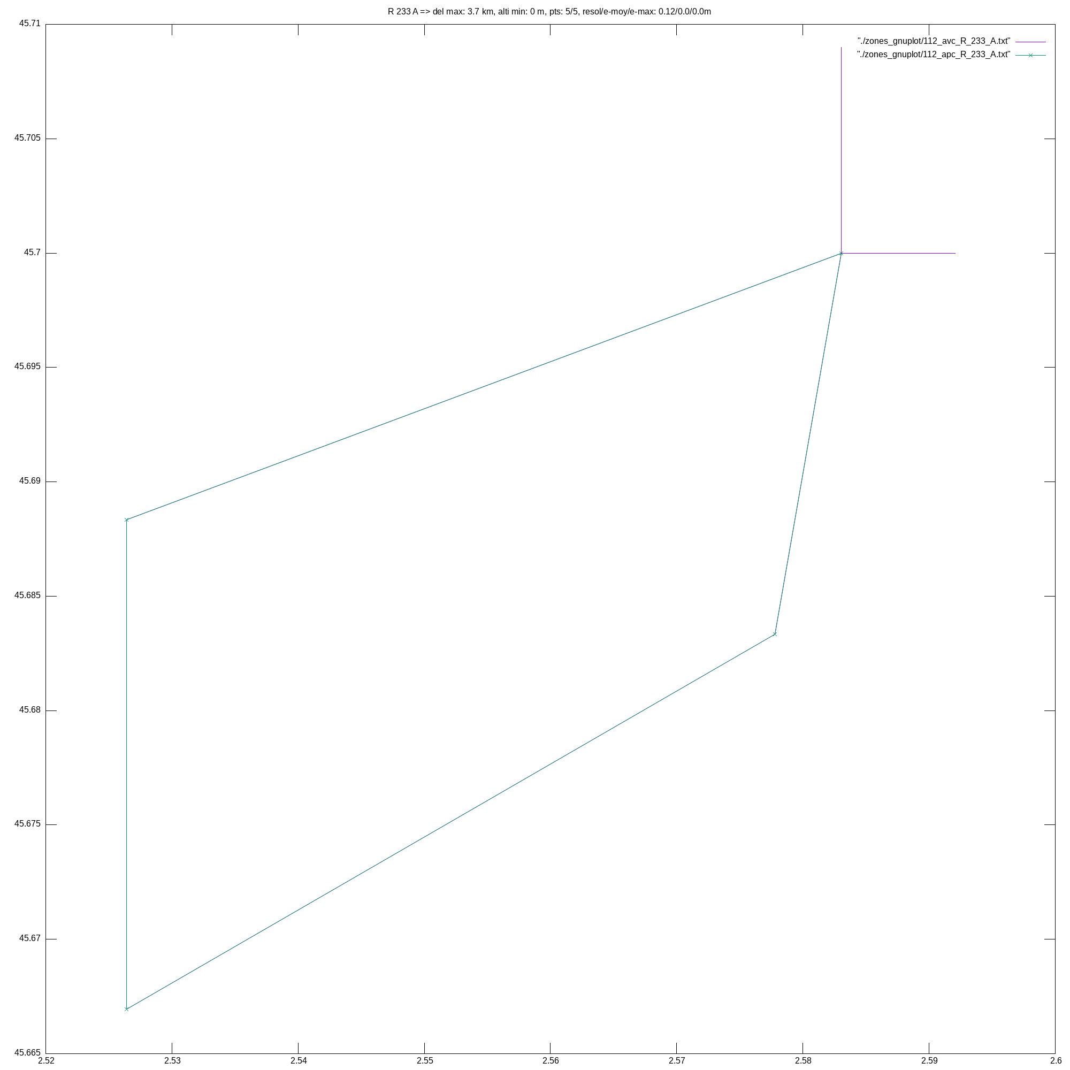
CompZoneAerienne/zones_gnuplot/112_png_R_233_A.png
