gitberthe/BertheVario/CompZoneAerienne/zones_gnuplot/115_png_R_68_D.png

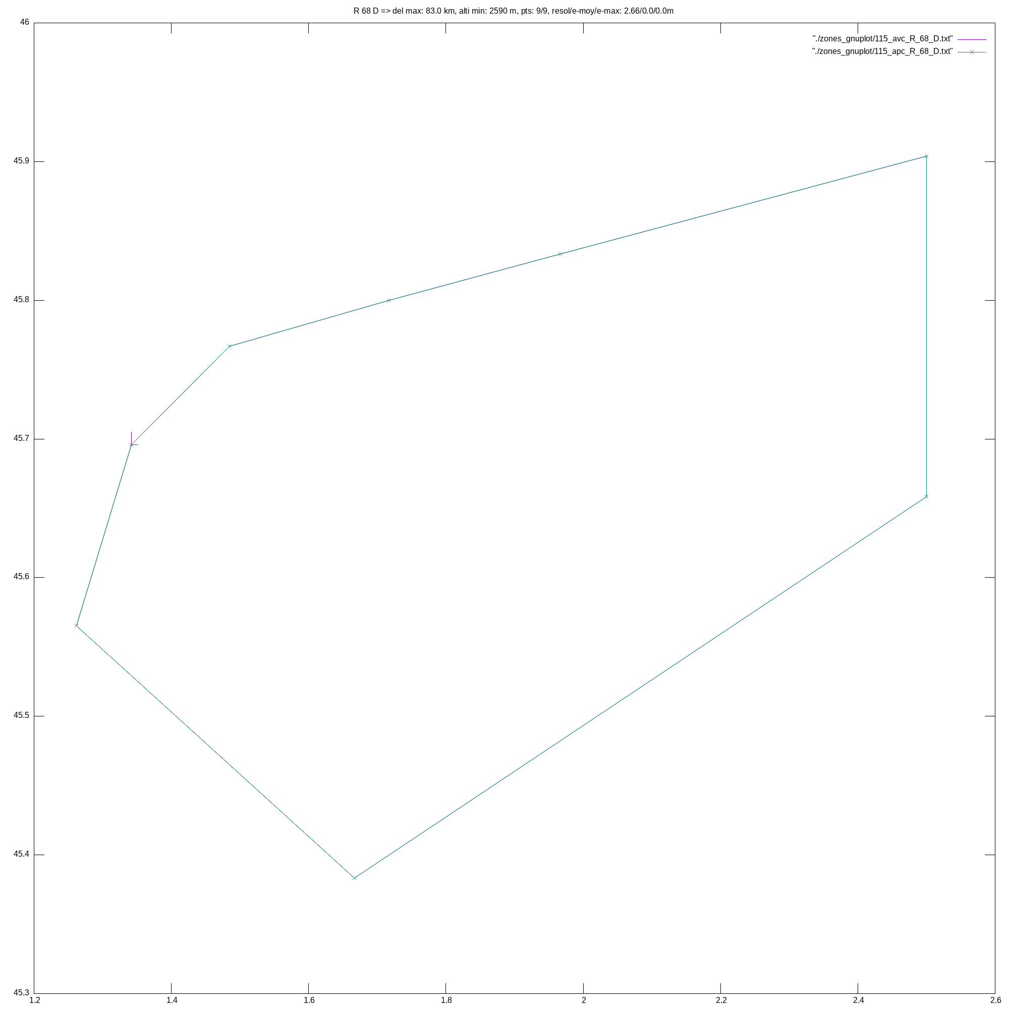
CompZoneAerienne/zones_gnuplot/115_png_R_68_D.png
