gitberthe/BertheVario/BertheVarioTac/documentation/00-premiers-pas/2.8inch_ESP32-2432S028R/1-Demo/Demo_LVGL(idf-4.3)/5_35_LVGL_Full_Test-S024/components/lv_examples/lv_examples/src/lv_demo_printer/README.md

# Printer demo

## Overview
An printer example created with LVGL. This demo is optmized for 800x480 resoltion and among many others it demonstrates custom theme creation, style transitions and animations. 

The demo uses some images with 32 bit color depth they require ~1.6 MB flash. With 16 bit color depth ~900KB is required for the images.

Printer demo with LVGL embedded GUI library

## Run the demo
- In `lv_ex_conf.h` set `LV_USE_DEMO_PRINTER 1`
- After `lv_init()` and initializing the drivers call `lv_demo_printer()`
