gitberthe/BertheVario/BertheVario/BertheVarioPlatformIO/src/BertheVario.cpp

////////////////////////////////////////////////////////////////////////////////
/// \file BerheVario.cpp
///
/// \brief Fichier principal du projet GNU-Vario de Berthe
///
/// \date creation     : 02/03/2024
/// \date modification : 08/07/2025 suppression xc_track et limite zone xy alti
/// \date modification : 09/07/2025 modification de beep vario sol
/// \date modification : 16/09/2025 LibGeneral
/// \date modification : 18/09/2025 .ini : board_build.partitions = no_ota.csv / huge_app.csv
/// \date modification : 18/09/2025
///

char NumVer[] = "20260302a" ;

// uncomment next line to use HSPI for EPD (and e.g VSPI for SD), e.g. with Waveshare ESP32 Driver Board
//#define USE_HSPI_FOR_EPD

#include "BertheVario.h"

// variable globale du programme
CGlobalVar g_GlobalVar ;

// note for partial update window and setPartialWindow() method:
// partial update window size and position is on byte boundary in physical x direction
// the size is increased in setPartialWindow() if x or w are not multiple of 8 for even rotation, y or h for odd rotation
// see also comment in GxEPD2_BW.h, GxEPD2_3C.h or GxEPD2_GFX.h for method setPartialWindow()

//VarioBle VBle ;

// site du pdd et certificat
const char*  server = "pdd.dprslt.fr" ; // /spaces/notams";  // Server URL

const char* test_root_ca= \
"-----BEGIN CERTIFICATE-----\n" \
"MIIFBjCCAu6gAwIBAgIRAMISMktwqbSRcdxA9+KFJjwwDQYJKoZIhvcNAQELBQAw\n" \
"TzELMAkGA1UEBhMCVVMxKTAnBgNVBAoTIEludGVybmV0IFNlY3VyaXR5IFJlc2Vh\n" \
"cmNoIEdyb3VwMRUwEwYDVQQDEwxJU1JHIFJvb3QgWDEwHhcNMjQwMzEzMDAwMDAw\n" \
"WhcNMjcwMzEyMjM1OTU5WjAzMQswCQYDVQQGEwJVUzEWMBQGA1UEChMNTGV0J3Mg\n" \
"RW5jcnlwdDEMMAoGA1UEAxMDUjEyMIIBIjANBgkqhkiG9w0BAQEFAAOCAQ8AMIIB\n" \
"CgKCAQEA2pgodK2+lP474B7i5Ut1qywSf+2nAzJ+Npfs6DGPpRONC5kuHs0BUT1M\n" \
"5ShuCVUxqqUiXXL0LQfCTUA83wEjuXg39RplMjTmhnGdBO+ECFu9AhqZ66YBAJpz\n" \
"kG2Pogeg0JfT2kVhgTU9FPnEwF9q3AuWGrCf4yrqvSrWmMebcas7dA8827JgvlpL\n" \
"Thjp2ypzXIlhZZ7+7Tymy05v5J75AEaz/xlNKmOzjmbGGIVwx1Blbzt05UiDDwhY\n" \
"XS0jnV6j/ujbAKHS9OMZTfLuevYnnuXNnC2i8n+cF63vEzc50bTILEHWhsDp7CH4\n" \
"WRt/uTp8n1wBnWIEwii9Cq08yhDsGwIDAQABo4H4MIH1MA4GA1UdDwEB/wQEAwIB\n" \
"hjAdBgNVHSUEFjAUBggrBgEFBQcDAgYIKwYBBQUHAwEwEgYDVR0TAQH/BAgwBgEB\n" \
"/wIBADAdBgNVHQ4EFgQUALUp8i2ObzHom0yteD763OkM0dIwHwYDVR0jBBgwFoAU\n" \
"ebRZ5nu25eQBc4AIiMgaWPbpm24wMgYIKwYBBQUHAQEEJjAkMCIGCCsGAQUFBzAC\n" \
"hhZodHRwOi8veDEuaS5sZW5jci5vcmcvMBMGA1UdIAQMMAowCAYGZ4EMAQIBMCcG\n" \
"A1UdHwQgMB4wHKAaoBiGFmh0dHA6Ly94MS5jLmxlbmNyLm9yZy8wDQYJKoZIhvcN\n" \
"AQELBQADggIBAI910AnPanZIZTKS3rVEyIV29BWEjAK/duuz8eL5boSoVpHhkkv3\n" \
"4eoAeEiPdZLj5EZ7G2ArIK+gzhTlRQ1q4FKGpPPaFBSpqV/xbUb5UlAXQOnkHn3m\n" \
"FVj+qYv87/WeY+Bm4sN3Ox8BhyaU7UAQ3LeZ7N1X01xxQe4wIAAE3JVLUCiHmZL+\n" \
"qoCUtgYIFPgcg350QMUIWgxPXNGEncT921ne7nluI02V8pLUmClqXOsCwULw+PVO\n" \
"ZCB7qOMxxMBoCUeL2Ll4oMpOSr5pJCpLN3tRA2s6P1KLs9TSrVhOk+7LX28NMUlI\n" \
"usQ/nxLJID0RhAeFtPjyOCOscQBA53+NRjSCak7P4A5jX7ppmkcJECL+S0i3kXVU\n" \
"y5Me5BbrU8973jZNv/ax6+ZK6TM8jWmimL6of6OrX7ZU6E2WqazzsFrLG3o2kySb\n" \
"zlhSgJ81Cl4tv3SbYiYXnJExKQvzf83DYotox3f0fwv7xln1A2ZLplCb0O+l/AK0\n" \
"YE0DS2FPxSAHi0iwMfW2nNHJrXcY3LLHD77gRgje4Eveubi2xxa+Nmk/hmhLdIET\n" \
"iVDFanoCrMVIpQ59XWHkzdFmoHXHBV7oibVjGSO7ULSQ7MJ1Nz51phuDJSgAIU7A\n" \
"0zrLnOrAj/dfrlEWRhCvAgbuwLZX1A2sjNjXoPOHbsPiy+lO1KF8/XY7\n" \
"-----END CERTIFICATE-----\n" ;

// wifi client secure
WiFiClientSecure client;

#ifdef TEST_SOUND
void TestSound(void *param)
{
while( true )
    {
    g_GlobalVar.beeper(1000,10) ;
    g_GlobalVar.beeper( SOUND_DELAY_ONLY , 10 ) ;
    }

while( true )
    vTaskDelete(NULL) ;
}
#endif

///////////////////////////////////////////////////////////////////////////////
/// \brief Connection a pdd.dprslt.fr pout recuperation page Notam
/// recuperation par :
/// openssl s_client -showcerts -servername pdd.dprslt.fr  -connect pdd.dprslt.fr:443 </dev/null
void EssDprslt()
{
return ; // on ne faite plus rien

// certificat
client.setCACert(test_root_ca);

int count = 0 ;
while ( ! client.connected() && count++ < 5 )
    {
    if (!client.connect(server, 443))
        {
        Serial.print( "not connected\n") ;
        g_GlobalVar.BeepError() ;
        }
    else
        {
        Serial.print( "connected to pdd.dprslt.fr !!!\n") ;
        break ;
        }
    }

// Make a HTTP request:
client.println("GET https://pdd.dprslt.fr/spaces/notams HTTP/1.0");
client.print("Host: ");
client.println(server);
client.println("Connection: close");
client.println();

  while (client.connected()) {
      String line = client.readStringUntil('\n');
      if (line == "\r") {
        Serial.println("headers received");
        break;
      }
    }


//If there are incoming bytes available
    //from the server, read them and put into the 'response' char array
    while (client.connected()) {

      if (client.available()) {
        char c = client.read();
        Serial.print( c ) ;
        }
    }

client.stop() ;

/*client.println("Host: pdd.dprslt.fr");
client.println("Connection: close");
client.println();

while (client.connected())
    {
    String line = client.readStringUntil('\n');
    if (line == "\r")
        {
        Serial.println("headers received");
        break;
        }
    }

// if there are incoming bytes available
// from the server, read them and print them:
while (client.available())
    {
    char c = client.read();
    Serial.write(c);
    }

client.stop(); */
}

///////////////////////////////////////////////////////////////////////////////
/// \brief fonction setup de demmarrage.
void setup()
{
// init port serie de console
Serial.begin(115200);
Serial.println("Setup") ;
#ifdef _LG_DEBUG_
 Serial.println();
 Serial.println("fonction setup");
 delay(100);
#endif

//#if defined(ESP32) && defined(USE_HSPI_FOR_EPD)
  //hspi.begin(13, 12, 14, 15); // remap hspi for EPD (swap pins)
  //display.epd2.selectSPI(hspi, SPISettings(4000000, MSBFIRST, SPI_MODE0));
//#endif

// beeper init
g_GlobalVar.LanceTacheSound() ;
delay( 200 ) ;
CGlobalVar::BeepOk() ;

// init alim
g_GlobalVar.InitAlim() ;

// init ecran
g_GlobalVar.InitScreen() ;

// affichage boutons
g_GlobalVar.AfficheBoutons() ;

// init boutons
g_GlobalVar.InitButton() ;

// init sdcard
g_GlobalVar.InitSDCard() ;

// test pdd fichier hgt
g_GlobalVar.TestPddGroundZ() ;

// boutons
bool BoutonGaucheAppuye = false ;  // calibration
bool BoutonCentreAppuye = false ;  // mode wifi
bool BoutonDroitAppuye = false ;   // mode rando-vol
unsigned long time = millis() ;
while ( (millis() - time) < 2000 )
    {
    if ( g_GlobalVar.BoutonDroit() )
        {
        BoutonDroitAppuye = true ;
        break ;
        }
    if ( g_GlobalVar.BoutonGauche() )
        {
        BoutonGaucheAppuye = true ;
        break ;
        }
    if ( g_GlobalVar.BoutonCentre() )
        {
        BoutonCentreAppuye = true ;
        break ;
        }
    }
//g_GlobalVar.BootEffectue() ;

// affichage voltage
g_GlobalVar.AfficheVoltage() ;

// lecture fichier de configuration
g_GlobalVar.m_Config.LectureFichier() ;

// Init BUS I2C
g_GlobalVar.InitI2C() ;

////////////////////
// si mode http wifi
if ( BoutonCentreAppuye )
    {
    // mode ftp pour loop
    g_GlobalVar.m_ModeHttp = true ;

    // lecture fichier zones aeriennes
    g_GlobalVar.m_ZonesAerAll.LectureFichiers() ;
    // creation fichier de validation zones
    g_GlobalVar.m_ZonesAerAll.Valid() ;
    // liberation memoire
    g_GlobalVar.m_ZonesAerAll.DeleteAll() ;

    // affichage
    g_GlobalVar.AfficheConnectWifi() ;

    // connection wifi
    WiFi.begin( g_GlobalVar.m_Config.m_Ssid, g_GlobalVar.m_Config.m_Passwd );
    while (WiFi.status() != WL_CONNECTED)
        {
        delay(500);
        Serial.print(".");
        }

    g_GlobalVar.m_Config.FreeVect() ;

    #ifdef HTTP_DEBUG
    Serial.println("");
    Serial.print("Connected to ");
    Serial.println(WIFI_SSID);
    Serial.print("IP address: ");
    Serial.println(WiFi.localIP());
    #endif

    // adresse wifi
    char buf[50];
    sprintf(buf, "%d.%d.%d.%d", WiFi.localIP()[0], WiFi.localIP()[1], WiFi.localIP()[2], WiFi.localIP()[3] );
    g_GlobalVar.AfficheWifi( buf ) ;

    EssDprslt() ;

    // creation init file manager
    pfilemgr = new ESPFMfGK( 8080 ) ;

    addFileSystems();
    setupFilemanager();

    return ;
    }
else
    g_GlobalVar.m_ModeHttp = false ;


// capteur de pression temperature
g_GlobalVar.m_MS5611Press.InitMs5611() ;

// capteur accelerometrique/cap magnetique
g_GlobalVar.m_Mpu9250.Init() ;

// init port serie GPS
g_GlobalVar.InitGps() ;

////////////////////////////////////
// si calibration capteur magnetique
if ( BoutonGaucheAppuye )
    {
    g_GlobalVar.AfficheCalibreMag() ;
    g_GlobalVar.m_Mpu9250.Calibration() ;
    CGlobalVar::Reboot() ;
    }

// lancement tache de calcul de la Vz et acquisition cap magnetique
g_GlobalVar.m_MS5611Press.LancerTacheCalculVzCapMag() ;

/////////////////////
// si mode vol-rando
#ifdef DEBUG_RANDO_VOl
 g_GlobalVar.m_ModeRandoVol = true ;
 return ;
#endif
if ( BoutonDroitAppuye )
    {
    // lecture fichier terrains
    g_GlobalVar.m_TerrainArr.LireFichierTerrains(TERRAIN_FCH) ;
    g_GlobalVar.m_ModeRandoVol = true ;
    return ;
    }
else
    g_GlobalVar.m_ModeRandoVol = false ;

// lecture fichier terrains
g_GlobalVar.m_TerrainArr.LireFichierTerrains(TERRAIN_FCH) ;

// lecture fichier zones aeriennes
g_GlobalVar.m_ZonesAerAll.LectureFichiers() ;

// lancement tache gps
g_GlobalVar.LanceTacheGps(true) ;

// lancement tache beep
g_GlobalVar.LanceTacheVarioBeep() ;

#ifdef _LG_DEBUG_
  Serial.println("setup done");
#endif

#ifdef TEST_SOUND
 xTaskCreatePinnedToCore(TestSound, "Testsound", SERIAL_GPS_STACK_SIZE, NULL, SERIAL_GPS_PRIORITY,NULL, 0 );
 xTaskCreatePinnedToCore(TestSound, "Testsound", SERIAL_GPS_STACK_SIZE, NULL, SERIAL_GPS_PRIORITY,NULL, 0 );
 xTaskCreatePinnedToCore(TestSound, "Testsound", SERIAL_GPS_STACK_SIZE, NULL, SERIAL_GPS_PRIORITY,NULL, 1 );
 xTaskCreatePinnedToCore(TestSound, "Testsound", SERIAL_GPS_STACK_SIZE, NULL, SERIAL_GPS_PRIORITY,NULL, 1 );
#endif

#ifdef TIME_GROUND_Z
 //while ( g_GlobalVar.m_Hgt2Agl.GetCacheAlti().GetSize() < MAX_ELEMENT_ALTI - 20 )
 //    g_GlobalVar.m_Hgt2Agl.GetCacheAlti().Add( new CCacheAlti ) ;
#endif

#ifdef GROUND_Z_DEBUG
for ( int ipa = 0 ; ipa < 3 ; ipa++ )
    {
    unsigned long time_gz = millis() ;
    Serial.print( "\ncache size : " ) ; Serial.println( g_GlobalVar.m_Hgt2Agl.GetCacheSize() ) ;

    // 512
    float SsdLat = 45.631652 ;
    float SsdLon =  3.116147 ;
    // pdd
    float PddLat = 45.772396 ;
    float PddLon = 2.964061  ;
    // vichy
    float ViLat = 46.1239268 ;
    float ViLon = 3.4203712  ;
    // aiguille du midi
    float MiLat = 42.843134 ;
    float MiLon = -0.438166 ;
    // mont blanc
    float MbLat = 45.832526 ;
    float MbLon = 6.864775 ;
    // pt
    float PtLat = 45.885989 ;
    float PtLon = 2.727933 ;
    // corent
    float CoLat = 45.660355 ;
    float CoLon = 3.179634 ;
    // zp sancy
    float ZpLat = 45.491927 ;
    float ZpLon = 2.740171 ;
    // dune
    float DuLat = 44.529188 ;
    float DuLon = -1.257285;

    int SsdAlti = g_GlobalVar.m_Hgt2Agl.GetGroundZ( SsdLon , SsdLat ) ;
    int PddAlti = g_GlobalVar.m_Hgt2Agl.GetGroundZ( PddLon , PddLat ) ;
    int ViAlti = g_GlobalVar.m_Hgt2Agl.GetGroundZ( ViLon , ViLat ) ;
    int MiAlti = g_GlobalVar.m_Hgt2Agl.GetGroundZ( MiLon , MiLat ) ;
    int MbAlti = g_GlobalVar.m_Hgt2Agl.GetGroundZ( MbLon , MbLat ) ;
    int PtAlti = g_GlobalVar.m_Hgt2Agl.GetGroundZ( PtLon , PtLat ) ;
    int CoAlti = g_GlobalVar.m_Hgt2Agl.GetGroundZ( CoLon , CoLat ) ;
    int ZpAlti = g_GlobalVar.m_Hgt2Agl.GetGroundZ( ZpLon , ZpLat ) ;
    int DuAlti = g_GlobalVar.m_Hgt2Agl.GetGroundZ( DuLon , DuLat ) ;

    Serial.print( "\n512(790) alti:" ) ; Serial.println( SsdAlti ) ;
    Serial.print( "pdd(1465) alti:" ) ; Serial.println( PddAlti ) ;
    Serial.print( "vichy() alti:" ) ;   Serial.println( ViAlti ) ;
    Serial.print( "midi(2847) alti:" ) ;Serial.println( MiAlti ) ;
    Serial.print( "mb(4768) alti:" ) ;  Serial.println( MbAlti ) ;
    Serial.print( "pt(686) alti:" ) ;   Serial.println( PtAlti ) ;
    Serial.print( "co(616) alti:" ) ;   Serial.println( CoAlti ) ;
    Serial.print( "Zp(1141) alti:" ) ;  Serial.println( ZpAlti ) ;
    Serial.print( "Du(2) alti:" ) ;  Serial.println( DuAlti ) ;
    unsigned long ecart = millis() - time_gz ;
    Serial.print( "time calc hgt ms : " ) ;
    Serial.println( ecart ) ;
    Serial.println( "************" ) ;
    }
#endif
}

bool once = true ;

///////////////////////////////////////////////////////////////////////////////
/// \brief fonction loop toujours appelée.
void loop()
{
if ( g_GlobalVar.GetWant2Reboot() )
    CGlobalVar::Reboot() ;

/*// si boucle a ne plus faire
if ( g_GlobalVar.m_StopLoop )
    {
    delay( DELAY_ATTENTE_IDLE ) ;
    return ;
    }*/

////////////////////
// si mode http wifi
if ( g_GlobalVar.m_ModeHttp )
    {
    g_GlobalVar.m_DureeVolMin = ATTENTE_MESSAGE_GPS ;
    pfilemgr->handleClient();
    return ;
    }

// si raz ecran
if ( g_GlobalVar.BoutonCentreLong() )
    {
    g_GlobalVar.PurgeBoutons( 3000 ) ;
    g_GlobalVar.ScreenRaz() ;
    }

////////////////////
// si mode rando-vol
if ( g_GlobalVar.m_ModeRandoVol )
    {
    if ( once )
        {
        unsigned int time = millis() ;
        while ( (millis()-time) < 2000 )
            {
            // mode verification checksum
            if ( g_GlobalVar.BoutonDroit() )
                {
                g_GlobalVar.m_ModeChecksum = true ;
                g_GlobalVar.m_ModeRandoVol = false ;
                g_GlobalVar.DoChar( 30 , 30 , "Mode chks" ) ;
                once = false ;
                return ;
                }
            }
        once = false ;
        g_GlobalVar.InitRandoVol() ;
        }
    g_GlobalVar.AfficheRandoVol() ;
    delay( 200 ) ;
    return ;
    }

////////////////////
// si mode checksum
if ( g_GlobalVar.m_ModeChecksum )
    {
    // si cheksum ok
    if ( g_GlobalVar.VerifyAllChecksumGood() )
        {
        Serial.println( "good all cheksum" ) ;
        g_GlobalVar.DoChar( 0 , 120 , "chks all ok" ) ;
        }
    else
        g_GlobalVar.DoChar( 0 , 120 , "wait bad chk" ) ;
    // atente 1 jour
    if ( ! g_GlobalVar.GetWant2Reboot() )
        delay( 1000*60*60*24 ) ;
    return ;
    }

// bip demarrage premiere boucle
if ( once )
    {
    once = false ;
    CGlobalVar::BeepOk() ;
    delay( 200 ) ;
    CGlobalVar::BeepOk() ;

    //g_GlobalVar.VerifyChecksum( "" ) ;

    // simu vol
    #ifdef SIMU_VOL
     g_SimuVol.LancerTacheSimuVol() ;
    #endif
    }

// fonction d'affichage
//unsigned long TimeAvAff = millis() ;
g_GlobalVar.AfficheAll();

// pour la mise au point
Serial.println( "loop" ) ;
/*Serial.print( "TacheAttentVol:" ) ;
Serial.println( g_GlobalVar.IsRunning( ATTENTE_VOL_NUM_TASK ) ) ;
Serial.print( "TacheIgc:" ) ;
Serial.println( g_GlobalVar.IsRunning( IGC_NUM_TASK ) ) ;
Serial.print( "TachePerfMon:" ) ;
Serial.println( g_GlobalVar.IsRunning( PERF_MON_NUM_TASK ) ) ;
Serial.print( "TacheRelanceAttenteVol:" ) ;
Serial.println( g_GlobalVar.IsRunning( RELANCE_IGC_NUM_TASK ) ) ;*/


// attente 0.5s, l'affichage n'est pas prioritaire
//while ( (millis() - TimeAvAff) < 500 )
//    delay( DELAY_ATTENTE_IDLE ) ;

/*
// pression hPascal, altitude meters ,vario cm/s, temperature C, battery voltage, *checksum
char Sentence[500] ;
sprintf( Sentence , "LK8EX1,999999,%f,99,99,999",g_GlobalVar.m_TerrainPosCur.m_AltiBaroRec ) ;
int Len = strlen( Sentence ) ;
unsigned int checksum , ai, bi;                                               // Calculating checksum for data string
for (checksum = 0, ai = 0; ai < Len ; ai++)
    {
    bi = (unsigned char)Sentence[ai];
    checksum ^= bi;
    }

char Sentence2[500] ; // = "$LK8EX1,98974,197,0,99,999*32\r\n" ;
sprintf( Sentence2 , "$%s*%X\r\n" , Sentence , checksum ) ;
int Len2 = strlen( Sentence2 ) ;
for ( int ic = 0 ; ic < Len2 ; ic++ )
    VBle.write( Sentence2[ic] ) ;
VBle.flush() ;
*/
}
