gitberthe/BertheVario/BertheVario/BertheVarioPlatformIO/src/FileMgr/FileMgr.h

////////////////////////////////////////////////////////////////////////////////
/// \file FileMgr.h
///
/// \brief Fonction du file manager
///
/// \date creation     : 04/04/2024
/// \date modification : 21/07/2024
///

#ifndef _FILEMGR_
#define _FILEMGR_

void addFileSystems() ;
void setupFilemanager() ;

extern ESPFMfGK * pfilemgr ;

#endif
